XGudron/UA3REO-DDC-Transceiver/Schematic/Wolf-DK102/Photos/20241206171314.jpg

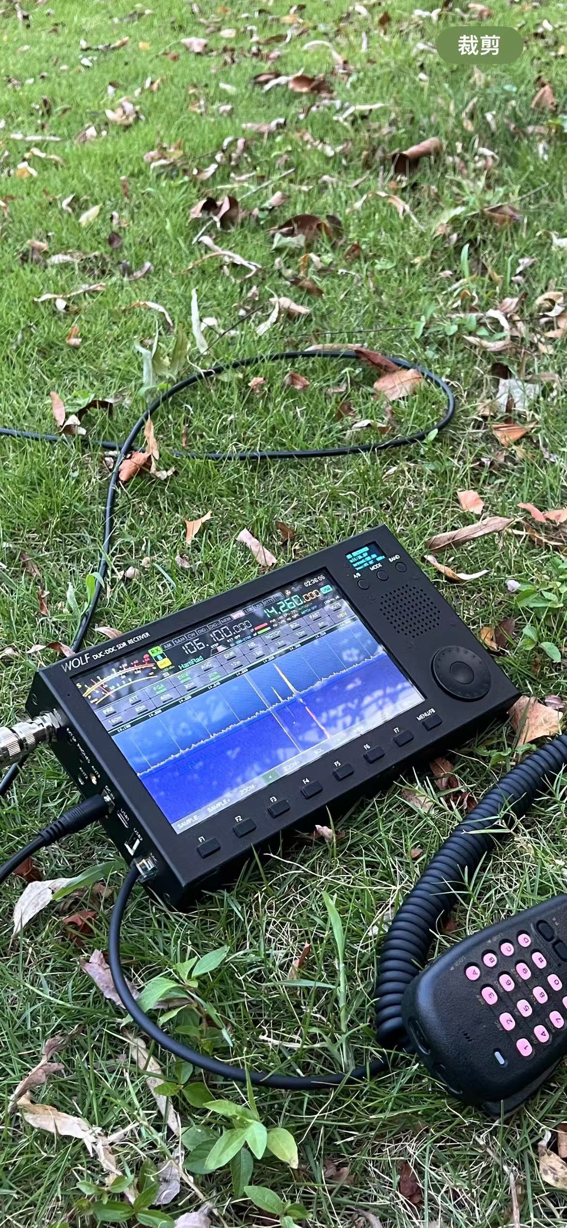
Schematic/Wolf-DK102/Photos/20241206171314.jpg
