XGudron/UA3REO-DDC-Transceiver/Schematic/Wolf/Addons/LPF_switch.jpg

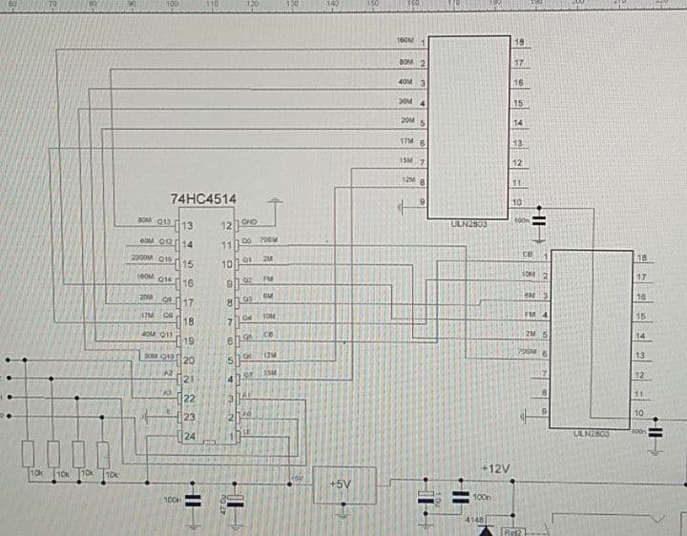
Schematic/Wolf/Addons/LPF_switch.jpg
