XGudron/UA3REO-DDC-Transceiver/Schematic/Wolf/Addons/PCB MIC MH-48/pcb1.jpg

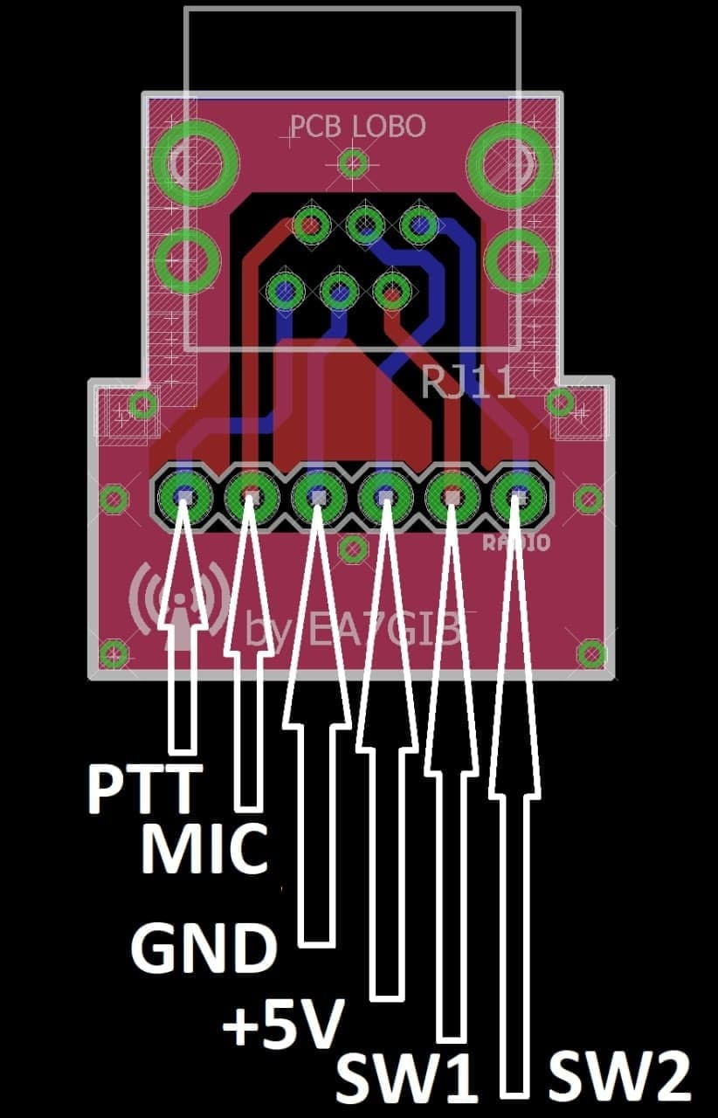
Schematic/Wolf/Addons/PCB MIC MH-48/pcb1.jpg
