XGudron/UA3REO-DDC-Transceiver/Schematic/Wolf/Addons/PCB MIC MH-48/pcb3.jpg

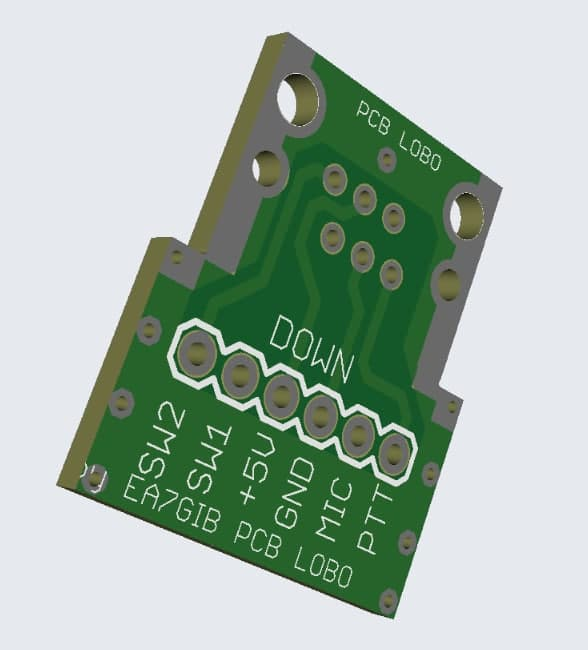
Schematic/Wolf/Addons/PCB MIC MH-48/pcb3.jpg
