XGudron/UA3REO-DDC-Transceiver/Schematic/Wolf/CASE/7/Panel/photo_2023-04-01_12-15-42.jpg

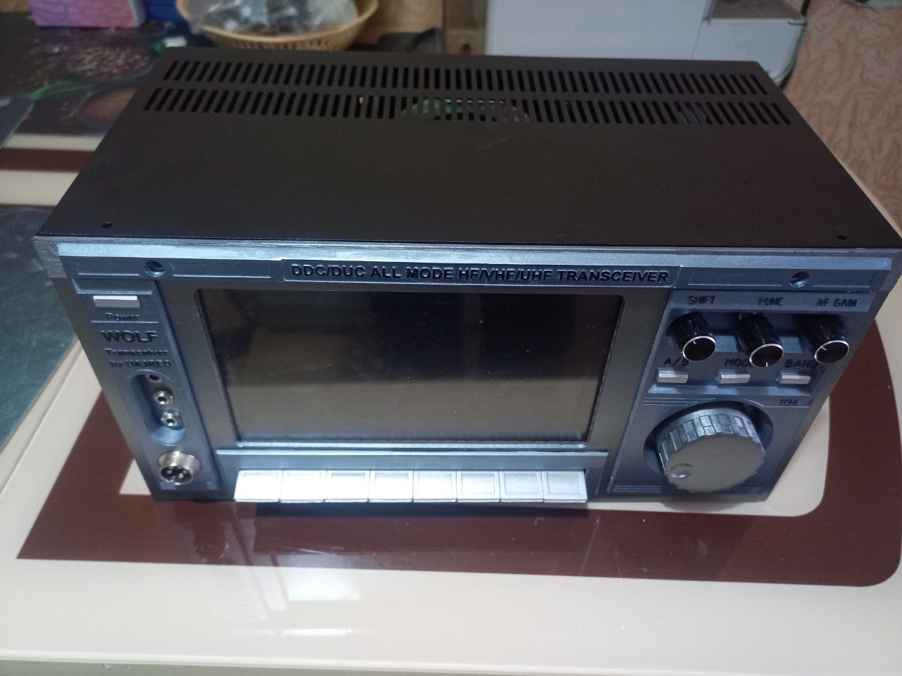
Schematic/Wolf/CASE/7/Panel/photo_2023-04-01_12-15-42.jpg
