XGudron/UA3REO-DDC-Transceiver/Schematic/Wolf/CASE/7/Panel/photo_2023-04-01_13-19-56.jpg

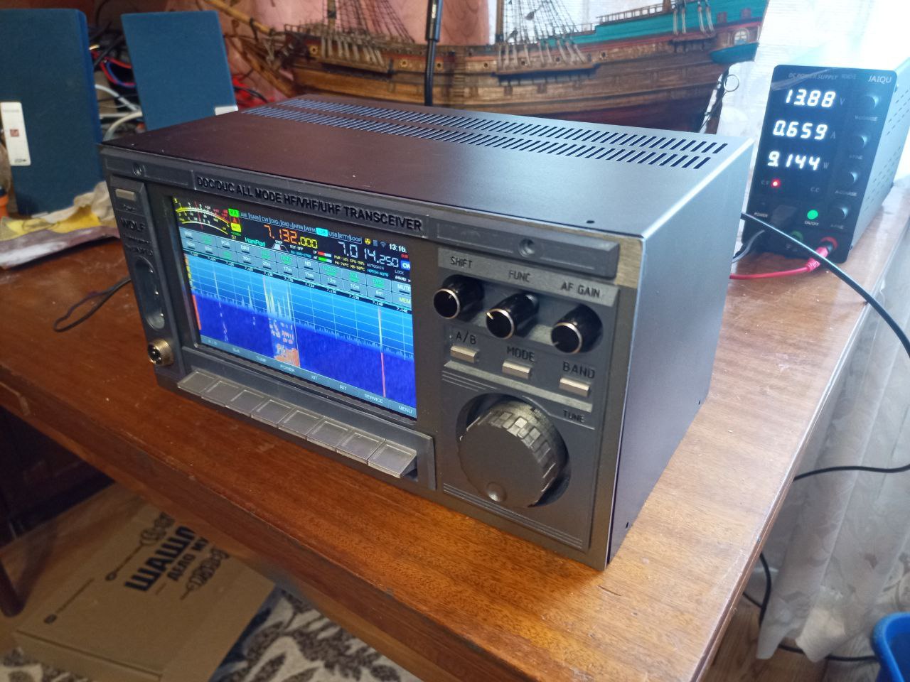
Schematic/Wolf/CASE/7/Panel/photo_2023-04-01_13-19-56.jpg
