XGudron/UA3REO-DDC-Transceiver/Schematic/Wolf/BOM/BOM-MOTHERBOARD-rev33.xls

Comment | Description | Designator | Footprint | LibRef | Quantity | LCSC Part #
JX2 | JX2 | 13.8V + | JX2 | JX2 | 1
51022-0300_1 | 51022-0300 | A_OUT, MIC_IN2 | 51022-0200 - duplicate | 51022-0300_1 | 2
CR1220 + | BR1632A/FA | B1 | KLS5-CR1220-01 | BR1632A/FA | 1
 | 2 Pin | BOOT | 51022-0200 | 51022-0200 | 1
4.7uF 16V | CAPAE_6.6x6.6h5.4 | C1 | SMC | CAPAE_6.6x6.6h5.4 | 1
22uF 10V | CAPAE_4.3x4.3h5.4 | C2, C125, C126 | CAPAE_4.3x4.3h5.4 | CAPAE_4.3x4.3h5.4 | 3
100n | CAP_0805 | C3, C4, C5, C6, C9, C16, C19, C21, C23, C31, C44, C45, C46, C47, C48, C49, C51, C53, C56, C57, C58, C59, C61, C62, C65, C67, C69, C70, C71, C72, C73, C74, C76, C78, C79, C81, C82, C83, C84, C86, C87, C88, C89, C91, C93, C94, C95, C96, C97, C98, C99, C100, C107, C109, C110, C112, C113, C114, C115, C117, C118, C120, C123, C124, C135 | CAP_0805 | CAP_0805 | 65
1uF | CAP_0805 | C7, C11, C12, C13, C14, C15, C35, C92, C119, C121, C122, C1003, C1004 | CAP_0805 | CAP_0805 | 13
10uF 10V | CAPAE_4.3x4.3h5.4 | C8, C20, C22, C24, C32, C54, C60, C75, C77, C80, C85, C1002 | CAPAE_4.3x4.3h5.4 | CAPAE_4.3x4.3h5.4 | 12
470p | CAP_0805 | C10, C90, C104, C116 | CAP_0805 | CAP_0805 | 4
10uF 10V | CAP_0805 | C17 | CAP_0805 | CAP_0805 | 1
1uF 10V | CAPAE_4.3x4.3h5.4 | C25, C26, C29 | CAPAE_4.3x4.3h5.4 | CAPAE_4.3x4.3h5.4 | 3
220p | CAP_0805 | C27, C28, C30 | CAP_0805 | CAP_0805 | 3
220uF 10V | CAPAE_4.3x4.3h5.4 | C33, C34 | EEEFC_size� | CAPAE_4.3x4.3h5.4 | 2
100pF | CAP_0805 | C36 | CAP_0805 | CAP_0805 | 1
10n | CAP_0805 | C37, C63, C137 | CAP_0805 | CAP_0805 | 3
6pF | CAP_0805 | C38, C39 | CAP_0805 | CAP_0805 | 2
10uF | CAP_0805 | C40, C41, C50, C52, C64, C66, C68 | CAP_0805 | CAP_0805 | 7
22p | CAP_0805 | C42, C43 | CAP_0805 | CAP_0805 | 2
7.5p | CAP_0805 | C55 | CAP_0805 | CAP_0805 | 1
10uF 20V | CAPAE_4.3x4.3h5.4 | C101, C108 | CAPAE_4.3x4.3h5.4 | CAPAE_4.3x4.3h5.4 | 2
1uF | CAP_1206 | C102, C103 | CAP_1206 | CAP_1206 | 2
680p | CAP_1206 | C105, C106 | CAP_1206 | CAP_1206 | 2
10p | CAP_0805 | C127 | CAP_0805 | CAP_0805 | 1
8.2n | CAP_0805 | C136 | CAP_0805 | CAP_0805 | 1
1n | CAP_0805 | C1001 | CAP_0805 | CAP_0805 | 1
SMAJ5.0A-TR | Diode | D1, D3, D29, D30, D31, D34, D35, D36, D37, D38, D39, D40 | SMBJ36CATR | SMLVT3V3 | 12 | [NoParam], test
SS34 | Schottky Diode | D1001 | SMB | D Schottky | 1
Diode | Default Diode | D1002 | C1206 | Diode | 1
SJ1-3525NG | SJ1-3525NG | J1, J2, J3, J5 | SJ1-3525NG | SJ1-3523N | 4
RF-UNIT | 2*5 Pin | J4 | 90131-0126 | 90131-0126 | 1
FPC-45P-0.5mm | Connector | J6 | FH12S45S05SH60 | FH12S-45S-0.5SH_55_ | 1
FAN | 51022-0200 | J7 | 51022-0200 | 51022-0200 | 1
USB | 2-1734035-3 | J8 | 2-1734035-3 | 2-1734035-3 | 1
DAC_OUT | SMA | J9 | 31-5431 | 31-5431 | 1
ADC | SMA | J10 | 31-5431 | 31-5431 | 1
 | 2*5 Pin | JTAG_FPGA, JTAG_STM32 | IDC10 | IDC10 | 2
3.3uH | IND_1812 | L1, L9 | IND_1812 | IND_1812 | 2
BLM21 | BLM21 | L3, L8 | CAP_0805 | IND_FERRITE_BEAD | 2
22uH | IND_1206 | L7 | IND_7x7 | IND_1206 | 1
10uH | Inductor | L37, L1001 | IND_7x7 | IND_FERRITE_CORE | 2
10uH | IND_1812 | L1002 | IND_1812 | IND_1812 | 1
PTT_IN | 51022-0200 | PTT_IN | 51022-0200 | 51022-0200 | 1
2SC5103TLP | Transistor BJT NPN | Q1 | 2SC5103TLQ | 2SC5103TLP | 1
7.5k | RES_0805 | R1 | RES_0805 | RES_0805 | 1
39k | RES_0805 | R2 | RES_0805 | RES_0805 | 1
0/NONE | By used crystal | R3 | RES_0805 | RES_0805 | 1
NONE / 0 | RES_0805 | R4, R1001, R1002 | RES_0805 | RES_0805 | 3
5.6k | RES_0805 | R5, R6, R7, R9, R51 | RES_0805 | RES_0805 | 5
30k | RES_0805 | R8, R55 | RES_0805 | RES_0805 | 2
10k | RES_0805 | R10, R13, R24, R27, R28, R30, R31, R32, R33, R36, R37, R38, R39, R46, R47, R48, R56, R57 | RES_0805 | RES_0805 | 18
680 | RES_0805 | R11 | RES_0805 | RES_0805 | 1
47k | RES_0805 | R12, R14, R15, R45 | RES_0805 | RES_0805 | 4
1.5k | RES_0805 | R16, R66 | RES_0805 | RES_0805 | 2
1k | RES_0805 | R17, R18, R19, R25, R26, R49, R50, R52 | RES_0805 | RES_0805 | 8
130 | RES_0805 | R20, R21 | RES_0805 | RES_0805 | 2
82 | RES_0805 | R22, R23 | RES_0805 | RES_0805 | 2
1m | RES_0805 | R29 | RES_0805 | RES_0805 | 1
100 | RES_0805 | R34, R35 | RES_0805 | RES_0805 | 2
22 | RES_0805 | R40, R53, R54, R58 | RES_0805 | RES_0805 | 4
24 | RES_0805 | R41, R42, R43, R64, R65 | RES_0805 | RES_0805 | 5
200 | RES_0805 | R44 | RES_0805 | RES_0805 | 1
 | RES_0805 | R59, R60 | RES_0805 | RES_0805 | 2
330 | RES_0805 | R61 | RES_0805 | RES_0805 | 1
5.6 | RES_1206 | R62, R63 | RES_1206 | RES_1206 | 2
56 | RES_0805 | R67 | RES_0805 | RES_0805 | 1
10 | RES_0603 | R68, R69 | RES_0603 | RES_0603 | 2
Thermistor 20k | Thermistor | R70 | MF52A103F3950A1 | MF52A103F3950_A1_ | 1
ADJ-5k | 306J | R71 | 306J | 306J | 1
0 | RES_0805 | R1003 | RES_0805 | RES_0805 | 1
1:1+1 | Transformer | T3 | TRANSF_ACORE2 | TRANSF_ACORE2 | 1
1:4 ADT4-6T | Transformer | T4 | TRANSF_ACORE2 | TRANSF_ACORE2 | 1
1:1 | Transformer | T6 | TRANSF_ACORE | TRANSF_ACORE | 1
PAM8406 | PAM8406 | U1 | PAM8403 | PAM8406 | 1
LD3985 | LD3985 | U2 | LD3985 | LD3985 | 1
ST1S10 | ST1S10 | U3 | ST1S10 | ST1S10 | 1
WM8731 | WM8731 | U4 | WM8731 | WM8731 | 1
STM32H743VIT6-rev.V | STM32H743VIT6 | U5 | STM32H743VIT6 | STM32H743VIT6 | 1
LM1084IS-3.3 | LM1084IS-3.3 | U6 | LM1085-3.3 | LM1085-3.3 | 1
W25Q16 | W25Q16 | U7 | W25Q16 | W25Q16 | 1
DAC5674 | Integrated Circuit | U8 | QFP50P900X900X100-49N | DAC5674IPHP | 1
25P80 | 25P80 | U9 | 25P80 | 25P80 | 1
EP4CE22E22C8N | EP4CE22E22C8N | U10 | QFP144-20-2222A | EP4CE22E22C8N | 1
1117DT-2.5 | LD1117DT-2.5 DPAK | U11 | TO228P991X238-3N | LM1117DT-ADJ | 1
1117DT-1.2 | LD1117DT-1.2 DPAK | U12 | TO228P991X238-3N | LM1117DT-ADJ | 1
1117-3.3 | LT1117CST-3.3 | U13 | LT1117CST-3.3 | LT1117CST-3.3 | 1
1117-1.8 | LT1117CST-1.8 | U14 | LT1117CST-3.3 | LT1117CST-3.3 | 1
SPEAKER | 4 pins conn | U15 | speaker conn | speaker conn | 1
LTC2208CUP | LTC2208CUP | U16 | LTC2208CUP | LTC2208CUP | 1
LTC6400IUD | Single Channel, Low Noise, Low Distortion Differential ADC Driver for 300 MHz IF, 1800 MHz Typical GBW, 4500 V/us Typical SR, 2.85 to 3.5 V, 16-Pin QFN (UD-16), Industrial, Pb-Free | U17 | LT-UD-16_N | CMP-0359-03855-2 | 1
1117DT-3.3 | LD1117DT33 DPAK | U18 | TO228P991X238-3N | LM1117DT-ADJ | 1
ADUM4160 | Integrated Circuit | U19 | SOIC127P1032X265-16N | ADUM4160BRWZ | 1
OPA2673 | Integrated Circuit | U20 | QFN65P400X400X100-17N-D | OPA2673IRGVT | 1
LM2940S-12/NOPB | 1-A, 26-V, high-PSRR, low-dropout voltage regulator | U21 | TO254P1524X483-4N | LM2940S-12/NOPB | 1
122.88Mhz | NV7050SA VG-4513CA-122.8800M-GGCT3 | XG1 | NV7050SA | NV7050SA | 1
12.288Mhz TCXO 3.3v TTL/CMOS (set other freq in fpga code) | Crystal or Oscillator | XG2 | 581L200X2ITT | 581L200X2ITT | 1
ABS25-32.768KHZ-6-T | Crystal or Oscillator | Y1 | ABS25 | ABS25-32.768KHZ-6-T | 1
8mhz | ECS-200-20-1 | Y2 | ECS-200-20-1 | ECS-200-20-1 | 1
