XGudron/UA3REO-DDC-Transceiver/Schematic/Wolf/BOM/BOM-RF-UNIT-BIG-RU4PN-rev5.5.xls

ID | Name | Designator | Footprint | Quantity | Manufacturer Part | Manufacturer | Supplier | Supplier Part | Price
1 | 100n | C1,C7,C8,C9,C10,C11,C16,C21,C26,C31,C36,C38,C42,C47,C48,C49,C50,C59,C64,C67,C71,C76,C78,C80,C82,C89,C90,C113,C114,C116,C117,C118,C130,C131,C136,C137,C138,C139,C167,C170,C171,C241,C301,C302,C303,C304 | C0805 | 46
2 | 470pF | C2 | C1206 | 1
3 | 30pF | C3 | C1206 | 1
4 | 36pF | C4 | C1206 | 1
5 | 47pF | C5,C86 | C1206 | 2
6 | 22pF | C6,C85 | C1206 | 2
7 | 27pF | C12,C15 | C1210 | 2
8 | 20pF | C13 | C1210 | 1
9 | 100pF | C14,C17,C19,C20 | C1210 | 4
10 | 120pF | C18 | C1210 | 1
11 | 150pF | C22,C23,C25,C28 | C1210 | 4
12 | 220pF | C24,C27,C30 | C1210 | 3
13 | 330pF | C29 | C1210 | 1
14 | 470pF | C32,C33,C34,C35 | C1210 | 4
15 | 470+330pF | C37,C41 | C1210 | 2
16 | 1000pF | C39,C45 | C1210 | 2
17 | 560pF | C40 | C1210 | 1
18 | 1000+220pF | C43,C46 | C1210 | 2
19 | 1000+470pF | C44 | C1210 | 1
20 | 3n3 | C51,C125,C134,C135 | C0805 | 4
21 | 68pF 500V | C52,C56 | C1206 | 2
22 | 4.7n* | C53,C54 | C1206 | 2
23 | 27pF | C55 | C0805 | 1
24 | 470p 500V | C57 | C1206 | 1
25 | 100n | C58,C61,C106 | C1206 | 3
26 | 200p 500V | C60 | C1206 | 1
27 | 1uF | C62,C63,C79,C83,C126 | C0805 | 5
28 | 30pF* | C65,C66 | CAP-ADJ-SMD_L4.5-W3.2-L | 2 | TZC3P300A110R00 | Murata Electronics | LCSC | C107707
29 | 82pF | C68,C73,C388,C390 | C0805 | 4
30 | 10n | C69,C107,C108,C109,C110,C121,C123,C124,C133,C141,C142,C143,C144,C145,C146,C147,C148,C149,C150,C151,C152,C153,C154,C157,C158,C159,C160,C161,C162,C163,C164,C165,C166 | C0805 | 33
31 | 4.7n | C70,C75 | C0805 | 2
32 | 75pF | C72,C311,C389 | C0805 | 3
33 | 22uF | C74,C77 | CASE-B_3528 | 2
34 | 15n | C81,C111 | C1206 | 2
35 | 10pF | C84 | C1206 | 1
36 | 100pF | C87,C91,C93,C103 | C1206 | 4
37 | 220pF | C88 | C1206 | 1
38 | 10n | C92,C102 | C1206 | 2
39 | 1n | C94,C104 | C1206 | 2
40 | 2.2uF | C95 | C1206 | 1
41 | * | C96,C97,C98,C99,C100 | CAP-TH_L8.0-W4.0-P7.50-D0.6 | 5 | CC45SL3AD101JYSNA | TDK | LCSC | C2835349 | 0.006
42 | 200pF | C101 | C1206 | 1
43 | 1n8 | C105 | C1206 | 1
44 | 100p | C112,C127,C132 | C0805 | 3
45 | 1n | C115,C122,C347,C348,C372 | C0805 | 5
46 | 47uF | C119 | CASE-B_3528 | 1
47 | 68p | C120,C202,C208 | C0805 | 3
48 | 1uF | C128 | C1206 | 1
49 | 10uF 25V | C129 | CAP-D4.0×H5.5 | 1
50 | 39p | C201 | C0805 | 1
51 | 12p | C203 | C0805 | 1
52 | 27p | C204 | C0805 | 1
53 | 51p | C207 | C0805 | 1
54 | 47p | C210 | C0805 | 1
55 | 47pF | C305,C313 | C0805 | 2
56 | 33pF | C306 | C0805 | 1
57 | 39pF | C307 | C0805 | 1
58 | 110pF | C310 | C0805 | 1
59 | 61pF | C312 | C0805 | 1
60 | 100pF | C314,C322 | C0805 | 2
61 | 120pF | C315,C321 | C0805 | 2
62 | 15pF | C317 | C0805 | 1
63 | 8pF | C319 | C0805 | 1
64 | 150pF | C320 | C0805 | 1
65 | 330pF | C323,C344,C346 | C0805 | 3
66 | 270pF | C324,C332,C345 | C0805 | 3
67 | 180pF | C333,C334 | C0805 | 2
68 | 560pF | C335 | C0805 | 1
69 | 470pF | C336,C360 | C0805 | 2
70 | 820pF | C358,C373 | C0805 | 2
71 | 680pF | C359 | C0805 | 1
72 | 1.5n | C361 | C0805 | 1
73 | 1.2n | C362,C374 | C0805 | 2
74 | 3.3n | C375,C376 | C0805 | 2
75 | 30pF * | C386,C387 | CAP-ADJ-SMD_L4.5-W3.2-L | 2 | TZC3P300A110R00 | Murata Electronics | LCSC | C107707
76 | BAT46JFILM | D1,D3,D49,D50 | SOD-323_L1.8-W1.3-LS2.5-RD | 4 | BAT46JFILM | STMicroelectronics | LCSC | C111205
77 | SMAJ5.0A-TR | D2 | SMA_L4.3-W2.6-LS5.2-RD | 1 | SMAJ5.0A-TR | STMicroelectronics | LCSC | C98802 | 0.037
78 | 1N4148W | D4,D5,D8,D9,D13,D15,D17,D20,D22,D25,D27,D31,D32,D38,D39,D40,D41,D42,D43,D44,D45,D46,D47,D48,D51 | SOD-123FL_L2.6-W1.6-LS3.4-RD | 25 | 1N4148W | Tak Cheong | LCSC | C129216 | 0.003
79 | CDSOD323-T05C | D6,D10,D11,D12 | SOD-323_L1.8-W1.3-LS2.5-BI | 4 | CDSOD323-T05C | BOURNS | LCSC | C711706 | 0.048
80 | BAV99 | D7 | SOT-23-3_L2.9-W1.3-P1.90-LS2.4-BR | 1 | BAV99-7-F | DIODES | LCSC | C106919 | 0.005
81 | SS14 | D18,D23 | SS14 | 2 | SS14 | MDD | LCSC | C2480 | 0.002
82 | SS14 | D35,D36,D37 | SMA_L4.4-W2.8-LS5.4-RD | 3 | SS14 | MDD | LCSC | C2480 | 0.002
83 | BLM21 | FB1,FB2 | L0806 | 2
84 | BLM21 | FB4,FB5 | L0805 | 2 | BLM21PG300SN1D | MuRata | LCSC | C16903 | 0.004
85 | FAN_OUT | H1 | HDR-F-2.54_1X2 | 1 |  |  | LCSC | C49661 | 0.006
86 | ANT1 | J1 | SMA-TH_BWSMA-KE-Z001 | 1 | SMA-KE-P901 | DreamLNK | LCSC | C914556 | 0.109
87 | ADC | J2,J10 | SMA-TH_BWSMA-KE-Z001 | 2 | SMA-KE-P901 | DreamLNK | LCSC | C914556 | 0.109
88 | EXTERNAL | J3 | IDC-10 | 1
89 | MOTHERBOARD | J4 | IDC-10 | 1
90 | ANT2 | J5 | SMA-TH_BWSMA-KE-Z001 | 1 | SMA-KE-P901 | DreamLNK | LCSC | C914556 | 0.109
91 | HiCurrent 13.8V | J6 | CONN-TH_TY500-5.08-02P-14-00AH | 1 | TY500-5.08-02P-14-00AH | Toponelec(拓宜) | LCSC | C2828268 | 0.032
92 | HiCurrent13.8V | J7 | CONN-TH_TY500-5.08-02P-14-00AH | 1 | TY500-5.08-02P-14-00AH | Toponelec(拓宜) | LCSC | C2828268 | 0.032
93 | 13.8V | J8 | CONN-TH_TY500-5.08-02P-14-00AH | 1 | TY500-5.08-02P-14-00AH | Toponelec(拓宜) | LCSC | C2828268 | 0.032
94 | DAC | J9 | SMA-TH_BWSMA-KE-Z001 | 1 | SMA-KE-P901 | DreamLNK | LCSC | C914556 | 0.109
95 | G6S-2-12V | K1,K2,K8,K9,K10,K11,K12,K13,K14,K15,K16,K17,K18,K19,K20,K21,K24,K25,K26,K27,K28,K29,K30,K31,K32,K33,K34,K35 | RELAY-TH_G6S-2-X | 28 | G6S-2-12V | OMRON | LCSC | C28410 | 0.145
96 | axicom im06c | K4,U4,U12 | IM06C | 3 | axicom im06c |  | axicom
97 | G6K-2F-5V | K50 | RELAY-TH_G6K-2F-Y | 1 | 0 | Omron Electronics | LCSC | C231389 | 0.201
98 | 0,047uH | L1 | BEAD-TH_BD3.5-L4.7-P8.70-D0.7 | 1 | BL02RN2R1M2 | China |  | C84974
99 | 0.047uH | L2,L3 | BEAD-TH_BD3.5-L4.7-P8.70-D0.7 | 2 | BL02RN2R1M2 | China |  | C84974
100 | 0.065uH | L7,L8 | BEAD-TH_BD3.5-L4.7-P8.70-D0.7 | 2 | BL02RN2R1M2 | China |  | C84974
101 | 0.29uH | L10,L11 | BEAD-TH_BD3.5-L4.7-P8.70-D0.7 | 2 | BL02RN2R1M2 | China |  | C84974
102 | 0.4uH | L13,L14 | BEAD-TH_BD3.5-L4.7-P8.70-D0.7 | 2 | BL02RN2R1M2 | China |  | C84974
103 | 0.6uH | L16,L17 | BEAD-TH_BD3.5-L4.7-P8.70-D0.7 | 2 | BL02RN2R1M2 | China |  | C84974
104 | 1.15uH | L19,L20 | BEAD-TH_BD3.5-L4.7-P8.70-D0.7 | 2 | BL02RN2R1M2 | China |  | C84974
105 | 2.3uH | L22,L23 | BEAD-TH_BD3.5-L4.7-P8.70-D0.7 | 2 | BL02RN2R1M2 | China |  | C84974
106 | 4.5uH | L25,L26 | BEAD-TH_BD3.5-L4.7-P8.70-D0.7 | 2 | BL02RN2R1M2 | China |  | C84974
107 | 10u 10x10 | L30,L43 | B82464Z4 | 2
108 | 0.22u | L31 | L1206 | 1
109 | 0.0082u | L32,L33,L34 | L0805 | 3
110 | 0.1uH | L35 | BEAD-TH_BD3.5-L4.7-P8.70-D0.7 | 1 | BL02RN2R1M2 | China |  | C84974
111 | 0.22uH | L36 | BEAD-TH_BD3.5-L4.7-P8.70-D0.7 | 1 | BL02RN2R1M2 | China |  | C84974
112 | 0.45uH | L39 | BEAD-TH_BD3.5-L4.7-P8.70-D0.7 | 1 | BL02RN2R1M2 | China |  | C84974
113 | 1.0uH | L41 | BEAD-TH_BD3.5-L4.7-P8.70-D0.7 | 1 | BL02RN2R1M2 | China |  | C84974
114 | 2.2uH | L42 | BEAD-TH_BD3.5-L4.7-P8.70-D0.7 | 1 | BL02RN2R1M2 | China |  | C84974
115 | 0.22u | L46 | L0805 | 1
116 | 0.022u | L48 | L0805 | 1
117 | 0.0082u | L134,L135,L136 | L0805-WOLF | 3 | L0805C100MDWIT | KEMET | LCSC | C696787 | 0.037
118 | 0.1u | L140 | L0805-WOLF | 1
119 | 0.082u | L141 | L0805-WOLF | 1
120 | 0.15u | L142 | L0805-WOLF | 1
121 | 0.022u | L151 | L0805-WOLF | 1 | L0805C100MDWIT | KEMET | LCSC | C696787 | 0.037
122 | 0.18u | L153 | L0805-WOLF | 1 | L0805C100MDWIT | KEMET | LCSC | C696787 | 0.037
123 | 0.33u | L155,L308,L310,L311 | L0805-WOLF | 4 | L0805C100MDWIT | KEMET | LCSC | C696787 | 0.037
124 | 0.27u | L301,L307 | L0805-WOLF | 2 | L0805C100MDWIT | KEMET | LCSC | C696787 | 0.037
125 | 0.082u | L302 | L0805-WOLF | 1 | L0805C100MDWIT | KEMET | LCSC | C696787 | 0.037
126 | 0.1u | L303 | L0805-WOLF | 1 | L0805C100MDWIT | KEMET | LCSC | C696787 | 0.037
127 | 0.47u | L304,L315 | L0805-WOLF | 2 | L0805C100MDWIT | KEMET | LCSC | C696787 | 0.037
128 | 0.15u | L305,L306 | L0805-WOLF | 2 | L0805C100MDWIT | KEMET | LCSC | C696787 | 0.037
129 | 1u | L309,L317 | L0805-WOLF | 2 | L0805C100MDWIT | KEMET | LCSC | C696787 | 0.037
130 | 0.56u | L312,L316 | L0805-WOLF | 2 | L0805C100MDWIT | KEMET | LCSC | C696787 | 0.037
131 | 0.82u | L313,L321 | L0805-WOLF | 2 | L0805C100MDWIT | KEMET | LCSC | C696787 | 0.037
132 | 1.5u | L314,L318,L325 | L0805-WOLF | 3 | L0805C100MDWIT | KEMET | LCSC | C696787 | 0.037
133 | 1.8u | L319,L326 | L0805-WOLF | 2 | L0805C100MDWIT | KEMET | LCSC | C696787 | 0.037
134 | 0.68u | L320 | L0805-WOLF | 1 | L0805C100MDWIT | KEMET | LCSC | C696787 | 0.037
135 | 2.2u | L322,L330,L331 | L0805-WOLF | 3 | L0805C100MDWIT | KEMET | LCSC | C696787 | 0.037
136 | 2.7u | L323,L327 | L0805-WOLF | 2 | L0805C100MDWIT | KEMET | LCSC | C696787 | 0.037
137 | 4.7u | L324 | L0805-WOLF | 1 | L0805C100MDWIT | KEMET | LCSC | C696787 | 0.037
138 | 3.3u | L328 | L0805-WOLF | 1 | L0805C100MDWIT | KEMET | LCSC | C696787 | 0.037
139 | 5.6u | L329 | L0805-WOLF | 1 | L0805C100MDWIT | KEMET | LCSC | C696787 | 0.037
140 | 6.8u | L332 | L0805-WOLF | 1 | L0805C100MDWIT | KEMET | LCSC | C696787 | 0.037
141 | 8.2u | L333 | L0805-WOLF | 1 | L0805C100MDWIT | KEMET | LCSC | C696787 | 0.037
142 | RD16HHF1 | Q1,Q3 | TO220V | 2
143 | IRLML9301 | Q2,Q7,Q10 | SOT-23-3_L2.9-W1.3-P1.90-LS2.4-BR | 3 | IRLML9301TR | VBsemi Elec | LCSC | C710004 | 0.018
144 | PGA103+/SPF5189Z | Q4 | SOT-89-3_L4.5-W2.5-P1.50-LS4.2-TL | 1
145 | RD100HHF1 | Q5,Q6 | RD100HHF WOLF | 2
146 | RA80H1415M1 | Q8 | RA80H1415M1 | 1 | RA80H1415M1
147 | RD01MUS1 | Q9 | RD01MUS1 | 1
148 | IRLML9301 | Q11 | SOT-23_L2.9-W1.3-P1.90-LS2.4-BR | 1 | IRLML9301TRPBF | IR | LCSC | C82056 | 0.051
149 | BSS123 | Q12 | SOT-23-3_L2.9-W1.6-P1.90-LS2.8-BR | 1 | BSS123 | CJ | LCSC | C79015 | 0.005
150 | A022-145M2 | QF1 | A022-145M2 | 1
151 | 47 | R1,R2,R17,R18 | R1206_1 | 4 | 0 | Chian Chia Elec | LCSC | C122207 | 0.012
152 | 560 | R3,R7,R8,R9,R10,R11,R12,R62,R63 | R0805 | 9
153 | 30k | R4,R41,R45,R48,R75 | R0805 | 5
154 | 1k | R5,R6,R31,R33,R35,R42,R43,R57,R69,R70,R71,R72,R79,R80,R81,R201,R202,R203,R204,R205,R206,R207 | R0805 | 22
155 | 2k | R13 | R0805 | 1
156 | KTY81/120 | R14 | RES-TH_KTY81 | 1 | KTY81/110,112 | NXP(恩智浦) | LCSC | C1527155 | 0.201
157 | 56 | R15,R16,R26 | R0805 | 3
158 | 0 | R17*,R49,R50,R65,R67 | R1206 | 5
159 | * | R18* | R1206 | 1
160 | 10K | R19,R20 | RES-ADJ-TH_3296W | 2 | 3296W-1-102LF | BOURNS | LCSC | C57089 | 0.12
161 | 750 | R21 | R0805 | 1
162 | 470 | R22 | R0805 | 1
163 | 20 | R23 | R0805 | 1
164 | 300 | R24,R25 | R0805 | 2
165 | 47 | R27,R44 | R0805 | 2
166 | 100 | R28,R29,R51 | R0805 | 3
167 | 1K | R30,R40,R46 | RES-ADJ-TH_3296W | 3 | 3296W-1-102LF | BOURNS | LCSC | C57089 | 0.12
168 | 6.8k | R32 | R0805 | 1
169 | 100 | R34 | R1206 | 1
170 | 510 | R36,R54 | R1206 | 2
171 | 2.7k | R37 | R0805 | 1
172 | 4.7 | R38,R47,R74,R76 | R1206 | 4
173 | 18 | R39 | R1206 | 1
174 | 200 | R52 | R0805 | 1
175 | 1.2k | R53 | R0805 | 1
176 | 50 | R55,R56 | R1206 | 2
177 | 620 | R58 | R0805 | 1
178 | 430 | R59,R60 | R1206 | 2
179 | 10 | R61 | R0805 | 1
180 | 1K | R64,R68 | R1206 | 2
181 | 100 | R66 | RES-ADJ-TH_3362P | 1 | 3362P-1-105 | ReliaPro | LCSC | C20063
182 | 10k | R73 | R1206 | 1
183 | 2.2k | R77,R78 | R0805 | 2
184 | BN61-002 | T1 | BN61-002 WOLF | 1 | BN61-002
185 | BN43-202 | T2 | BN43-202 WOLF SHORT | 1
186 | BN43-202 | T3 | BN43-202_RD16 WOLF | 1
187 | 1:1 | T5 | ATD1+TC1 | 1 | TC1-1T+ | Mini-Circuits | LCSC | C879831 | 0.44
188 | VHF Tandem Meter | T6 | VHF SWR METER | 1 | VHF Tandem Meter
189 | BN-61-202 | TSWR | BN43-202_TANDEM | 1 | 2843010302 | Fair-Rite |  | 2843010302
190 | STPIC6C595TTR | U1,U2,U3,U7,U11,U21 | TSSOP-16_L5.0-W4.4-P0.65-LS6.4-BL | 6 | STPIC6C595TTR | STMicroelectronics | LCSC | C222081 | 0.391
191 | LT1117-ADJ | U5,U20 | SOT-223-3_L6.5-W3.4-P2.30-LS7.0-BR | 2 | LT1117IST#PBF | Analog Devices | LCSC | C661269 | 0.689
192 | LM1117DT-5.0 | U6 | TD03B | 1
193 | PE4302 | U9 | QFN-20L_L4.0-W4.0-P0.50-BL-EP2.0 | 1 | PE4302-EK | null | LCSC | C2763949
194 | ADG918BRMZ | U13,U14 | MSOP-8_L3.0-W3.0-P0.65-LS4.9-BL | 2 | ADG918BRMZ-500RL7 | Analog Devices | LCSC | C207406 | 0.452
195 | LT1117IST-5.0 | U19 | SOT-223-3_L6.5-W3.4-P2.30-LS7.0-BR | 1 | LT1117IST-5#TRPBF | Analog Devices | LCSC | C661276 | 1.412
196 | ADG904BRUZ | U24,U25,U26,U27 | TSSOP-20 | 4
