XGudron/UA3REO-DDC-Transceiver/Schematic/Wolf/CASE/3'2/3DPrinter/STL/case_shell.STL

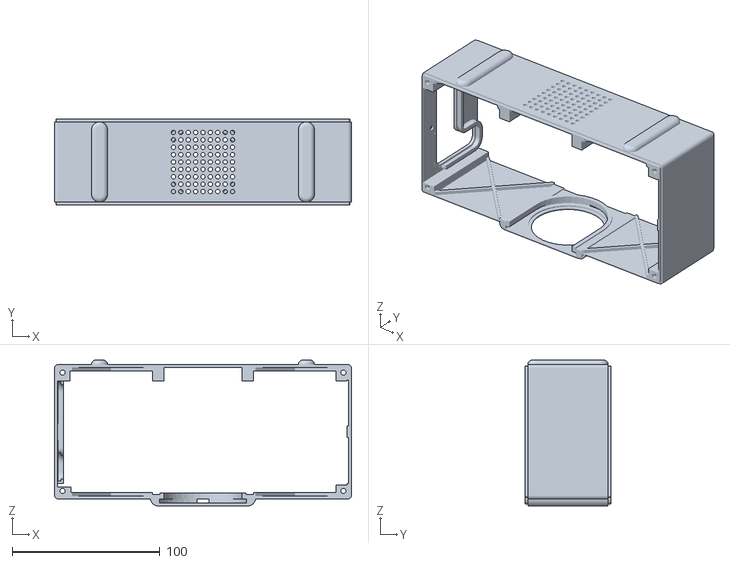
[picture p36: CAD file, 2024-02-05]
Schematic/Wolf/CASE/3'2/3DPrinter/STL/case_shell.STL
201.0 x 58.4 x 98.7
