XGudron/UA3REO-DDC-Transceiver/Schematic/Wolf/CASE/VFO/VFO38WithExt.stl

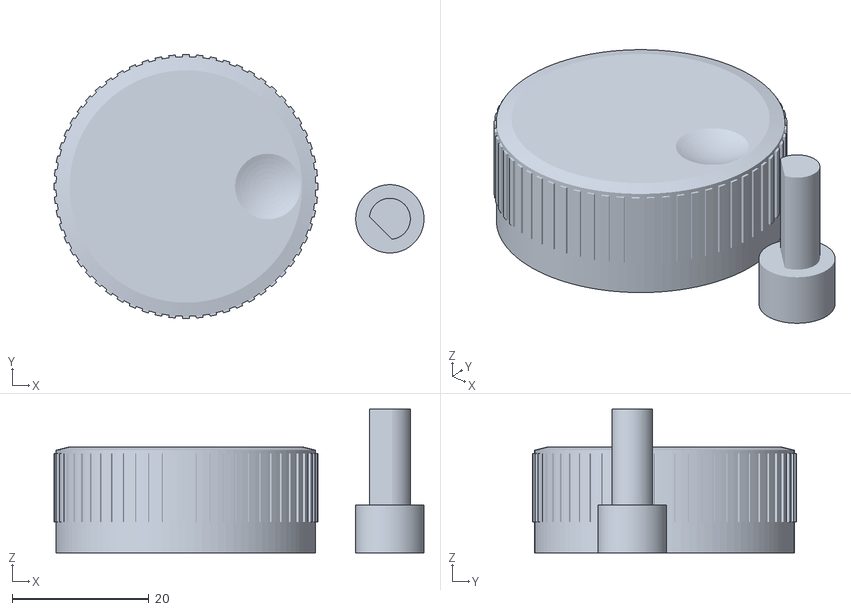
[picture p38: CAD file, 2024-02-05]
Schematic/Wolf/CASE/VFO/VFO38WithExt.stl
54.1 x 38.6 x 21.0
