XGudron/UA3REO-DDC-Transceiver/Schematic/Wolf/CASE/7/Panel/верхняя планка волк7_1.stl

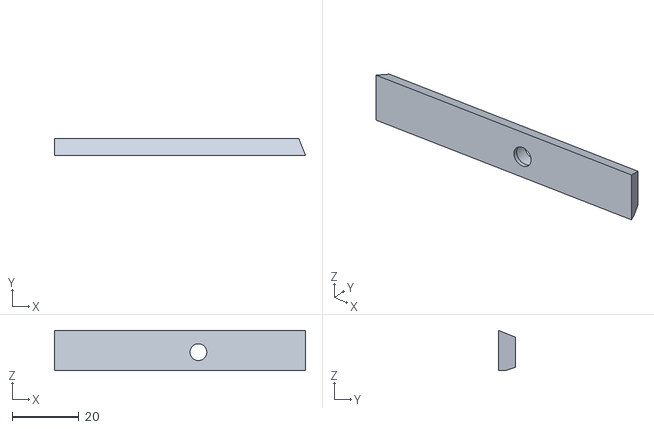
[picture p41: CAD file, 2024-02-05]
Schematic/Wolf/CASE/7/Panel/верхняя планка волк7_1.stl
75.0 x 5.00 x 12.0
