XGudron/UA3REO-DDC-Transceiver/Schematic/Wolf/CASE/3'2/3DPrinter/Rotary Encoder.SLDPRT

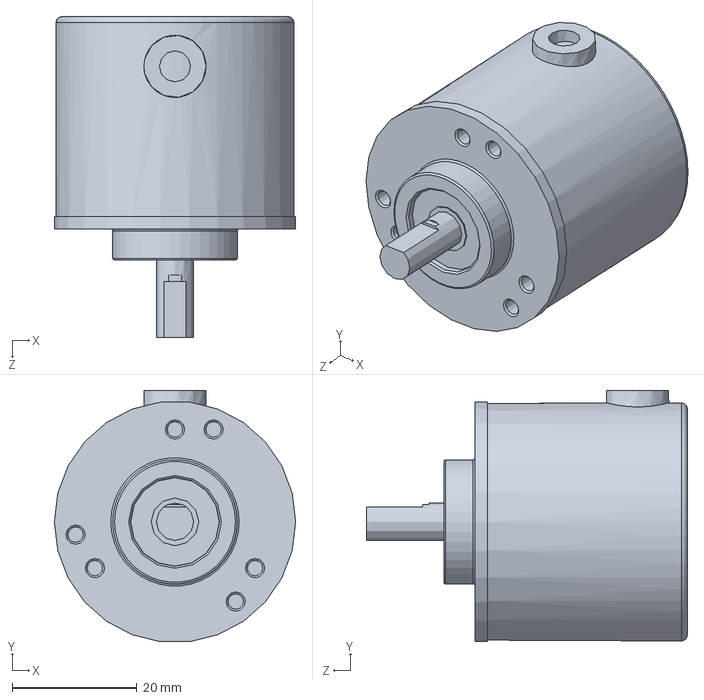
[picture p44: CAD file, 2024-02-05]
Schematic/Wolf/CASE/3'2/3DPrinter/Rotary Encoder.SLDPRT
38.7 x 40.3 x 51.5 mm
