XGudron/UA3REO-DDC-Transceiver/Schematic/Wolf/CASE/7/Panel/рамка_низ_7_л.stl

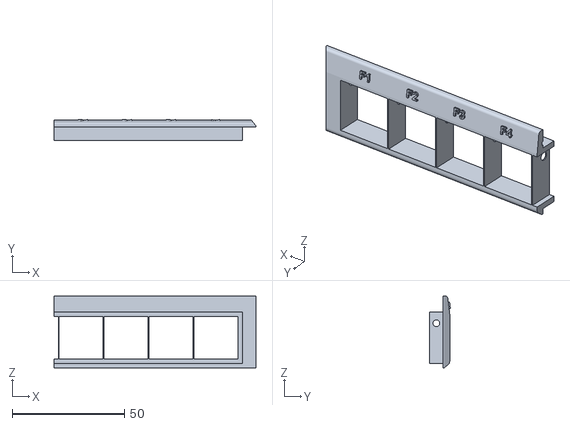
[picture p48: CAD file, 2024-02-05]
Schematic/Wolf/CASE/7/Panel/рамка_низ_7_л.stl
90.0 x 9.31 x 32.0
