XGudron/UA3REO-DDC-Transceiver/Schematic/Wolf/CASE/7/Panel/левая_панель_волк7.stl

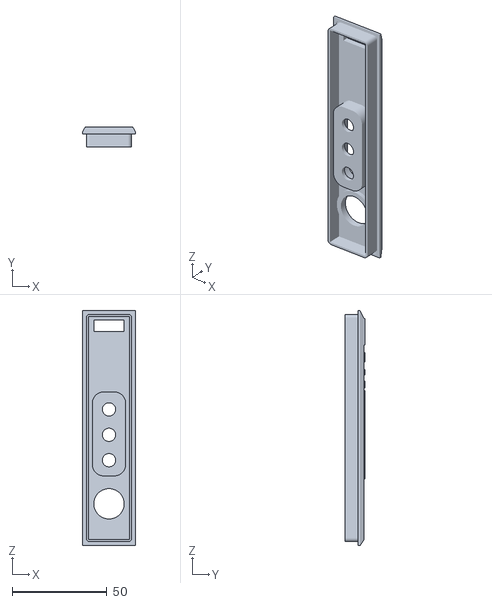
[picture p53: CAD file, 2024-02-05]
Schematic/Wolf/CASE/7/Panel/левая_панель_волк7.stl
28.0 x 10.6 x 124.0
