XGudron/UA3REO-DDC-Transceiver/Schematic/Wolf/CASE/3'2/3DPrinter/speaker.SLDPRT

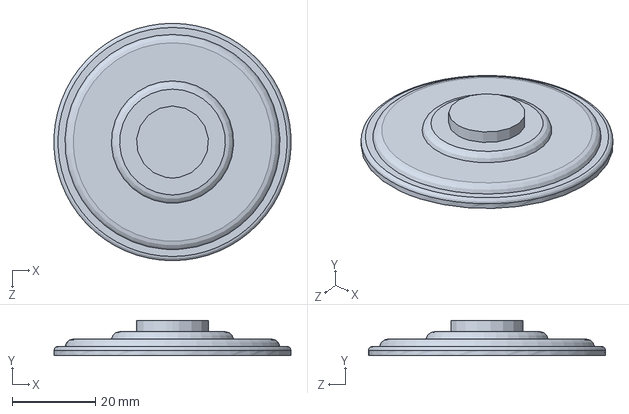
[picture p55: CAD file, 2024-02-05]
Schematic/Wolf/CASE/3'2/3DPrinter/speaker.SLDPRT
56.9 x 8.51 x 57.0 mm
