XGudron/UA3REO-DDC-Transceiver/Schematic/Wolf/CASE/3'2/3DPrinter/case/button.SLDPRT

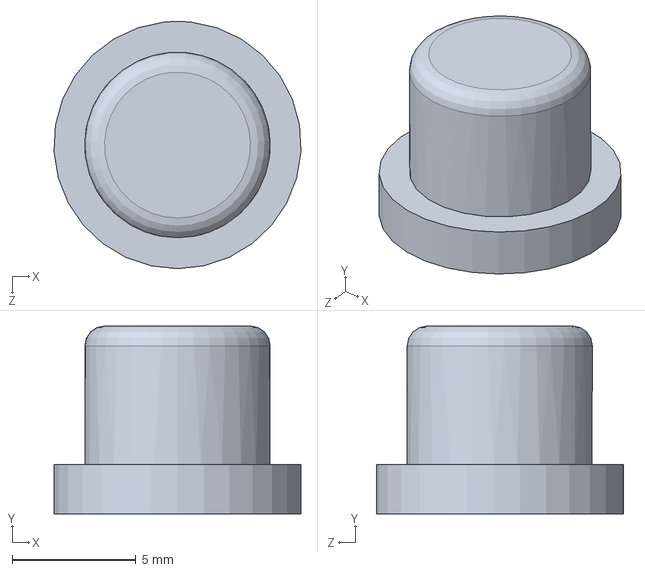
[picture p59: CAD file, 2024-02-05]
Schematic/Wolf/CASE/3'2/3DPrinter/case/button.SLDPRT
9.99 x 7.60 x 10.0 mm
