XGudron/UA3REO-DDC-Transceiver/Schematic/Wolf/CASE/3'2/3DPrinter/tactileswitch-long.SLDPRT

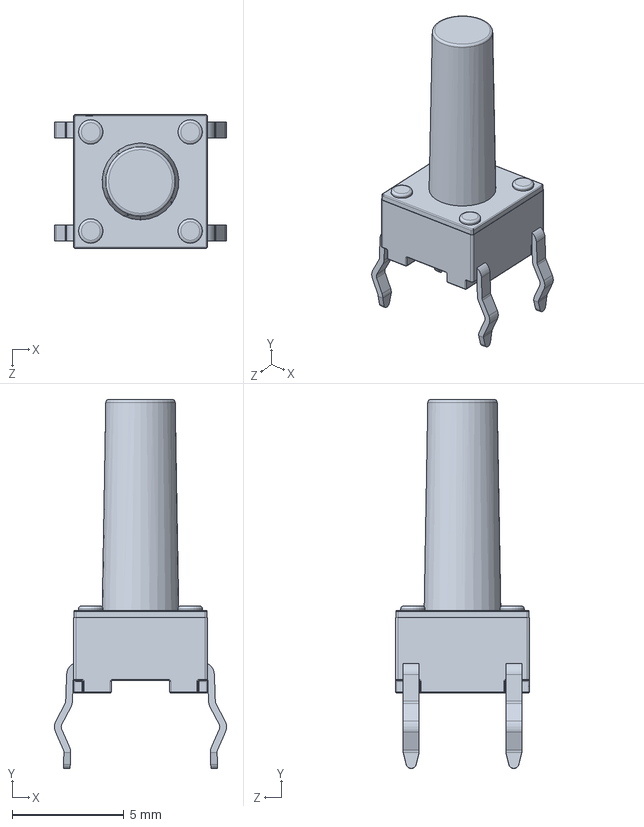
[picture p62: CAD file, 2024-02-05]
Schematic/Wolf/CASE/3'2/3DPrinter/tactileswitch-long.SLDPRT
7.69 x 16.5 x 6.01 mm
