XGudron/UA3REO-DDC-Transceiver/Schematic/Wolf/CASE/3'2/3DPrinter/MB.SLDPRT

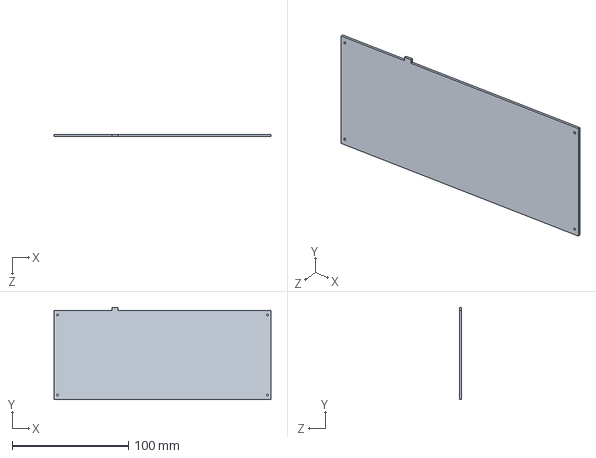
[picture p67: CAD file, 2024-02-05]
Schematic/Wolf/CASE/3'2/3DPrinter/MB.SLDPRT
187.0 x 79.5 x 1.60 mm
