XGudron/UA3REO-DDC-Transceiver/Schematic/Wolf/CASE/3'2/3DPrinter/beam_short.SLDPRT

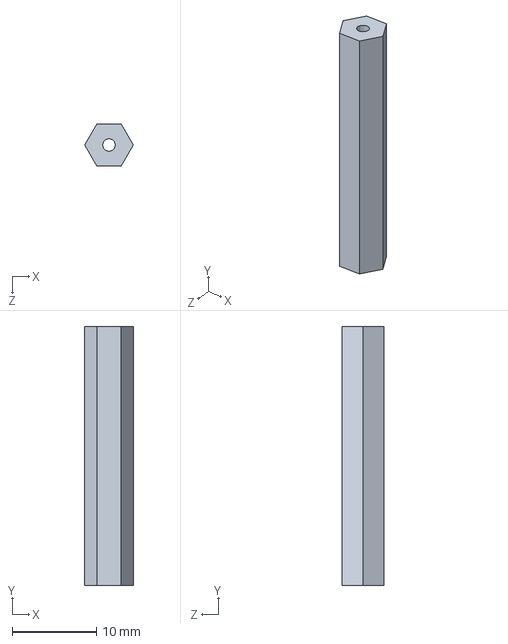
[picture p71: CAD file, 2024-02-05]
Schematic/Wolf/CASE/3'2/3DPrinter/beam_short.SLDPRT
5.77 x 30.7 x 5.00 mm
