XGudron/UA3REO-DDC-Transceiver/Schematic/Wolf/CASE/3'2/3DPrinter/GX16-8.stp

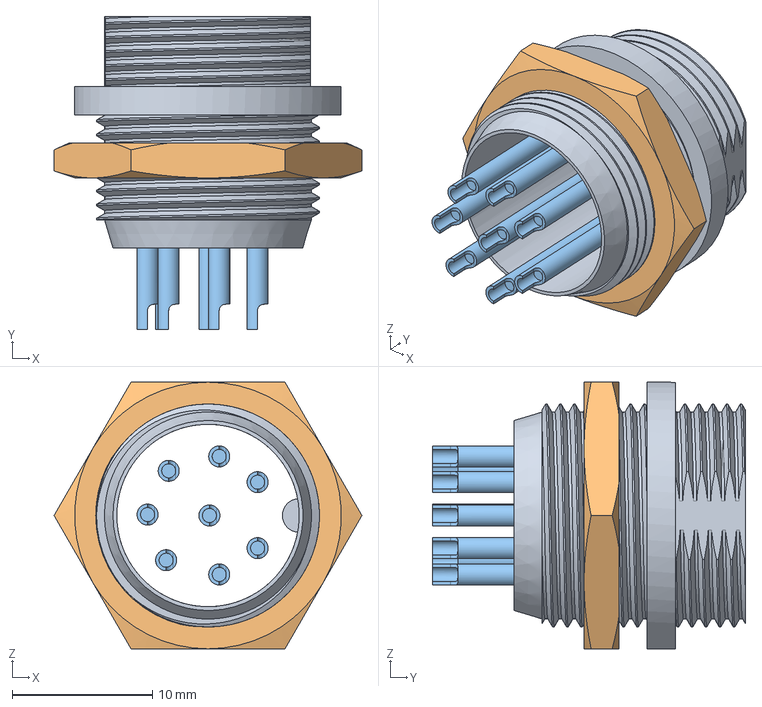
[picture p73: CAD file, 2024-02-05]
Schematic/Wolf/CASE/3'2/3DPrinter/GX16-8.stp
21.9 x 22.3 x 19.0 mm
