XGudron/UA3REO-DDC-Transceiver/Stuff/Manuals/Сопряжение TRX Wolf и CW Skimmer + DXLog.pdf

1. Скачиваем и ставим CW Skimmer 2.1 (содержит Omnirig) https://www.dxatlas.com/CwSkimmer/
2. Включаем аудио-устройства трансивера

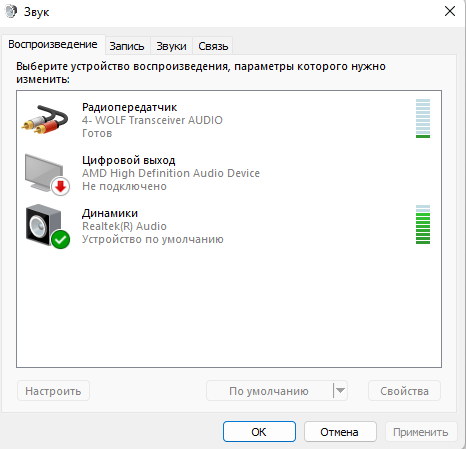
[picture p141: figure]
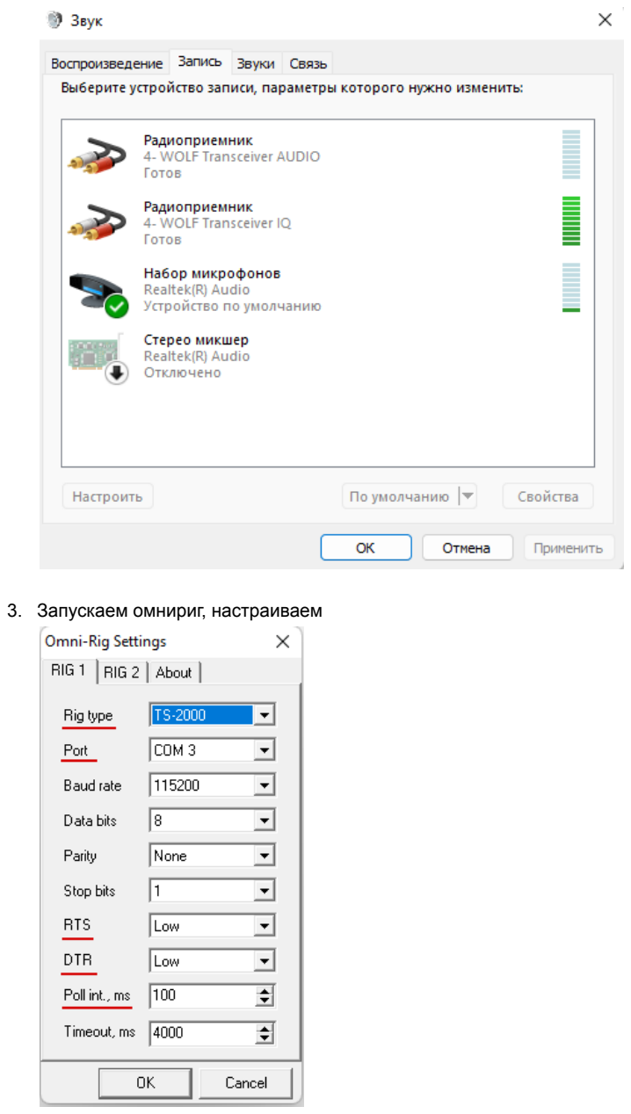
[picture p142: page 2]

3. Запускаем омнириг, настраиваем

4. Запускаем CW Skimmer, регистрируем
5. Настраиваем скиммер
CW Pitch выбираем как в трансивере (Меню -> CW Settings -> Pitch)

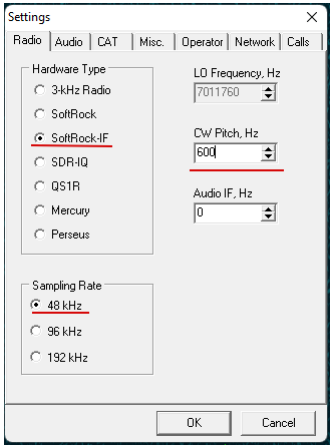
[picture p143: figure]
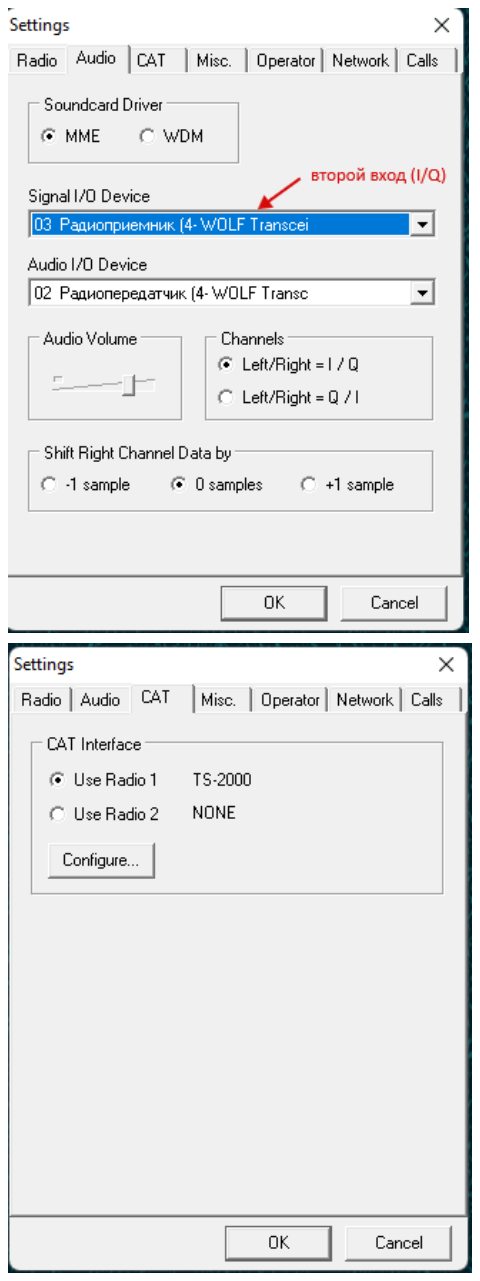
[picture p144: page 4]
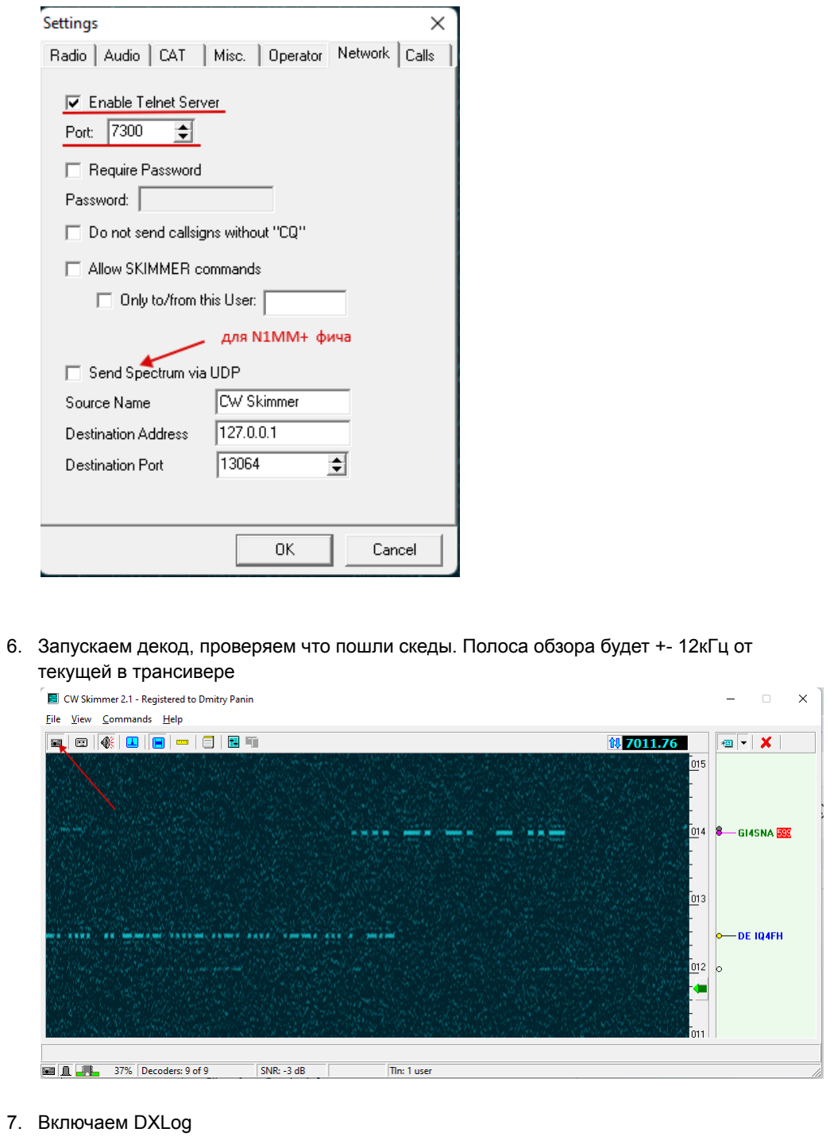
[picture p145: page 5]

6. Запускаем декод, проверяем что пошли скеды. Полоса обзора будет +- 12кГц от текущей в трансивере
7. Включаем DXLog

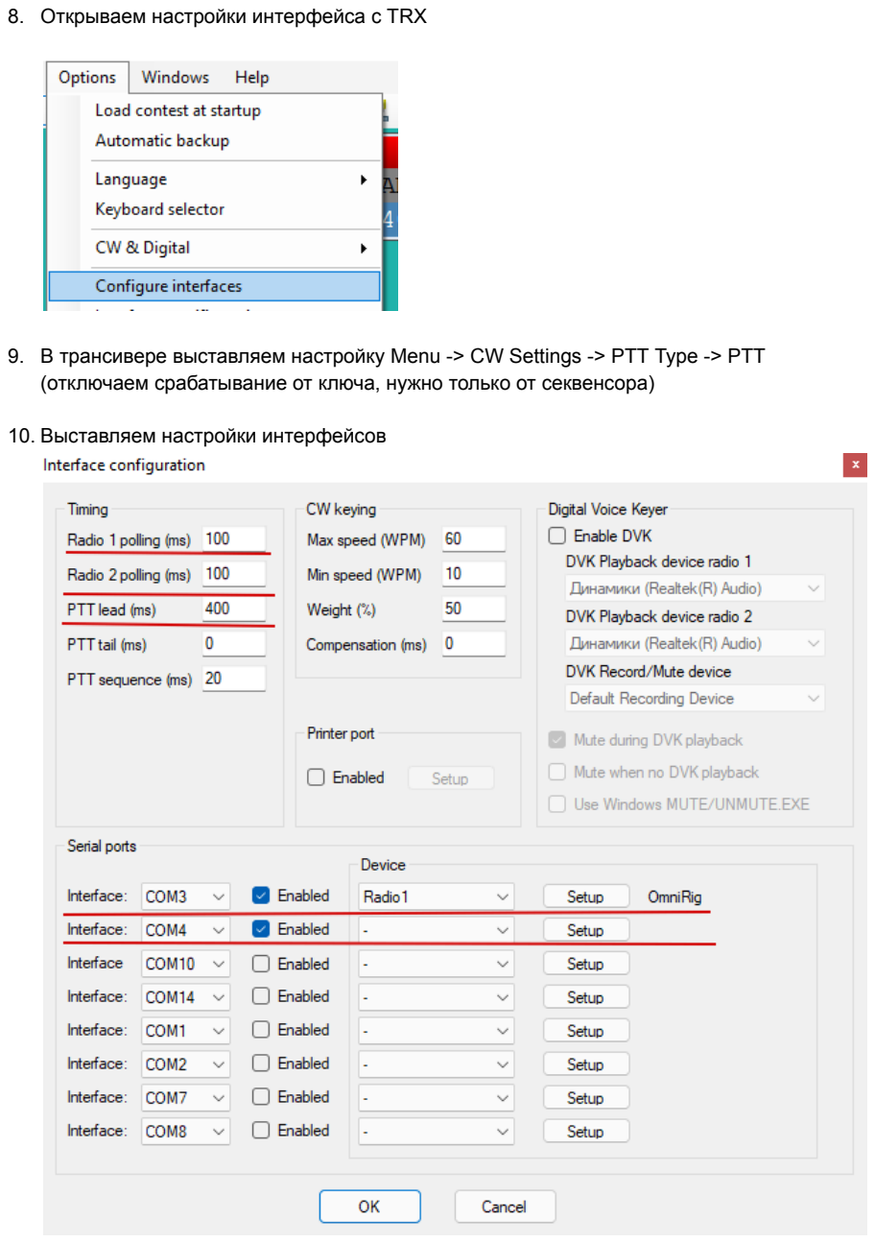
[picture p146: page 6]

8. Открываем настройки интерфейса с TRX
9. В трансивере выставляем настройку Menu -> CW Settings -> PTT Type -> PTT (отключаем срабатывание от ключа, нужно только от секвенсора)
10. Выставляем настройки интерфейсов

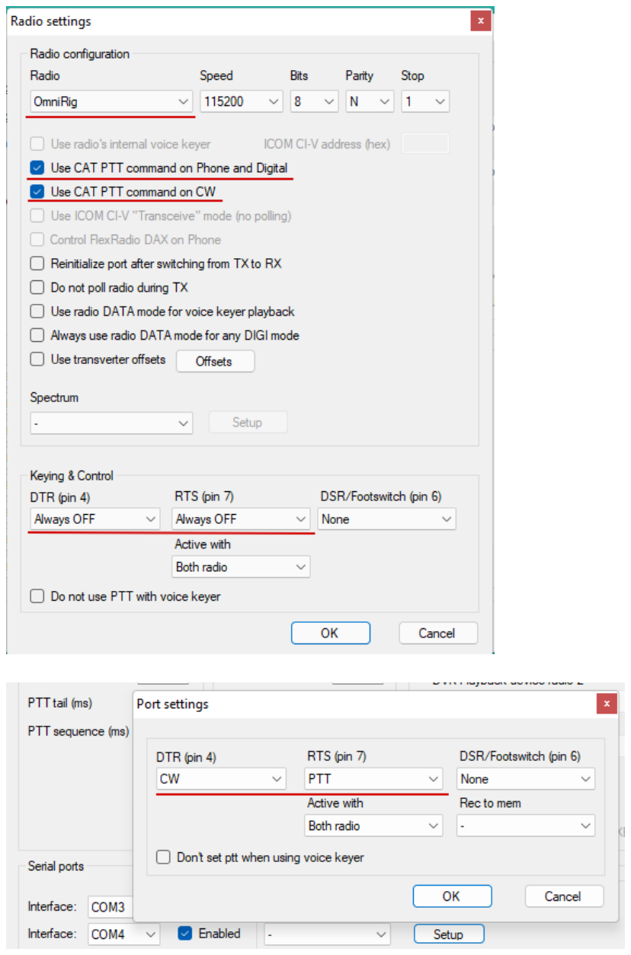
[picture p147: page 7]

11. Проверяем что пошла синхронизация частоты, есть несущая (Ctrl+T), есть ввод с клавиатуры (Alt+K) и он не сжирает первую точку (слушаем самоконтроль на трансивере).
12. Открываем список соединений с кластером

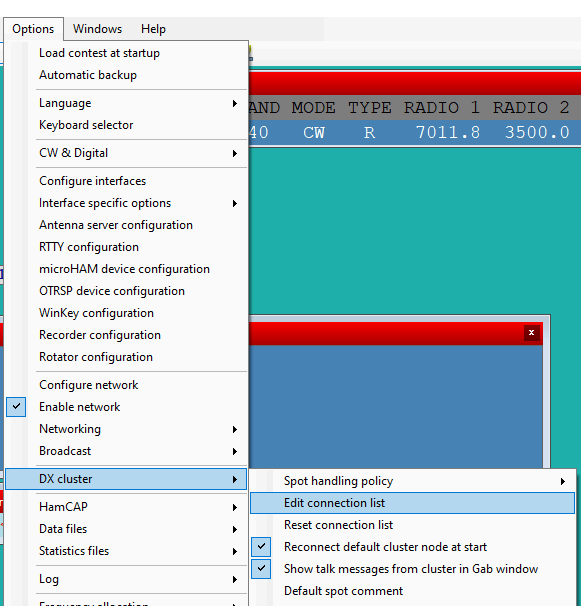
[picture p148: figure]

13. Добавляем локальный кластер скиммера, делаем его активным по умолчанию

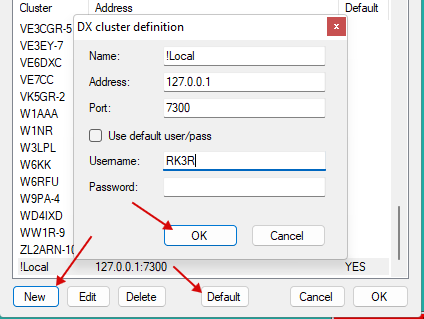
[picture p149: figure]

Включаем соединение при старте

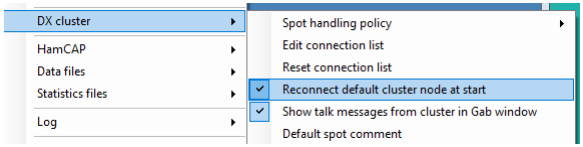
[picture p150: figure]

14. Перезапускаем лог или подключаемся вручную

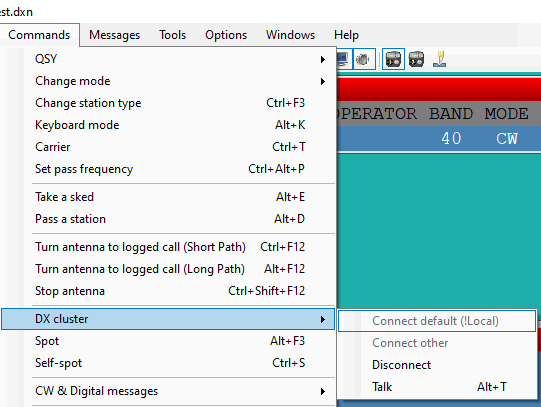
[picture p151: figure]

15. Проверяем что на бендмапе побежали споты

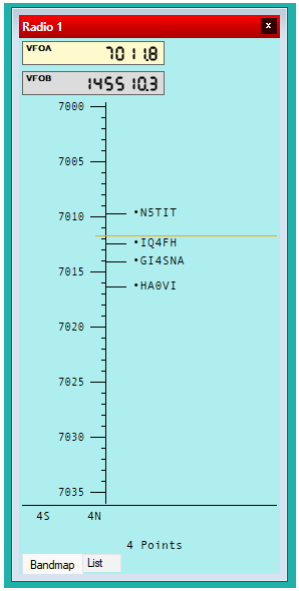
[picture p152: figure]

16. Готово, можно пользоваться
