XGudron/UA3REO-DDC-Transceiver/Schematic/Wolf-DK102/Manual/WOLF_DK102 Руководство по сборке и эксплуатации V0_4_250321.pdf

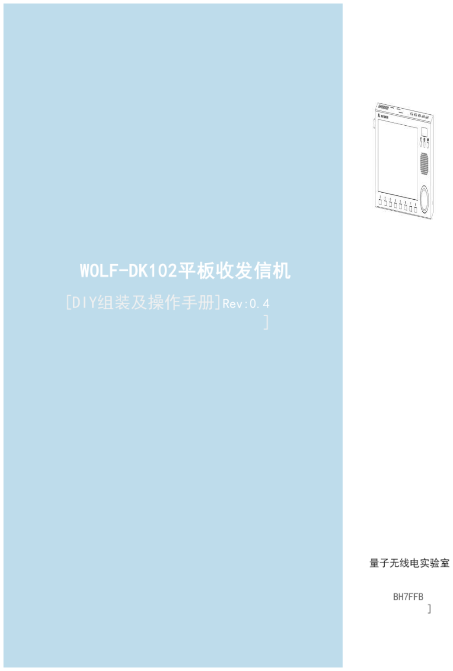
[picture p181: page 1]

[Лаборатория квантового радио] Внутренние учебные материалы

Оглавление
1. Введение | 2
2. Предупреждение | 2
3. Описание панели и кнопок. | 2
3.1 Передняя панель и кнопки | 2
3.2 Верхние кнопки и ручки | 3
3.3 Боковой интерфейс | 3
3.4 Интерфейс главного экрана | 4
4. Описание определения интерфейса | 5
4.1 Вход для зарядки | 5
4.2 Внешние динамики/ACC | 5
4.3 Электрические ключи | 6
4.4 Разъем для наушников | 6
4.5 Антенный вход | 6
4.6 Микрофон | 6
4.7 USB-интерфейс | 6
5. Меню главного экрана | 7
5.1 Главное меню | 7
5.2 Дополнительное меню | 7
6. Индикаторы параметров | 7
6.1 Основные параметры | 7
6.2 Получение параметров | 8
6.3 Параметры передачи | 8
7. Общие способы устранения неполадок | 8
8. Приложение | 9
8.1 Подключение к ПК | 9
8.2 Подключение внешнего усилителя мощности (зарезервировано) | 9
9. Сборка своими руками | 9
9.1 Монтажные инструменты и расходные материалы | 9
9.2 Список устройств | 9
9.3 Сборка и пайка устройства платы приема | 11
9.4 Сборка и пайка устройства на плате AD/DA | 12
9.5 Сборка и пайка устройства платы PA | 14
9,6 МБ монтаж платы сварка | 17
9.7 Монтаж и сварка платы OLED | 20
9.8 Сборка и сварка платы энкодера | 21
9.9 Измерение статического сопротивления | 21
9.10 Измерение напряжения | 23
9.11 Приемочные испытания голой платы | 24
9.12 Испытание на излучение голой платы | 25
9.13 Устранение побочных излучений | 30
9.14 Полная сборка машины | 32
9.15 Полное испытание машины | 40
9.16 Краткое изложение мер предосторожности и вопросов при сборке | 40
1. Введение

Плоский трансивер WOLF-DK102 использует высокопроизводительную

архитектуру прямого радиочастотного захвата. Его ядром является

полнодиапазонный полнорежимный радиоприемопередатчик с повышающим/понижающим преобразованием, разработанный и открытый

российским радиолюбителем «UA3REO» и его командой. «Квантовая

радиолаборатория» превратила его в портативную машину, также известную как

«плоский радиоприемник Вольфа».

Планшетный трансивер WOLF-DK102 оснащен мощными высокоскоростными

компонентами АЦП и радиочастотными блоками, предоставляющими новые

мощные функции и более удобное использование для радиолюбителей.

Высокопроизводительная архитектура прямого обнаружения RF обеспечивает

трансиверу более высокую чувствительность приема и более низкий коэффициент

шума. Кроме того, большой 7-дюймовый сенсорный экран отображает сигналы в

каждой частотной точке в режиме реального времени, что упрощает захват

мимолетных сигналов.

Кроме того, планшетный трансивер WOLF-DK102 также обладает

характеристиками ультрапортативного устройства и его можно легко переносить на

открытом воздухе или во время путешествий. Его встроенная батарея большой

емкости и сверхкомпактная конструкция обеспечивают максимальную

портативность, позволяя пользователям удобно искать свои любимые сигналы в

любое время и в любом месте, что делает использование трансивера более

свободным и гибким.

Смысл этого занятия своими руками заключается в решении трех задач.

Во-первых, снизить сложность производства и предоставить радиолюбителям с недостаточными техническими навыками возможность испытать волка. Во-вторых,

дайте дополнительный выбор тем радиолюбителям, у которых есть технические

возможности, но нет денег, чтобы заниматься своими руками. Потому что стоимость

сборки очень высока, если людей или людей мало. В-третьих, ощутить

удовольствие и технологические усовершенствования DIY.

2. предупреждать
- Во избежание возгорания или поражения электрическим током не подвергайте

данное устройство воздействию дождя или влаги;

- Его должны собирать или ремонтировать квалифицированные специалисты;
- Встроенный аккумулятор: в целях защиты окружающей среды после сдачи в

утилизацию машину необходимо подвергнуть профессиональной переработке;

- | Те, | кто | не | получил | сертификат | радиолюбителя | и | лицензию на

радиолюбительство, не имеют права вести передачу. Нарушители будут

расследованы и наказаны соответствующими ведомствами и подвергнуты

административному наказанию;

- Этот комплект востребованВОЛКЛицензия автора радио с открытым исходным

кодом UA3REO предоставляется в виде набора для использования

радиолюбителями без высоких возможностей самостоятельной сборки с целью

сниженияСложность радио «ВОЛК» своими руками；

- Этот комплект предназначен для того, чтобы получить удовольствие от работы

своими руками и усовершенствования любительской радиотехники по низкой цене, а не для получения прибыли.

3. Описание панели и кнопок
3.1 | Передняя панель и кнопки

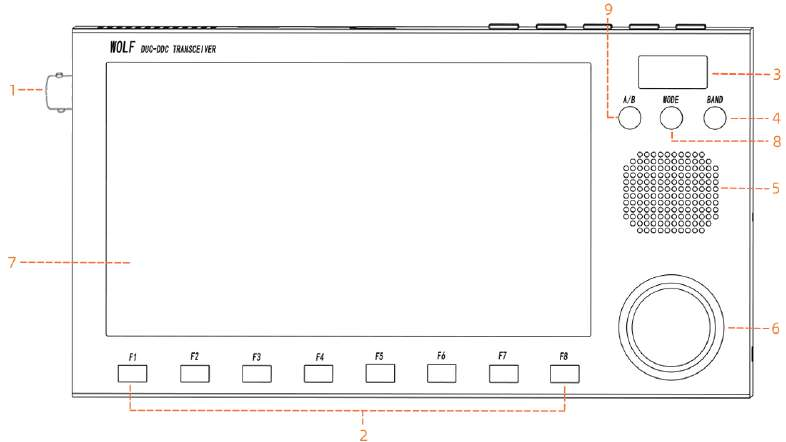
[picture p182: figure]

❶Интерфейс | высокочастотной
антенны

❻Ручка настройки

❷Функциональные клавиши [F1~F8] ❼Главный экран
❸Вторичный экран | ❽[MODE] переключение режима
❹[BAND] переключение диапазонов ❾[A/B] переключение между основной и дополнительной частотой
❺Спикер

3.2 Верхние кнопки и ручки

❶[IF-GAIN] Регулировка усиления
промежуточной частоты

❺[S2] Функциональная клавиша S2

❷Регулировка громкости [AF-GAIN] | ❻[S3] Функциональная клавиша S3
❸Слот для tf-карты | ❼[SCP] Клавиша переключения вторичного
экрана.
❹[S1] Функциональная клавиша
S1/PTT
❽[ПИТАНИЕ] | Короткое | нажатие | для
включения, | длительное | нажатие | для
выключения

3.3 Боковой интерфейс

левая сторона | правая сторон а

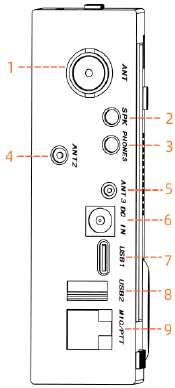
[picture p183: figure]

❶Интерфейс | высокочастотной
антенны

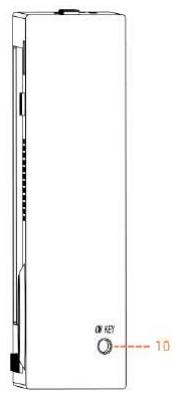
[picture p184: figure]

❻Интерфейс зарядки

❷Внешний динамик/интерфейс
ACC (зарезервировано)

❼интерфейс типа C

❸Разъем для наушников | ❽интерфейс типаА
❹Антенный | интерфейс | U/VHF
(зарезервирован)

❾Интерфейс ручного микрофона

❺Антенный | интерфейс | GPS
(зарезервирован)

❿Интерфейс CW-ключа

3.4 Интерфейс главного экрана

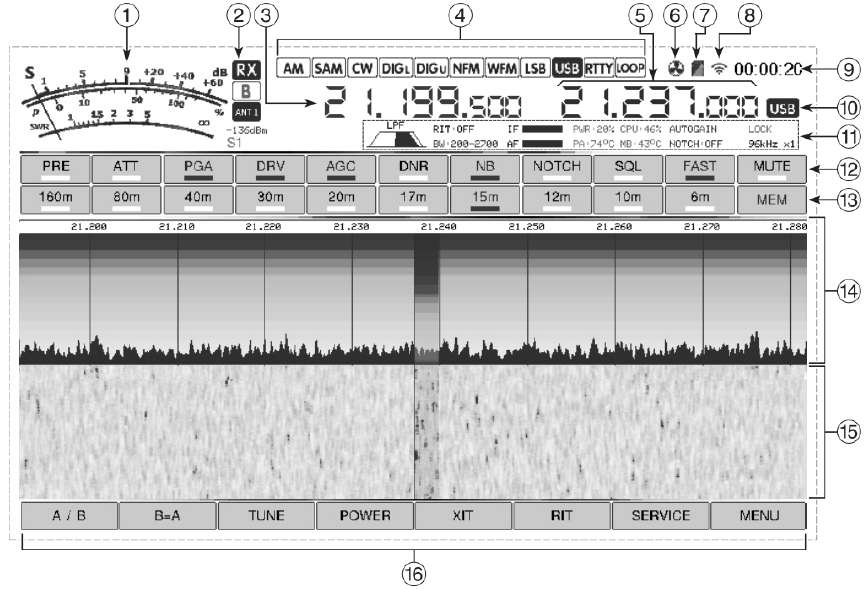
[picture p185: figure]

❶Информационная | панель | (сила
сигнала/мощность передачи/стоячая волна)

❾часы

❷TX/RX передача/прием | ❿Режим работы частоты VFO-B
❸Частота VFO-A | ⓫Текущий статус машины
❹Режим работы частоты VFO-A | ⓬Кнопка быстрой функции
❺Частота VFO-B | ⓭Выбор диапазона
❻Статус фаната | ⓮Спектр БПФ
❼Состояние SD-карты | ⓯WTF водопад
❽Состояние Wi-Fi | ⓰Функциональные программные клавиши
(им соответствуют физические клавиши ниже)

⓫Текущий статус машины

[11-1] | Состояние | полосового | фильтра
(длительное нажатие для настройки)

[11-3]Ширина спектра

[11-2] | IF: | Отображение | усиления
промежуточной частоты
AF: отображение громкости
PWR: процент мощности передачи (длительное нажатие для регулировки)
PA: температура трубки усилителя

[11-4] Индикация блокировки от детей. Нажмите и удерживайте кнопку LOCK, чтобы разблокировать.

мощности
ЦП: отображение загрузки ЦП
МБ: | отображение | температуры
материнской платы
AUTOGAIN: автоматическая коррекция усиления.
NOTCH: режекторный фильтр
⓬Кнопка быстрой функции
[PRE]Малошумящий предусилитель LNA | [ATT]Аттенюатор
[PGA]Предварительный усилитель АЦП | [DRV]Драйвер АЦП
[AGC]Прием автоматической регулировки
усиления

[DNR]Цифровой процессор шума

[NB] Подавитель импульсных помех | [NOTCH]Режекторный фильтр
[SQL] Шумоподавление | [FAST] Ступенчатое ускорение частоты
[MUTE]Отключить звук
4. Описание определения интерфейса
4.1 | вход для зарядки
5525 Разъем постоянного тока | название сигнала | описывать | Примечание
| + | Положительный полюс источника питания | 9~16,8 В постоянного тока Зарядное устройство для литиевой батареи ≤3А
| - | Отрицательный полюс источника питания
4.2 | Внешние динамики/ACC
СПК/АСС | название сигнала | описывать | Примечание
| 1 | Аудиовыход+ | Подключите внешние динамики+

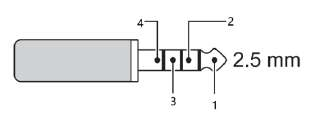
[picture p186: figure]

| 2 | Аудиовыход - | Подключите внешние динамики-
| 3 | ТРХ | Отправка и получение сигналов (зарезервировано)
| 4 | ГРУППА | Диапазон сигнала (зарезервирован)
4.3 | ключ

CW-КЛЮЧ

название
сигнала

описывать Примечание

Точка | сброс сигнала | Поддержка ручных и автоматических ключей, устанавливаемых в меню «CWsettings».
Общий | обществен ный
Бросаться | да сигнал
4.4 | Разъем для наушников
Аудио/PTT-выход | название сигнала | описывать | Примечание
| Верно | левый канал | --
| Левый | правый канал | --
| Земля | земля | --

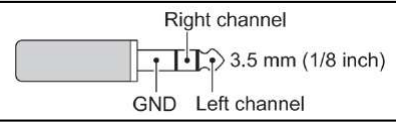
[picture p187: figure]

4.5 | Антенный вход
ANT1: интерфейс ВЧ антенны, розетка BNC, сопротивление 50 Ом.

ANT2: интерфейс антенны GPS, гнездовая база MCX, сопротивление 50 Ом

(зарезервировано)

ANT3: Антенный интерфейс U/VHF, розетка MCX, полное сопротивление 50 Ом

(зарезервировано)

4.6 ручной микрофон
Он поддерживает многофункциональные ручные микрофоны Yaesu MH-36 и MH-48.

Выбрать нужную модель можно в меню главного экрана. Тип интерфейса — RJ12, а

интерфейс ручного микрофона определяется следующим образом.

Интерфейс ручного микрофона RJ12 | приколоть | Сигнал | Примечание
| 1 | РТТ | запуск PTT
| 2 | ВПК | ручной микрофон
| 3 | Земля | Земля
| 4 | 5В | источник питания 5 В
| 5 | ДАТЫ1 | Сигнал данных ручного микрофона 1
| 6 | ДАННЫЕ2 | Сигнал данных ручного микрофона 2

### 4.7 USB-интерфейс

Интерфейс TypeC: связь с компьютером и внешняя зарядка (быстрая зарядка

максимум 27 Вт)

Интерфейс TypeA: внешняя зарядка (быстрая зарядка максимум 27 Вт)

5. Меню главного экрана

5.1 Главное меню
Нажмите кнопку MENU, чтобы войти в главное меню.

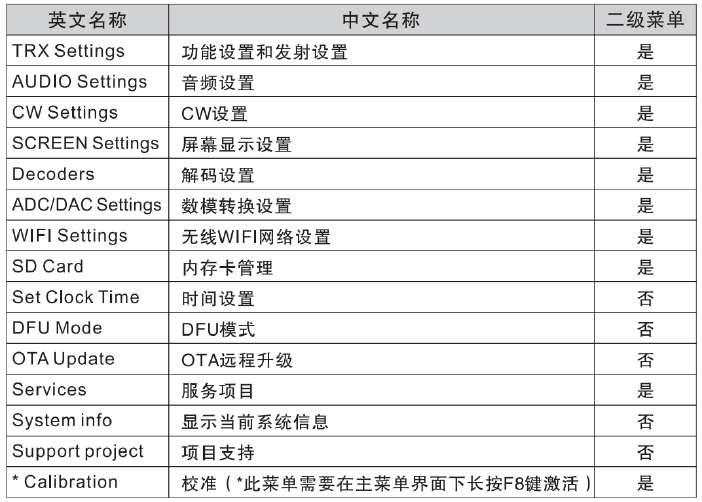
[picture p188: figure]

5.2 Вторичное меню
После входа во вторичное меню вы можете использовать ручку настройки для

выбора различных подменю, затем нажать кнопку в середине ручки настройки,

чтобы выбрать подменю, или коснуться ее непосредственно, чтобы выбрать

подменю. Список вторичного подменю выглядит следующим образом:

❶Настройки функций и настройки запуска

❷Настройки звука
❸Настройки CW
❹Настройки отображения экрана
❺Настройки декодирования
❻Настройки цифро-аналогового преобразования. ❼Настройки беспроводной сети Wi-Fi ❽Управление картами памяти
❾Сервисные предметы
❿Калибровка
6. Индекс параметра

6.1 Основные параметры

- Тип модуляции: CW, LSB, USB, AM, FM, WFM, DIGI
- Напряжение питания: 9 ~ 16,8 В
- Полученный ток: 0,7 А (макс.)
- Ток эмиссии: 3,8 А (макс.)
- Параметры зарядки: зарядное устройство для литиевой батареи 16,8 В/2 А.
- Сопротивление антенны: 50 Ом
- Аудиовыход: 4 Вт (4 Ом, КНИ ≤10%)
- Рабочая температура: -5℃~45℃
- Размер корпуса: 210*119*35 мм (без учета выступов)
- Емкость аккумулятора: 51,8 Втч (встроенный)
- Вес хоста: 910 г

6.2 Получить параметры

- Частота приема: 0,5-750 МГц
- Чувствительность приема (теоретическое значение, не проверялось):

SSB/CW(S/N 10 дБ) 0,16 мкВ (1,8–30 МГц) 0,16 мкВ (50–54 МГц)

AM (S/N 10 дБ) 5 мкВ (0,8–1,8 МГц) 1,6 мкВ (1,8–30 МГц)

- Малошумящий усилитель: LNA
- Регулируемый аттенюатор: 0–31 дБ

6.3 Параметры передачи

- Частота передачи: 0,5–30 МГц (только любительский диапазон частот)
- Мощность передачи: 14,9 Вт (макс.)
★Примечание. | Подробную
информацию о функциях вторичного
меню | см. | в | «Справочнике | по
трансиверу Wolf на китайском языке», составленном BD6MM.

- Подавление побочных эффектов: ≥50 дБ
7. Общие способы устранения неполадок
- Система не работает (отображается в виде зависания экрана и звука или размытого

изображения). Вы можете нажать кнопку сброса на задней панели устройства, чтобы

перезапустить его.

- Касания экрана или нажатия клавиш недействительны. Возможно, блокировка машины от

детей заблокирована. Вы можете часто нажимать кнопку LOCK, чтобы разблокировать его.

- Реакция клавиш медленная или реакция дисплея меню медленная. Возможно, модель

TF-карты не соответствует или не отформатирована.

- Невозможно запустить, удерживая клавишу PTT. Возможно, установлена частота только для

приема или выбран неправильный режим.

- Никакой реакции при нажатии кнопки питания. Возможно, аккумулятор разряжен или

внешний источник питания имеет неправильную полярность.

- Высота стоячей волны отображается во время запуска, и после этого машина не может

запуститься. Возможно, передающая цепь перешла в состояние защиты, и машину

необходимо перезапустить.

- Аккумулятор, встроенный в машину, нельзя заряжать. Возможно, ток зарядного устройства

слишком велик и машина защищена. Зарядный ток не должен превышать 3А.

8. приложение

8.1 Подключиться к ПК

- Подключите интерфейс USB (typeC) устройства к интерфейсу USB ПК. ПК распознает

звуковую карту USB и взаимодействует с программным обеспечением на ПК, например

HAMRADIODELUX, HDSDR и т. д. (не проверено).

- Подключите интерфейс USB (typeC) устройства к интерфейсу USB ПК. ПК также распознает

COM-порт. COM-порт можно использовать для открытия программного обеспечения

последовательного терминала на ПК и просмотра информации о рабочем состоянии

машины.

8.2 Подключение к внешнему усилителю мощности (зарезервировано)

- Сигнал приемопередатчика TRX в интерфейсе SPK/ACC машины подключен к сигналу

управления приемопередатчиком интерфейса управления внешним усилителем мощности.

- Сигнал диапазона BAND в интерфейсе SPK/ACC машины подключен к сигналу управления

диапазоном интерфейса управления внешним усилителем мощности.

- Антенный интерфейс HF ANT устройства подключен к входному порту антенны внешнего

усилителя мощности.

9. Сборка своими руками
9.1 | Инструменты и расходные материалы для сборки
- | Необходимые | инструменты:Паяльник, паяльная проволока, мультиметр, диагональные

плоскогубцы, пинцет, острогубцы, имитатор нагрузки 50 Ом при 20 Вт, коротковолновая

| антенна;
- Вторичные инструменты:Анализатор спектра, аттенюатор 50 дБ при 20 Вт и согласующая

перемычка (аттенюатор может заменить имитатор нагрузки), канцелярский нож,

регулируемый источник питания, измеритель стоячей волны, инструмент для зачистки

проводов, антистатический браслет или антистатические перчатки;

- Расходные материалы:Высокотемпературный скотч шириной более 15 мм, двухсторонний

клей-пенопласт (толщина 1 мм, ширина около 15 мм), промывочная вода или безводный

спирт (не обязательно); мягкая проволока диаметром около 0,4мм и длиной 50см;

теплопроводящая силиконовая смазка

- Что следует отметить:Перед сборкой вымойте руки и снимите статический заряд. Убедитесь,

что паяльник заземлен.

9.2 | Список запчастей
| се ри йн ый но
| тип | Модель/Описание ко ли че ст во

ме р

1 | Терми нальн ый кабел ь | Вилка с шагом 1,25, 2PIN, несимметричный, L=60 мм | 1
2 | Терми нальн ый кабел ь | Вилка с шагом 1,25 дюйма, 10-контактная, перевернутая с обоих концов, L=120 мм. | 1
3 | Терми нальн ый кабел ь | Вилка с шагом 1,25, 6-контактная, перевернутые концы, L=120 мм | 1
4 | Терми нальн ый кабел ь | Вилка с шагом 1,25, 12-контактная, перевернутые концы, L=250 мм | 1
5 | Терми нальн ый кабел ь | Вилка с шагом 1,25 мм, 14-контактная, перевернутые концы, L=130 мм. | 1
6 | Терми нальн ый кабел ь | Вилка с шагом 1,25, 4-контактная, несимметричная, L=50 мм | 2
7 | Терми нальн ый кабел ь | Вилка с шагом 2,54, 8-контактная, перевернутая с обоих концов, L=80 мм | 1
8 | RF-кабе ль | Разъем IPX на обоих концах, 113 линий, 50 Ом, длина = 130 мм. | 2
9 | RF-кабе ль | Разъем IPX на обоих концах, 113 линий, 50 Ом, L=100 мм | 2
10 RF-кабе | ль | Разъем IPX на обоих концах, 113 линий, 50 Ом, длина = 200 мм. | 1
11 | Силик онова я прово лока | Красный, силиконовый провод 18AWG, 6А, L=80 мм. | 1
12 | Силик онова я прово лока | Черный, силиконовый провод 18AWG, 6А, L=80 мм. | 1
13 ЖК-экр | ан | 7 дюймов, RGB, разрешение 800*480, емкостный сенсорный экран, настраиваемая подсветка высокой яркости | 1

14 | аккум улято рная батар ея | 18650, 3500 мАч, 4 ячейки последовательно, с 6-чиповым разъемом питания, 3-жильный разъем для отбора проб | 1
15 | колпа чки клави ш | Колпачок на пуговице 9*5*7,5 силикон | 13
16 | колпа чки клави ш | Клавиатура φ6*6*6,5-29 | 3
17 орато | р | Полнодиапазонный динамик 1,5 дюйма, высота 2 см, 4 Ом, 5 Вт | 1
18 шасси | | Алюминиевый сплав, индивидуальный, черный, с черными винтами с потайной головкой M2 * 5 9 шт., черные винты с потайной головкой M2 * 3 10 шт., с обычными серебряными винтами M2 13 шт., с роговой прокладкой из алюминиевого сплава | 1
19 | заряд ное устро йство | 16,8 В/2 А, разъем DCJack 5525 | 1
20 | ручно й микро фон | Домашний ручной микрофон MH-48A6J | 1
21 Прокл | адка | Прокладка М2 | 2
22 | орех | М12*0,75*3 | 1
23 | орех | Гайка М2 | 12
24 шпиль | ки | Внутреннее отверстие M2 на одном конце, винт M2 на другом конце, высота корпуса 3 мм. | 12
25 винт | | Крестообразные винты M2*3 с плоской головкой | 4
26 прихв | атка | 3,5*13 см, толщина: 1 мм | 1
27 | термо прокл адка | 16*30 мм, толщина: 2 мм | 1
28 | термо прокл адка | 16*16 мм, толщина: 3 мм | 1
29 | Эмали рован ный прово д | φ0,15 мм, длина = 0,4 м | 1
30 | Эмали рован ный прово д | φ0,40 мм, длина = 2,45 м | 1

31 | Эмали рован ный прово д | φ0,60 мм, длина = 0,77 м | 1
32 | Квадр атный щит | 3 типа защитных чехлов: 0,55*11,77*1,73 мм; 24,15*24,25*3,4 мм; 25,4*12,3*3,3 мм | 1
33 | Защит ная крышк а специ ально й формы | 2 типа защитных чехлов по индивидуальному заказу | 1
34 | Прово дящая пена | Длина: 7 мм, ширина: 6 мм, толщина: 3 мм. | 1
35 | магни тное кольц о | Т37-6 | 8
36 | магни тное кольц о | Т37-1 | 2
37 | магни тное кольц о | Т37-2 | 2
38 | магни тное кольц о | БН43-202 | 1
39 | магни тное кольц о | БН-61-202 | 1
40 | магни тное кольц о | БН43-2402 | 1
41 | магни тное кольц о | ФТ37-43 | 1
42 | печат ная плата | ДК-102_МБ_В01 | 1
43 | печат ная плата | ДК-102_AD_DA_V01 | 1
44 | печат ная плата | ДК-102_ПА_В01 | 1

45 | печат ная плата | ДК-102_RX_V01 | 1
46 | печат ная плата | ДК-102_OLED_V01 | 1
47 | печат ная плата | ДК-102_TUNING_V01 | 1
48 разъе | м | 1251S-2P (штуцер с шагом 1,27 мм) | 1
49 разъе | м | 1251S-3P (штуцер с шагом 1,27 мм) | 1
50 разъе | м | 1251S-4P (штуцер с шагом 1,27 мм) | 3
51 разъе | м | 1251S-6P (штуцер с шагом 1,27 мм) | 1
52 разъе | м | 1251S-12P (штуцер с шагом 1,27 мм) | 1
53 разъе | м | 1251S-14P (штуцер с шагом 1,27 мм) | 1
54 разъе | м | XH-6A (штуцер с шагом 2,54 мм) | 1
55 разъе | м | PM127V-6P (мама с шагом 1,27 мм) | 9
56 разъе | м | PJ-320A (разъем для наушников 2,5 мм) | 1
57 разъе | м | USB-265-BRW | 1
58 разъе | м | BNC_DOSIN-801-0080 | 1
59 разъе | м | DS1133-S60BPX,RJ12 | 1
60 разъе | м | MCX-KWE, ДИП | 2
61 разъе | м | MCX-КЕ,ДИП | 2
62 | ключе вой перек лючат ель | Тактовый переключатель, 6*6, боковой монтаж | 5
63 | ключе вой перек лючат ель | Тактовый переключатель, 6*6, вертикальная установка | 3
64 | элект ретны й микро фон | B4012AP422-003 | 1
65 | элект ролит ическ ий конде | 220 мкФ/35 В, φ8 мм, высота = 12 мм, DIP | 1

| нсато р
66 | НТЦ | MF52B104F3950L100(100к/нтк) | 1
67 | ТЫ | 0,96-дюймовый OLED, FPC | 1
68 кодер | | Датчик KC, черный, с кнопкой посередине. | 1
69 | регул ируем ое сопро тивле ние | Регулируемый резистор 50К Б503-16 | 2
70 | интег ральн ая схема | Датчик температуры KTY81/120 | 1
9.3 | Сборка и пайка устройства платы RX
- Припаяйте разъемы J9 (1251S-12P), J8 (1251S-14P) и J3 (1251S-10P) к плате DK-102_RX.

Конкретные положения показаны в красной области значка ниже (обратите внимание, что

разъемы вставляются в соответствии с направлением шелкографии и не могут быть

установлены задом наперед). U23 паять не нужно.

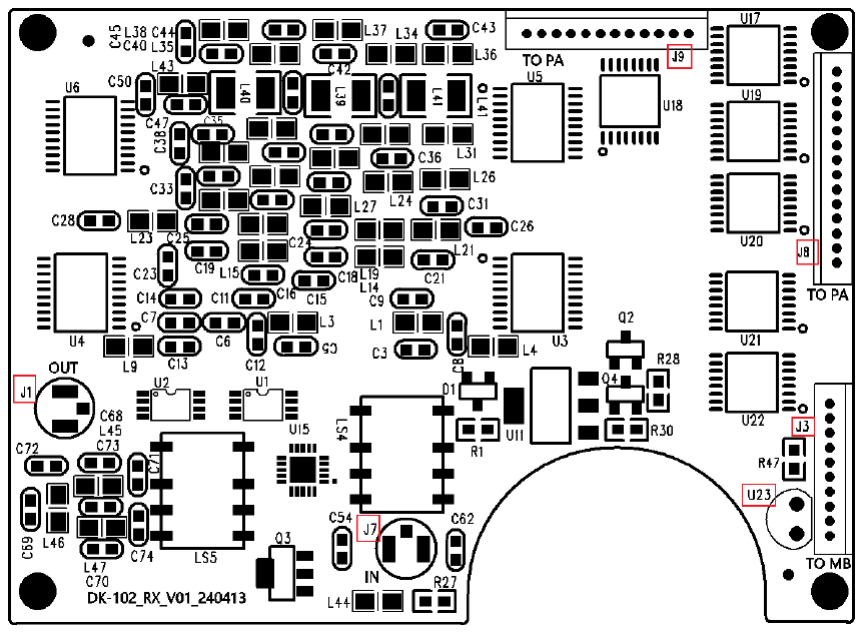
[picture p189: figure]

- Фактический продукт после завершения выглядит так, как показано ниже (паяные

соединения можно очистить промывочной водой или абсолютным спиртом).

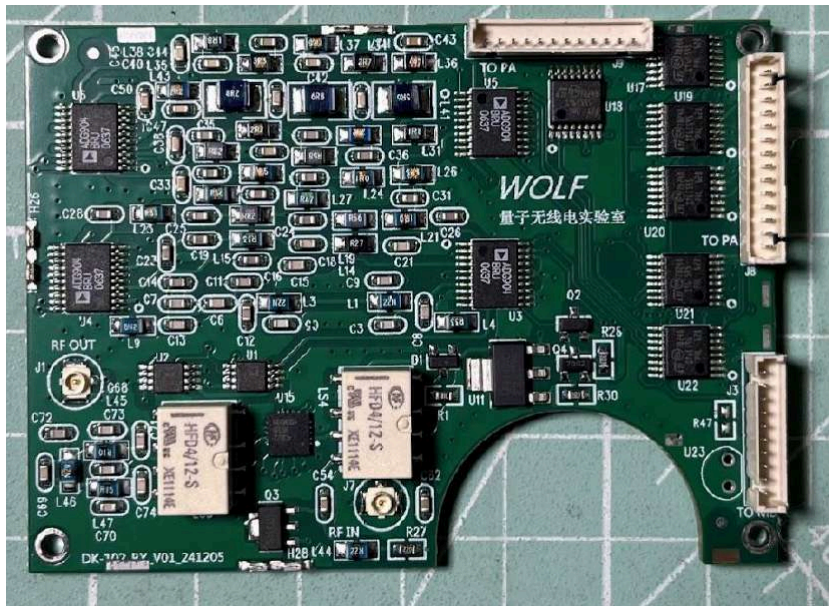
[picture p190: figure]

9.4 Сборка и пайка устройств на плате AD/DA

- Припаяйте J9 (XH-8A), J18 (PJ-320A), J8 (1251S-14P), J16 (1251S-6P) к плате

DK-102_ADC_DAC (обратите внимание, что разъем вставляется в соответствии с

направлением шелкографии и не может быть установлен задом наперед).R45 и R52

необходимо удалить и заменить примерно на 330–680 Ом.Резистор (корпус 0402),

конкретное расположение показано в красной области значка ниже.

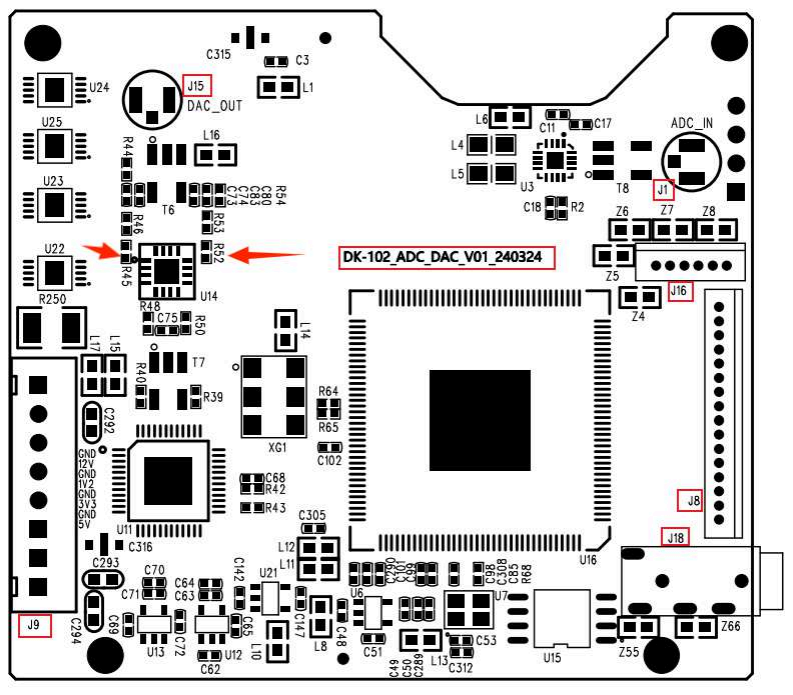
[picture p191: figure]

- Фактический продукт после завершения выглядит так, как показано ниже (паяные

соединения можно очистить промывочной водой или абсолютным спиртом).

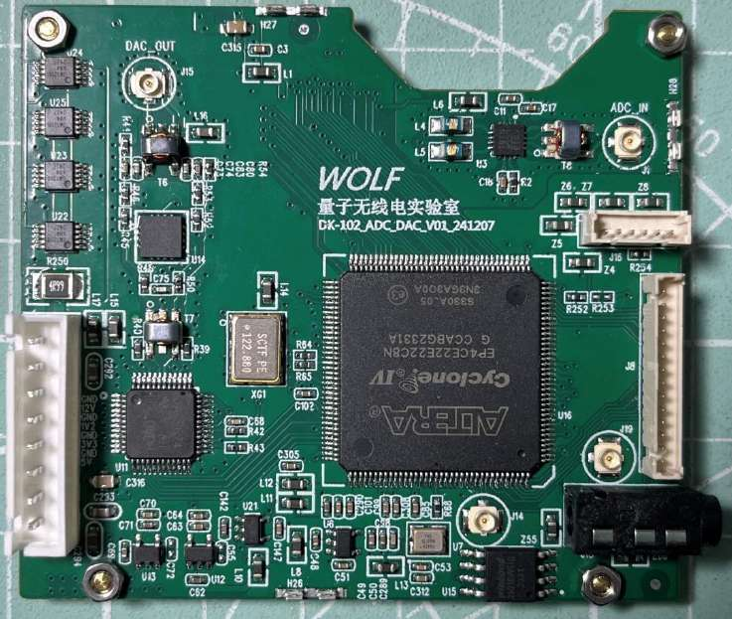
[picture p192: figure]

9.5 Сборка и сварка устройства платы ПА

- Намотайте магнитное кольцо в соответствии с таблицей ниже (для справки), 1T означает 1

оборот (в частности, см. завершенное физическое изображение ниже).

Магнитное кольцо (цвет/размер) | Количеств о витков(Т) | Диаметр проволоки (мм) | Количест во (шт.) | номер бита
Катушка с воздушным сердечником 0,068uH (диаметр 5,3 мм) | 5 | 0,60 | 2 | Л15, Л17
ФТ37-43(черный) | 5 | 0,60 | 1 | Л2
БН43-202(13,3*14,3 мм) | 1+1:3 | 0,60 | 1 | Т3
БН-61-202(13,3*14,3мм) | 1+1 | 0,60 | 1 | Т5
| 10+10 | Мягкая проволока диаметром 0,4 или около того или эмалирова нная проволока. | 1
Т37-2(красный) | 20 | 0,40 | 2 | Л26, Л27
Т37-1(синий) | 21 | 0,40 | 2 | Л28, Л29

Т37-6(желтый) | 8 | 0,40 | 2 | Л18, Л19
Т37-6(желтый) | 10 | 0,40 | 2 | Л20, Л21
Т37-6(желтый) | 13 | 0,40 | 2 | Л22, Л23
Т37-6(желтый) | 15 | 0,40 | 2 | Л24, Л25
БН43-2402(7*6,2 мм) | 6+6 | 0,15 | 1 | Т7
| 4 | 0,15 | 1

Способ намотки следующий. После завершения намотки концы обоих концов

эмалированного провода нужно зачистить краской и залужить. При лужении старайтесь отделять

концы проволоки от магнитного кольца и не нагревайте паяльник слишком долго. Избегайте

высокотемпературного повреждения магнитного кольца (настоятельно рекомендуется залудить

магнитное кольцо перед вставкой его в плату для пайки, иначе его будет легко припаять)

логическая схема | Схема намотки
Схема контактов сборки
печатной платы
- Способ намотки печатной платы номер Т7 следующий.

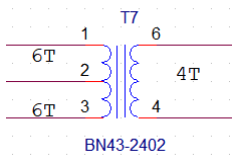
[picture p193: figure]
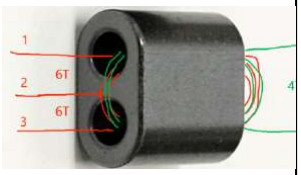
[picture p194: figure]

логическая схема | Схема намотки | Схема контактов сборки
печатной платы
- Способ намотки печатной платы номер Т3 следующий.

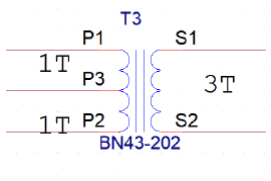
[picture p195: figure]

логическая схема

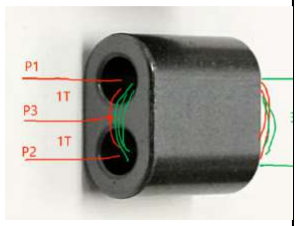
[picture p196: figure]
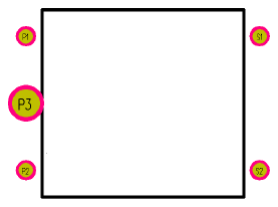
[picture p197: figure]

Схема намотки | Схема контактов сборки
| печатной платы
- Метод намотки печатной платы с номером T5 следующий: 2–7, 3–6 — эмалированный

провод φ=1 мм, эмалированный провод 10T — φ=0,5 мм.

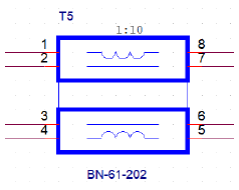
[picture p198: figure]

логическая схема

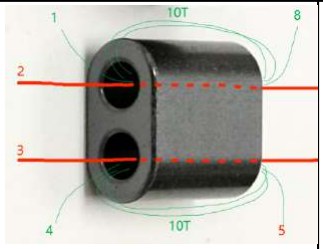
[picture p199: figure]

Схема намотки

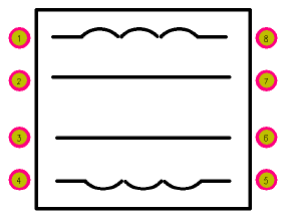
[picture p200: figure]

Схема контактов сборки
печатной платы
- Приварить T7, R79, R80 (потенциометр), L2, T3, J2, T5, J17, J16, ANT2, J15, J13, L22, L23,

L28, в плате ДК-102_ПА

L29,L24,L25,L20,L21,L26,L27,19,L18,L15,L17,U1(Датчик температуры KTY81/120). Между U1 и

печатной платой можно нанести термосиликоновую смазку.Удалите D71 и D73.,Положительный и

отрицательный полюсы диода D70 спроектированы неправильно, и перед приваркой их

необходимо снять и повернуть на 180 градусов.(Правильная полярность должна быть такой, как

показано ниже). Конкретное расположение необходимых сварочных компонентов показано в

красной рамке значка ниже, также вы можете проверить номер бита на плате. Т7 можно

закрепить клеем.

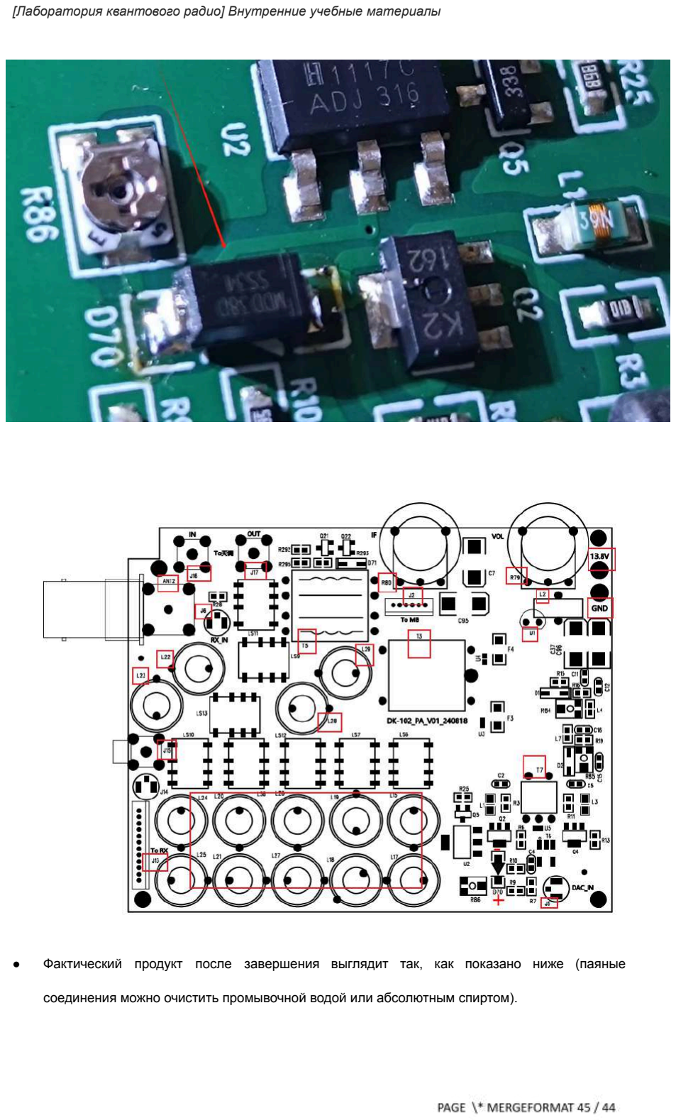
[picture p201: page 24]

- Фактический продукт после завершения выглядит так, как показано ниже (паяные

соединения можно очистить промывочной водой или абсолютным спиртом).

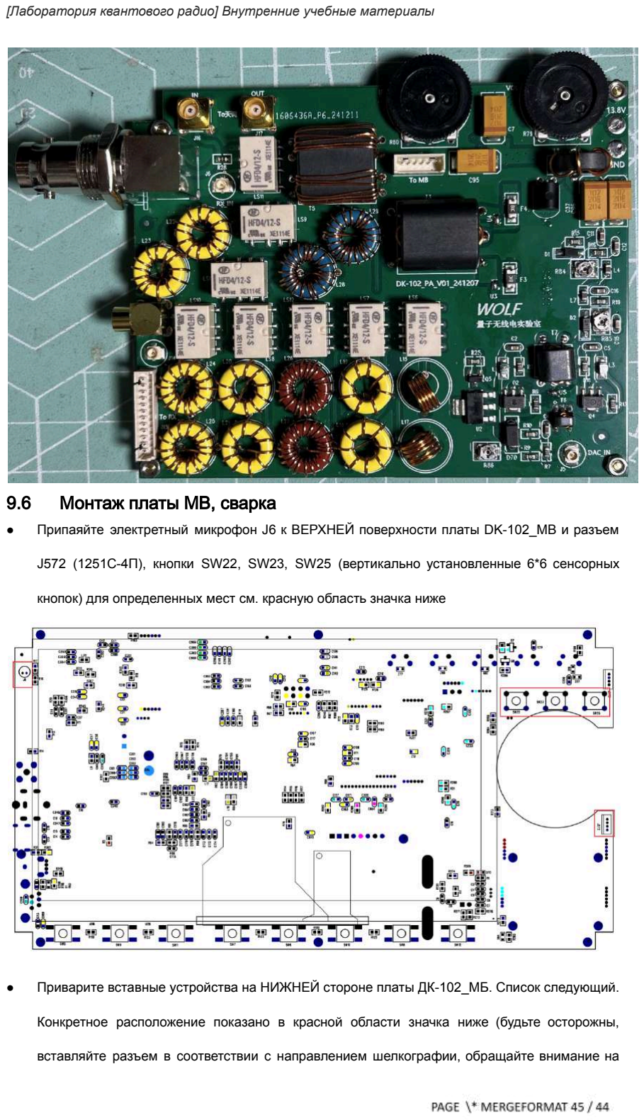
[picture p202: page 25]

9.6 Монтаж платы MB, сварка

- Припаяйте электретный микрофон J6 к ВЕРХНЕЙ поверхности платы DK-102_MB и разъем

J572 (1251С-4П), кнопки SW22, SW23, SW25 (вертикально установленные 6*6 сенсорных

кнопок) для определенных мест см. красную область значка ниже

- Приварите вставные устройства на НИЖНЕЙ стороне платы ДК-102_МБ. Список следующий.

Конкретное расположение показано в красной области значка ниже (будьте осторожны,

вставляйте разъем в соответствии с направлением шелкографии, обращайте внимание на полярность конденсатора и не устанавливайте его наоборот). После пайки открытые

контакты на поверхности TOP необходимо обрезать, иначе это повлияет на экран для

поверхностного монтажа TOP.

1 | ключевой переключатель | TS-1093C (боковой монтаж) | SW13, SW14, SW15, SW24, SW26
2 | разъем | 1251S-2P (2-контактная розетка с шагом 1,27) | J7
3 | разъем MCX | MCX-KWE | J15
4 | Разъем RJ12 | DS1133-S60BPX | J22
5 | разъем | USB-265-BRW | J47
6 | разъем | 1251S-3P (3-контактная розетка с шагом 1,27) | J48
7 | разъем | Однорядный гнездовой разъем с шагом 1,27 мм. | J560,J561,J562,J563,J564,J565, J566,J570,J571
8 | разъем | 1251S-4P (4-контактная розетка с шагом 1,27) | J573
9 | разъем | ХН-6А | J577
10 | разъем | PJ-242 (разъем для наушников | J8
2,5 мм)Необходимо отрезать нижнюю позиционирующую
стойку.
11 | электролитичес кий конденсатор | 220 мкФ/35 В, φ8, высота = 12 мм | С960
12 | НТЦ | MF52B104F3950L100(100к/нтк) | 270 рэндов

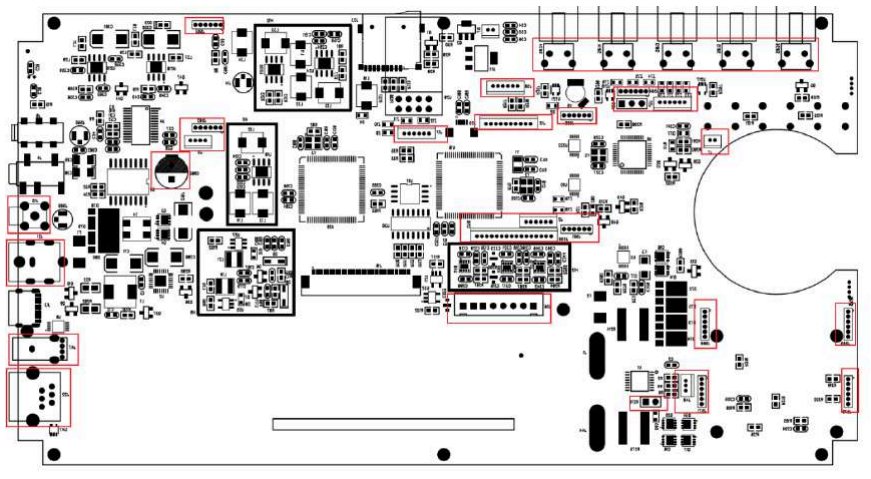
[picture p203: figure]

- Фактический продукт после завершения выглядит так, как показано ниже (паяные соединения можно очистить промывочной водой или абсолютным спиртом).

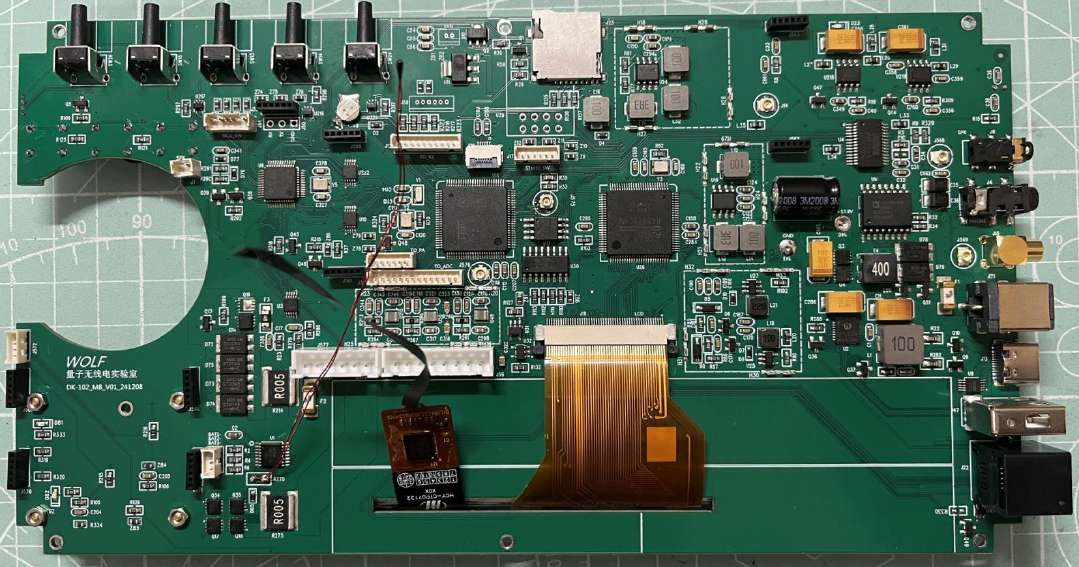
[picture p204: figure]

- Суперконденсатор, используемый в часах, расположен рядом с боковой кнопкой. Номер

битаY6, если мощности не хватает, нужно заменить на модель:ML414H-IV01E, иначе время,

отображаемое на главном экране, будет неточным.

- U4 необходимо использовать проволочную проволоку для приваривания двух резисторов 2,2

кОм к стрелке (в противном случае будет вероятность бесшумной загрузки или ошибки

инициализации аудиокода). Положение U4 показано в красной рамке устройства.

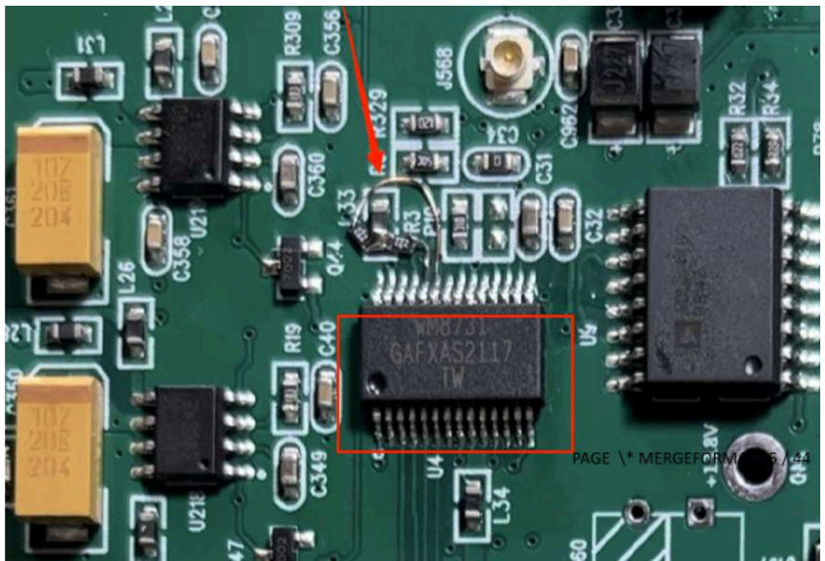
[picture p205: figure]

- Фактический продукт после завершения выглядит так, как показано ниже (паяные

соединения можно очистить промывочной водой или абсолютным спиртом).

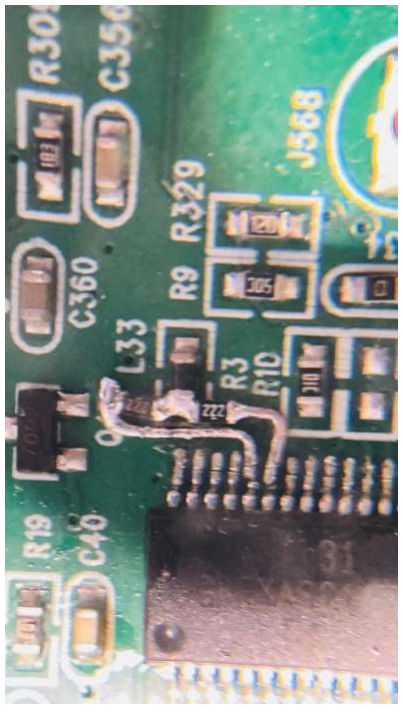
[picture p206: figure]

9.7 Сварка для монтажа платы OLED

- Припаяйте 4-жильный провод (вилка с шагом 1,25, 4-контактный, несимметричный, L=50) к

позиции J572 на плате DK-102_OLED. Обратите внимание на соответствующую взаимосвязь

между порядком пайки проводов и направлением вилки (см. завершенное физическое

изображение ниже).

- Завершите физический рисунок (паяные соединения можно очистить промывной водой или

абсолютным спиртом)

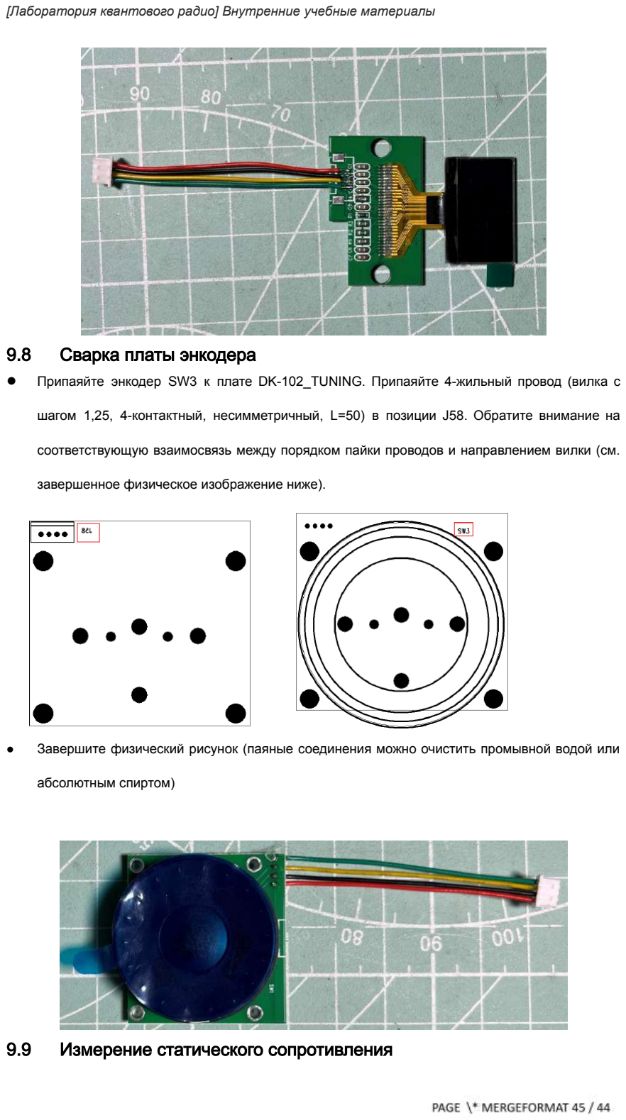
[picture p207: page 29]

9.8 Сварка платы энкодера
- Припаяйте энкодер SW3 к плате DK-102_TUNING. Припаяйте 4-жильный провод (вилка с

шагом 1,25, 4-контактный, несимметричный, L=50) в позиции J58. Обратите внимание на

соответствующую взаимосвязь между порядком пайки проводов и направлением вилки (см.

завершенное физическое изображение ниже).

- Завершите физический рисунок (паяные соединения можно очистить промывной водой или

абсолютным спиртом)

9.9 Измерение статического сопротивления

- Знаком со схемой топологии соединений каждой печатной платы всей машины.

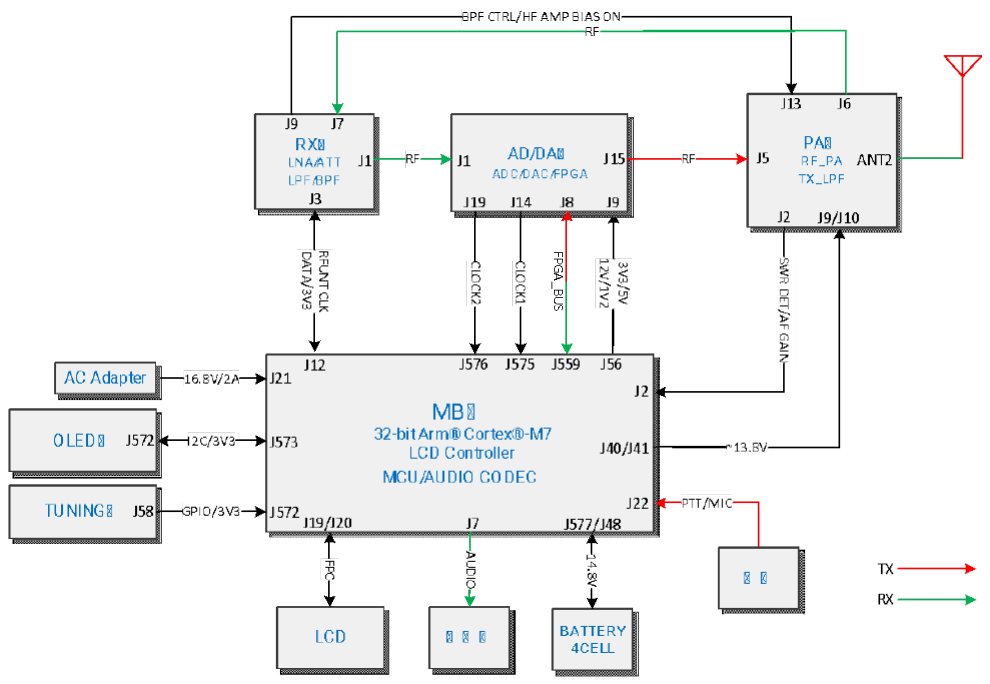
[picture p208: figure]

- Подключите каждую плату соответствующими кабелями в точках, указанных в таблице ниже

(взаимосвязь соответствует схеме топологии).

Кабель | Точка платы DK-102_MB | Оценка доски DK-102_AD_DA
Вилка с шагом 2,54, 8-контактная, перевернутая с обоих концов, L=80 | J56 | J9
Вилка с шагом 1,25, 14-контактная, перевернутые концы, L=130 | J559 | J8
Разъем IPX на обоих концах, 50 Ом, L=130 | J575 | J14
Разъем IPX на обоих концах, 50 Ом, L=130 | J576 | J19
Кабель | Точка платы DK-102_MB | Точка на плате DK-102_RX
Вилка с шагом 1,25, 10-контактная, | J12 | J3

перевернутые концы, L=120

Кабель | Точка платы DK-102_MB | Доска DK-102_PA
Вилка с шагом 1,25, 6-контактная, перевернутые концы, L=120 | J2 | J2
Кабель | Точка на плате DK-102_RX | Доска DK-102_PA
Вилка с шагом 1,25, 12-контактная, перевернутые концы, L=250 | J9 | J13
- Измерьте статический импеданс каждой точки на рисунке ниже на плате DK-102_MB

(зафиксируйте каждую плату и не допускайте короткого замыкания).

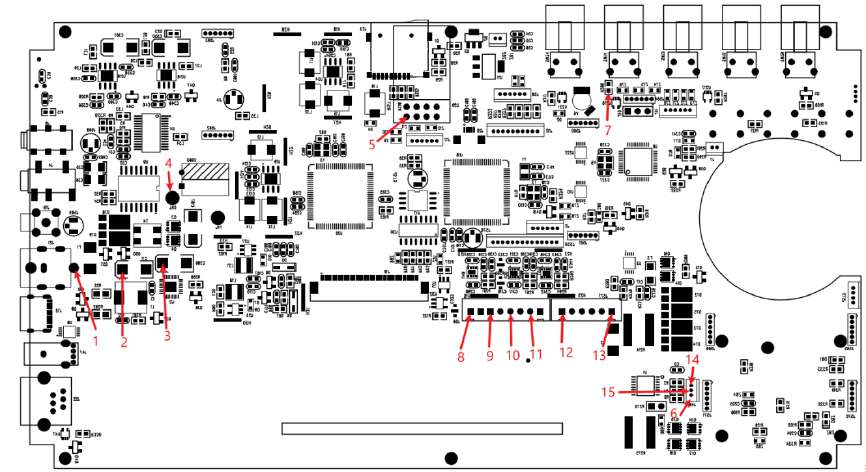
[picture p209: figure]

Располо жение | Эталонное значение импеданса | Располо жение | Эталонное значение импеданса | Располо жение | Эталонное значение импеданса | Располо жение | Эталонно е значение импеданс а
❶ | >800 Ом | ❷ | >800 Ом | ❸ | >800 Ом | ❹ | >800 Ом
❺ | Около 100 | ❻ | >800 Ом | ❼ | >800 Ом | ❽ | >800 Ом

| Ом
❾ | Около 100 Ом | ❿ | >800 Ом | ⓫ | >800 Ом | ⓬ | >800 Ом
⓭ | >800 Ом | ⓮ | >800 Ом | ⓯ | >800 Ом | ⓰ | >800 Ом

9.10 Измерение напряжения

- Отсоедините кабель, соединяющий плату DK-102_MB с другими платами, подключите

зарядное устройство (16,8 В) к разъему J21, а затем включите зарядное устройство.

Проверьте, что напряжение в позиции 1 на рисунке ниже должно составлять 16,8 В. Нажмите

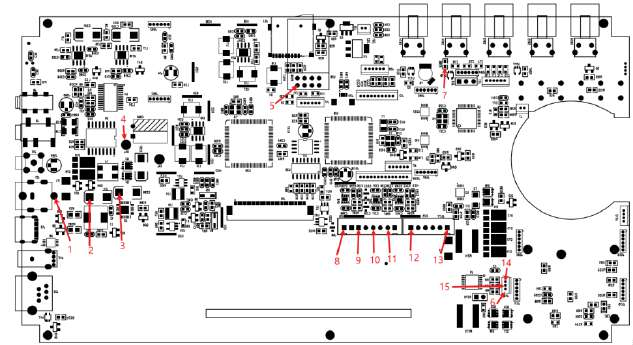
[picture p210: figure]

SW26, а затем SW 15. Посмотрите, нет ли каких-либо отклонений на плате. Если отклонений

нет, измерьте, соответствует ли напряжение в других позициях эталонному значению (будьте

осторожны, чтобы не вызвать короткое замыкание во время проверки. Вы можете

подключить кабель к позициям 8–11 и проверить другой конец кабеля). После проверки

напряжения отключите зарядное устройство.

Располо жение | Значение опорного напряжени я | Распол ожение | Значение опорного напряжения | Располо жение | Значение опорного напряжени я | Распол ожение | Значение опорного напряжения
❶ | 16,8 В | ❹ | 16,8 В | ❺ | 3,3 В | ❼ | 3,3 В
❽ | 5В | ❾ | 3,3 В | ❿ | 1,2 В | ⓫ | 12 В

9.11 Приемочные испытания голой платы

- Вставьте 4-контактный разъем, только что припаянный на плате DK-102_OLED, в J573 платы

MB. Вставьте зарядное устройство (16,8 В) в разъем J21, а затем включите зарядное

устройство. Нажмите SW15. В это время на экране платы DK-102_OLED должно

отображаться следующее изображение. Затем отключите зарядное устройство.

- Подключите плату DK-102_MB к другим платам в соответствии с главой 9.8 и подключите

кабели согласно таблице ниже.

Кабель | Точка на плате DK-102_RX | Доска DK-102_PA
Разъем IPX на обоих концах, 50 Ом, L=200 | J7 | J6
Кабель | Точка на плате DK-102_RX | Оценка доски DK-102_AD_DA
Разъем IPX на обоих концах, 50 Ом, L=100 | J1 | J1
Кабель | Точка платы DK-102_MB | оратор
Вилка с шагом 1,25, 2PIN, несимметричный, L=60 | J7 | +/-полюс
Кабель | DK-102_TUNNINGбон | Точка платы DK-102_MB
Вилка с шагом 1,25, 4-контактная, несимметричная, L=50 | J58 | J572
- Обклейте всю заднюю часть ЖК-экрана высокотемпературной лентой (ленту необходимо

удалить в местах соприкосновения с проводящей пеной) в целях изоляции. Наклейте

проводящую пену на квадратную открытую жестяную поверхность площадью 1,5 см на

ВЕРХНЕЙ поверхности платы MB, как показано ниже.

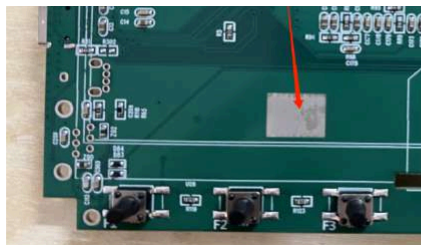
[picture p211: figure]
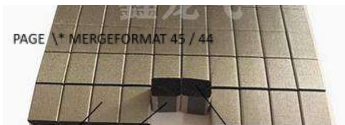
[picture p212: figure]

- Вставьте экран на плату MB (в соответствии с рамкой шелкографии на плате MB), после

завершения подключите кабель FPC экрана к плате MB J19 и J20, как показано ниже.

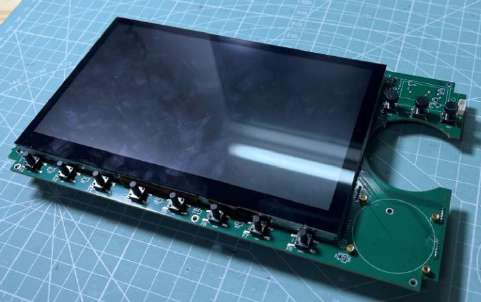
[picture p213: figure]

- Вставьте зарядное устройство (16,8В) в J21, нажмите SW26 для включения (учтите, что

платы нужно изолировать и не закорачивать). В это время должен отобразиться экран и

войти в основной интерфейс, как показано ниже. Из динамика должен раздаваться шорох

(если звука нет, проверьте, установлен ли потенциометр громкости или коэффициент

усиления ПЧ на плате PA на минимум). Каждая кнопка на сенсорном экране должна

реагировать на прикосновение.

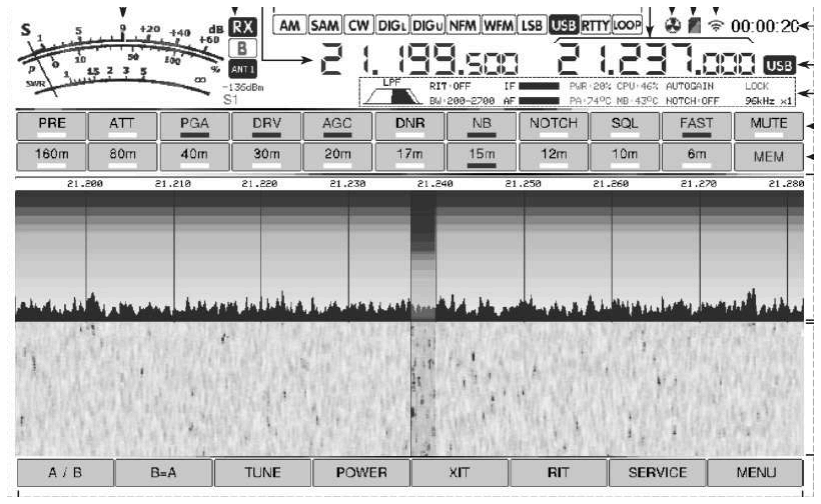
[picture p214: figure]

- Подключите зарядное устройство и нажмите SW26, чтобы включить его, коротко нажмите F8,

чтобы войти в интерфейс меню -> нажмите и удерживайте F8, чтобы войти в меню

калибровки, найдите меню RF-Unit Type (тип платы усилителя мощности) ->Выберите

RU4PN-> Возврат к основному интерфейсу режима ожидания-> Длительное нажатие SW26

для выключения.

- Подключите антенну к интерфейсу BNC на плате DK-102_PA, коротко нажмите SW26, чтобы

включить телефон, войдите в основной интерфейс, коснитесь частоты на экране, нажмите и

удерживайте, чтобы настроить частоту в соответствии с диапазоном FM-вещания и режимом

WFM. В это время вы сможете принимать FM-передачи. Настройтесь на коротковолновый

диапазон и режим AM, и вы сможете принимать коротковолновые передачи. Поверните

энкодер, чтобы отрегулировать частоту приема.

9.12 Тест запуска голой платы

- На основании главы 9.11 также подключите кабели согласно следующей таблице.
Кабель | Точка платы DK-102_MB | Доска DK-102_PA
Красный, силиконовый провод 18AWG, L=80 Черный, силиконовый провод 18AWG, L=80 | J40 J41 | Красный подключается к 13,8 В (J9). Черный подключен к GND (J10)
- Используйте зарядное устройство для питания материнской платы или регулируемый

источник питания (напряжение около 15 В, ток регулируется до <1,5 А).

- передаст прибыль(Следующее меню RF GAIN...) настроено примерно на 15~40. (по

умолчанию 40)

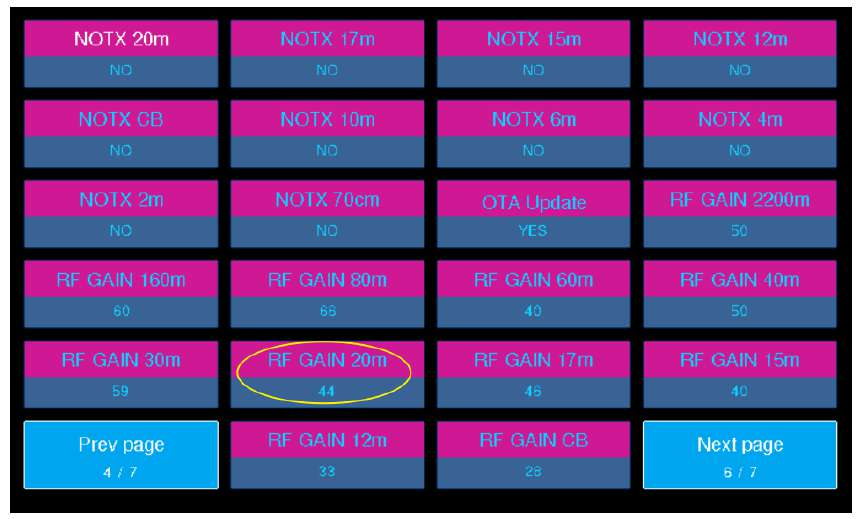
[picture p215: figure]

- Регулировка первичного статического смещения передачи: коснитесь основного интерфейса,

чтобы настроить диапазон 20 м, режим CW или режим SSB -> нажмите кнопку питания или

кнопку передачи ручного микрофона -> измерьте напряжение на контакте 1 R86 -> с

помощью крестовой отвертки отрегулируйте R86 так, чтобы напряжение на контакте 1

составляло около 2,2 В -> замкните U5 оловом -> затем измерьте напряжение на контакте 1

R86, оно должно быть около 2,5 В, а U5 должно быть около 9В. При измерении будьте

осторожны и не касайтесь измерительных проводов другими паяными соединениями.

- Регулировка статического смещения конечного этапа передачи: коснитесь основного

интерфейса, чтобы настроить диапазон 20 м, режим CW или режим SSB -> нажмите кнопку

источника питания или кнопку передачи ручного микрофона -> измерьте напряжение на

контакте 1 R84 и R85 -> используйте крестовую отвертку для регулировки R84 и R85 так,

чтобы напряжение на контакте 1 составляло около 2,27 В (R84 и R85 настроены одинаково и

не могут отличаться слишком сильно) -> короткое замыкание U3/U4 с оловом -> Затем

измерьте напряжение на контакте 1 R84 и R85, оно должно составлять около 2,27 В. U3/U4

должно быть напряжением источника питания. При измерении будьте осторожны и не

касайтесь измерительных проводов другими паяными соединениями.

- Выходная мощность 15 Вт, ложные стандартные эталонные параметры

1） Напряжение смещения: напряжение контакта 1 R86 составляет 2,5 В, напряжение

контакта 1 R85 — 2,25 В, напряжение контакта 1 R84 — 2,28 В (примечание: необходимо

отсоединить кабель, подключенный к J5 платы PA, а затем отрегулировать напряжение

смещения)

2） Усиление каждого диапазона: RF GAIN = 35~63 (разные машины и диапазоны

различаются, требуется отладка одной машины)

3） Другое: Снимите D71, D73 с платы усилителя мощности; R45, R52 с платы АЦП = 560 Ом

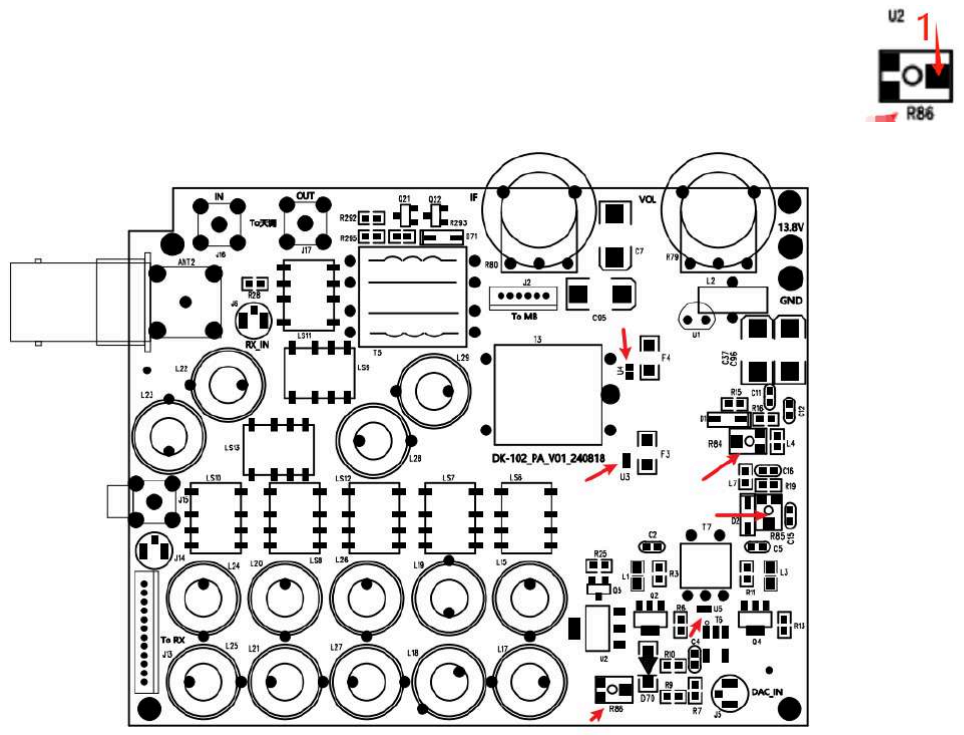
[picture p216: figure]

- Подключите кабели согласно таблице ниже.
Кабель | Оценка доски DK-102_AD_DA | Доска DK-102_PA
Разъем IPX на обоих концах, 50 Ом, L=80 | J15 | J5
- Нажмите F8 в главном интерфейсе, чтобы войти в следующее меню, измените«Мощность

RF» (китайская прошивка — «Мощность передачи») настроена на 50–100., а затем

вернитесь к основному интерфейсу

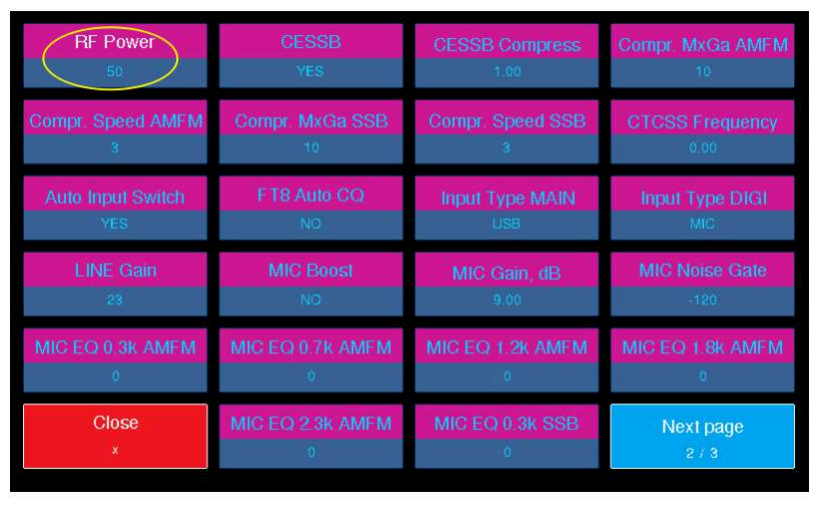
[picture p217: figure]

- Антенный интерфейс BNC подключается к измерителю стоячей волны и эквивалентной

нагрузке 50 Ом и 20 Вт или более. В это время тест передачи должен иметь выходную

мощность около 2 Вт (лучше всего использовать электростанцию для передачи в режиме

CW). Если выходная мощность отсутствует, выходной мощности ЦАП может быть

недостаточно. Вы можете долго нажимать клавишу F8 в интерфейсе главного меню, чтобы

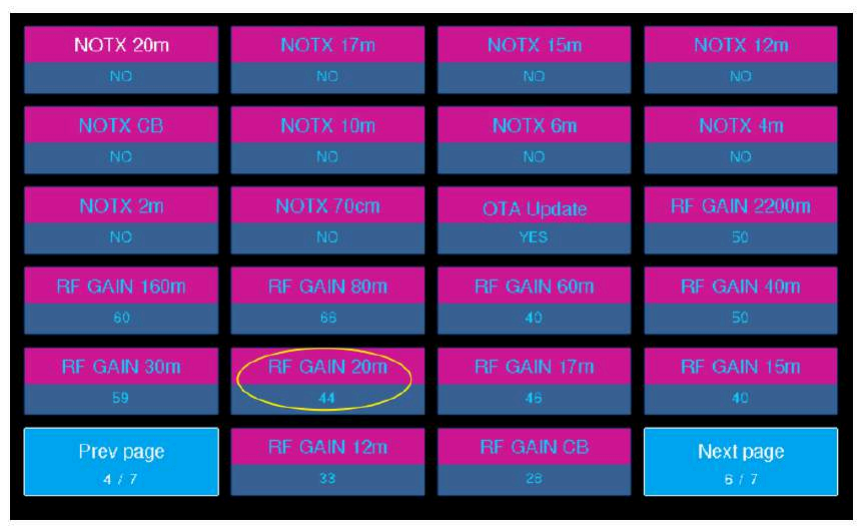
[picture p218: figure]

войти в «Меню калибровки» -> «Усиление RF каждого диапазона», чтобы увеличить

значение усиления (например, 20 м, отрегулируйте усиление RF GAIN на значение 20 м, выберите меню и поверните энкодер, чтобы изменить значение), интерфейс меню выглядит

следующим образом. В меню китайской версии прошивки есть "Усиление RF 20м".

- Увеличьте общий коэффициент передачи SSB. Это меню позволяет увеличить общую

мощность передачи SSB (по сравнению с режимом CW). Меню китайской прошивки - "SSB

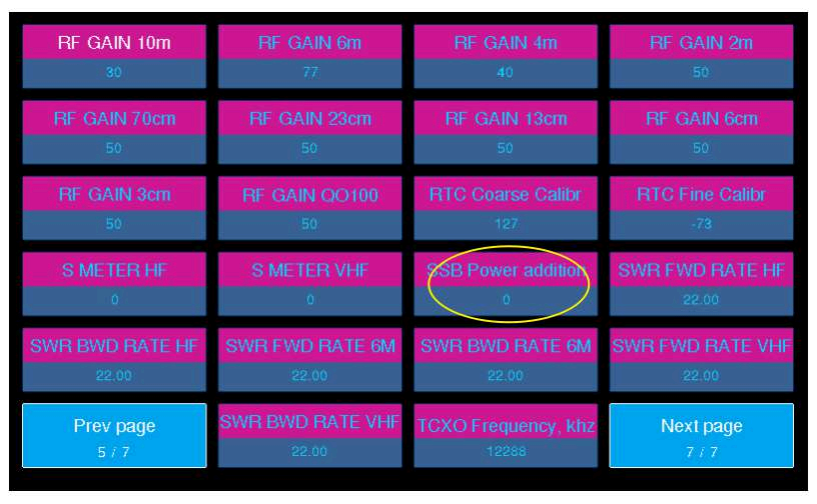
[picture p219: figure]

Power Enhancement". Рекомендуется настроить на максимальное значение.

- Увеличьте ток регулируемого источника питания до 4 А, затем повторите вышеуказанные

шаги, чтобы отрегулировать выходную мощность примерно до 14,9 Вт (если регулируемый

источник питания отсутствует, подождите, пока вся машина будет полностью собрана,

прежде чем приступать к отладке этого шага. Если нет измерителя стоячей волны, вы

можете наблюдать индикацию выходной мощности на экране в качестве справки)

- Отрегулируйте усиление других диапазонов по аналогии так, чтобы выходная мощность

была близка к одинаковой (не настраивайте выходную мощность более чем на 15 Вт, иначе

паразитные помехи превысят стандарт или схема передатчика будет повреждена

перегрузкой по току).

- Обратите внимание, что излучение можно тестировать только периодически в течение

короткого периода времени, поскольку в это время эмиссионная МОП-трубка не имеет

радиатора.

- Выключите передатчик 50М. Поскольку этот трансивер рассчитан только на прием на

расстоянии 50М, передатчик 50М имеет разработанную схему, но она не была отлажена.

Существует высокая вероятность того, что паразитные излучения превысят стандарт,

поэтому выключите передатчик. Если вам интересно, вы можете отладить его

самостоятельно. Метод выключения — установить NOTX 6m, как показано на рисунке ниже,

на ДА. В меню китайской версии прошивки стоит "Не передавать на 6м"

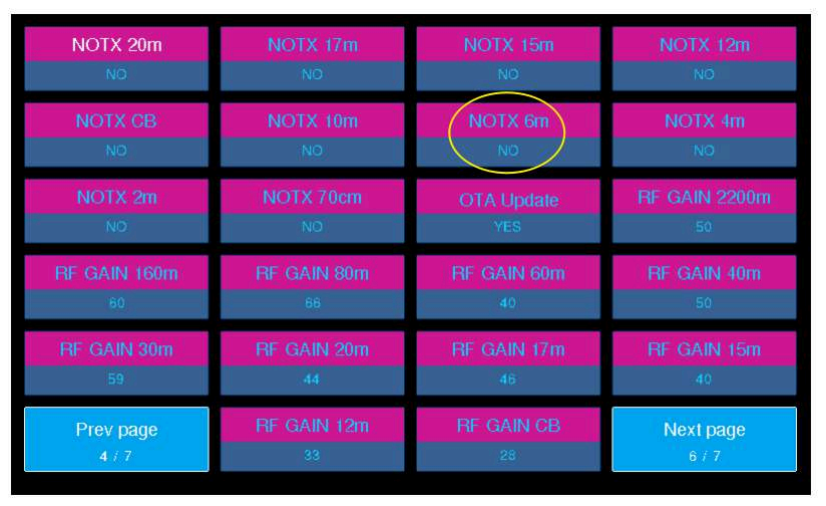
[picture p220: figure]

9.13 Отладка ложных излучений

- Если у вас есть анализатор спектра, вы можете проверить паразитное излучение.

Необходимое оборудование: анализатор спектра, аттенюатор 50 дБ при 20 Вт и

соответствующие перемычки.

- Причин ложного превышения нормы множество. В основном мы фокусируемся на трех

аспектах: напряжении смещения схемы усилителя мощности ВЧ, входной мощности

усилителя мощности ВЧ и выходном фильтре.

1) Напряжение смещения схемы усилителя мощности ВЧ предназначено главным образом

для регулировки значения R86 и значения R84/R85. R86 предназначен для регулировки

напряжения смещения лампы первичного усилителя. R84/R85 предназначен для регулировки напряжения смещения лампы окончательного усилителя. Слишком высокие или слишком низкие

напряжения смещения будут влиять на паразитную и передаваемую мощность. Обратите

внимание: при отладке рекомендуется, чтобы это напряжение не превышало 3,5 В. В противном

случае есть риск прожечь пусковую трубу.

2) Входная мощность усилителя мощности ВЧ предназначена главным образом для

регулировки усиления ВЧ, упомянутого в главе 9.12. Этот сигнал представляет собой

модулированный сигнал, выдаваемый ЦАП. Мощность около 120мВт.

3) Выходной фильтр в основном регулирует увеличение или уменьшение катушки,

намотанной на магнитное кольцо (L18/L19 и т. д. на рисунке ниже), а также регулирует номинал

конденсатора. (C51/C77/C52/C78/C50 и т. д. на рисунке ниже)

4) Поскольку печатная плата имеет паразитную емкость и паразитную индуктивность, а

также емкость, установленную на плате, ошибки магнитного кольца и катушки, эффект фильтра

каждой платы будет разным, поэтому эти параметры необходимо отрегулировать. Попробуйте

различные комбинации регулировок напряжения смещения схемы усилителя мощности ВЧ,

входной мощности усилителя мощности ВЧ и выходного фильтра для достижения показателей

выходной мощности и ложных показателей соответствия.

- На рисунке ниже показана принципиальная схема и номера битов каждой схемы полосового

фильтра. Для справки по отладке

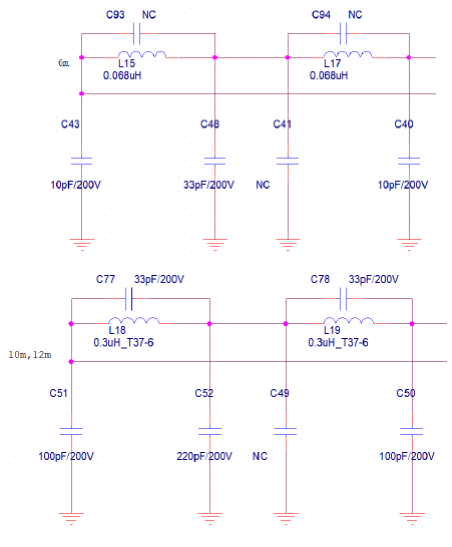
[picture p221: figure]
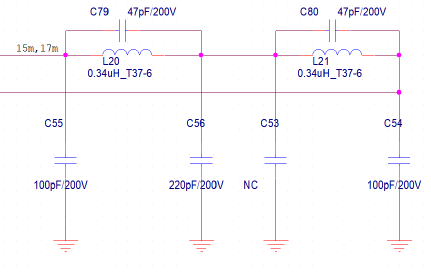
[picture p222: figure]
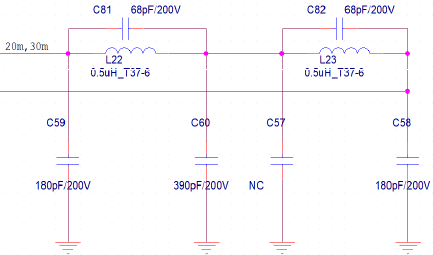
[picture p223: figure]
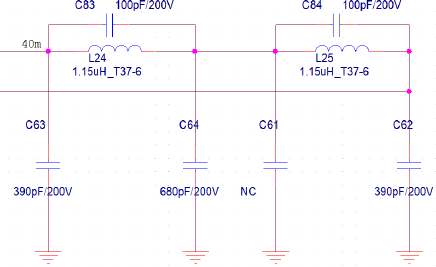
[picture p224: figure]

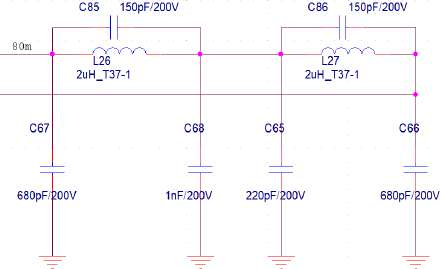
[picture p225: figure]
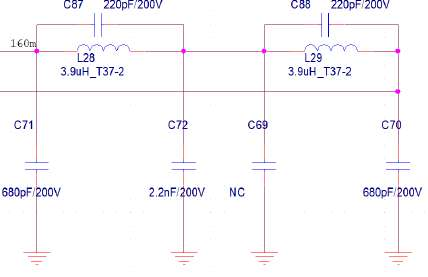
[picture p226: figure]

9.14 Вся сборка машины

1） Разделите кабели между каждой платой во время предыдущего теста, чтобы облегчить

установку в корпус.

2） Установите плату OLED в корпус и зафиксируйте винты. После завершения, как показано

ниже

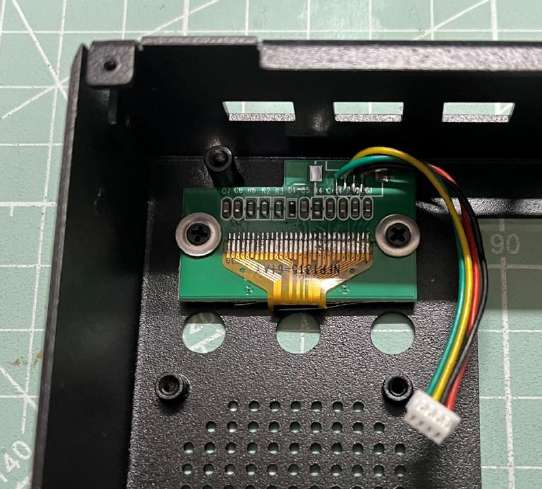
[picture p227: figure]

3） Установите динамик в корпус и зафиксируйте винты. Процесс завершения показан ниже.

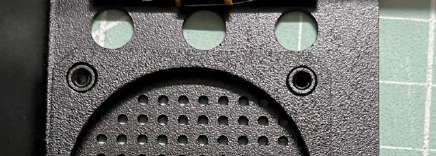
[picture p228: figure]

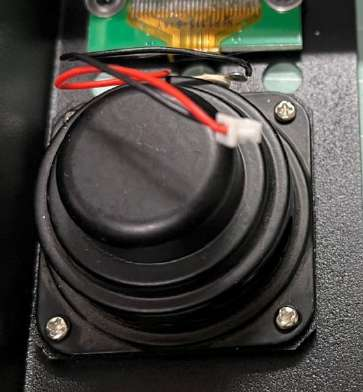
[picture p229: figure]

4） Установите плату энкодера на плату MB и подключите кабель, соединяющий энкодер с

платой MB. Процесс завершения показан ниже.

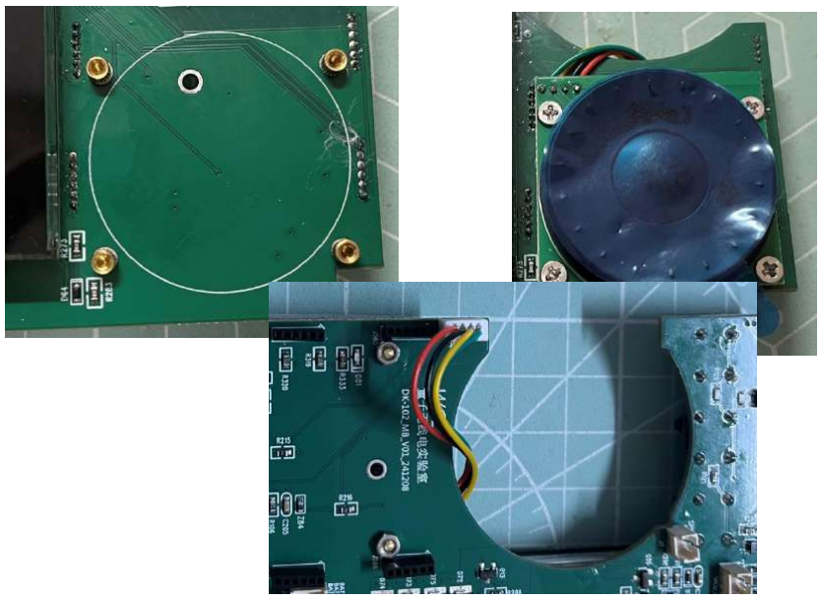
[picture p230: figure]

5） Установите плату DK-102_MB в корпус и зафиксируйте винтами. (Обратите внимание, что

кабели, соединяющие плату OLED и плату DK-102_MB, должны быть подключены правильно, а

кабели динамиков должны быть подключены.) Процесс завершения показан ниже.

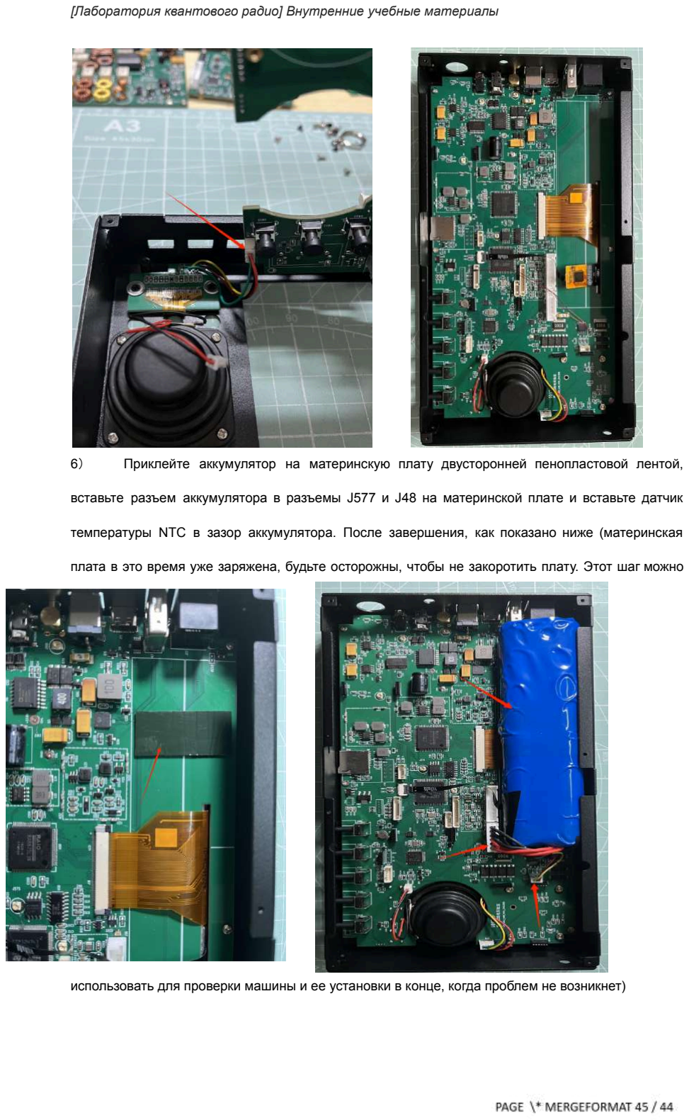
[picture p231: page 45]

6） Приклейте аккумулятор на материнскую плату двусторонней пенопластовой лентой,

вставьте разъем аккумулятора в разъемы J577 и J48 на материнской плате и вставьте датчик

температуры NTC в зазор аккумулятора. После завершения, как показано ниже (материнская

плата в это время уже заряжена, будьте осторожны, чтобы не закоротить плату. Этот шаг можно

использовать для проверки машины и ее установки в конце, когда проблем не возникнет)

7） Зафиксируйте шпильки в четырех углах платы DK-102_PA и подключите кабели. После

завершения, как показано ниже

8） Установите плату DK-102_PA в корпус (Рекомендуется наклеить на C38 и C39 платы MB

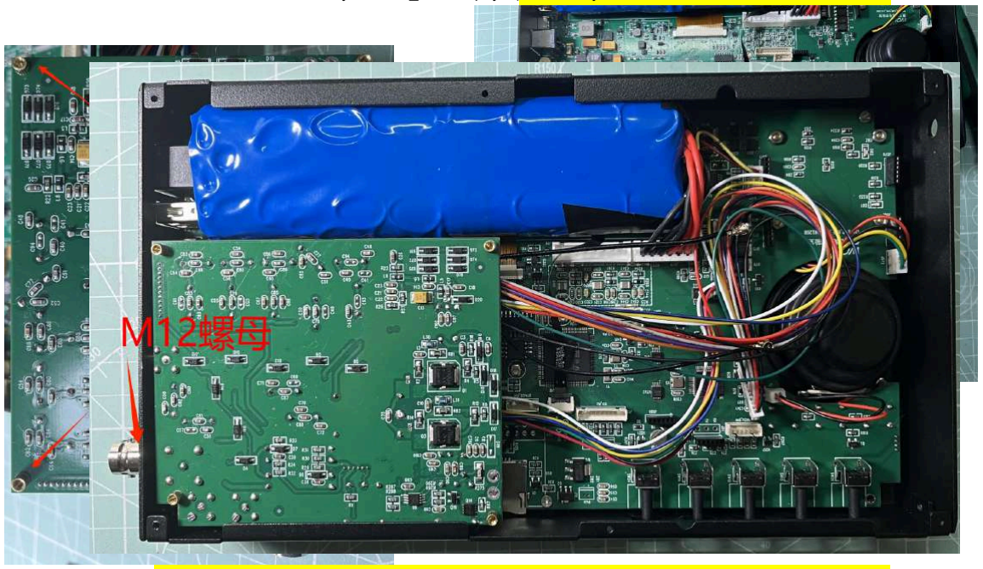
[picture p232: figure]

кусок высокотемпературной ленты для предотвращения короткого замыкания между разъемом

BNC платы DK-102_PA и C38.), зафиксируйте гайку гнезда BNC и вставьте кабель между платой

PA и платой MB. После завершения, как показано ниже

9） Зафиксируйте шпильки в четырех углах платы DK-102_AD_DA и подключите кабели.

После завершения, как показано ниже

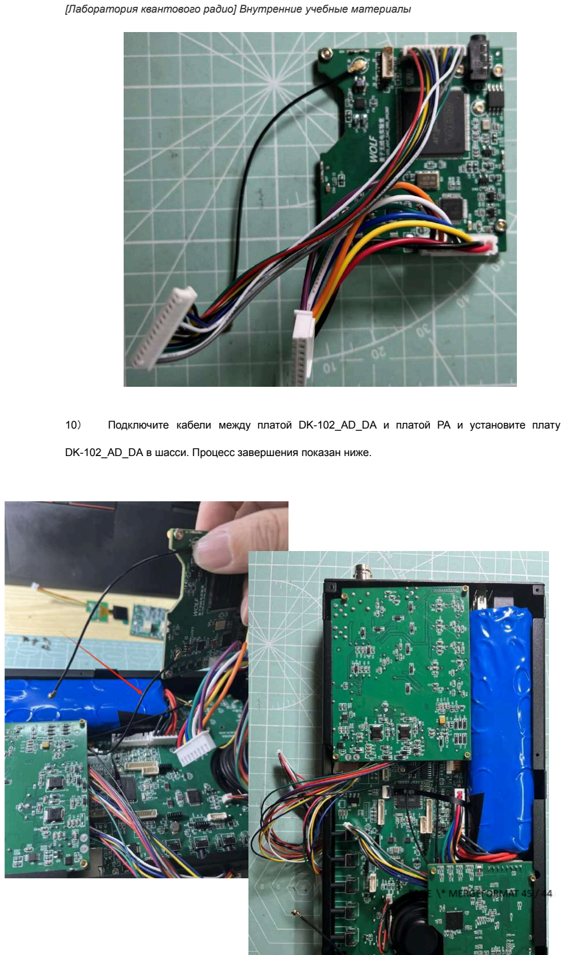
[picture p233: page 47]

10） Подключите кабели между платой DK-102_AD_DA и платой PA и установите плату

DK-102_AD_DA в шасси. Процесс завершения показан ниже.

11） Прикрепите плату DK-102_PA и плату AD_DA к термопрокладкам. После завершения

прикрепите аккумулятор к теплоизоляционной прокладке (для фиксации можно использовать

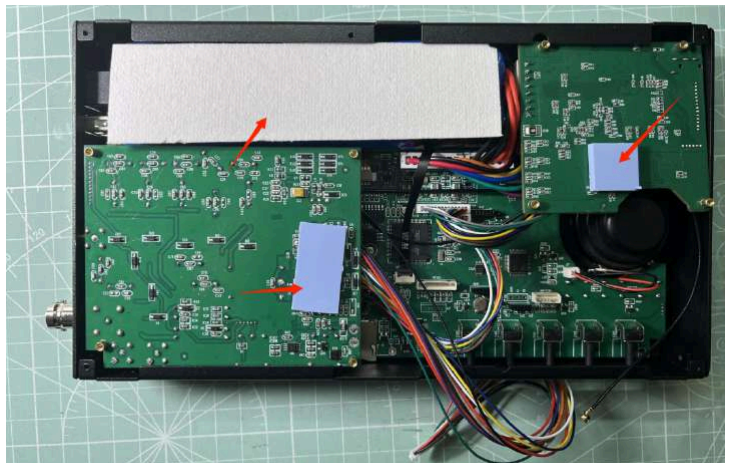
[picture p234: figure]

высокотемпературную ленту), как показано ниже.

12） Термопрокладка на рисунке выше менее эффективна и может быть заменена

«теплопроводящим силиконовым листом из нитрида алюминия мощностью 18,6 Вт» ниже. Если

его не

заменить,

летом

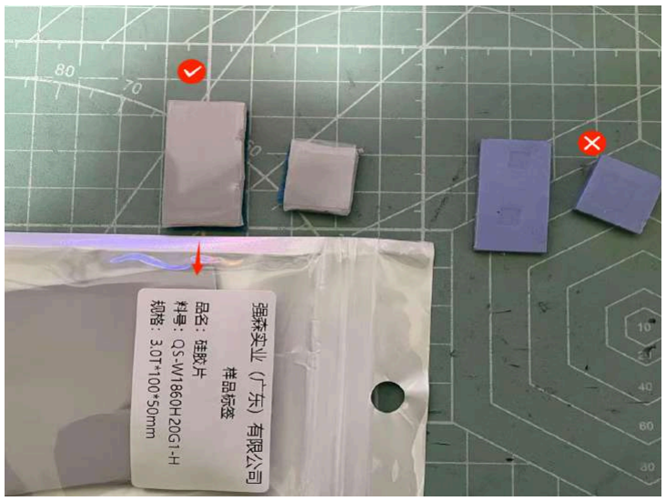
[picture p235: figure]

рассеивание тепла может быть плохим. Термопрокладка слева работает намного лучше.

(Обратите внимание, что площадь термопрокладки, прикрепленной к плате АЦП, после ее

замены на термопрокладку, расположенную ниже, не должна быть слишком большой.

Термопрокладка не может соприкасаться с резисторами и конденсаторами рядом с микросхемой,

иначе возникнет риск появления помех при приеме сигналов. Для изоляции устройств вокруг

микросхемы АЦП можно использовать высокотемпературную ленту)

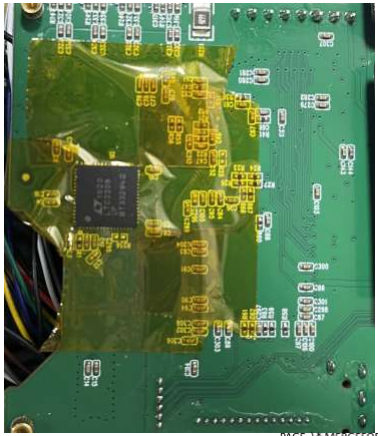
[picture p236: figure]
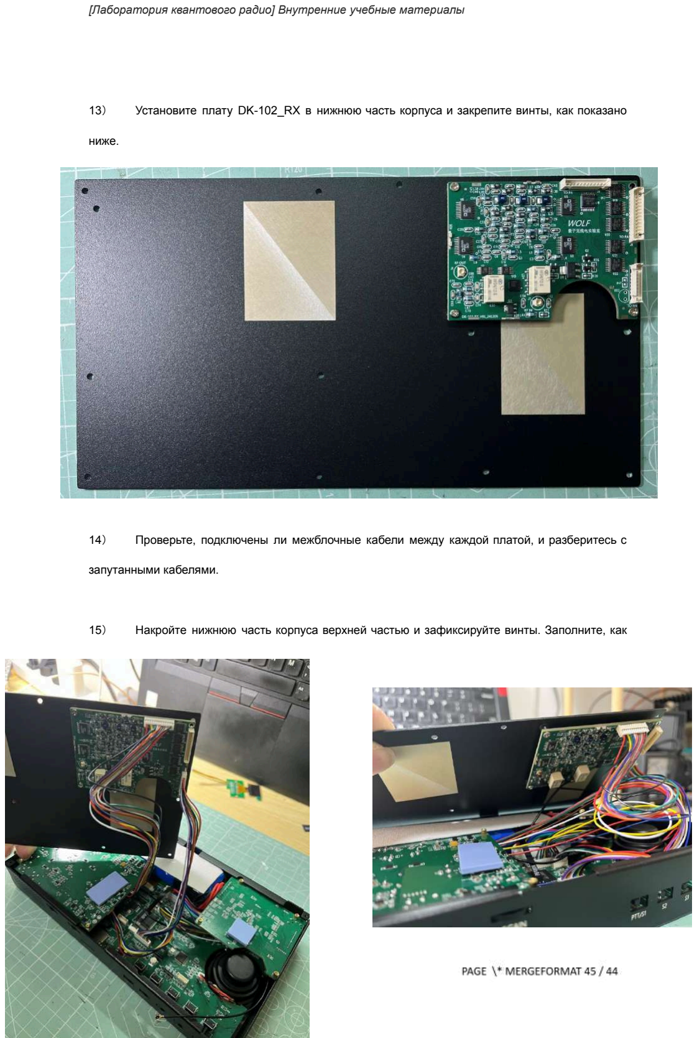
[picture p237: page 50]

13） Установите плату DK-102_RX в нижнюю часть корпуса и закрепите винты, как показано

ниже.

14） Проверьте, подключены ли межблочные кабели между каждой платой, и разберитесь с

запутанными кабелями.

15） Накройте нижнюю часть корпуса верхней частью и зафиксируйте винты. Заполните, как показано ниже (Обратите внимание, что винты в нижней части корпуса рядом с сердечником

батареи должны быть короткими. Длинные винты могут задеть сердцевину аккумулятора.）

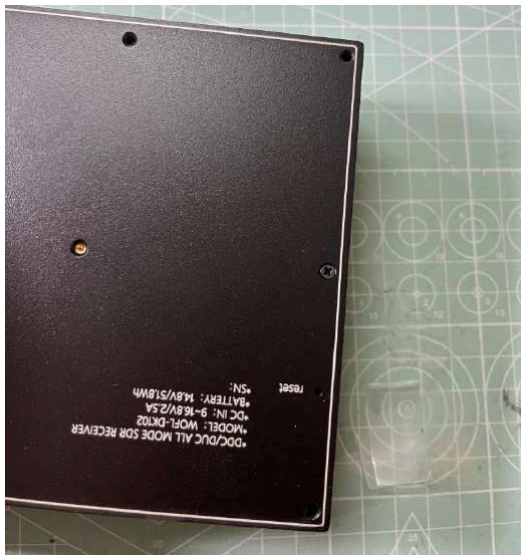
[picture p238: figure]

16） Установите верхний колпачок клавиатуры и колпачок клавиатуры на передней панели.

Заполните, как показано ниже

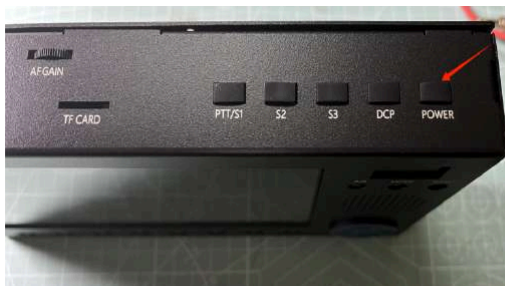
[picture p239: figure]

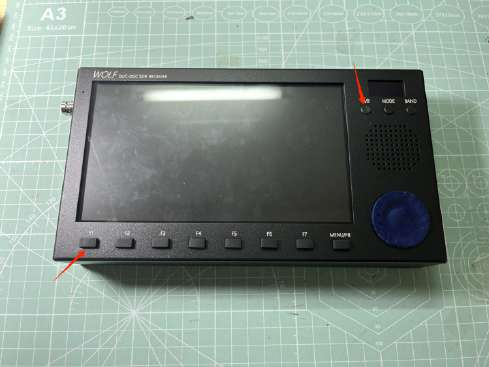
[picture p240: figure]

9.15 Тест всей машины

- Проверьте, нормальна ли функция приема
- Проверьте, нормальна ли функция передачи
- Проверьте, нормально ли работает интерфейс внешнего динамика
- Проверьте, нормальная ли зарядка
- Проверьте, нормально ли отображается OLED-экран.
- Проверьте, нормально ли работают все ручки.

9.16 Краткое изложение мер предосторожности и вопросов при сборке

- Коротковолновый прием должен питаться от батареек. Нельзя использовать прилагаемое

зарядное устройство, иначе зарядное устройство будет создавать слишком сильные помехи,

и сигнал не будет принят.

- По умолчанию передача отключена. Если вы хотите протестировать запуск, прикрепленный

экран в правом верхнем углу устройства необходимо настроить в режим трансивера.

- Как отличить эти два магнитных кольца с двумя отверстиями, которые выглядят одинаково?

Более шероховатую поверхность приваривают к Т5, а более гладкую – к Т3.

- Если вы не можете получить сигнал, убедитесь, что тип платы усилителя мощности выбран

правильно в соответствии со страницей 24 руководства.

- Чтобы настроить время, войдите в меню настройки времени, используйте волновое колесо,

чтобы выбрать положение, и удерживайте верхние кнопки S2 и S3, чтобы настроить время.

- Как именно работают резистивные летающие провода? См. рисунок в главе 9.6. Текстовое

описание такое: Один конец L33 подключен к двум резисторам 2,2К, а другие концы двух

резисторов подключены к контактам 23 и 24 микросхемы U4 соответственно.

- Каково направление вращения D70 платы PA после завершения? После завершения

положительный полюс D70 обращен к R9, и это правильно.

- U23 в плате RX паять не нужно.
- Аккумулятор нельзя заряжать или разряжать. Проверьте, хорошо ли приварен резистор NTC.
- Перед установкой материнской платы необходимо удалить край процесса.
- При подключении наушников звук есть, но в динамиках на фюзеляже звука нет. Проверьте,

плохой ли контакт внутренней шрапнели J4. Левая и правая ножки хвостовой части J4

должны быть соединены.

- Белый экран, проверьте, нормально ли питание J9 на плате АЦП (есть шелковый экран для

отображения значения напряжения), проверьте, хорошо ли сварены C322, C323 и C316

платы MB, хорошо ли сварены C316 платы АЦП и правильно ли подключены J575 и J576

платы MB к плате АЦП.

- Запуск очень медленный. Проверьте, припаян ли U18 и закорочен между контактами.

Проверьте, хорошо ли подключены J575 и J576 платы MB к плате АЦП.

- На плате АЦП нет напряжения 12В. Проверьте, припаян ли проходной конденсатор С323

платы MB. Если напряжения нет, проверьте, припаян ли проходной конденсатор.

- Главный экран белый, и через несколько секунд экран мигает. Плата АЦП работает

неправильно, или FPGA (U16) не записала прошивку.

- Не затягивайте винты на плате OLED слишком сильно, в противном случае экран OLED

будет легко подвергаться нагрузке, что приведет к обесцвечиванию отражающего света или

растрескиванию экрана при выключении.

- При передаче нет питания. Проверьте, не повреждены ли Q1 и Q3 платы PA. Сопротивление

между GS должно быть больше 1 кОм, а сопротивление между DS должно быть больше 2

кОм. Проверьте, имеют ли U3 и U4 напряжение более 13,8 В, имеет ли U5 напряжение около

9 В во время передачи, правильно ли подключен кабель, соединенный с платой PA, и

слышен ли звук реле при переключении разных диапазонов при приеме. Хорошо ли сварено

каждое магнитное кольцо

- Т5 может быть намотан проволокой.
- Если качество звука ухудшится через 2 минуты приема, прикрепите U2 платы АЦП к

термопрокладке и корпусу для отвода тепла или замените его термопрокладкой с более

высокой теплопроводностью.

- Напряжение, отображаемое на прикрепленном экране, является неточным, поскольку

сердечник батареи не подключен. После подключения аккумуляторной батареи для

активации прикрепленный экран необходимо перевести в режим зарядки.

- Компьютер не может подключиться к радио, а подключенный экран необходимо настроить в

режим PC SDR.

- В источнике питания произошло короткое замыкание. Рекомендуется проверить защитную

крышку, особенно защитную крышку рядом с J56.

- Эффект приема FM плохой. Не используйте антенну, резонирующую в коротковолновом

диапазоне. В качестве антенны можно использовать стержень или провод, либо отключить

экранирующий слой фидера в коротковолновой антенне.

- Неисправности энкодера вызывают скачки во время регулировки частоты. Очистите энкодер.
- После включения область спектра в главном интерфейсе становится черной. Войдите в

меню заводских настроек машины -> Сбросьте настройки машины.

- При загрузке выдает сообщение, что версия FPGA неправильная. Проверьте, правильно ли

подключен многожильный кабель между платой ADC и платой MB, или переверните кабель и

вставьте его.

- Время неточное после выключения на ночь. Причина в том, что суперконденсатор Y6 на

плате МБ имеет недостаточную емкость. Его можно заменить аккумуляторной батареей для

часов модели ML414H-IV01E.

- Вы можете найти меню самотестирования в меню аппарата, чтобы проверить аппарат на

наличие сообщений об ошибках, или подключить его к компьютеру и распечатать

информацию о запуске аппарата на терминале последовательного порта компьютера,

которая содержит сообщения об ошибках.

- Машина плохо отводит тепло. Вы можете попробовать следующие 3 метода улучшения:
1) Метод замены термопрокладки. Замените термопрокладку в комплекте на теплопроводящий

силиконовый листовой нитрид алюминия 18,6 Вт (см. стр. 37). Измеренный эффект улучшения очень очевиден. Летом это может в основном удовлетворить рассеивание тепла машины.

Преимущество этого метода в том, что он прост в эксплуатации. Справочный производитель

закупок (Taobao) выглядит следующим образом:

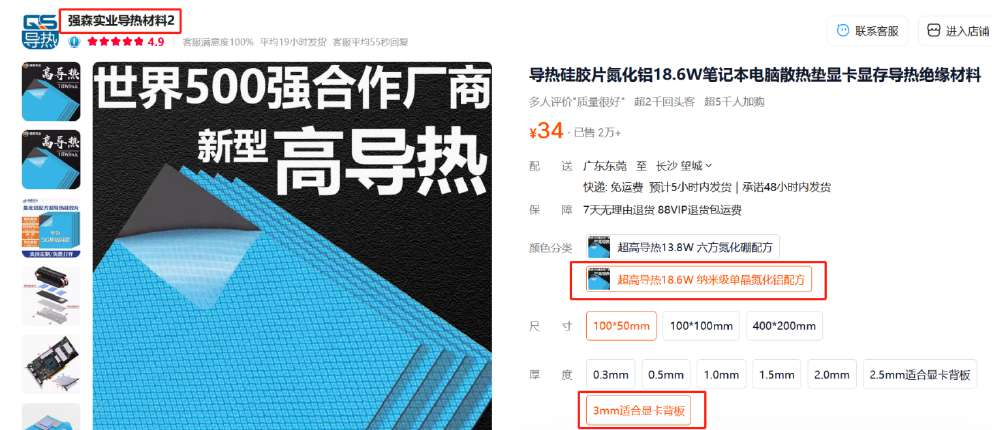
[picture p241: figure]

2) Добавьте метод медного радиатора. Добавьте кусок меди между последней трубкой MOS и

объединительной платой из алюминиевого сплава и нанесите термопасту или термопрокладку

(рекомендуется лист силикагеля из нитрида алюминия мощностью 18,6 Вт) в контактный зазор.

Максимальный доступный размер — медь 50*130 мм*1,4 мм.

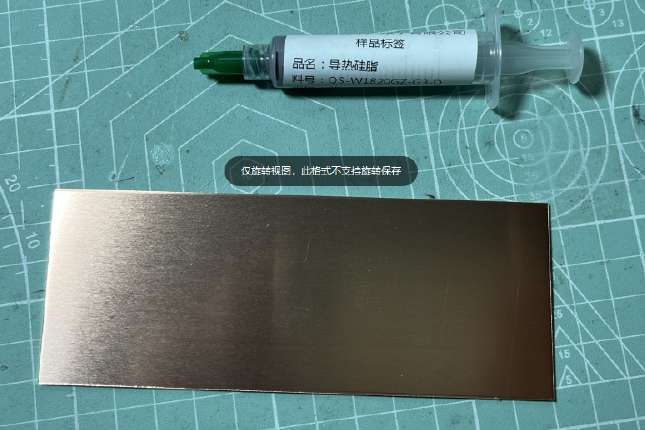
[picture p242: figure]

3） Метод увеличения высоты МОП-трубки. Поднимите последнюю МОП-трубку так, чтобы

она соприкасалась с нижней пластиной из алюминиевого сплава для отвода тепла, и нанесите

термосиликоновую смазку или термопрокладку (рекомендуется лист силикагеля из нитрида

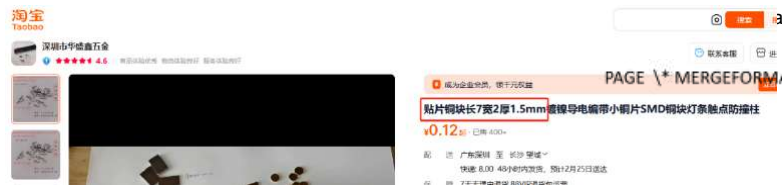
[picture p243: figure]

алюминия мощностью 18,6 Вт) в контактный зазор. Вы можете поместить два конденсатора 0805

(или металлический контактный лист батареи толщиной 1,5 мм) между трубкой MOS и печатной

платой, а затем с помощью термофена приварить трубку MOS и припаять ее. Затем с помощью

паяльника заполните припоем зазор между MOS-трубками. Плюсами этого метода являются

хороший отвод тепла и низкая стоимость. Недостаток – сложность операции.

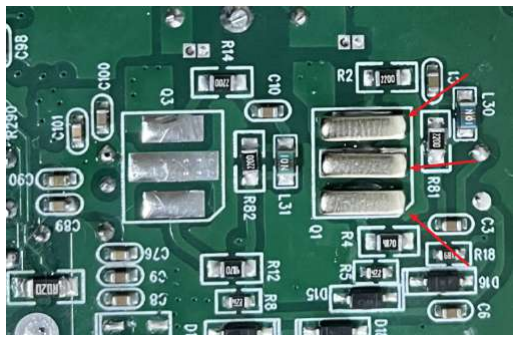
[picture p244: figure]
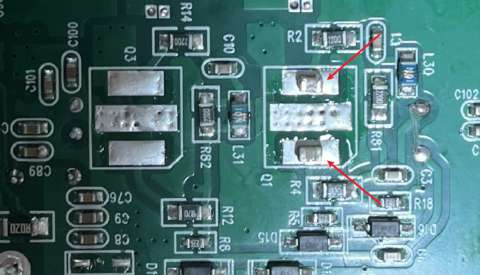
[picture p245: figure]
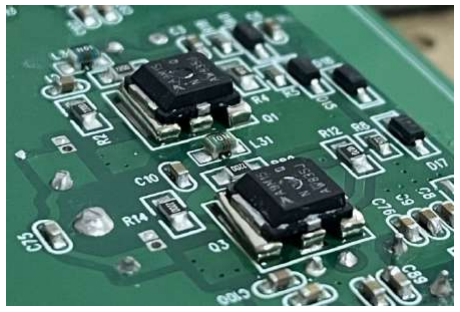
[picture p246: figure]

4) Фактическое тестовое сравнение нескольких методов оптимизации (комнатная температура 12 градусов, непрерывная передача в диапазоне 20 метров, сигнал тревоги при высокой

температуре 80 градусов Цельсия)

метод | модель | Выходная мощность | Продолжительность (секунды) | Примечание
Медный радиатор (50*130*1,5 мм) | CW продолжает передачу | 22 Вт | 55 лет | Нанесите теплопроводящую силиконовую смазку и установите тесный контакт.
Лист силикона из нитрида алюминия | CW продолжает передачу | 22 Вт | 200 с | Сожмите термопрокладку до 1,4 мм.
Увеличенная трубка MOS (силиконовый лист из нитрида алюминия) | CW продолжает передачу | 22 Вт | 230 с | Сожмите термопрокладку до 0,1 мм.
Прокладка трубки MOS (теплопроводящая силиконовая смазка) | CW продолжает передачу | 22 Вт | 60-е годы | Нанесите теплопроводящую силиконовую смазку и установите тесный контакт.

Таким образом, теоретически эффект термопасты должен быть лучше, чем у термопрокладок, но этот эксперимент показывает, что лучшим решением является раствор прокладки для трубок MOS (силиконовый лист из нитрида алюминия). Решение о прямой замене силиконового листа из нитрида алюминия является наиболее удобным и дает лучшие результаты.
4） Несколько дней спустя было протестировано другое решение по отводу тепла. Решение

заключалось в том, чтобы перевернуть трубку MOS и приварить ее, а затем использовать лист

силикона из нитрида алюминия толщиной 3 мм в качестве прокладки между выводами MOS и

объединительной платой корпуса. В реальных испытаниях этот эффект оказался лучше, чем

описанное выше решение, и его было легко реализовать. Чтобы снять трубку MOS, вы можете

использовать тепловую пушку или два паяльника. На рисунке ниже для справки показан готовый

снимок после переворачивания и сварки МОП-трубки. Результаты измерений этого решения на

открытом воздухе следующие: мощность передачи составляет 22 Вт. Режим CW имитирует связь

и осуществляет непрерывную передачу. Основной интерфейс отображает максимальную температуру PA 59 градусов Цельсия. Максимальная температура в МБ составляет 59 градусов

Цельсия. Прием нормальный. Аккумулятор разряжается через 107 минут после полной зарядки.

За все время работы машины не было никаких отклонений. Тело заметно горячее, но держать его

можно долго. Условия тестирования: на открытом воздухе, температура 27 градусов по Цельсию,

солнечно, машина подвергается воздействию прямых солнечных лучей.

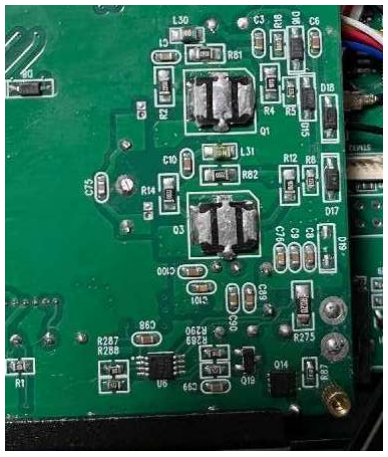
[picture p247: figure]
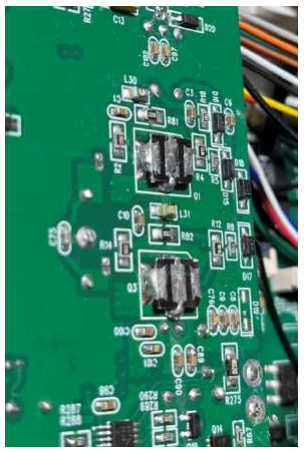
[picture p248: figure]

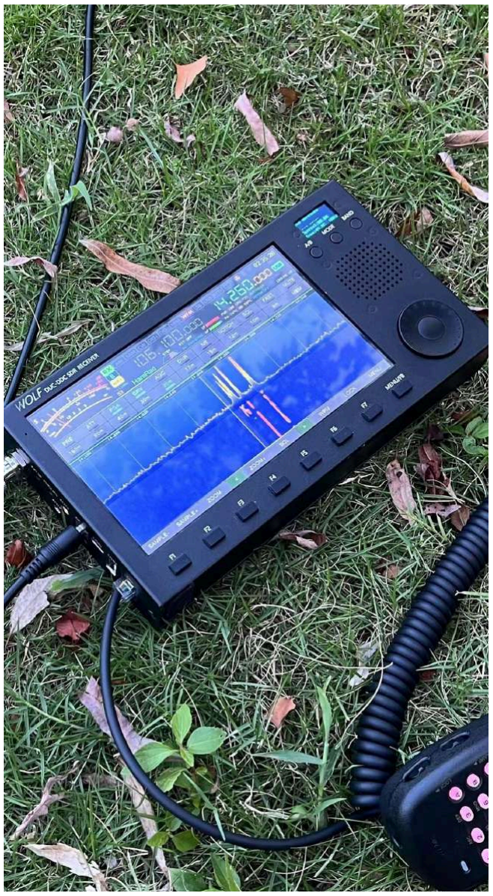
[picture p249: figure]

Как любитель радио, я искал более легкое и гибкое оборудование, чтобы лучше понять удовольствие от уличного радио. Веселое, интересное, познавательное и недорогое любительское радио своими руками! Лаборатория квантового радио 2025.03.21
