XGudron/UA3REO-DDC-Transceiver/Stuff/Manuals/External.png

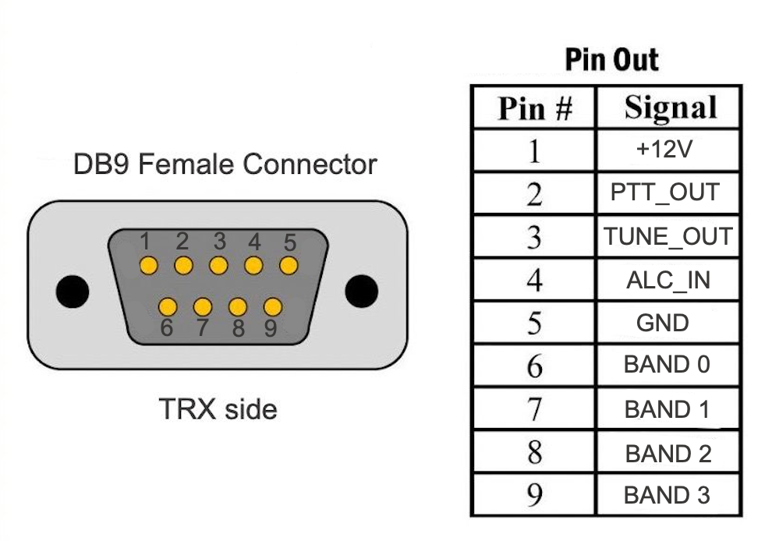
Stuff/Manuals/External.png
