XGudron/UA3REO-DDC-Transceiver/Stuff/Manuals/Infographics/rx_agc_parameters.png

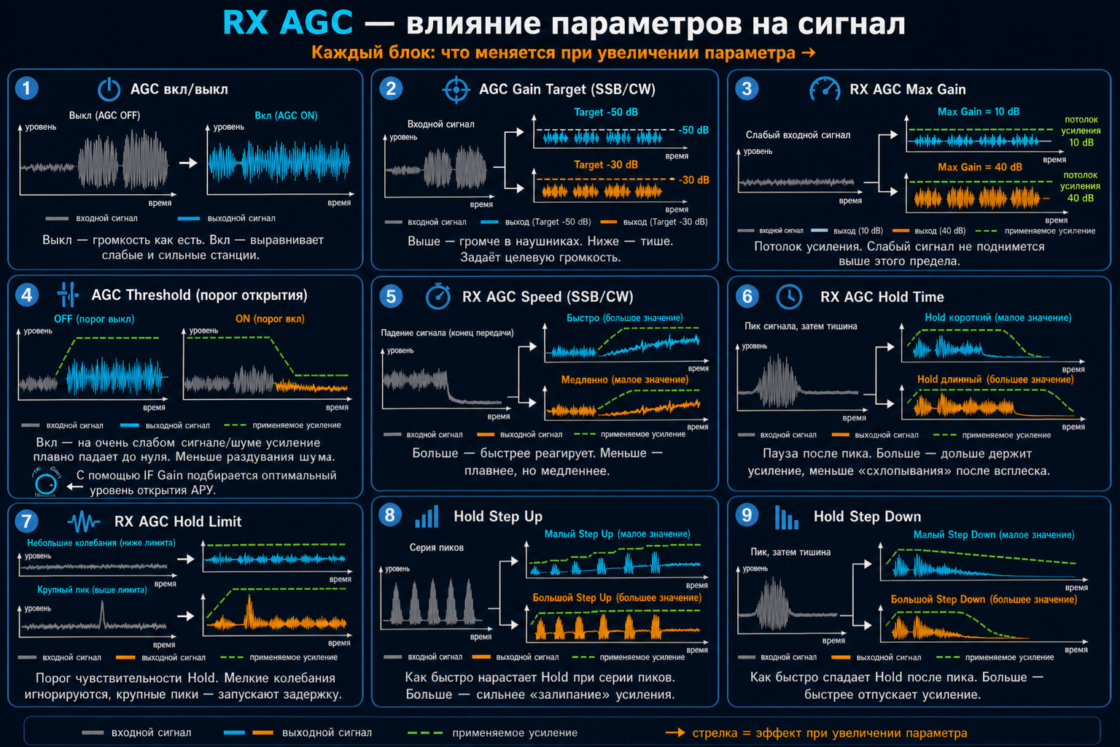
Stuff/Manuals/Infographics/rx_agc_parameters.png
