XGudron/UA3REO-DDC-Transceiver/Stuff/Manuals/Infographics/rx_agc_tips.png

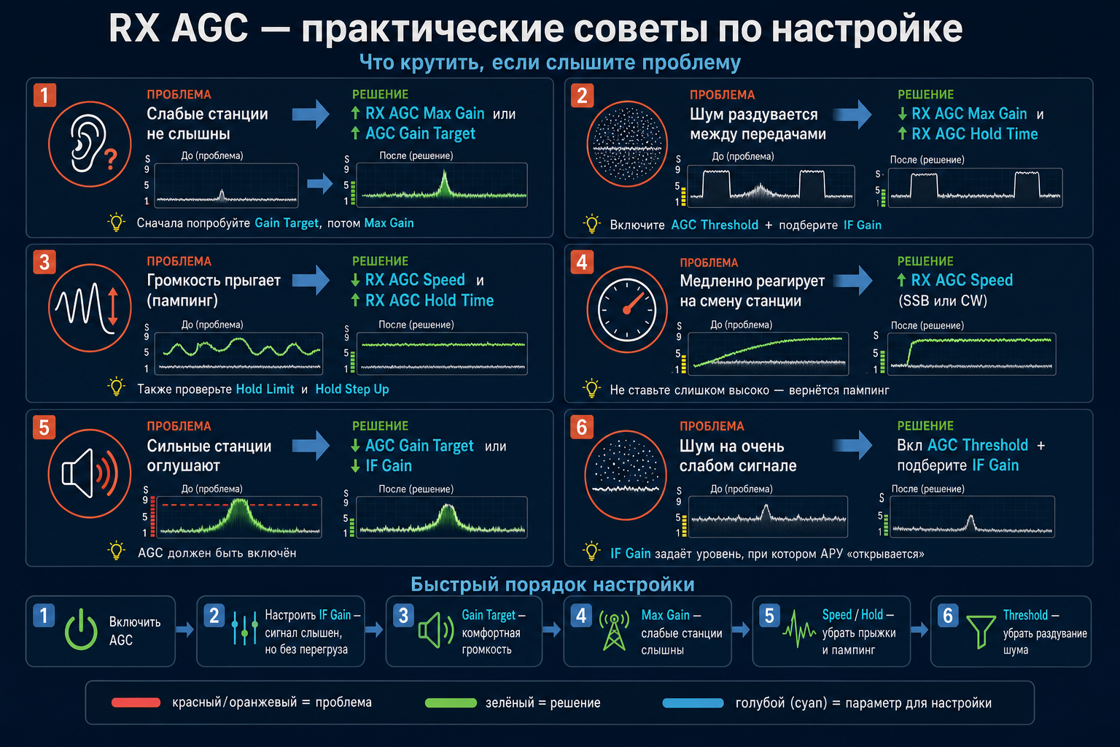
Stuff/Manuals/Infographics/rx_agc_tips.png
