XGudron/UA3REO-DDC-Transceiver/Stuff/Manuals/Infographics/tx_agc_parameters.png

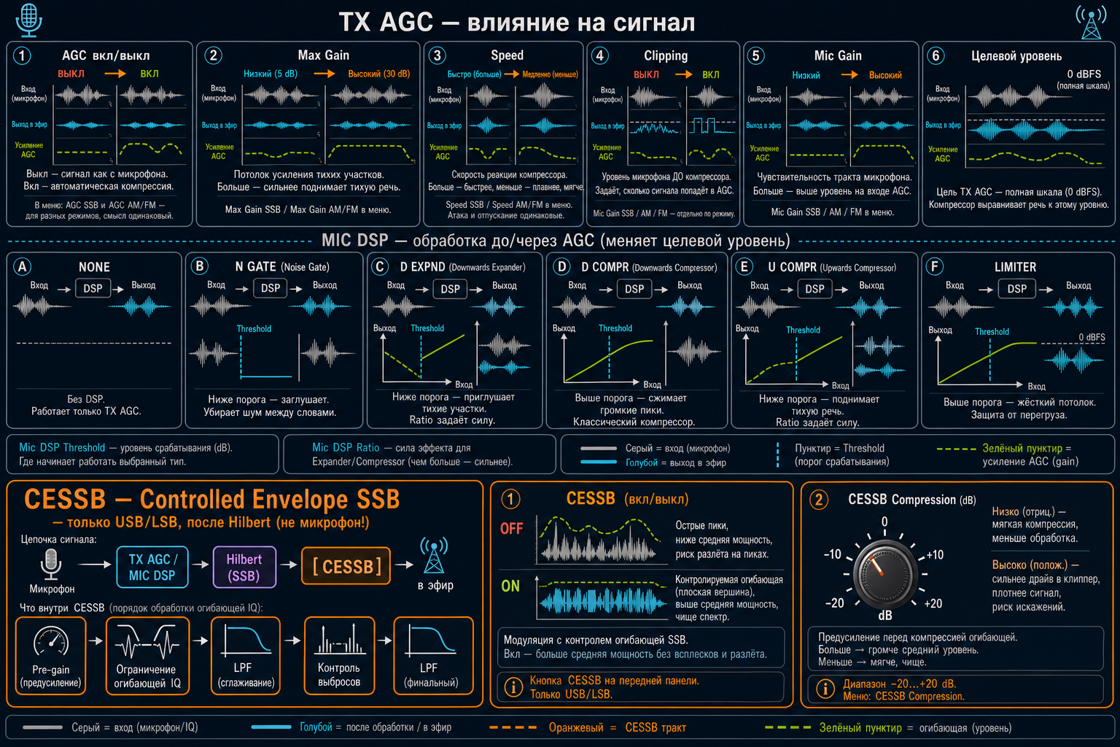
Stuff/Manuals/Infographics/tx_agc_parameters.png
