XGudron/UA3REO-DDC-Transceiver/Stuff/Manuals/Infographics/tx_agc_tips.png

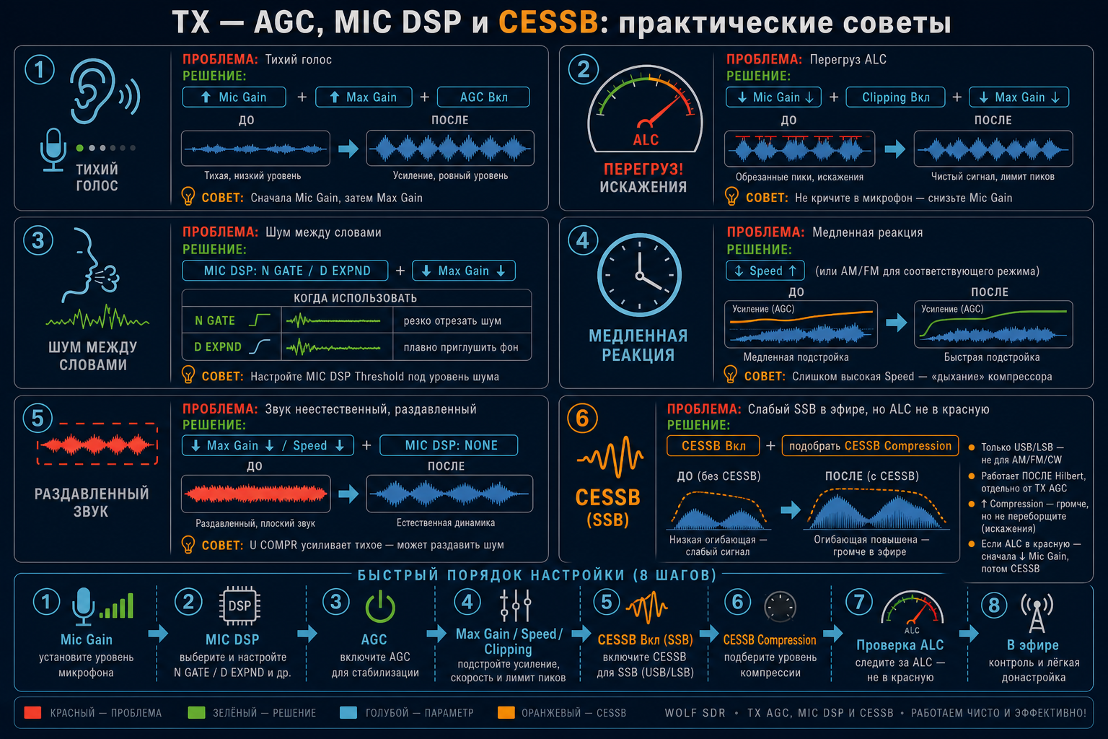
Stuff/Manuals/Infographics/tx_agc_tips.png
