XGudron/UA3REO-DDC-Transceiver/Stuff/Manuals/tangent-mh48-wolf.jpg

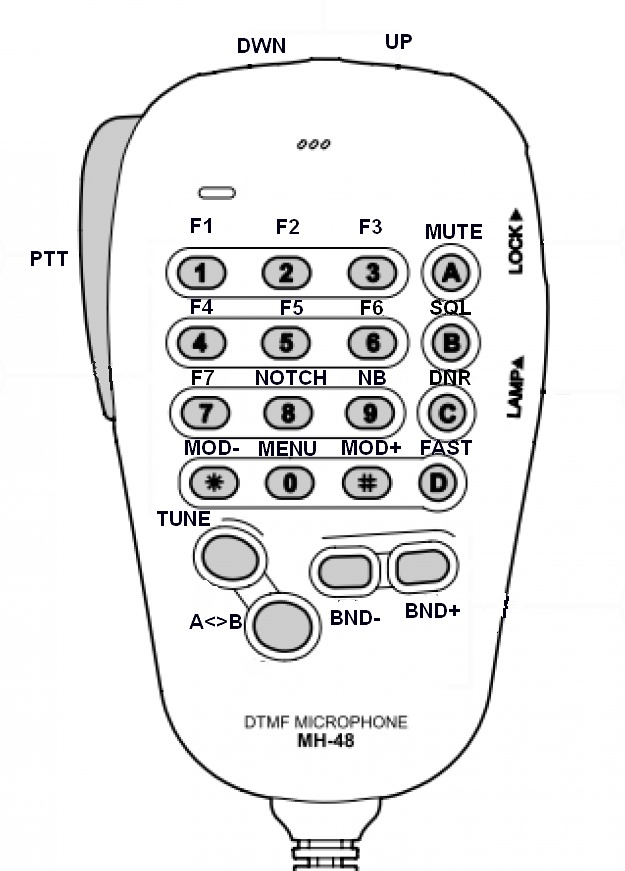
Stuff/Manuals/tangent-mh48-wolf.jpg
