XGudron/UA3REO-DDC-Transceiver/Schematic/Wolf-BA7LJL/Scheme/SCH_Main_Unit.pdf

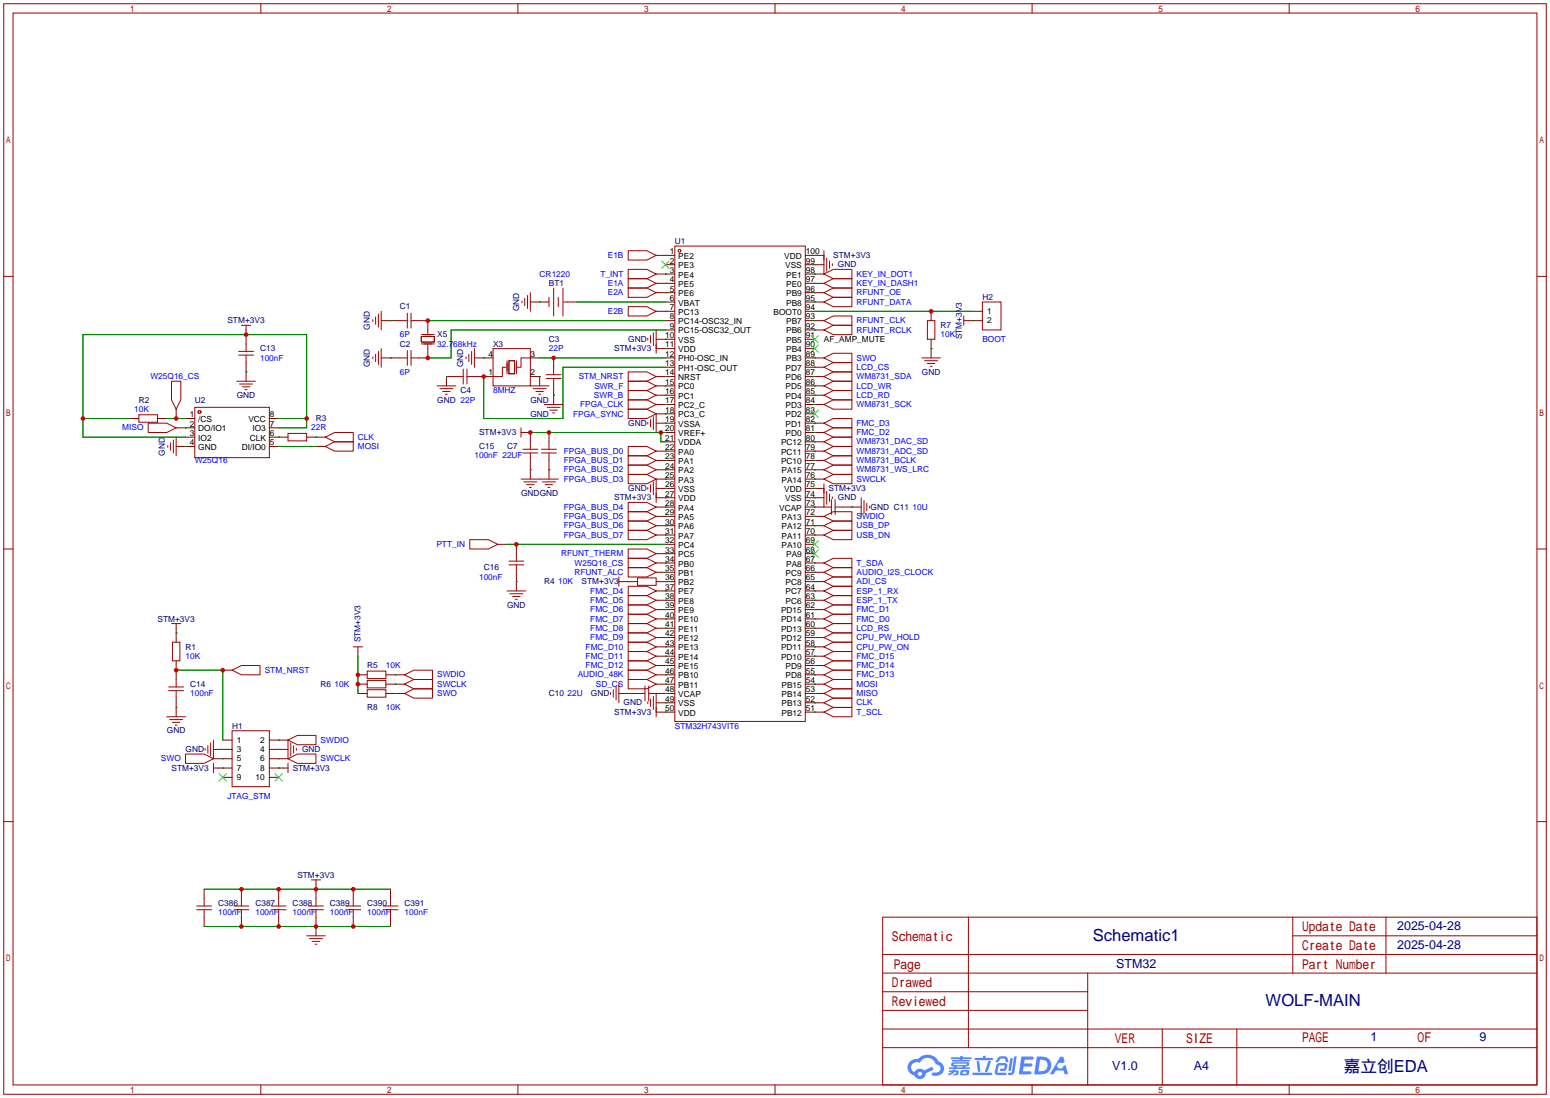
[picture p334: page 1]

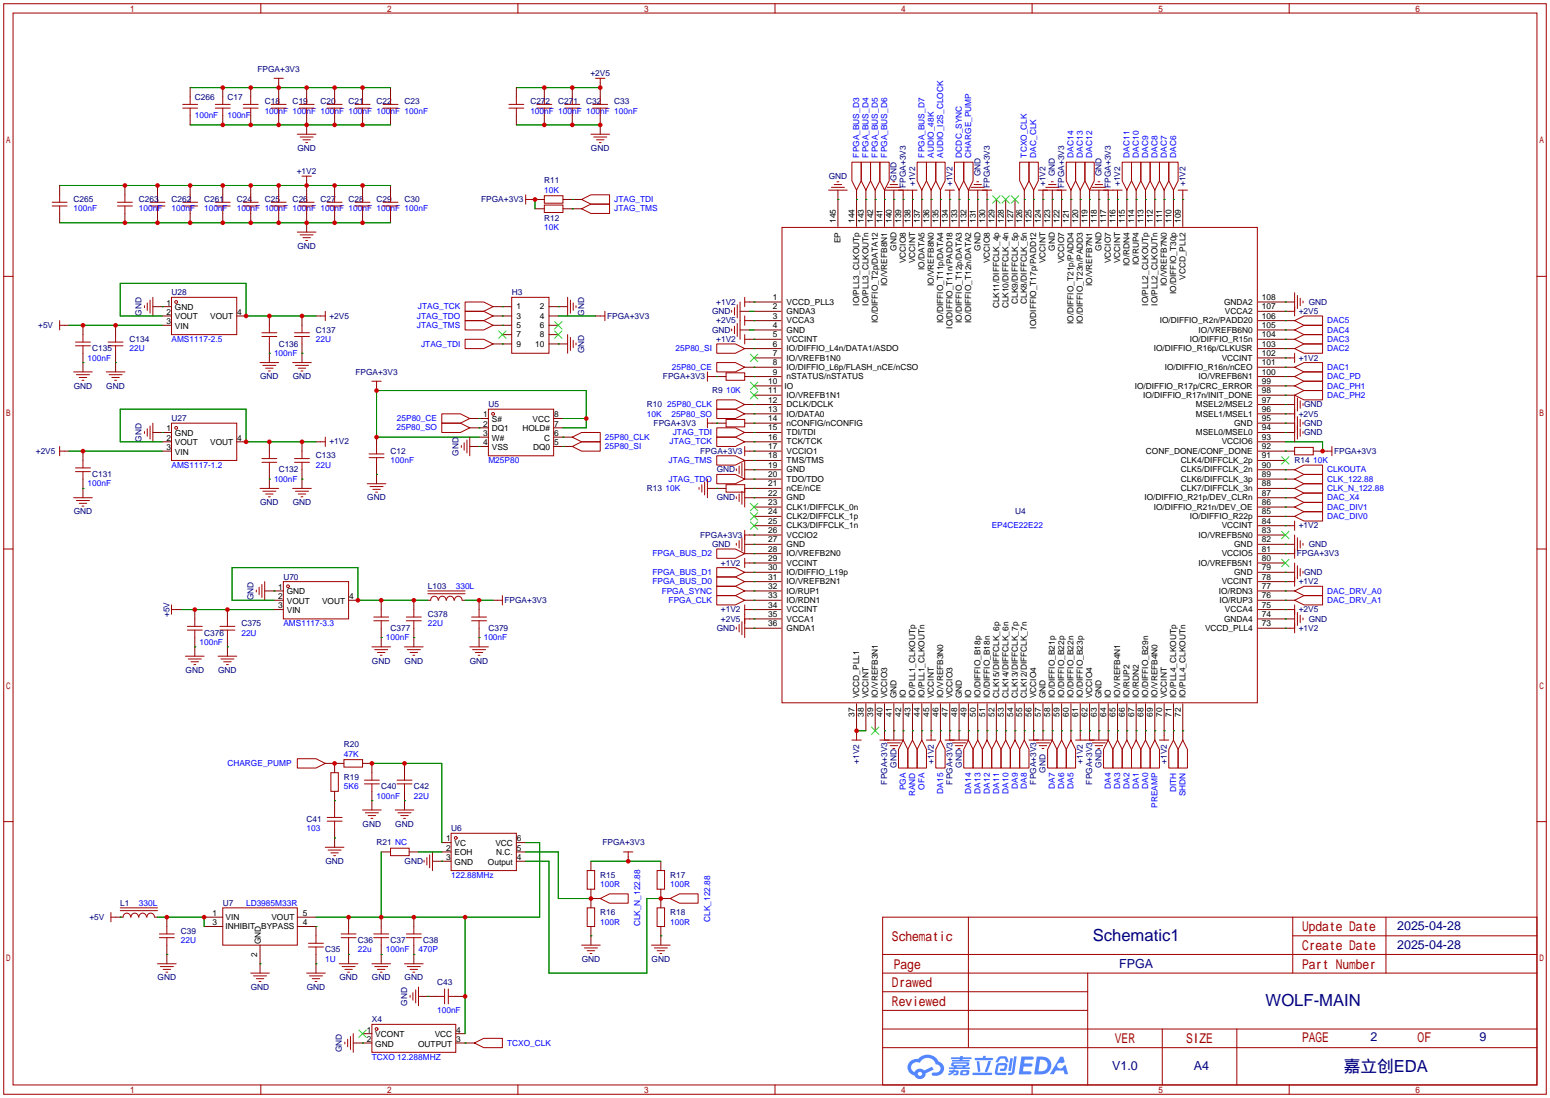
[picture p335: page 2]

VCCD_PLL4 73 GNDA4 74 VCCA4 75 IO/RUP3 76 IO/RDN3 77 VCCINT 78 GND 79 IO/VREFB5N1 80 VCCIO5 81 GND 82 IO/VREFB5N0 83 VCCINT 84 IO/DIFFIO_R22p 85 IO/DIFFIO_R21n/DEV_OE 86 IO/DIFFIO_R21p/DEV_CLRn 87 CLK7/DIFFCLK_3n 88 CLK6/DIFFCLK_3p 89 CLK5/DIFFCLK_2n 90 CLK4/DIFFCLK_2p 91 CONF_DONE/CONF_DONE 92 VCCIO6 93 MSEL0/MSEL0 94 GND 95 MSEL1/MSEL1 96 MSEL2/MSEL2 97 IO/DIFFIO_R17n/INIT_DONE 98 IO/DIFFIO_R17p/CRC_ERROR 99 IO/VREFB6N1 100 IO/DIFFIO_R16n/nCEO 101 VCCINT 102 IO/DIFFIO_R16p/CLKUSR 103 IO/DIFFIO_R15n 104 IO/VREFB6N0 105 IO/DIFFIO_R2n/PADD20 106 VCCA2 107 GNDA2 108 VCCD_PLL2 109 IO/DIFFIO_T30p 110 IO/VREFB⁷N⁰ ¹¹¹ IO/PLL2_CLKOUTn 112 IO/PLL2_CLKOUTp 113 IO/RUP⁴ ¹¹⁴ IO/RDN⁴ ¹¹⁵ VCCINT 116 VCCIO⁷ ¹¹⁷ GND ¹¹⁸ IO/VREFB⁷N¹ ¹¹⁹ IO/DIFFIO_T23n/PADD³ ¹²⁰ IO/DIFFIO_T21p/PADD⁴ ¹²¹ VCCIO⁷ ¹²² GND ¹²³ VCCINT 124 IO/DIFFIO_T17p/PADD¹² ¹²⁵ CLK⁸/DIFFCLK_5n 126 CLK⁹/DIFFCLK_5p 127 CLK¹⁰/DIFFCLK_4n 128 CLK¹¹/DIFFCLK_4p 129 VCCIO⁸ ¹³⁰ GND ¹³¹ IO/DIFFIO_T12n/DATA² ¹³² IO/DIFFIO_T12p/DATA³ ¹³³ IO/DIFFIO_T11n/PADD¹⁸ ¹³⁴ IO/DIFFIO_T11p/DATA⁴ ¹³⁵ IO/VREFB⁸N⁰ ¹³⁶ IO/DATA⁵ ¹³⁷ VCCINT 138 VCCIO⁸ ¹³⁹ GND ¹⁴⁰ IO/VREFB⁸N¹ ¹⁴¹ IO/DIFFIO_T2p/DATA¹² ¹⁴² IO/PLL3_CLKOUTn 143 IO/PLL3_CLKOUTp 144

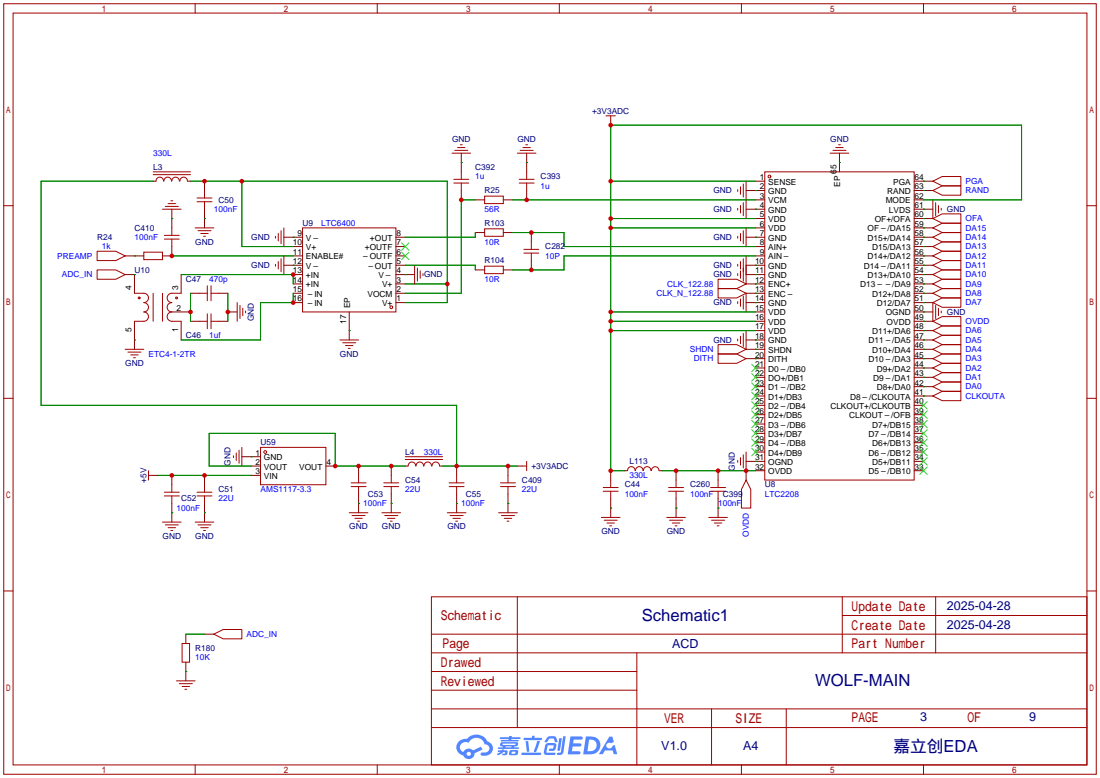
[picture p336: page 3]

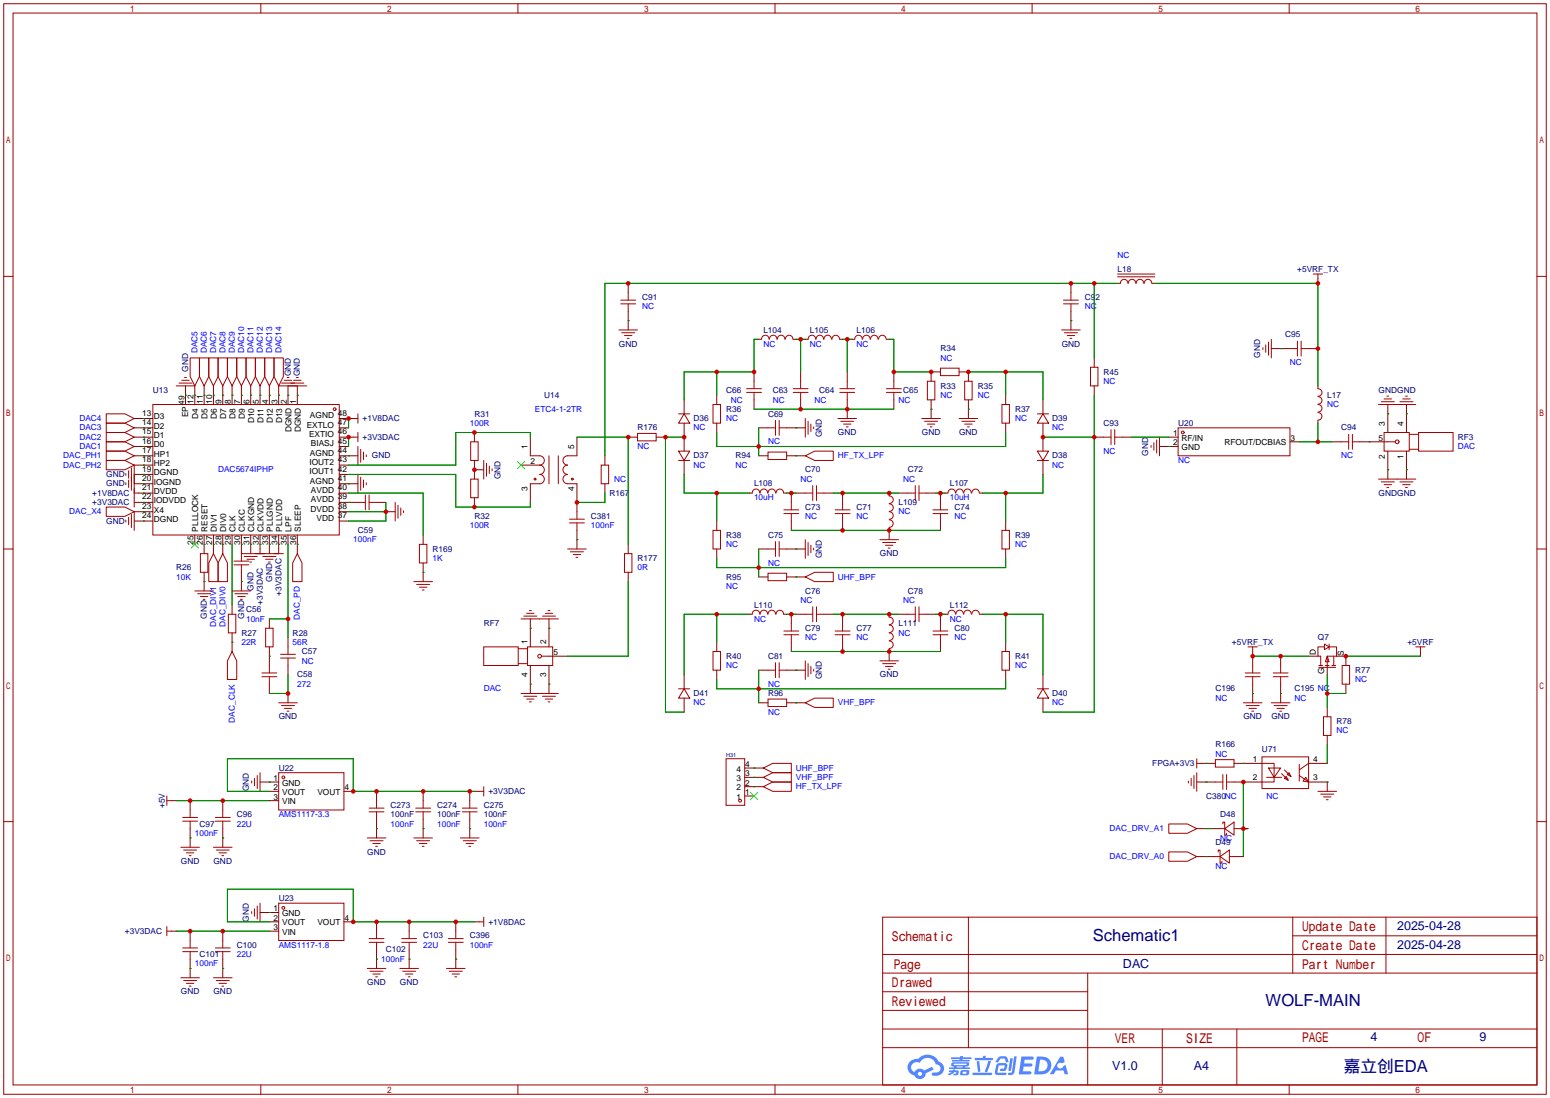
[picture p337: page 4]

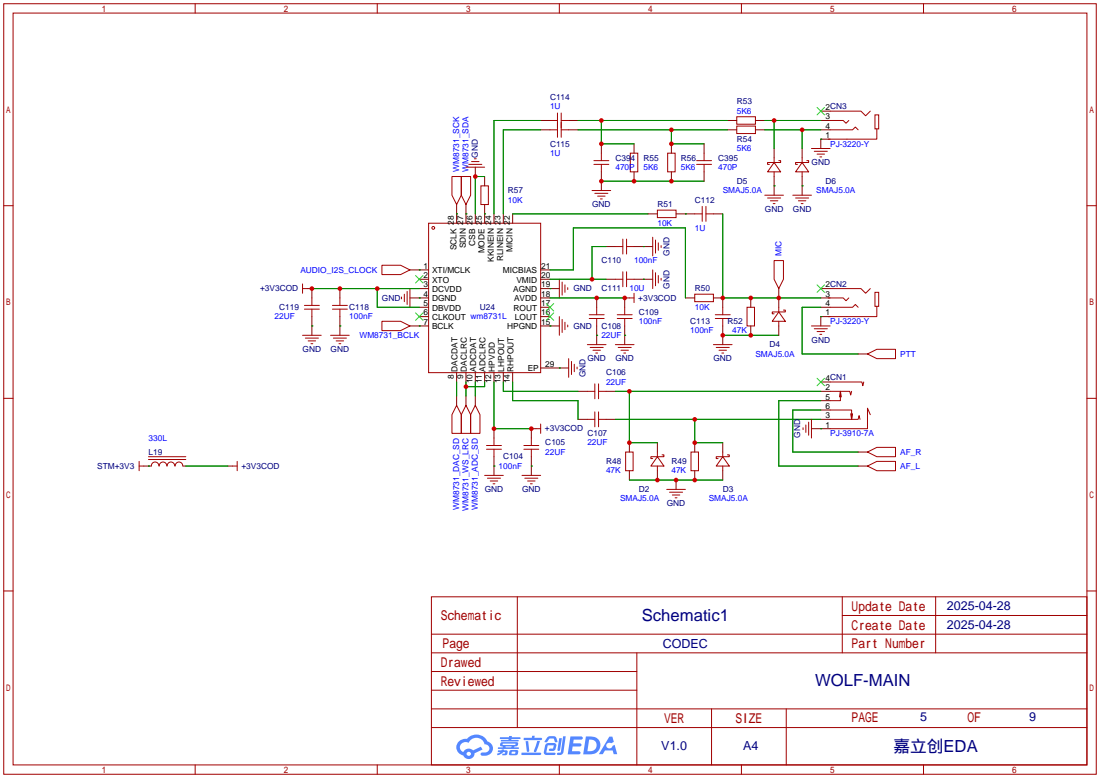
[picture p338: page 5]

HPGND 15 LOUT 16 ROUT 17 AVDD 18 AGND 19 VMID 20 MICBIAS 21 MICIN ²²

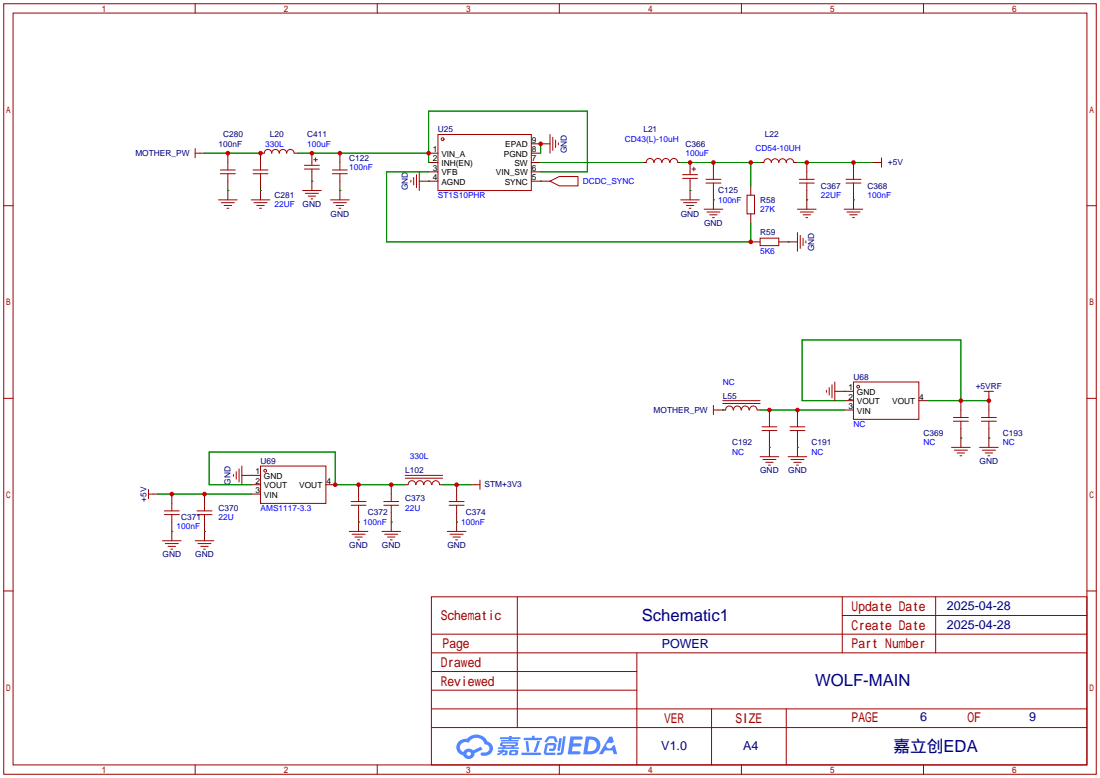
[picture p339: page 6]

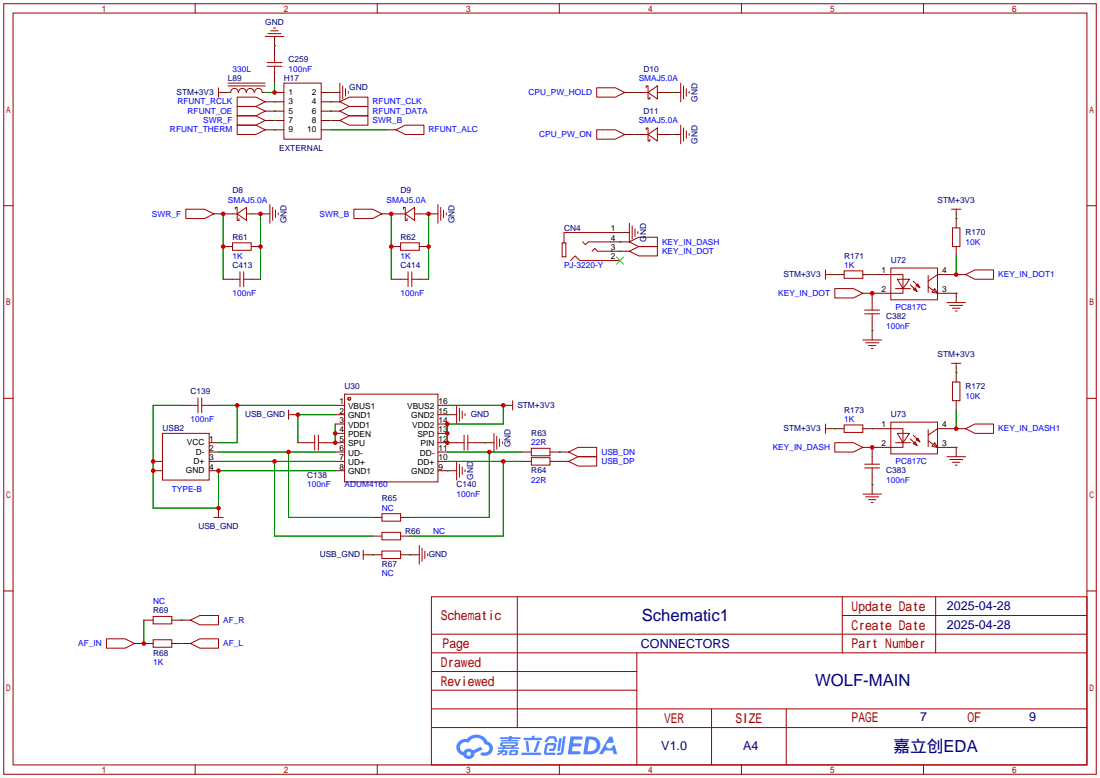
[picture p340: page 7]

DD+ 10 DD- 11 PIN 12 SPD 13 VDD2 14 GND2 15 VBUS2 16

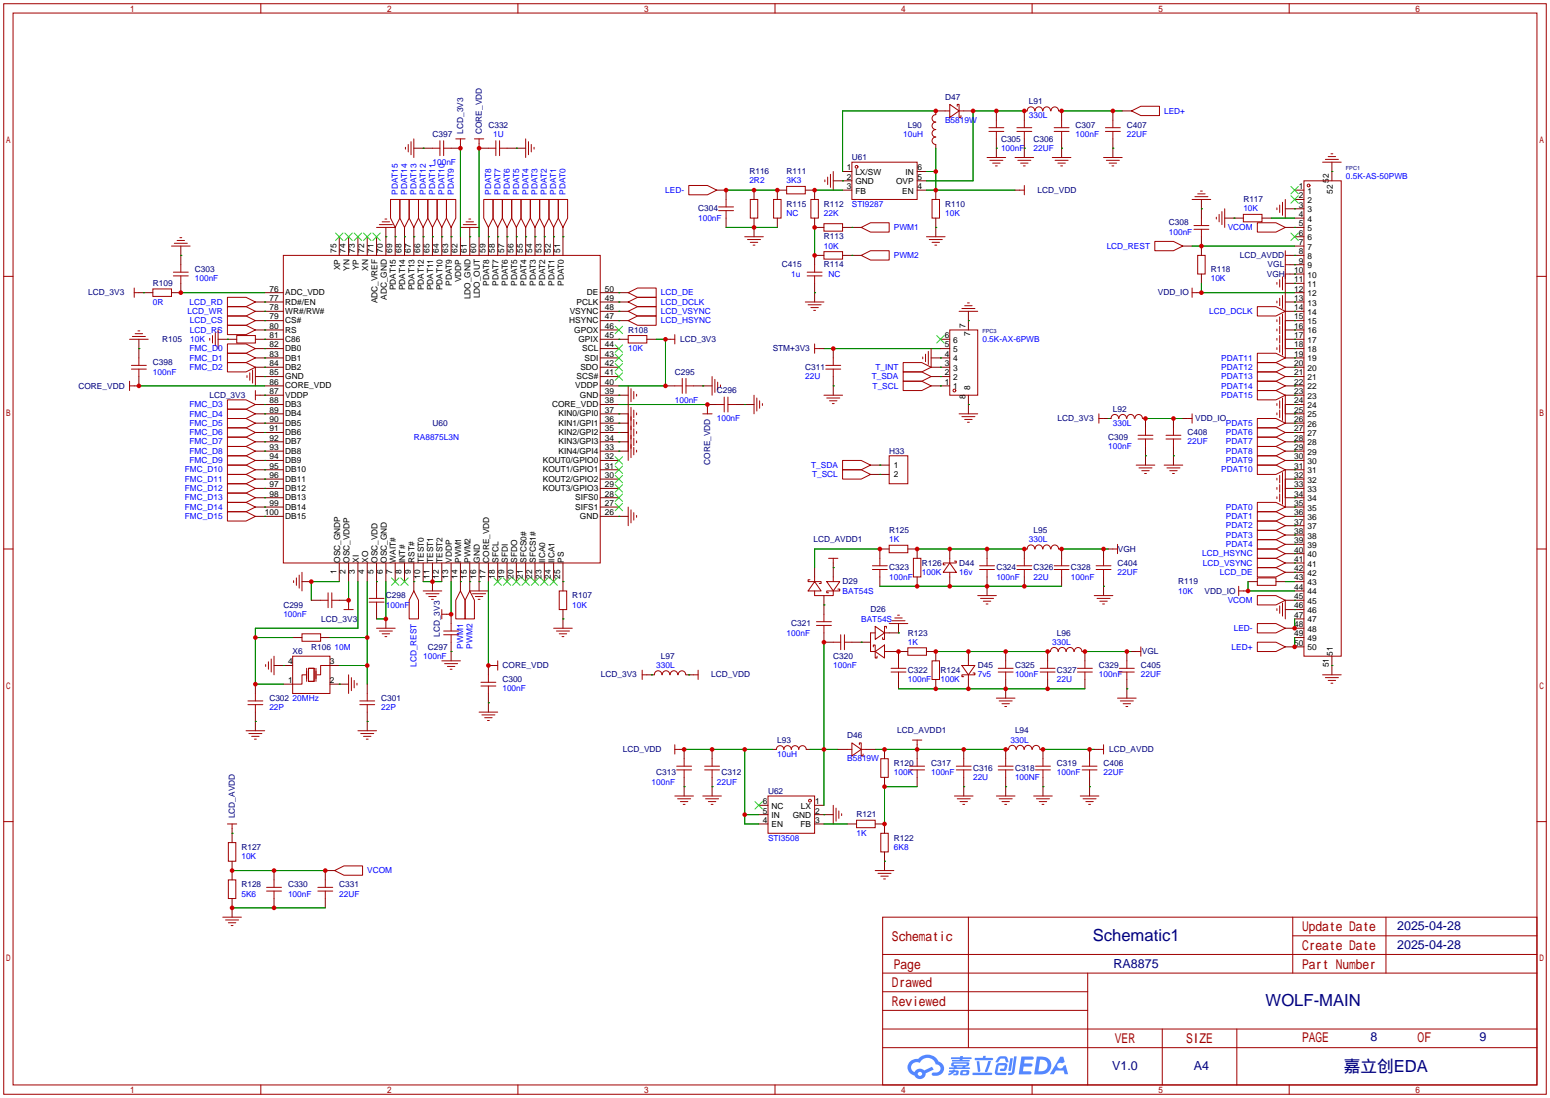
[picture p341: page 8]

GND 26 SIFS1 27 SIFS0 28 KOUT3/GPIO3 29 KOUT2/GPIO2 30 KOUT1/GPIO1 31 KOUT0/GPIO0 32 KIN4/GPI4 33 KIN3/GPI3 34 KIN2/GPI2 35 KIN1/GPI1 36 KIN0/GPI0 37 CORE_VDD 38 GND 39 VDDP 40 SCS# 41 SDO 42 SDI 43 SCL 44 GPIX 45 GPOX 46 HSYNC 47 VSYNC 48 PCLK 49 DE 50 PDAT0 51 PDAT1 52 PDAT2 53 PDAT3 54 PDAT4 55 PDAT5 56 PDAT6 57 PDAT7 58 PDAT8 59 LDO_OUT 60 LDO_GND ⁶¹ VDDP ⁶² PDAT9 63 PDAT10 64 PDAT11 65 PDAT12 66 PDAT13 67 PDAT14 68 PDAT15 69 ADC_GND ⁷⁰ ADC_VREF 71 XN ⁷² YP ⁷³ YN ⁷⁴ XP ⁷⁵

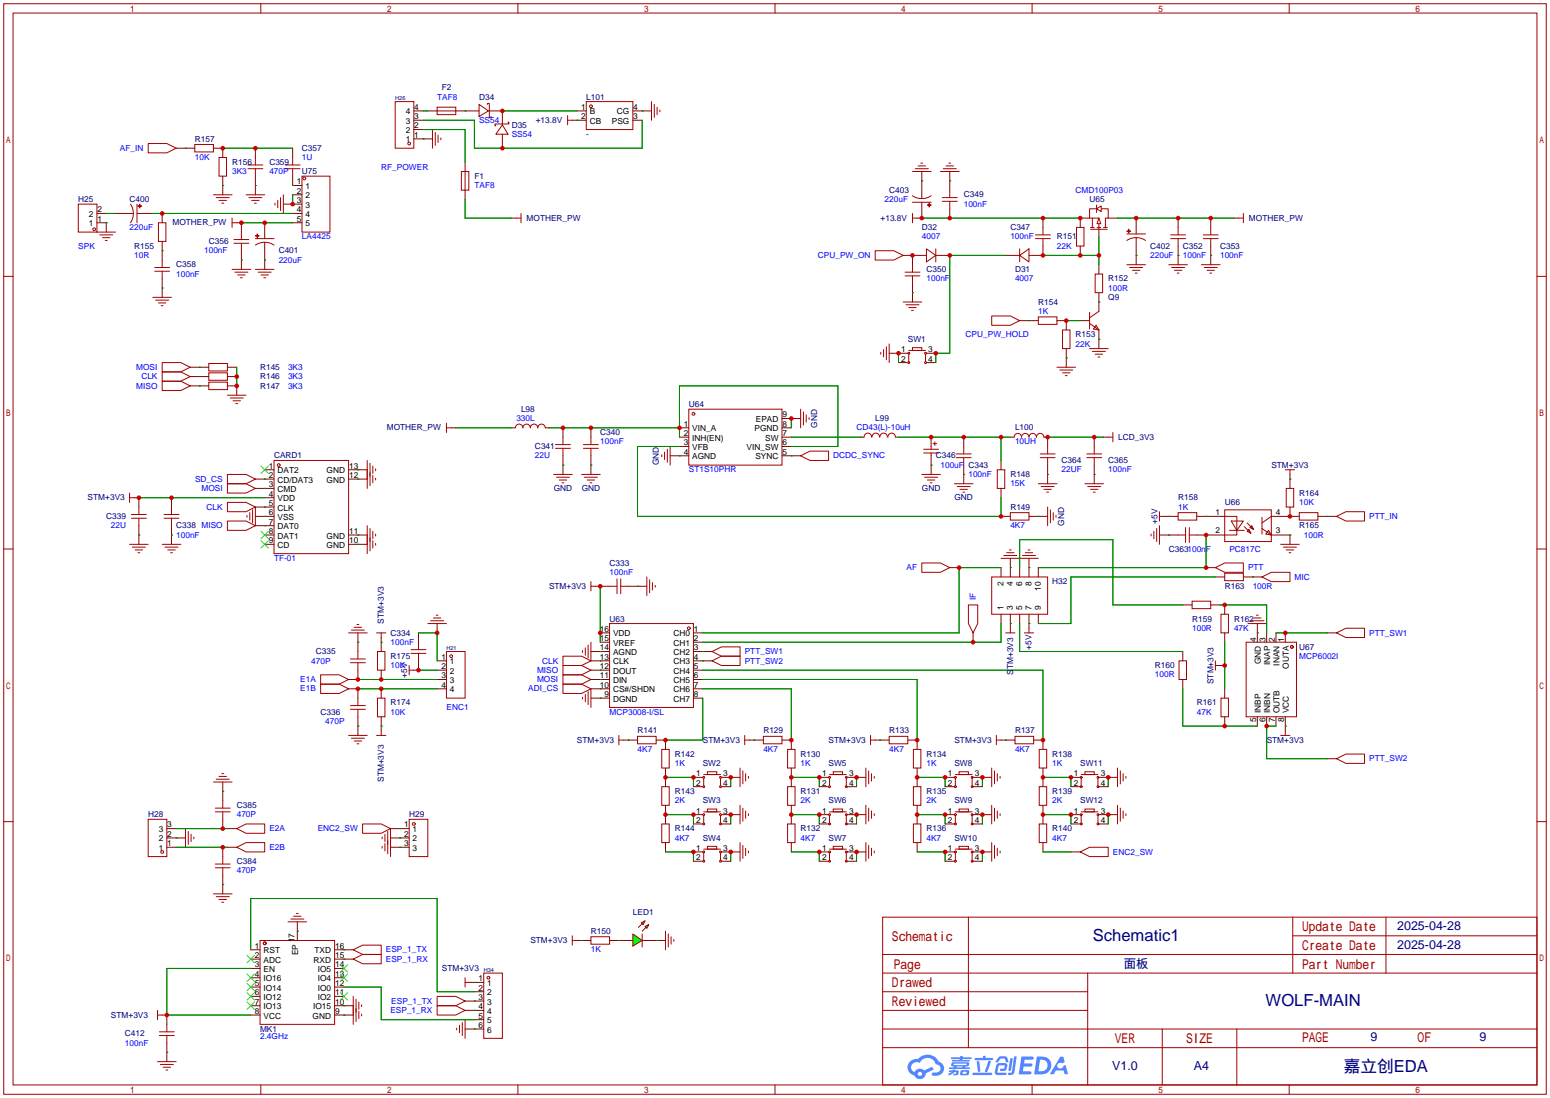
[picture p342: page 9]

CS#/SHDN 10 DIN 11 DOUT 12 CLK 13 AGND 14 VREF 15 VDD 16
