XGudron/UA3REO-DDC-Transceiver/Schematic/Wolf-BA7LJL/Scheme/SCH_PA_Unit.pdf

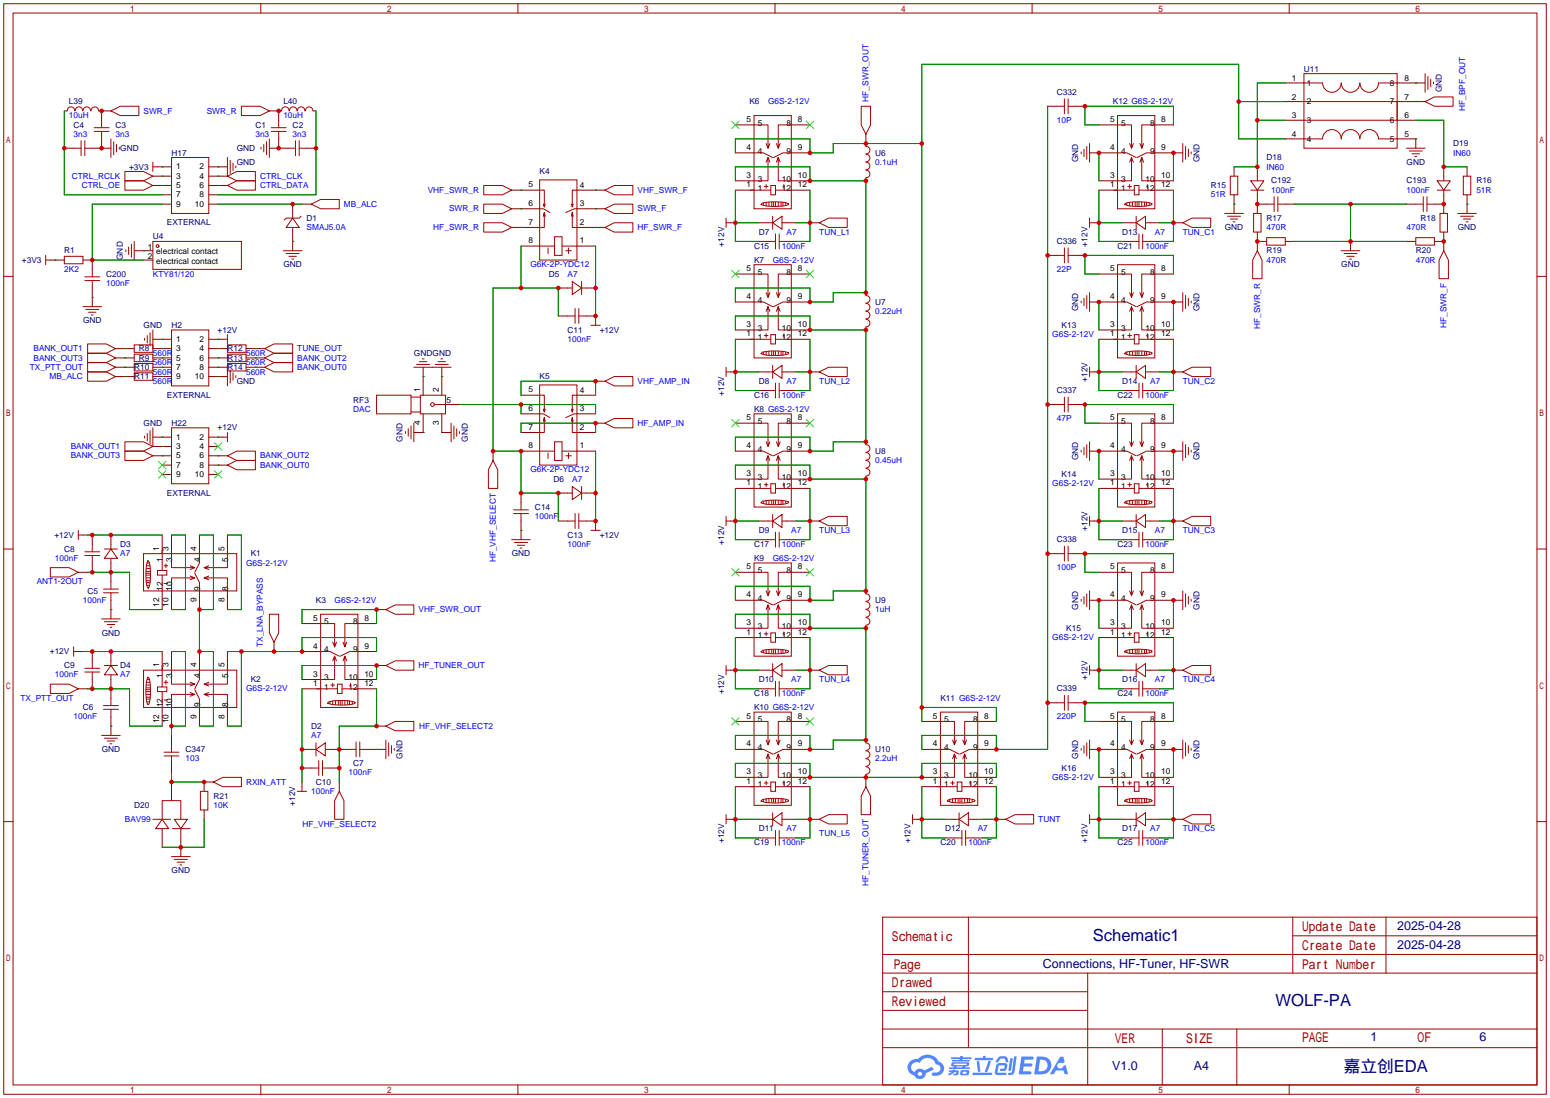
[picture p343: page 1]

2025-04-28 Schematic1
Connections, HF-Tuner, HF-SWR

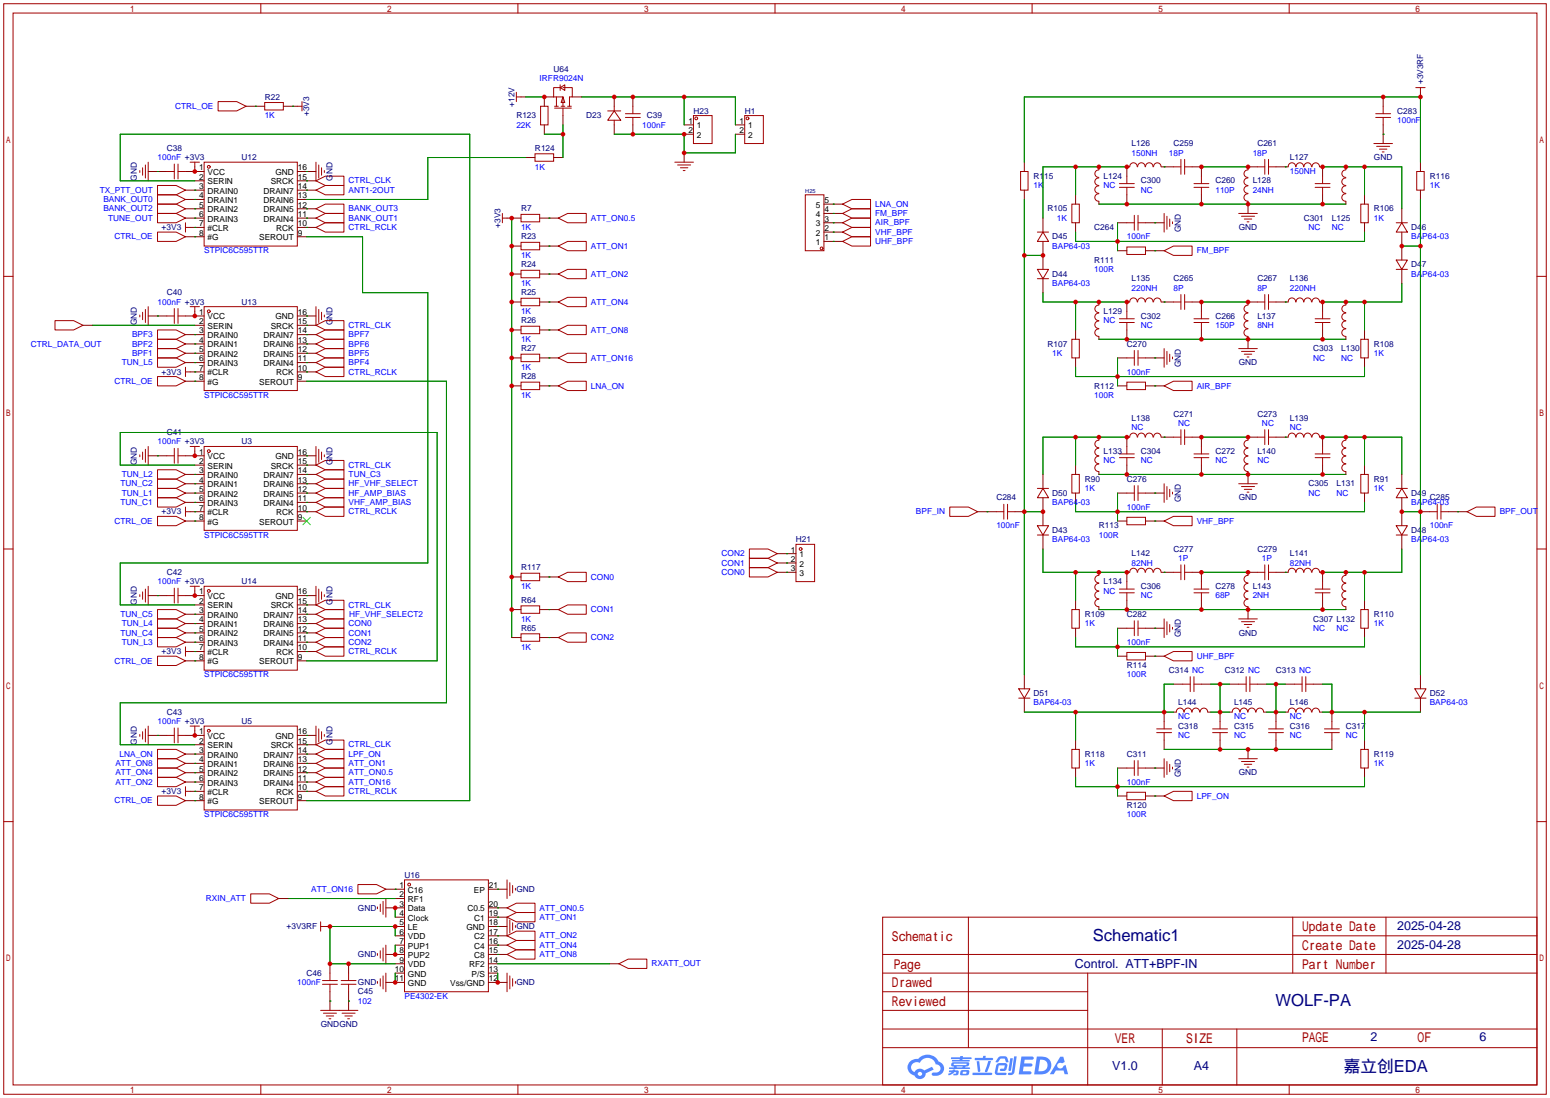
[picture p344: page 2]

2025-04-28 Schematic1
Control. ATT+BPF-IN

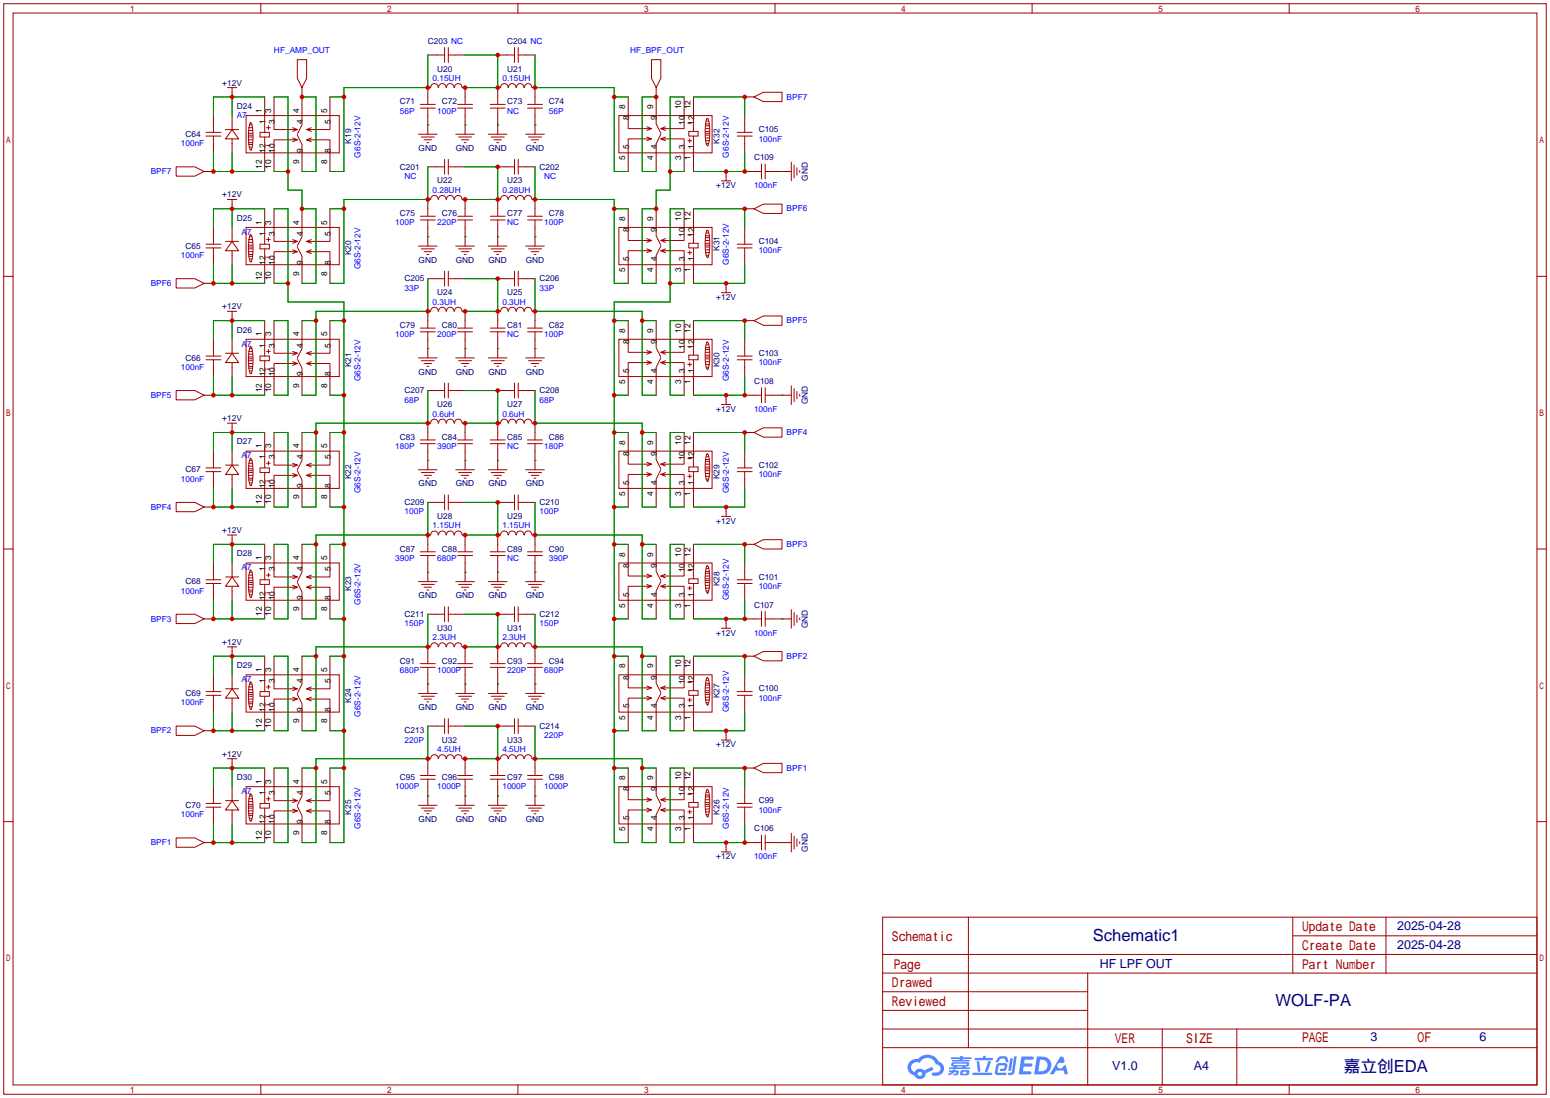
[picture p345: page 3]

GND GND

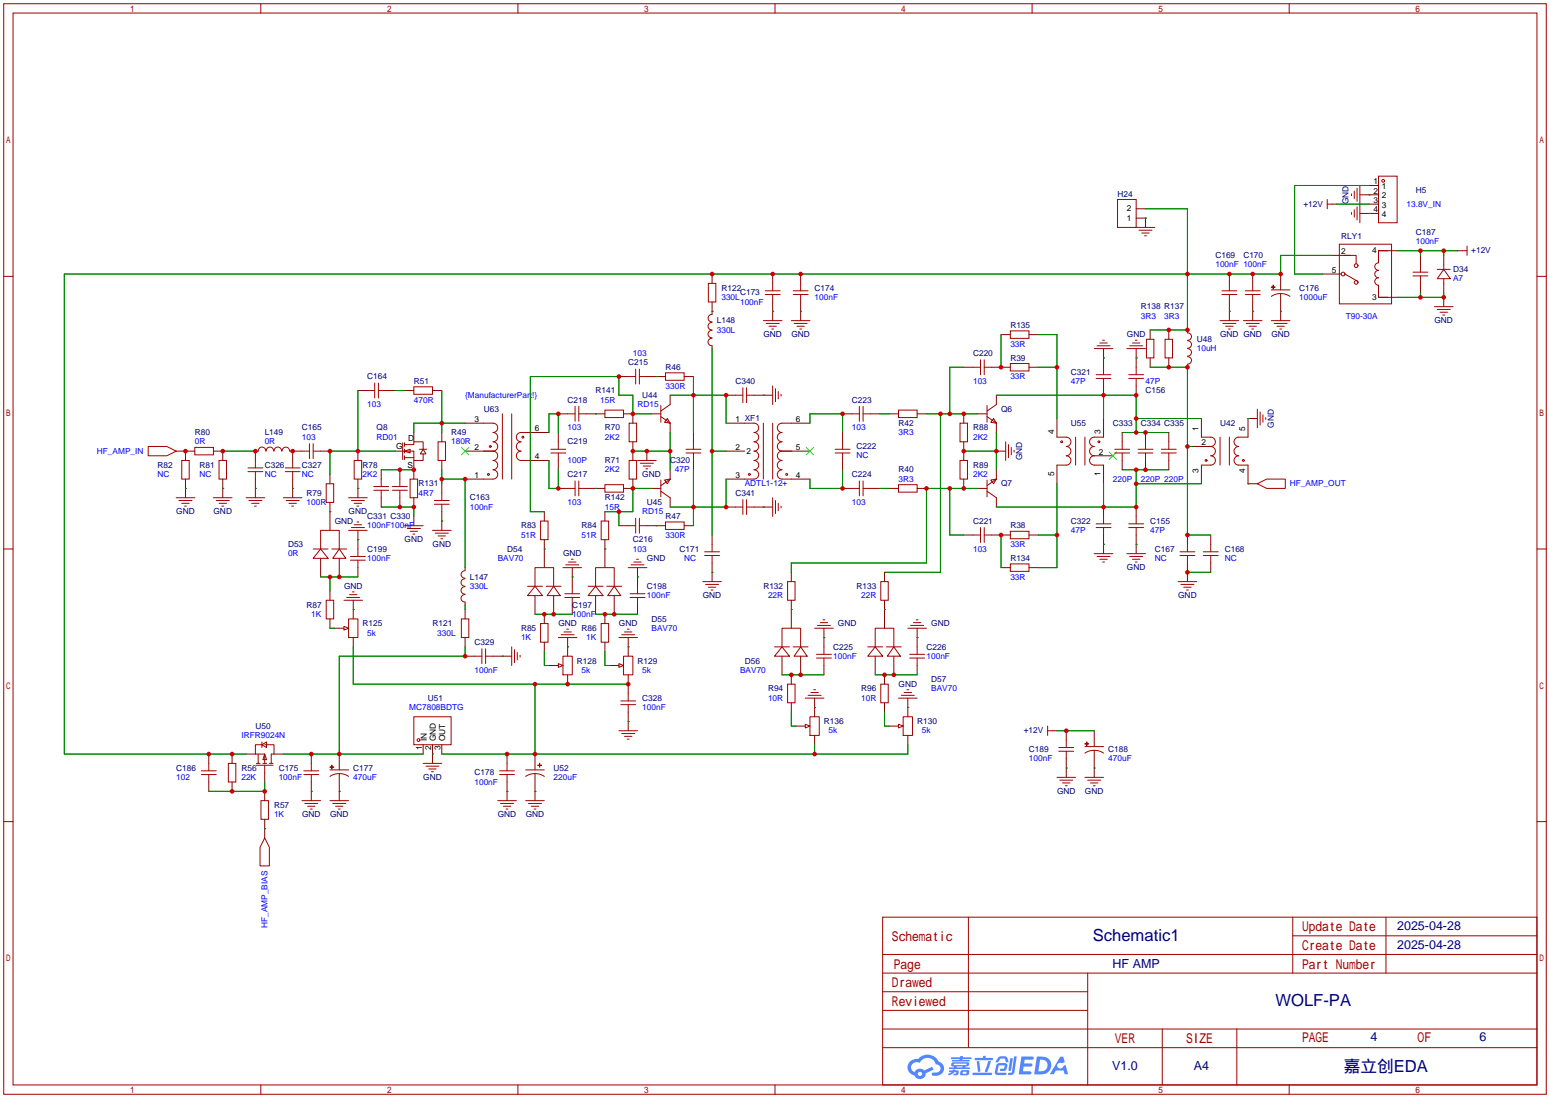
[picture p346: page 4]

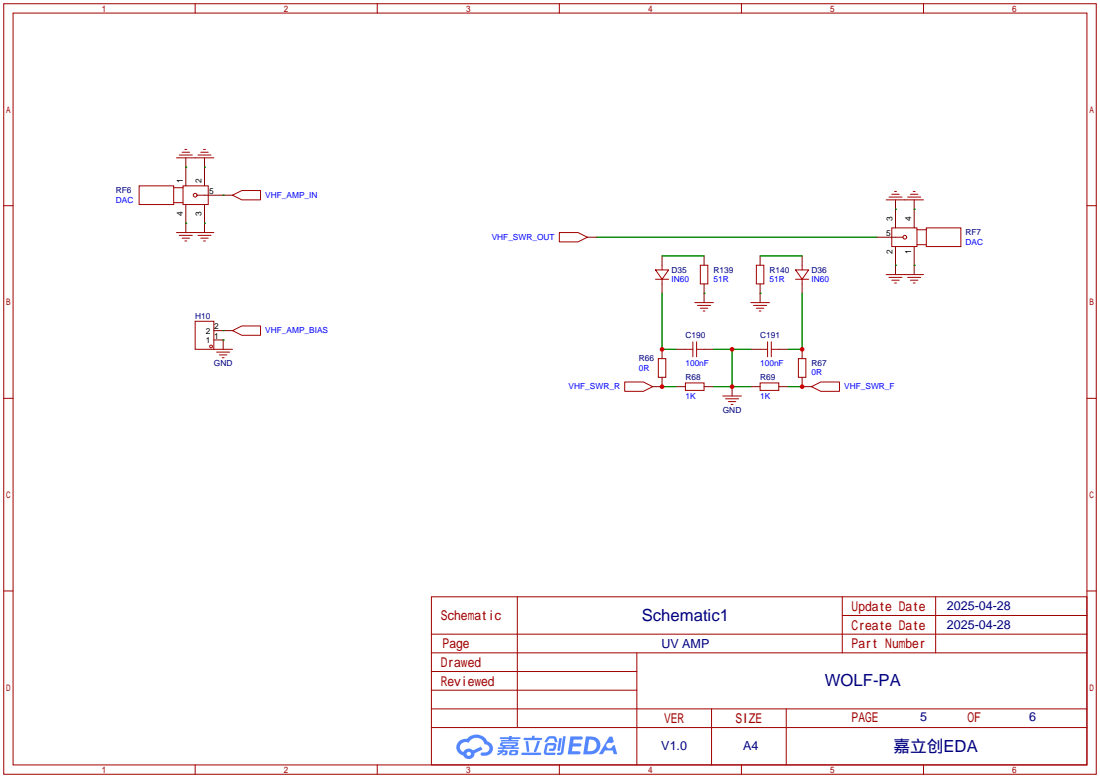
[picture p347: page 5]

# VHF

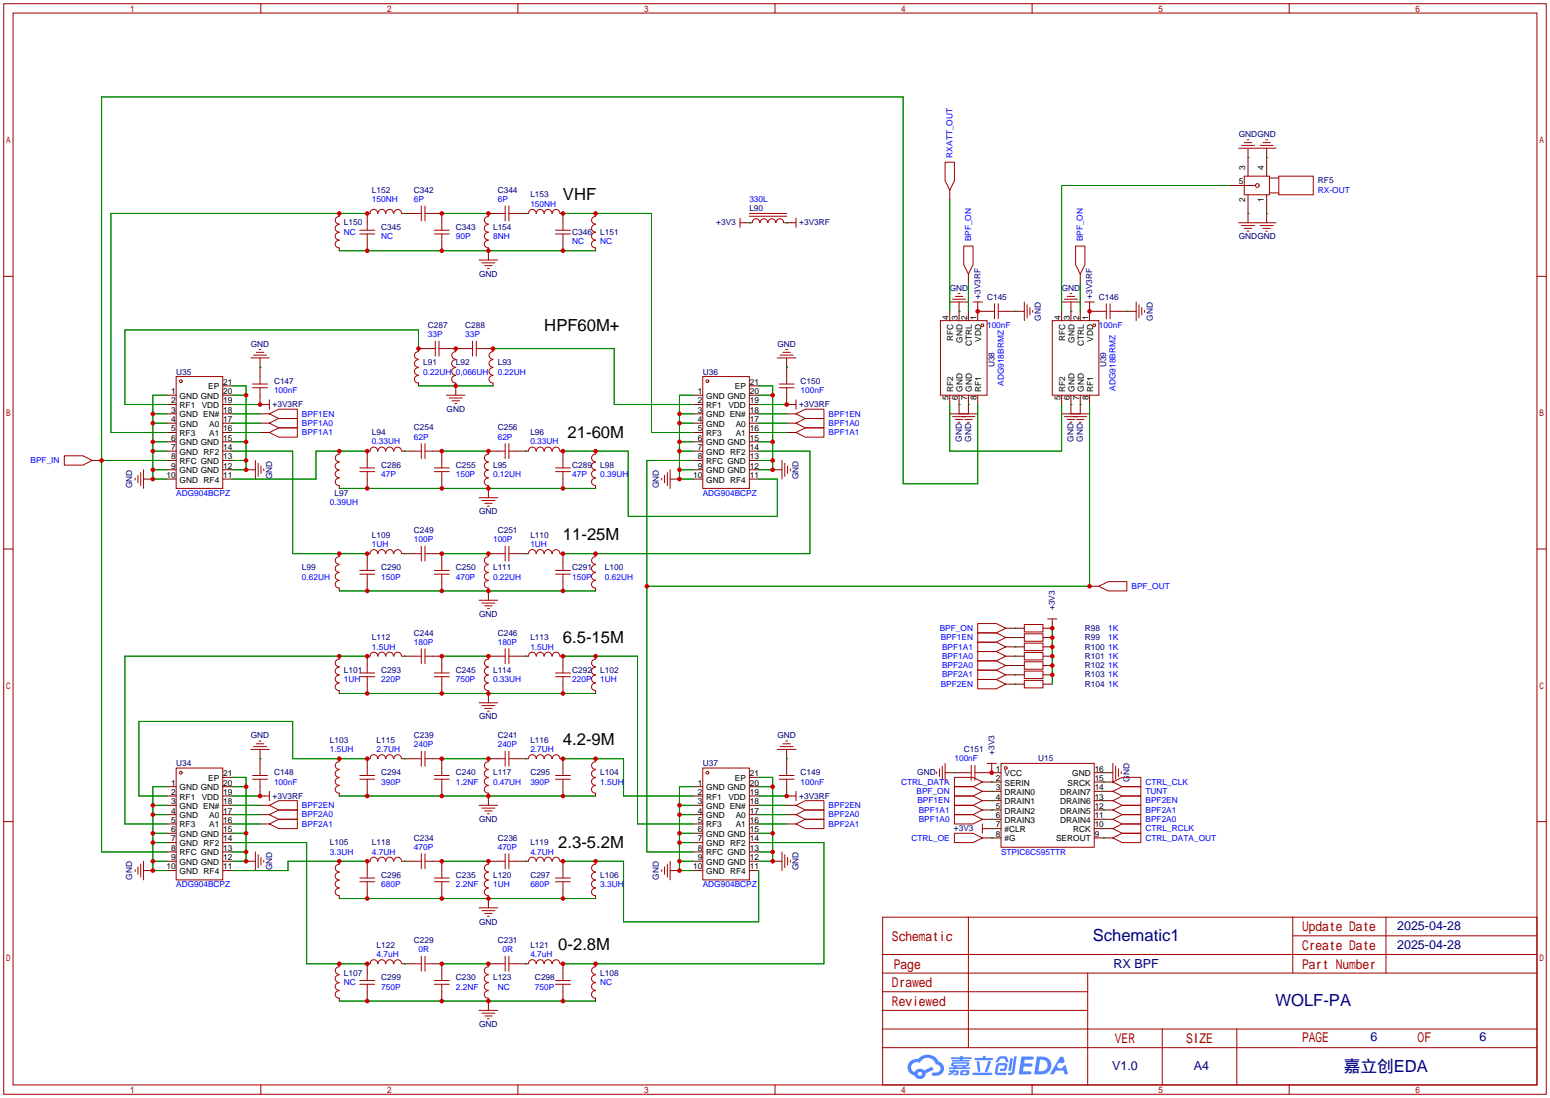
[picture p348: page 6]
