XGudron/UA3REO-DDC-Transceiver/Schematic/Wolf-DK102/Schematic/DK-102_AD_DA_V01_240324.pdf

# RX板

# AMP板 J

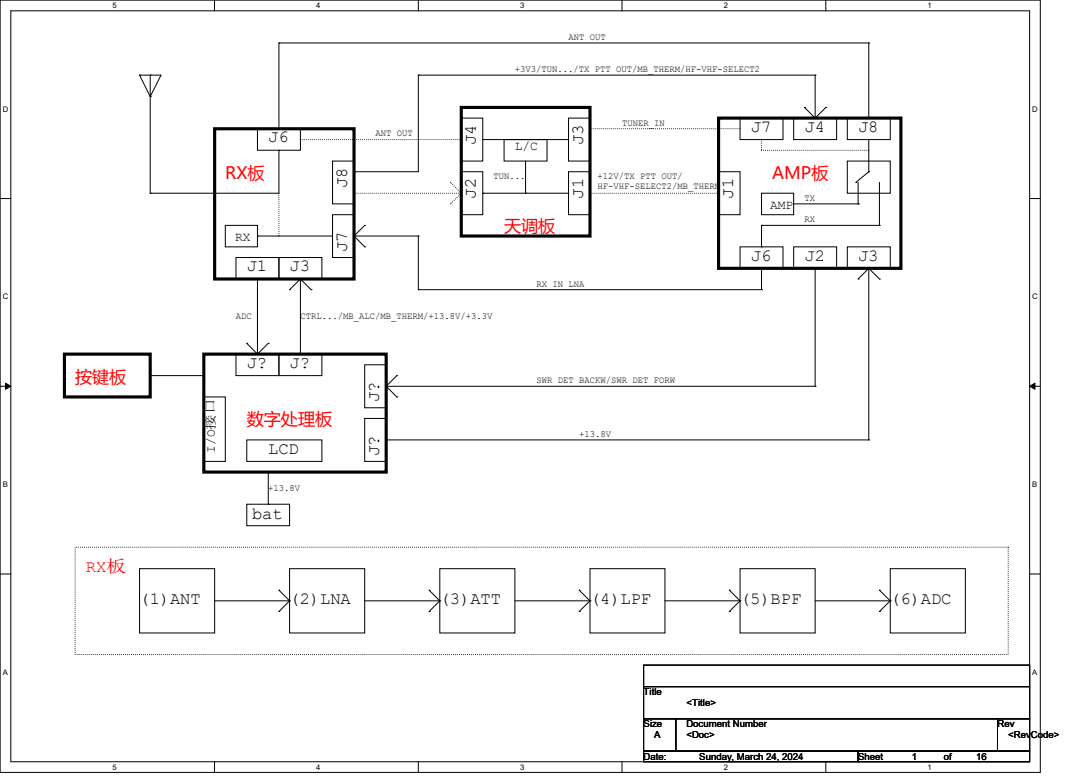
[picture p349: page 1]
天调板; 数字处理板; ANT OUT; TUNER_IN; AMP; ADC; CTRL.../MB_ALC/MB_THERM/+13.8V/+3.3V; bat; (1)ANT; (2)LNA; (3)ATT; (4)LPF; (5)BPF; (6)ADC; RX板; 按键板; LCD; TUN...; Title; Size; Document Number; Rev; Date:; Sheet; <Doc>; <RevCode>; <Title>; Sunday, March 24, 2024

+3V3/TUN.../TX PTT OUT/MB_THERM/HF-VHF-SELECT2

+12V/TX PTT OUT/
HF-VHF-SELECT2/MB_THERM

RX IN LNA

SWR DET BACKW/SWR DET FORW

500mA

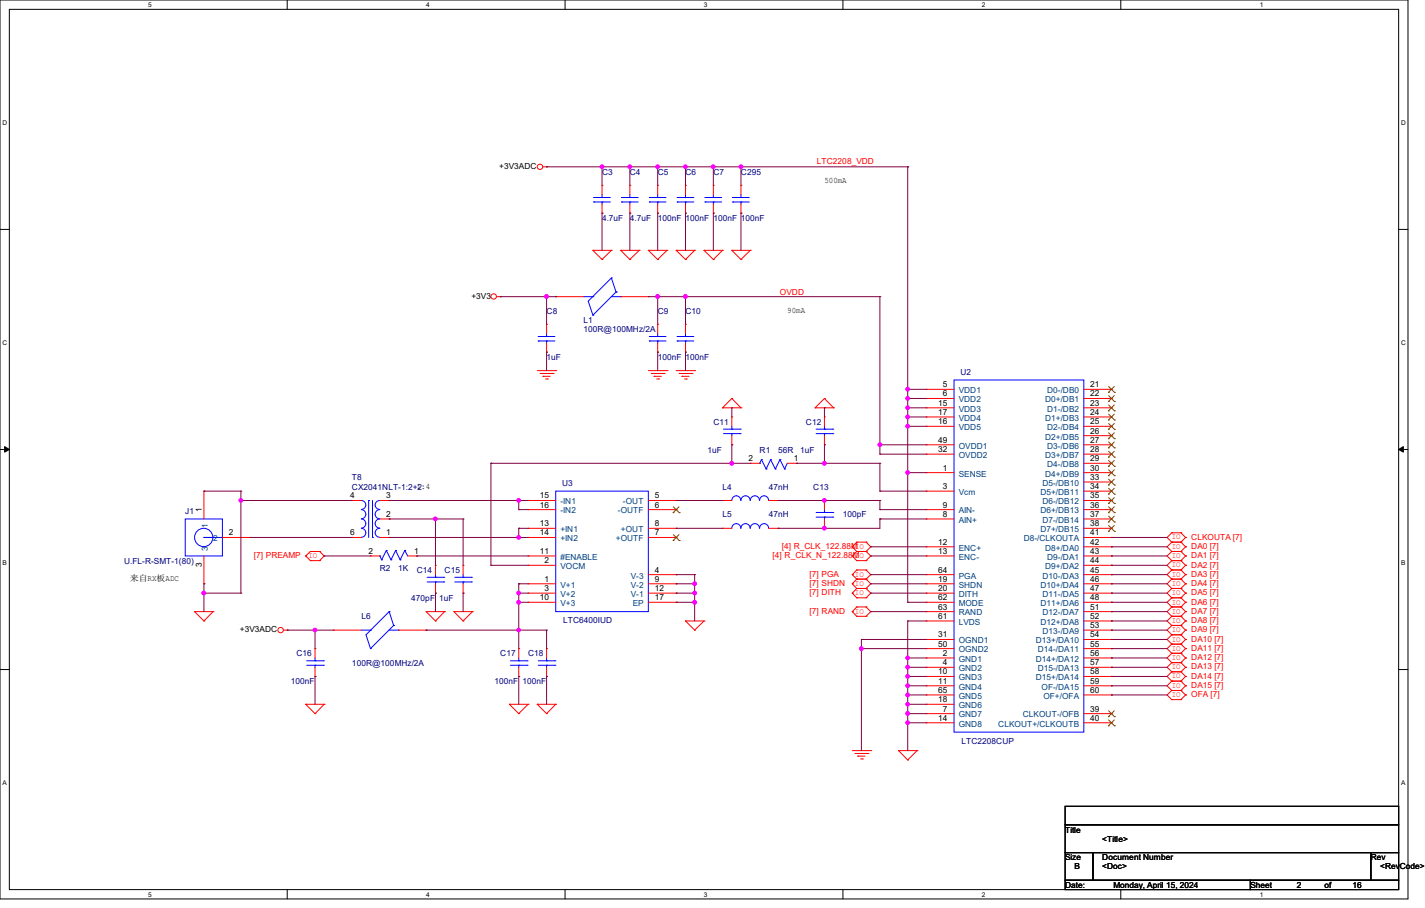
[picture p350: page 2]

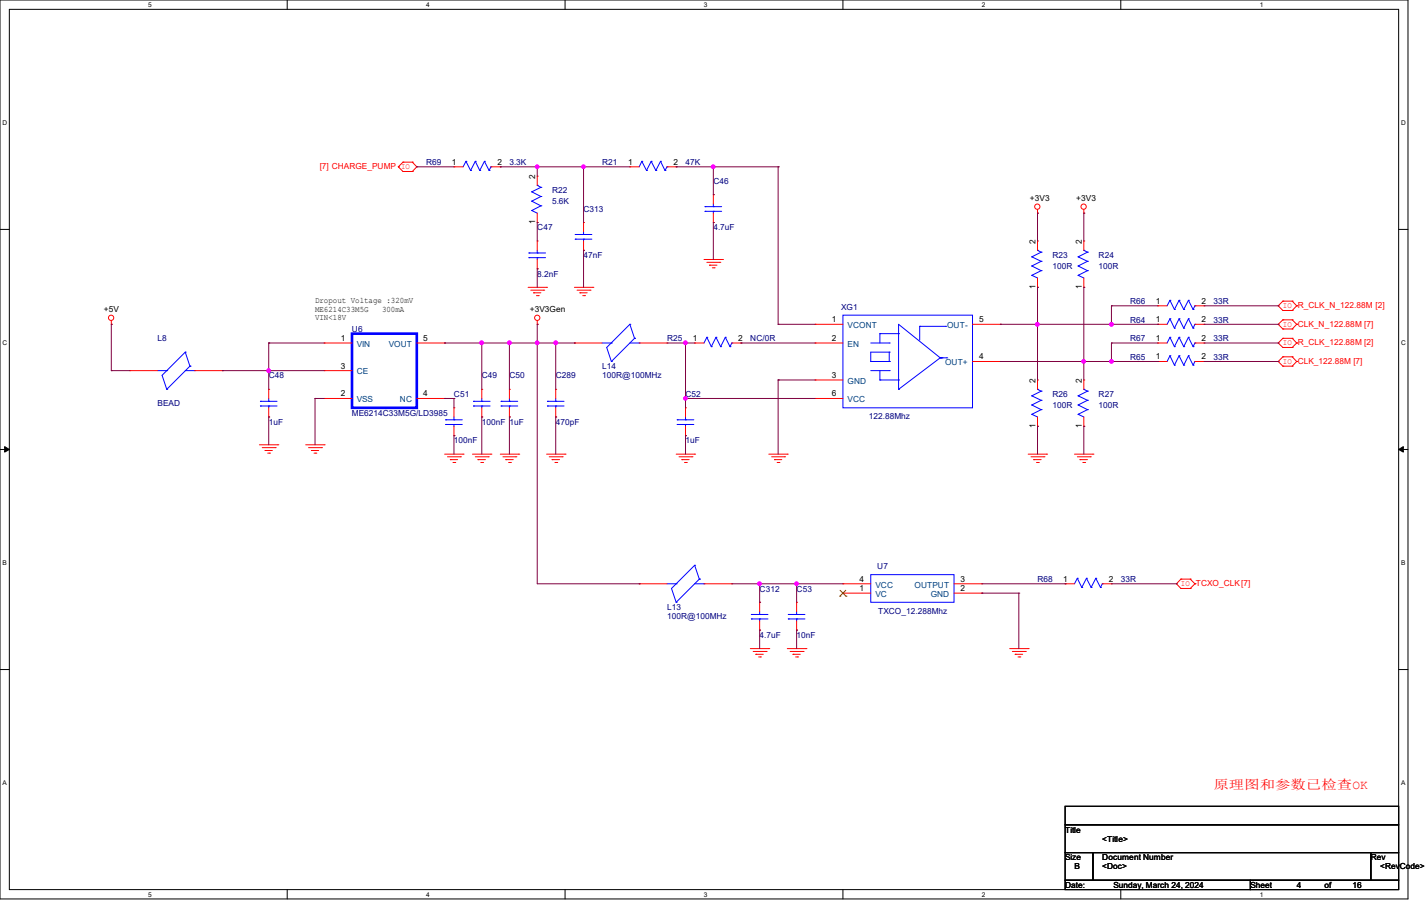
[picture p351: page 3]

## VIN=2.6V~20V VOUT=1.5V~15V/200mA

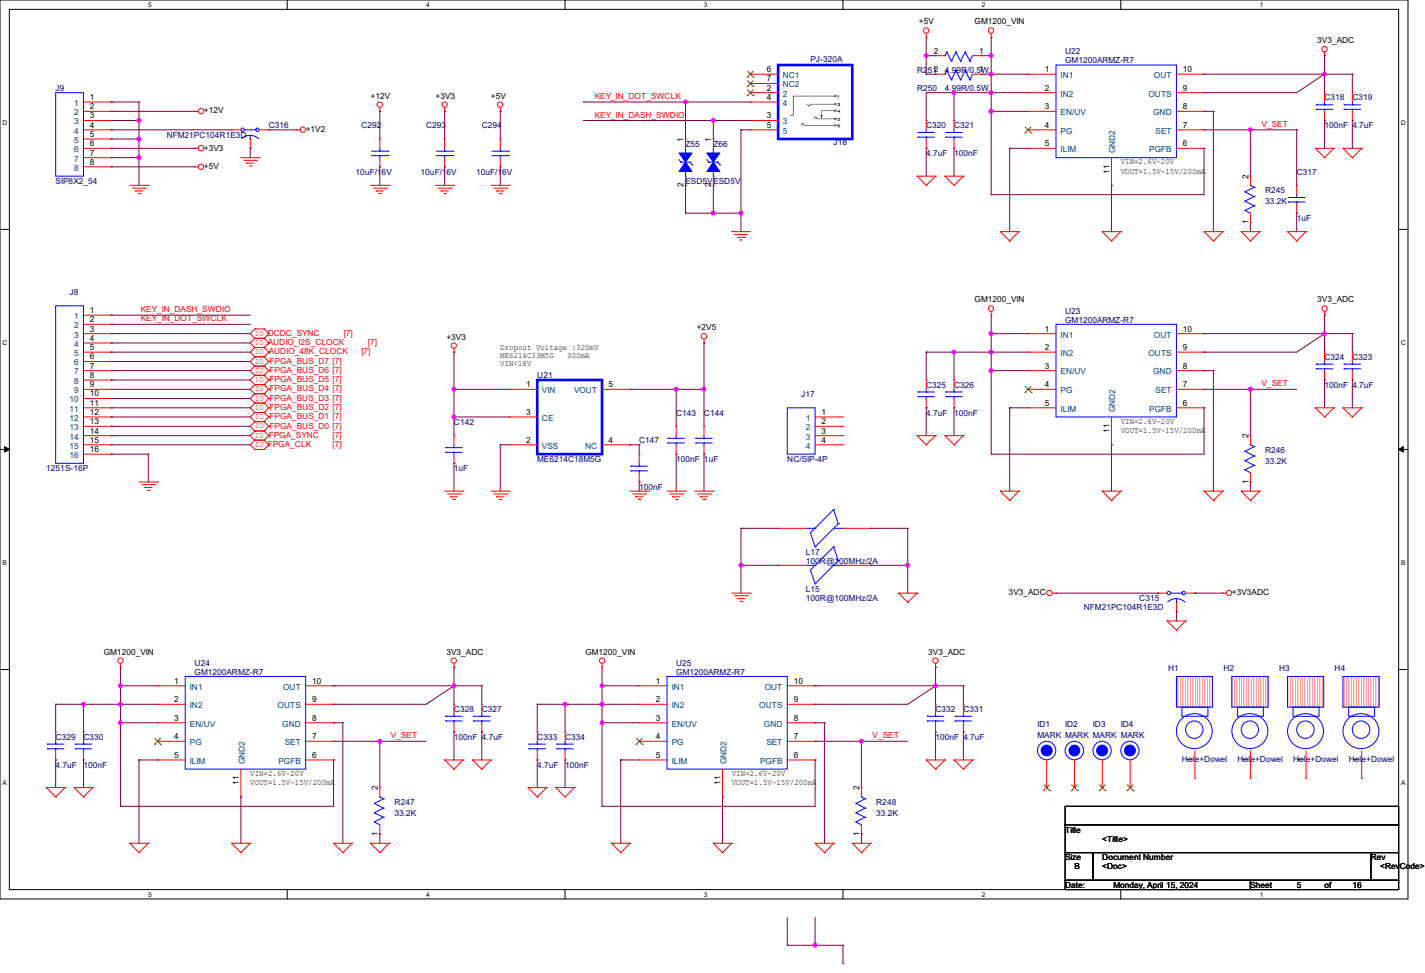
[picture p352: page 4]

## Dropout Voltage :320mV ME6214C33M5G 300mA

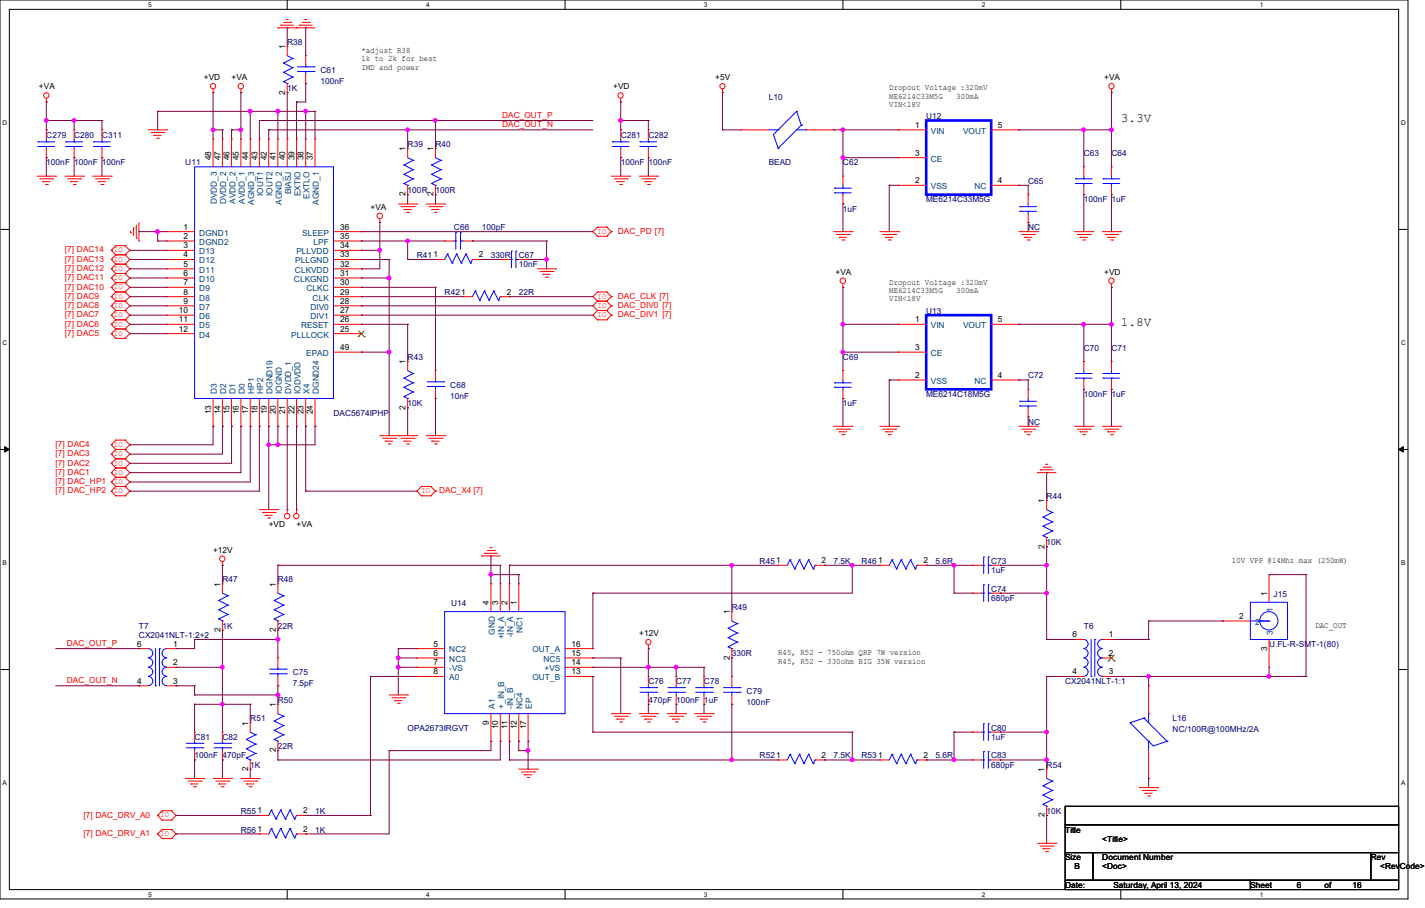
[picture p353: page 5]

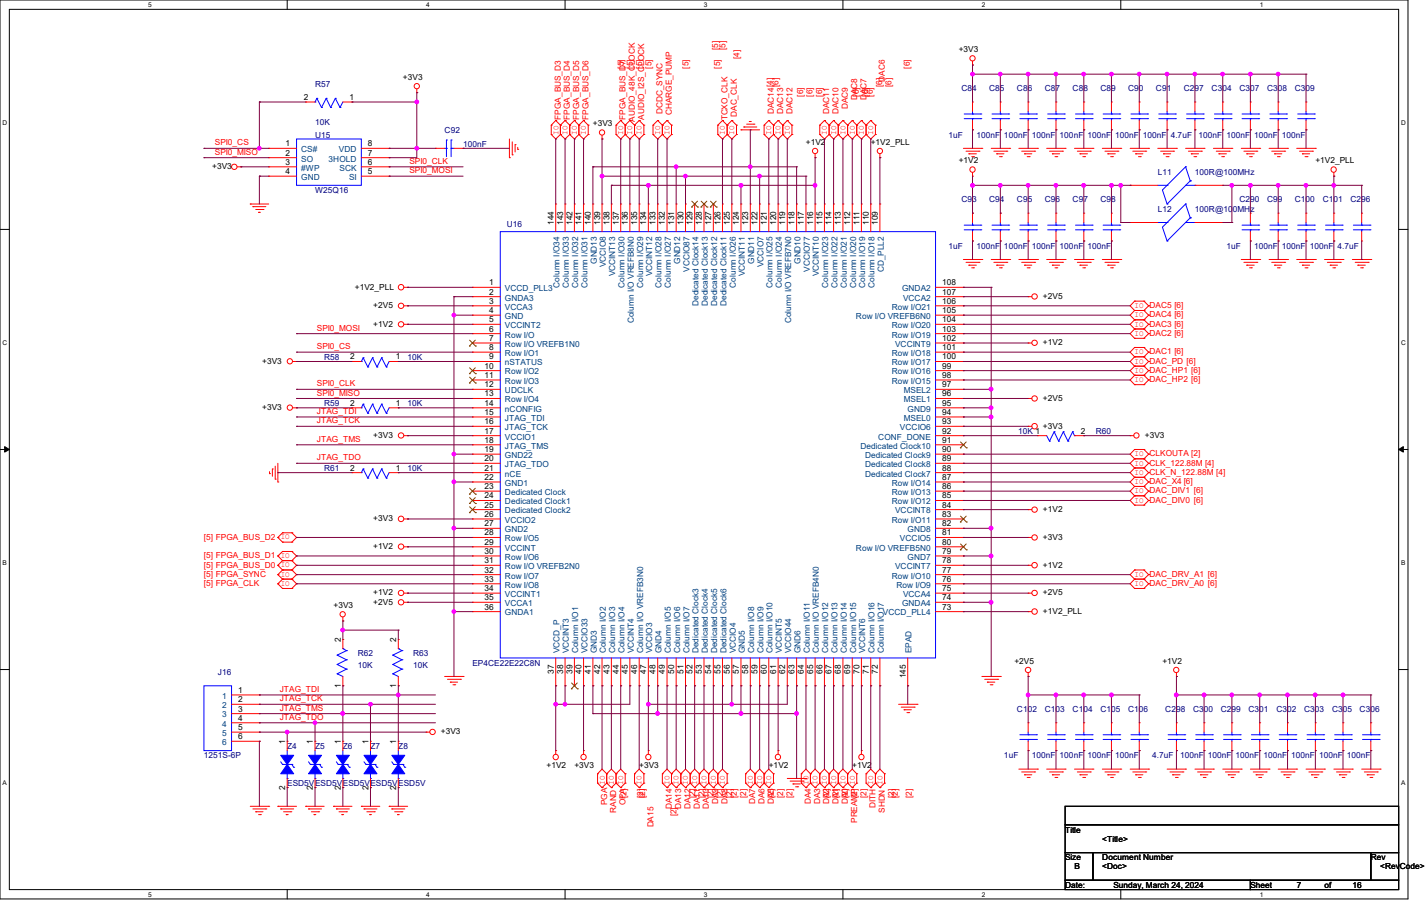
[picture p354: page 6]
