XGudron/UA3REO-DDC-Transceiver/Schematic/Wolf-DK102/Schematic/DK-102_MB_V02_240414.pdf

# RX板

# AMP板 J

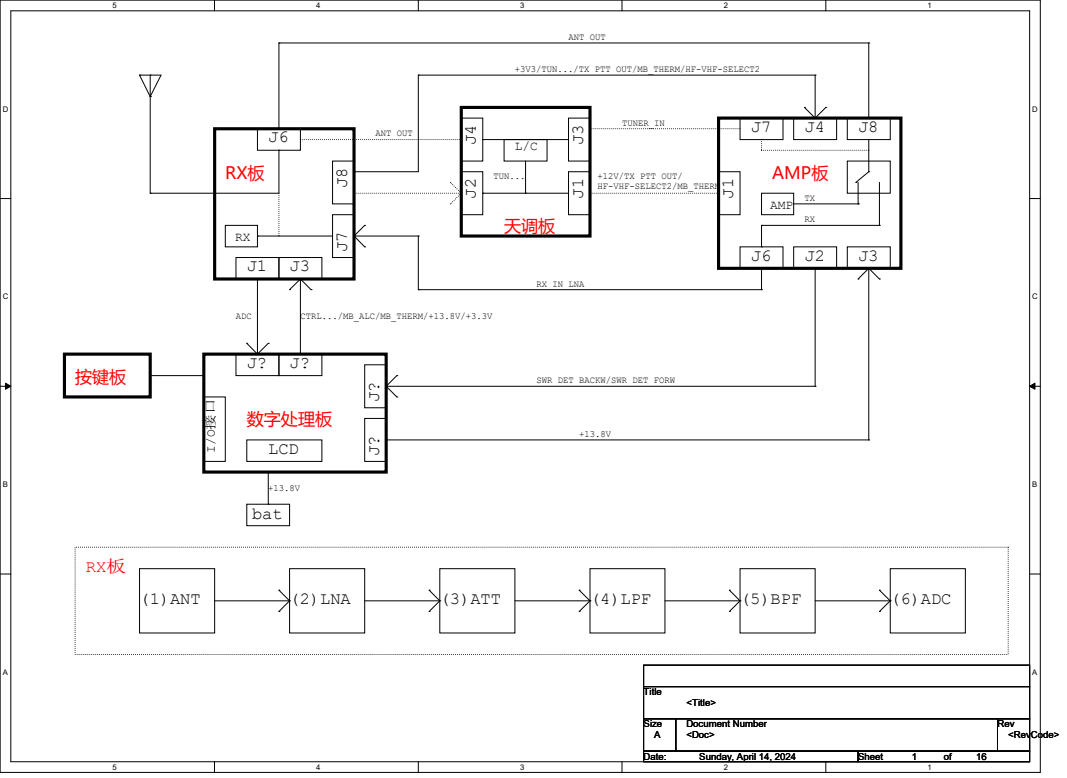
[picture p355: page 1]
天调板; 数字处理板; ANT OUT; TUNER_IN; AMP; ADC; CTRL.../MB_ALC/MB_THERM/+13.8V/+3.3V; bat; (1)ANT; (2)LNA; (3)ATT; (4)LPF; (5)BPF; (6)ADC; RX板; 按键板; LCD; TUN...; Title; Size; Document Number; Rev; Date:; Sheet; <Doc>; <RevCode>; <Title>; Sunday, April 14, 2024

+3V3/TUN.../TX PTT OUT/MB_THERM/HF-VHF-SELECT2

+12V/TX PTT OUT/
HF-VHF-SELECT2/MB_THERM

RX IN LNA

SWR DET BACKW/SWR DET FORW

## 0.9-1.5V 时芯片进入 AB 类工作模式，0.5V 以下时

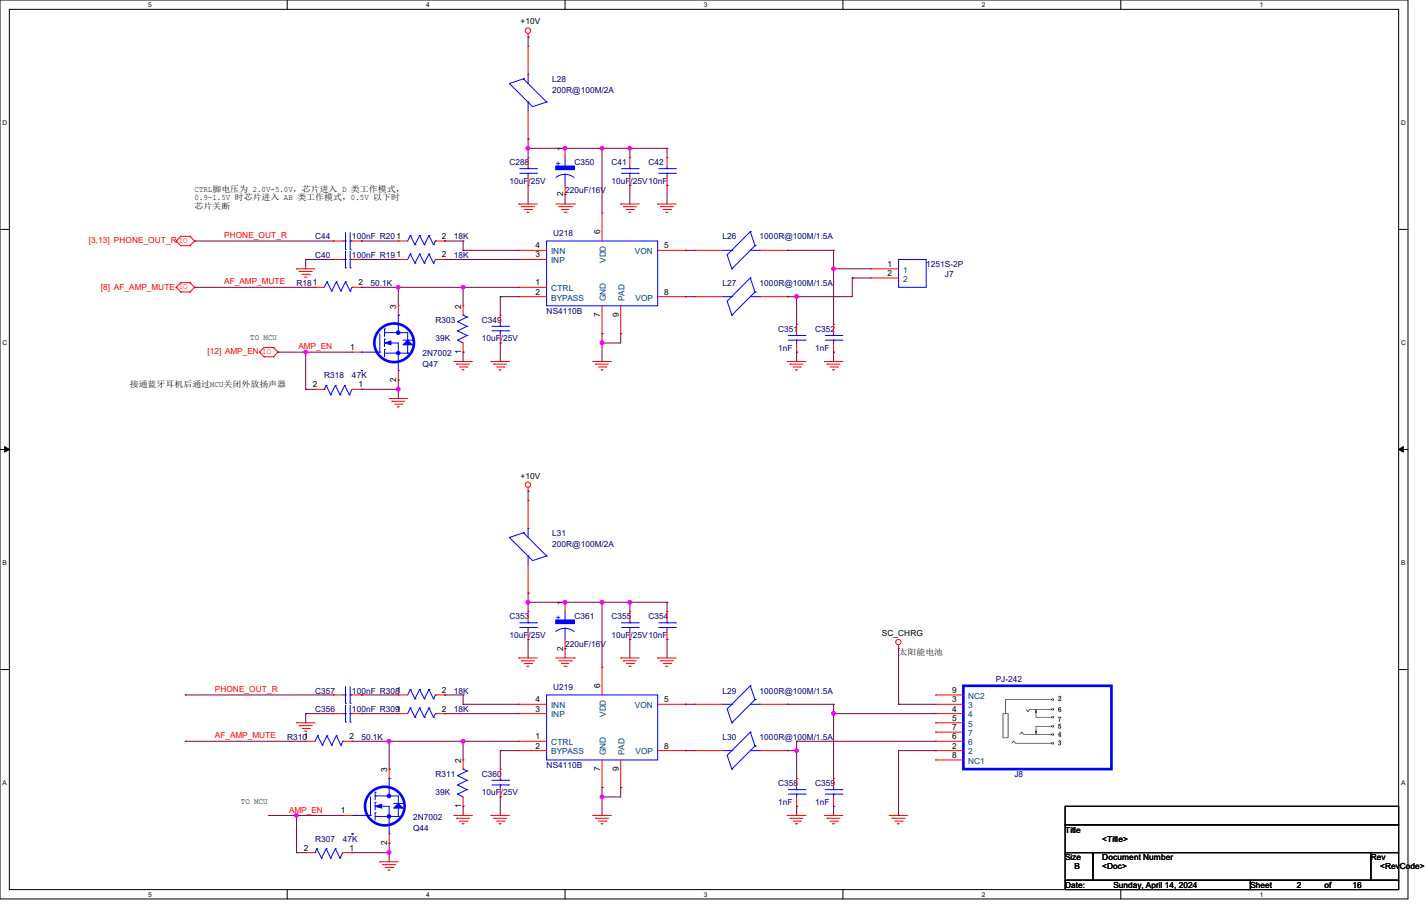
[picture p356: page 2]

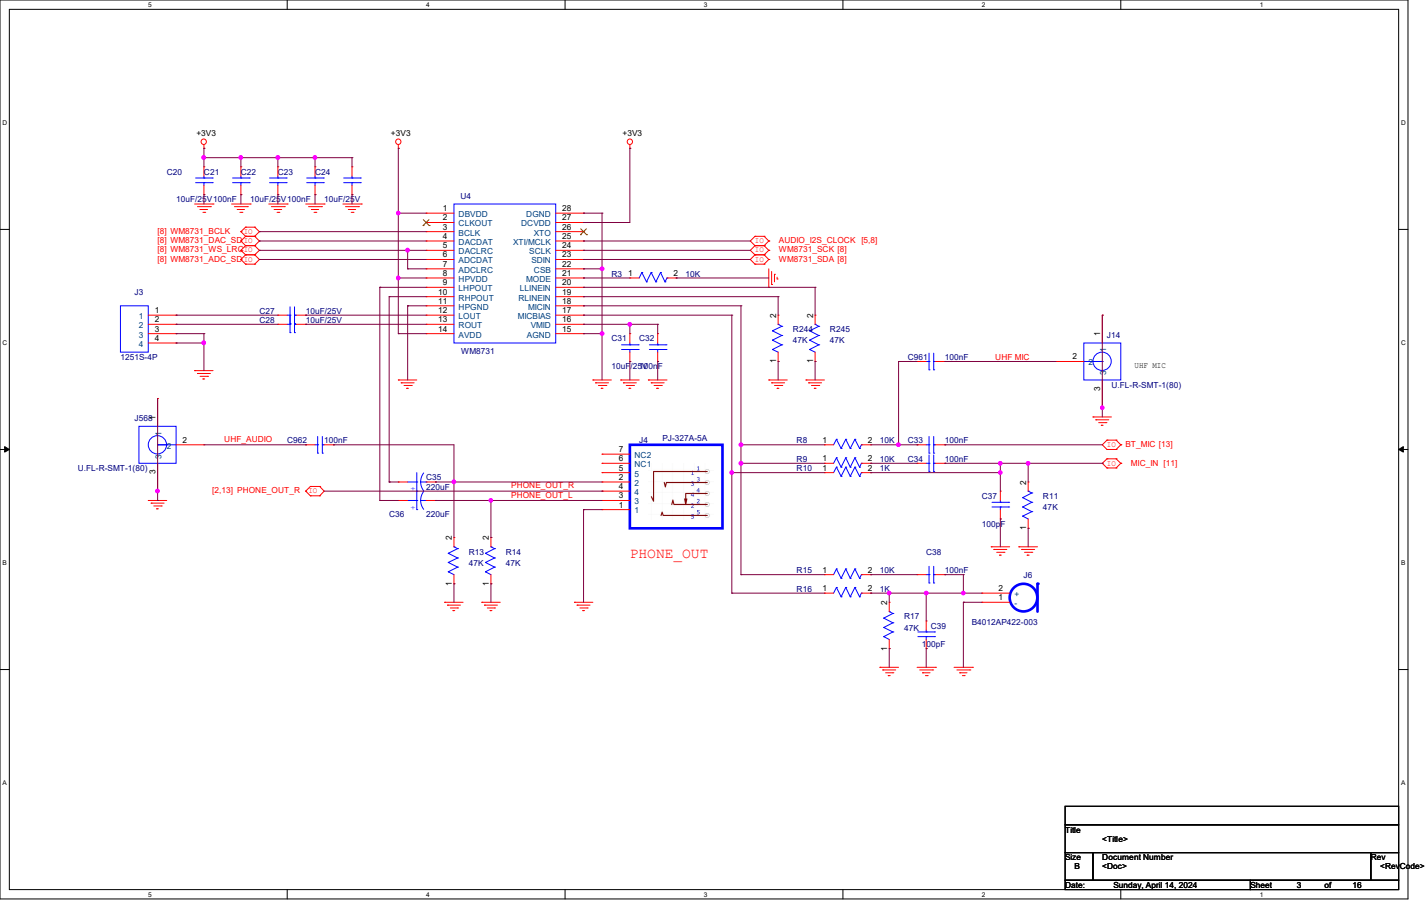
[picture p357: page 3]

13
14

## FAN

## TO AMP板

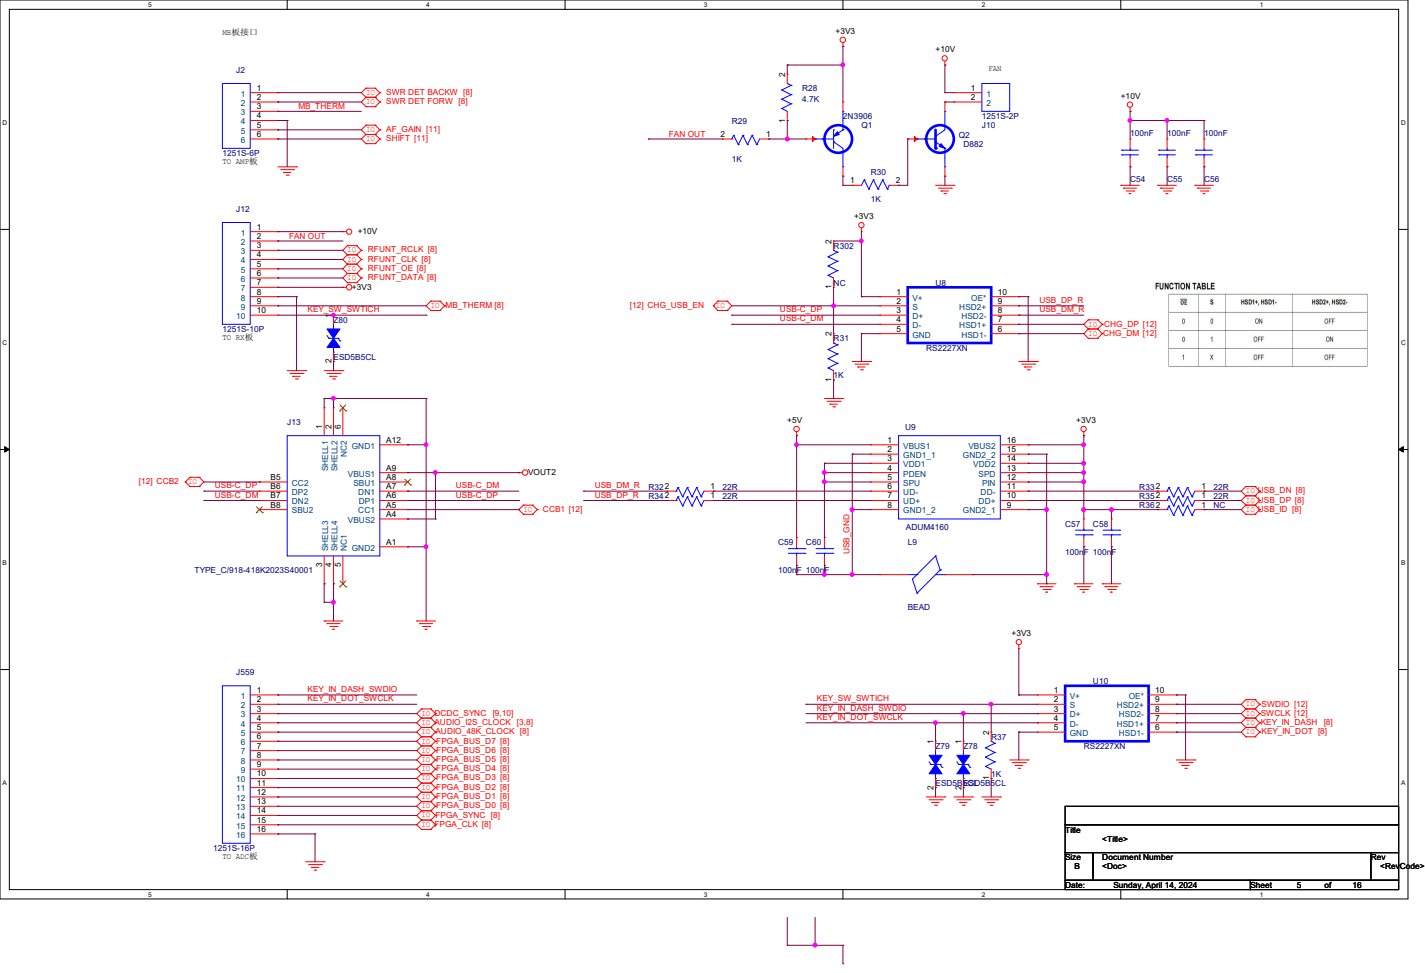
[picture p358: page 4]

IO SWR DET BACKW [8]
IO SWR DET FORW [8]

I

O

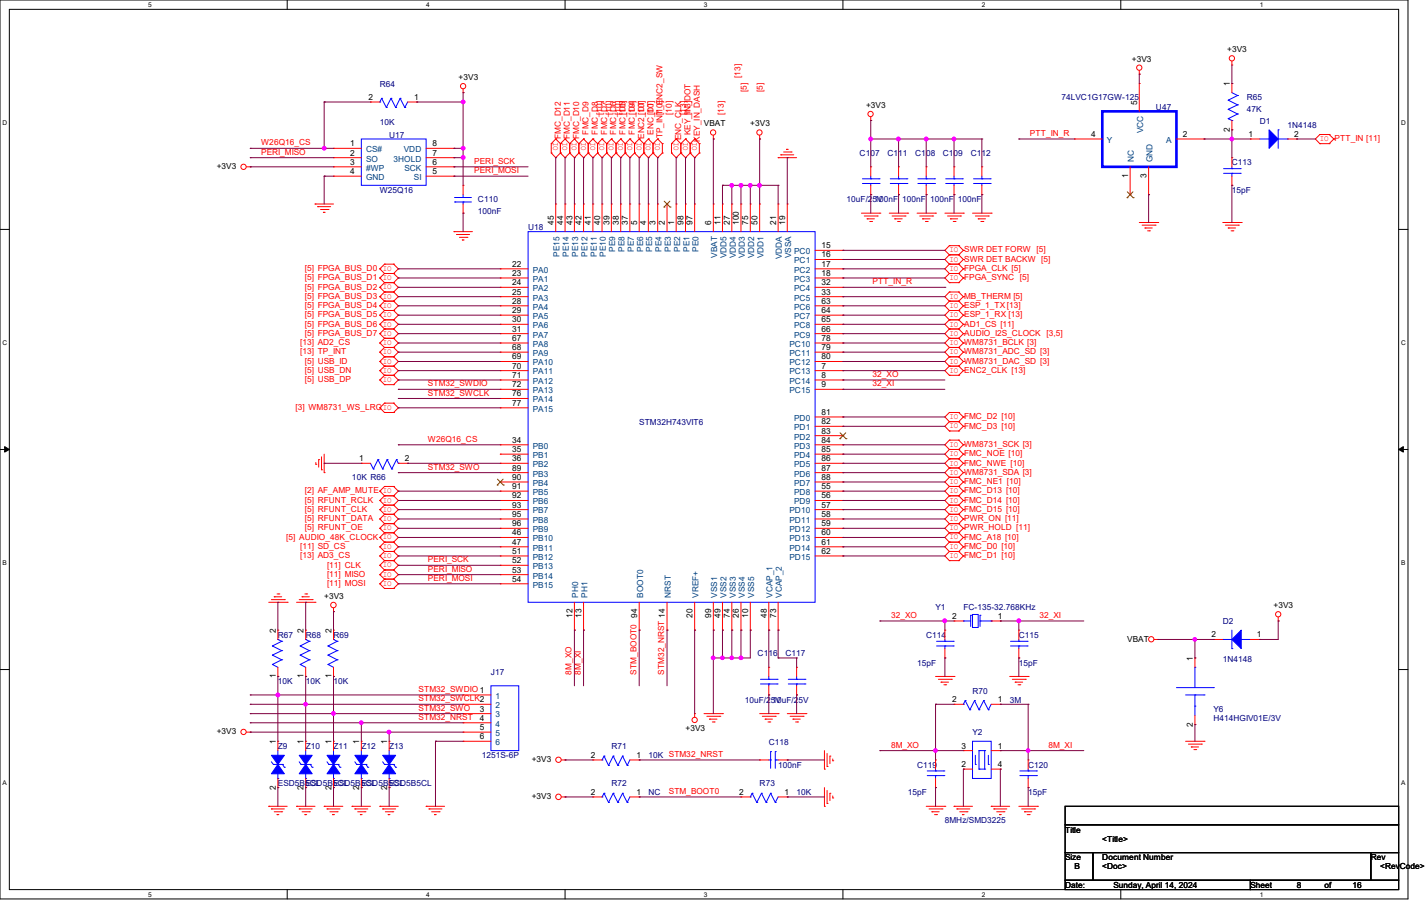
[picture p359: page 5]
DIO; IO FMC_D12; IO FMC_D11; IO FMC_D10; IO FMC_D9; IO FMC_D8; IO FMC_D7; IO FMC_D6; IO FMC_D5; IO FMC_D4; IO ENC2_DT; IO ENC_DT; IO TP_INT_ENC2_SW; IO ENC_CLK; MIS; IOKEY_IN_DASH; IO KEY_IN_DOT; Title Size; Title; ril 1; GND 3; VCC 5; VIT; VBAT 6; VDD5 11; VDD4 27; VDD3 100 VDD2 75; VDD1 50; BOOT0 94; NRST 14; VREF+ 20; VSS1 99; VSS2 49; VSS3 74; VSS4 26; VSS5 10; VCAP_1 48; VCAP_2 73 VDDA 21; VSSA 19; GIV; STM32_NRST STM³²_NRST STM_BOOT0; STM_BOOT0

## TO AMP板

0.8V

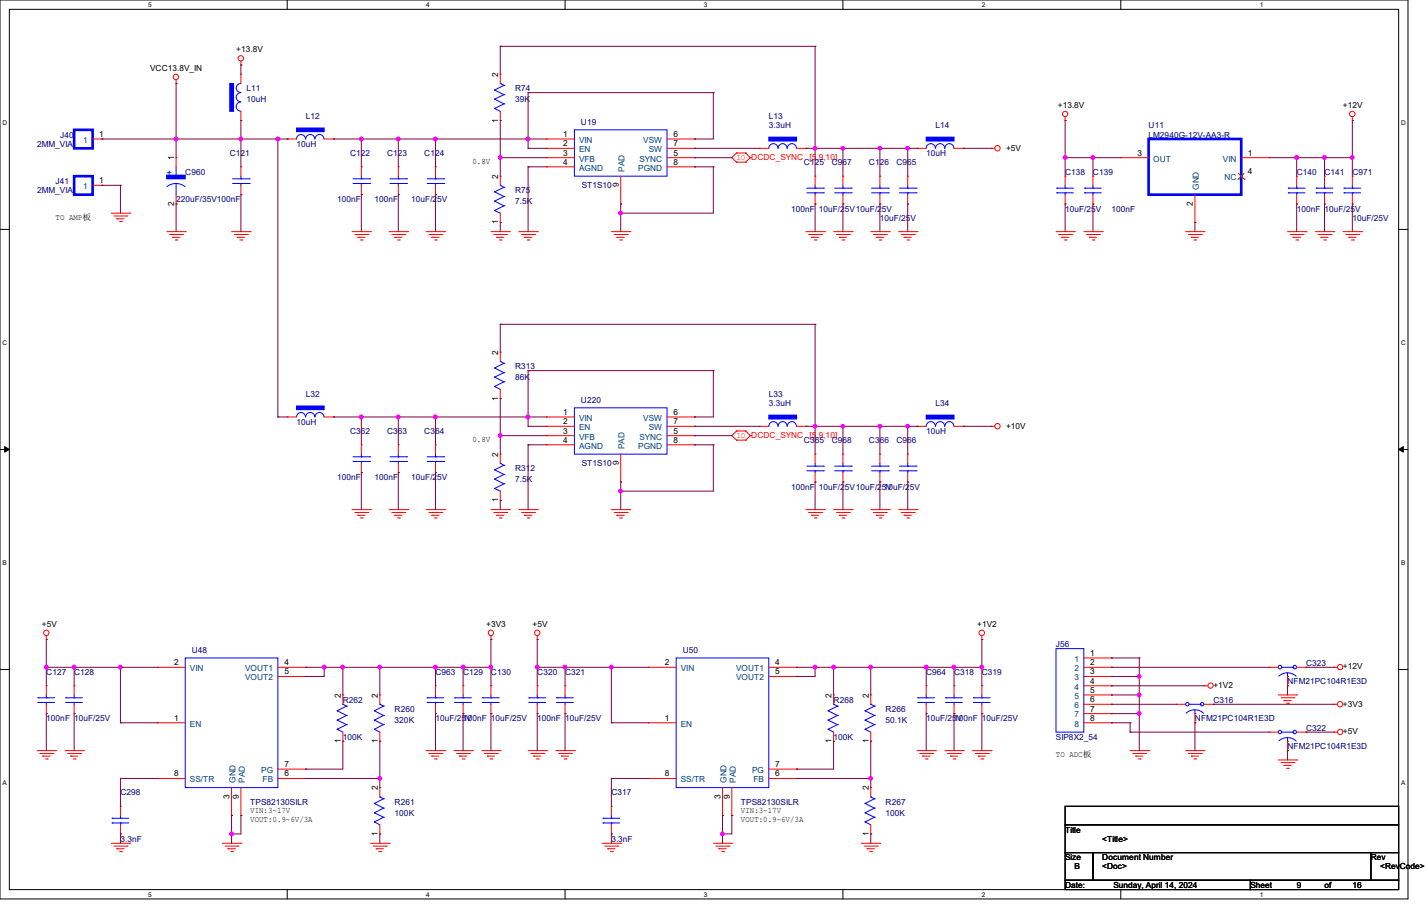
[picture p360: page 6]

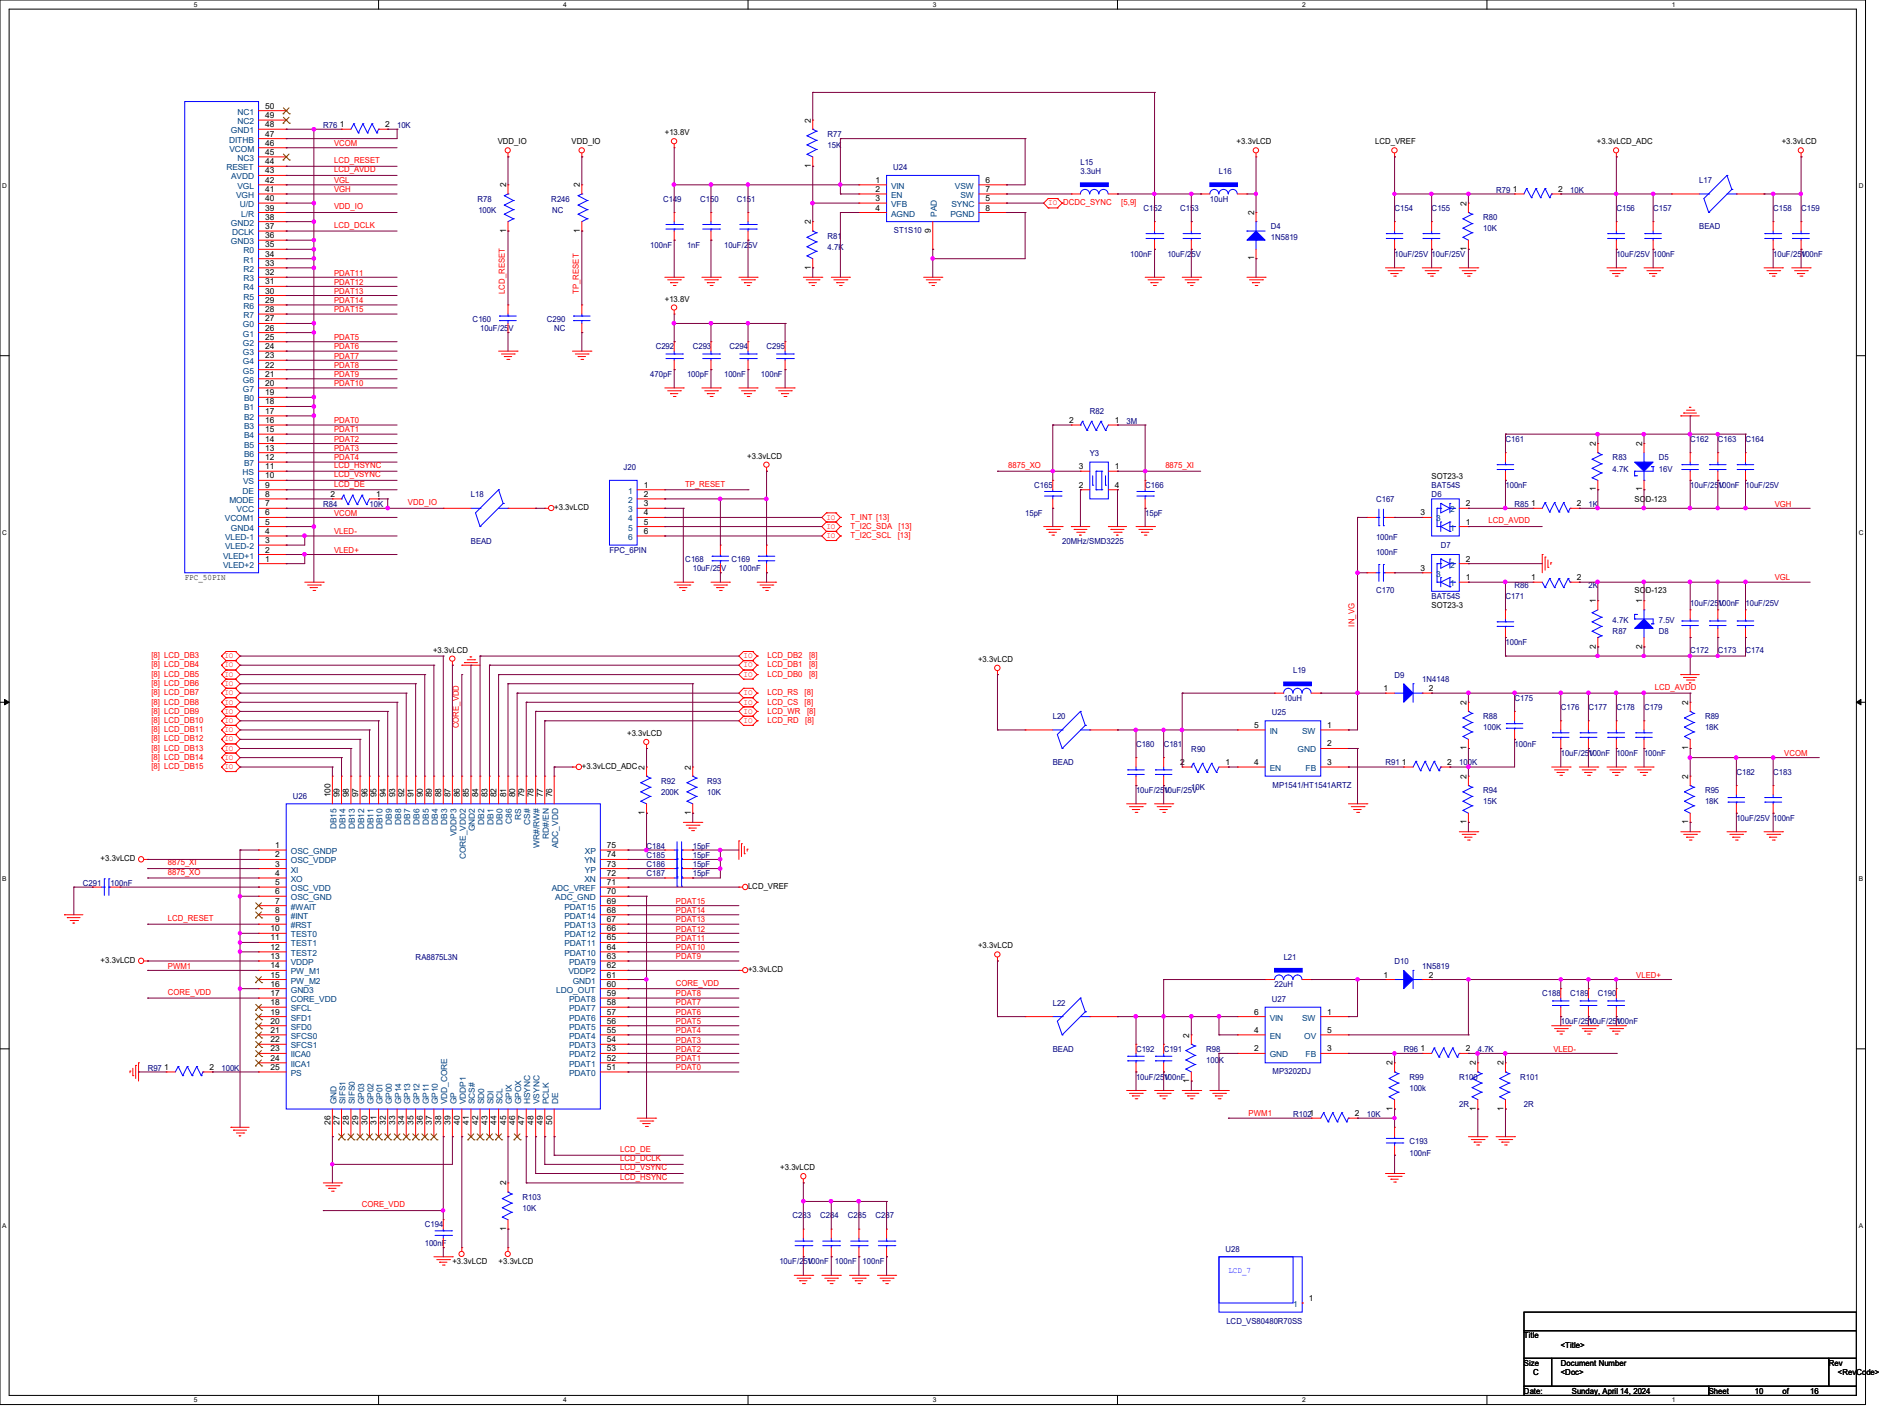
[picture p361: page 7]

EC2

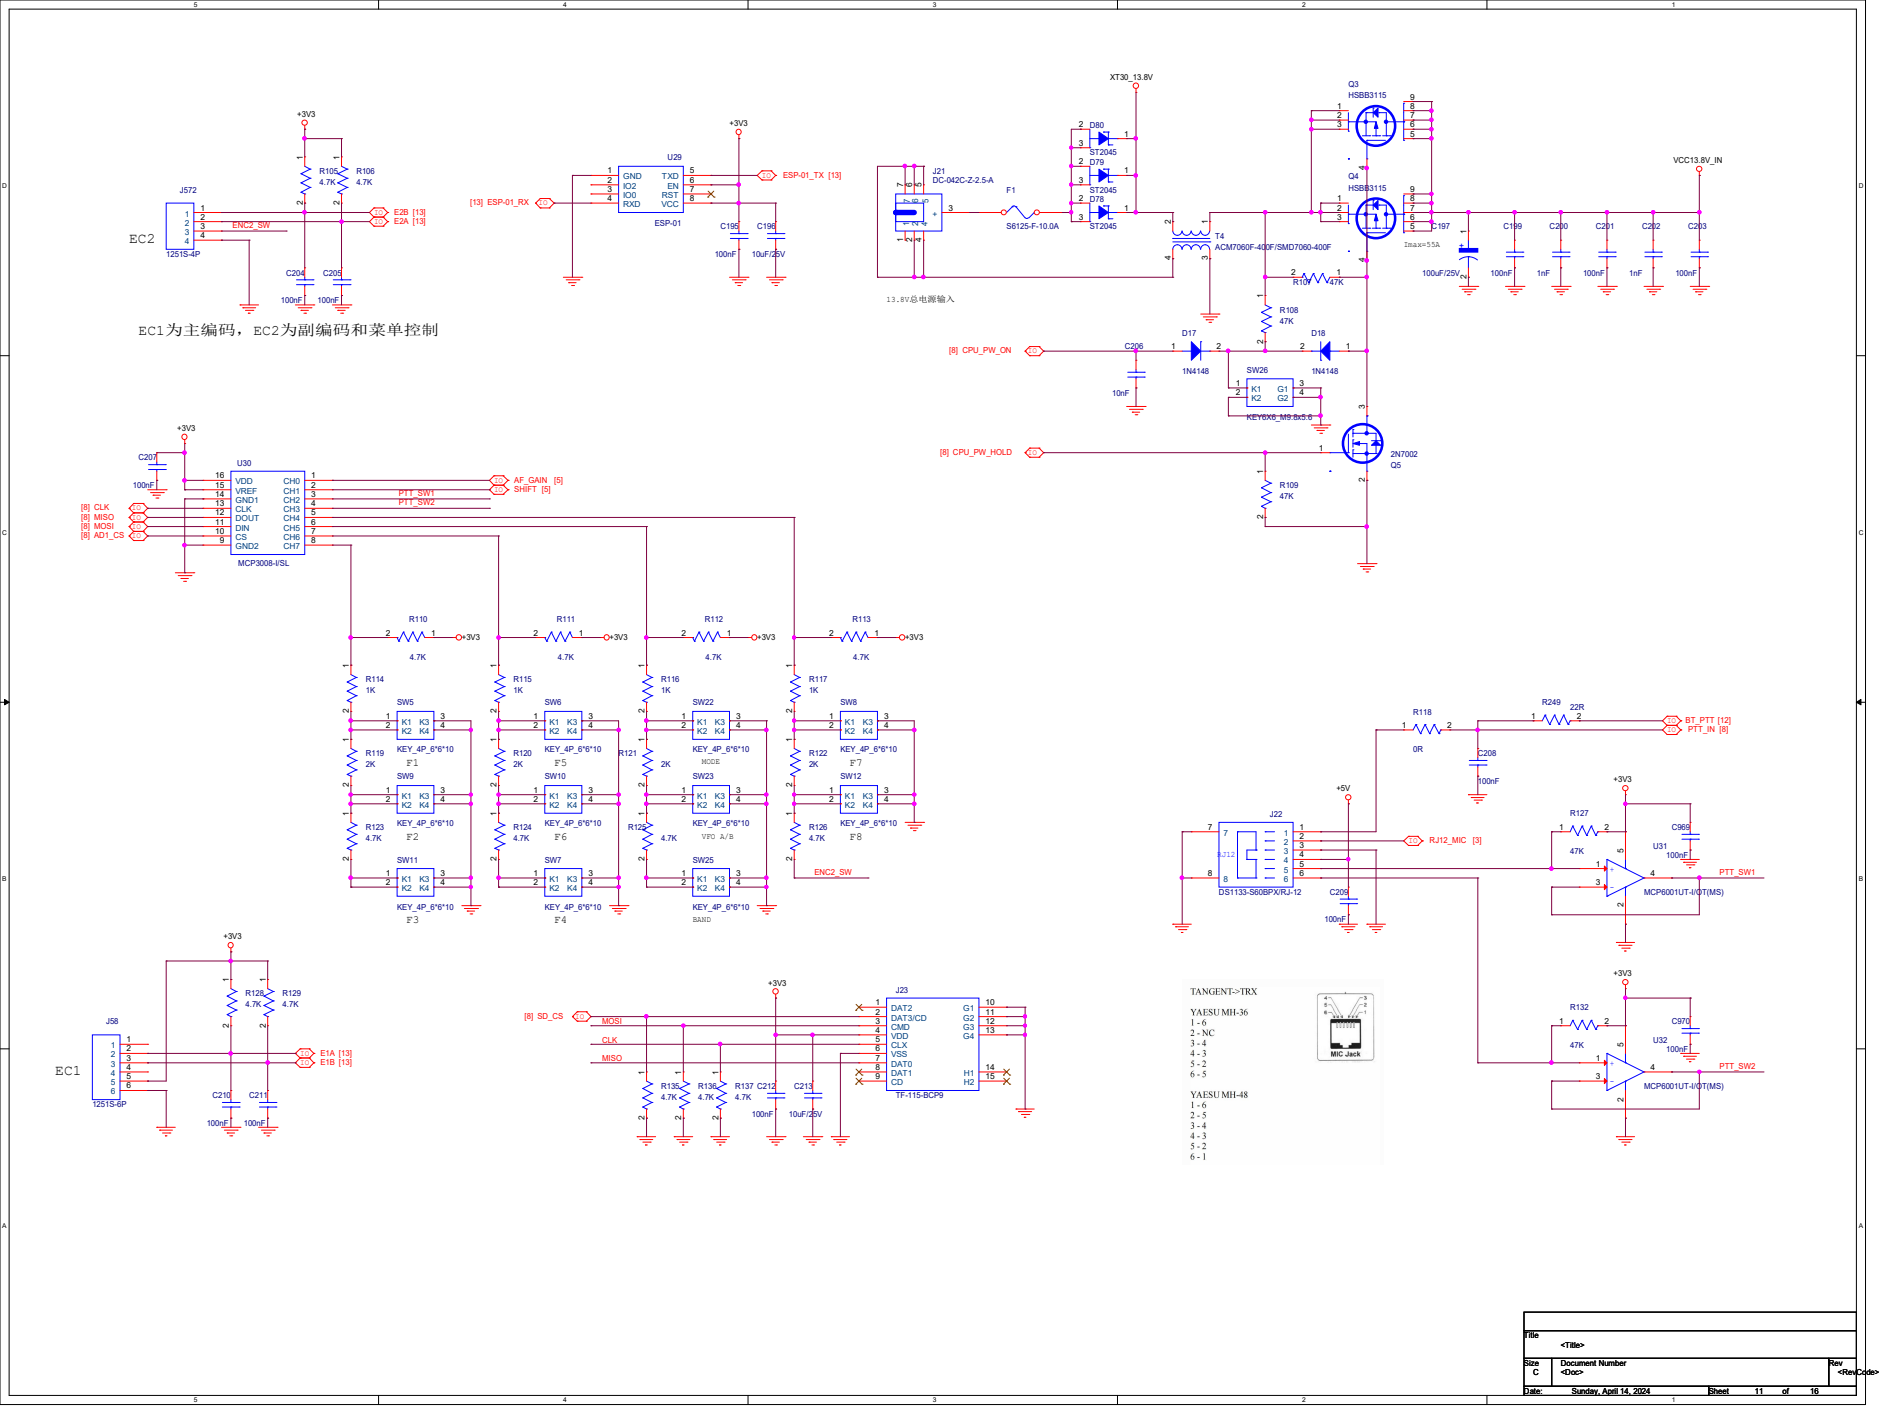
[picture p362: page 8]

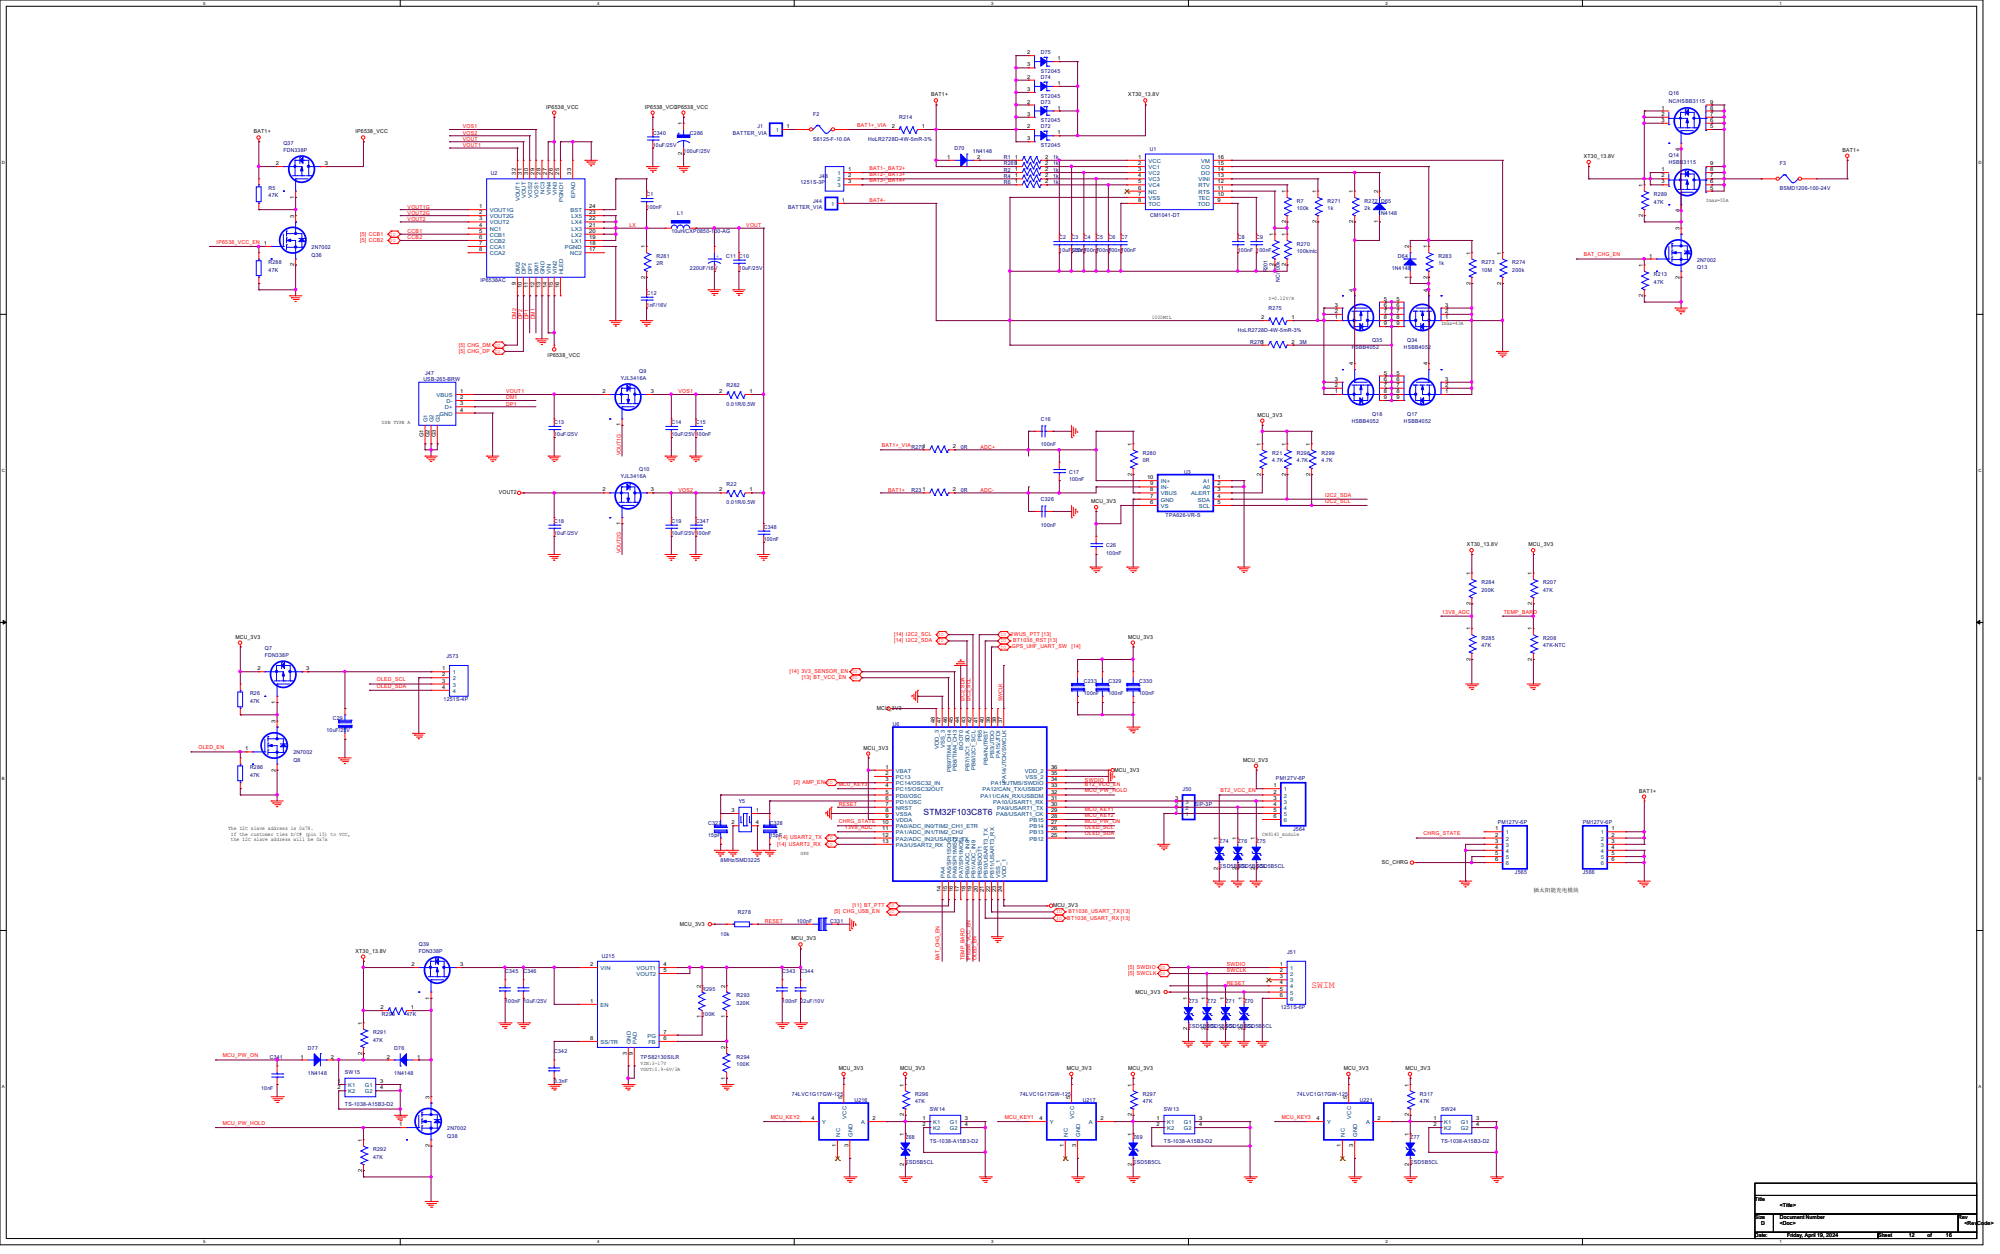
[picture p363: page 9]

The I2C slave address is 0x78.
If the customer ties D/C# (pin 15) to VCC,
the I2C slave address will be 0x7a

## SR_FRS_2WUS

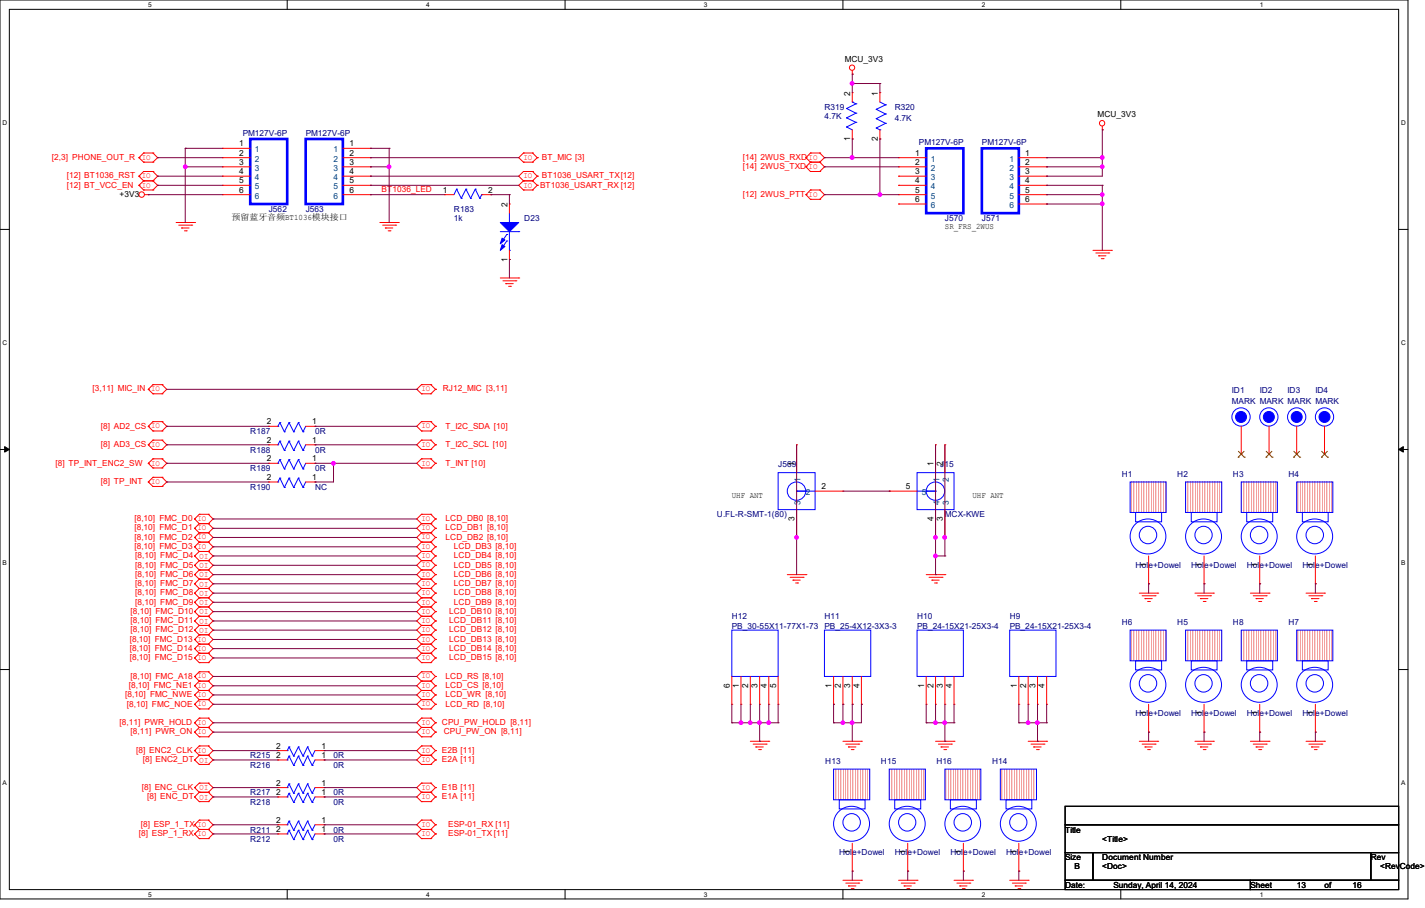
[picture p364: page 10]

1K1 2

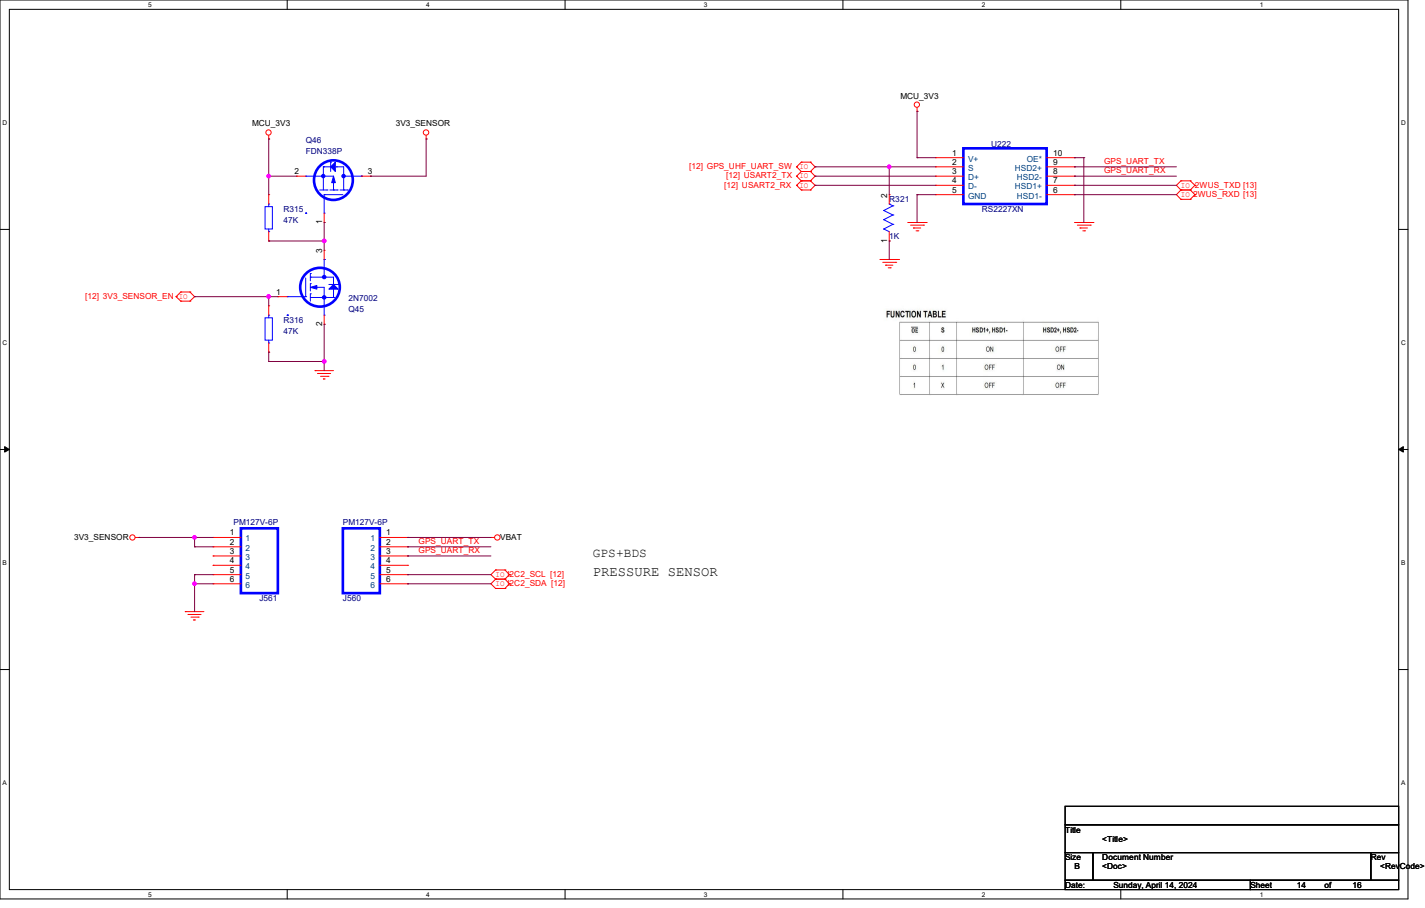
[picture p365: page 11]
