XGudron/UA3REO-DDC-Transceiver/Schematic/Wolf-DK102/Schematic/DK-102_RX_V01_240403.pdf

## 来自PA的RX 输出到ADC_DAC板

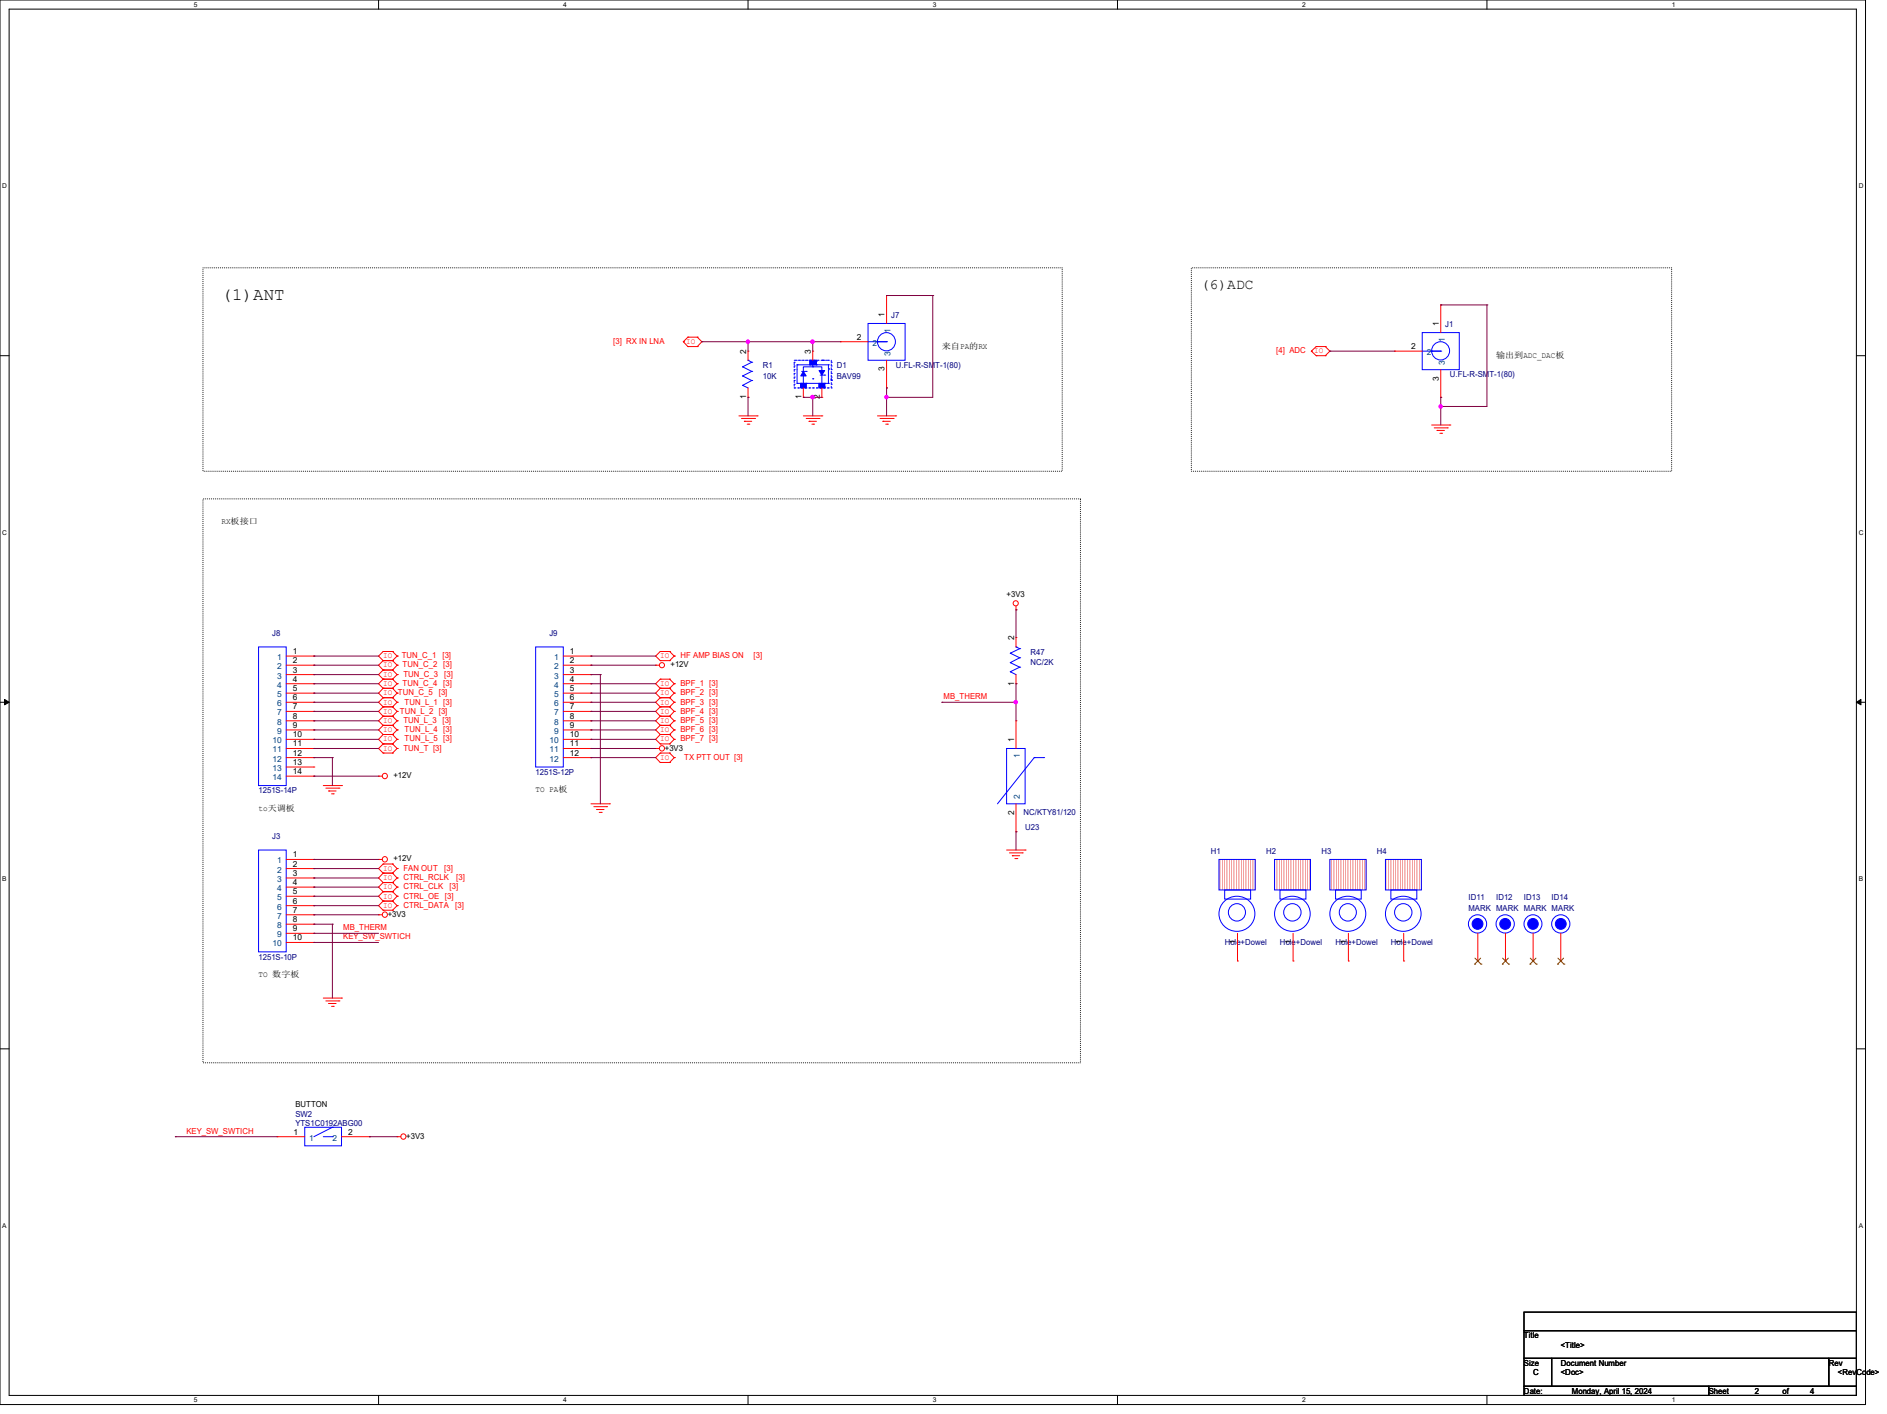
[picture p366: page 1]

## 5V/100mA

# (2)LNA

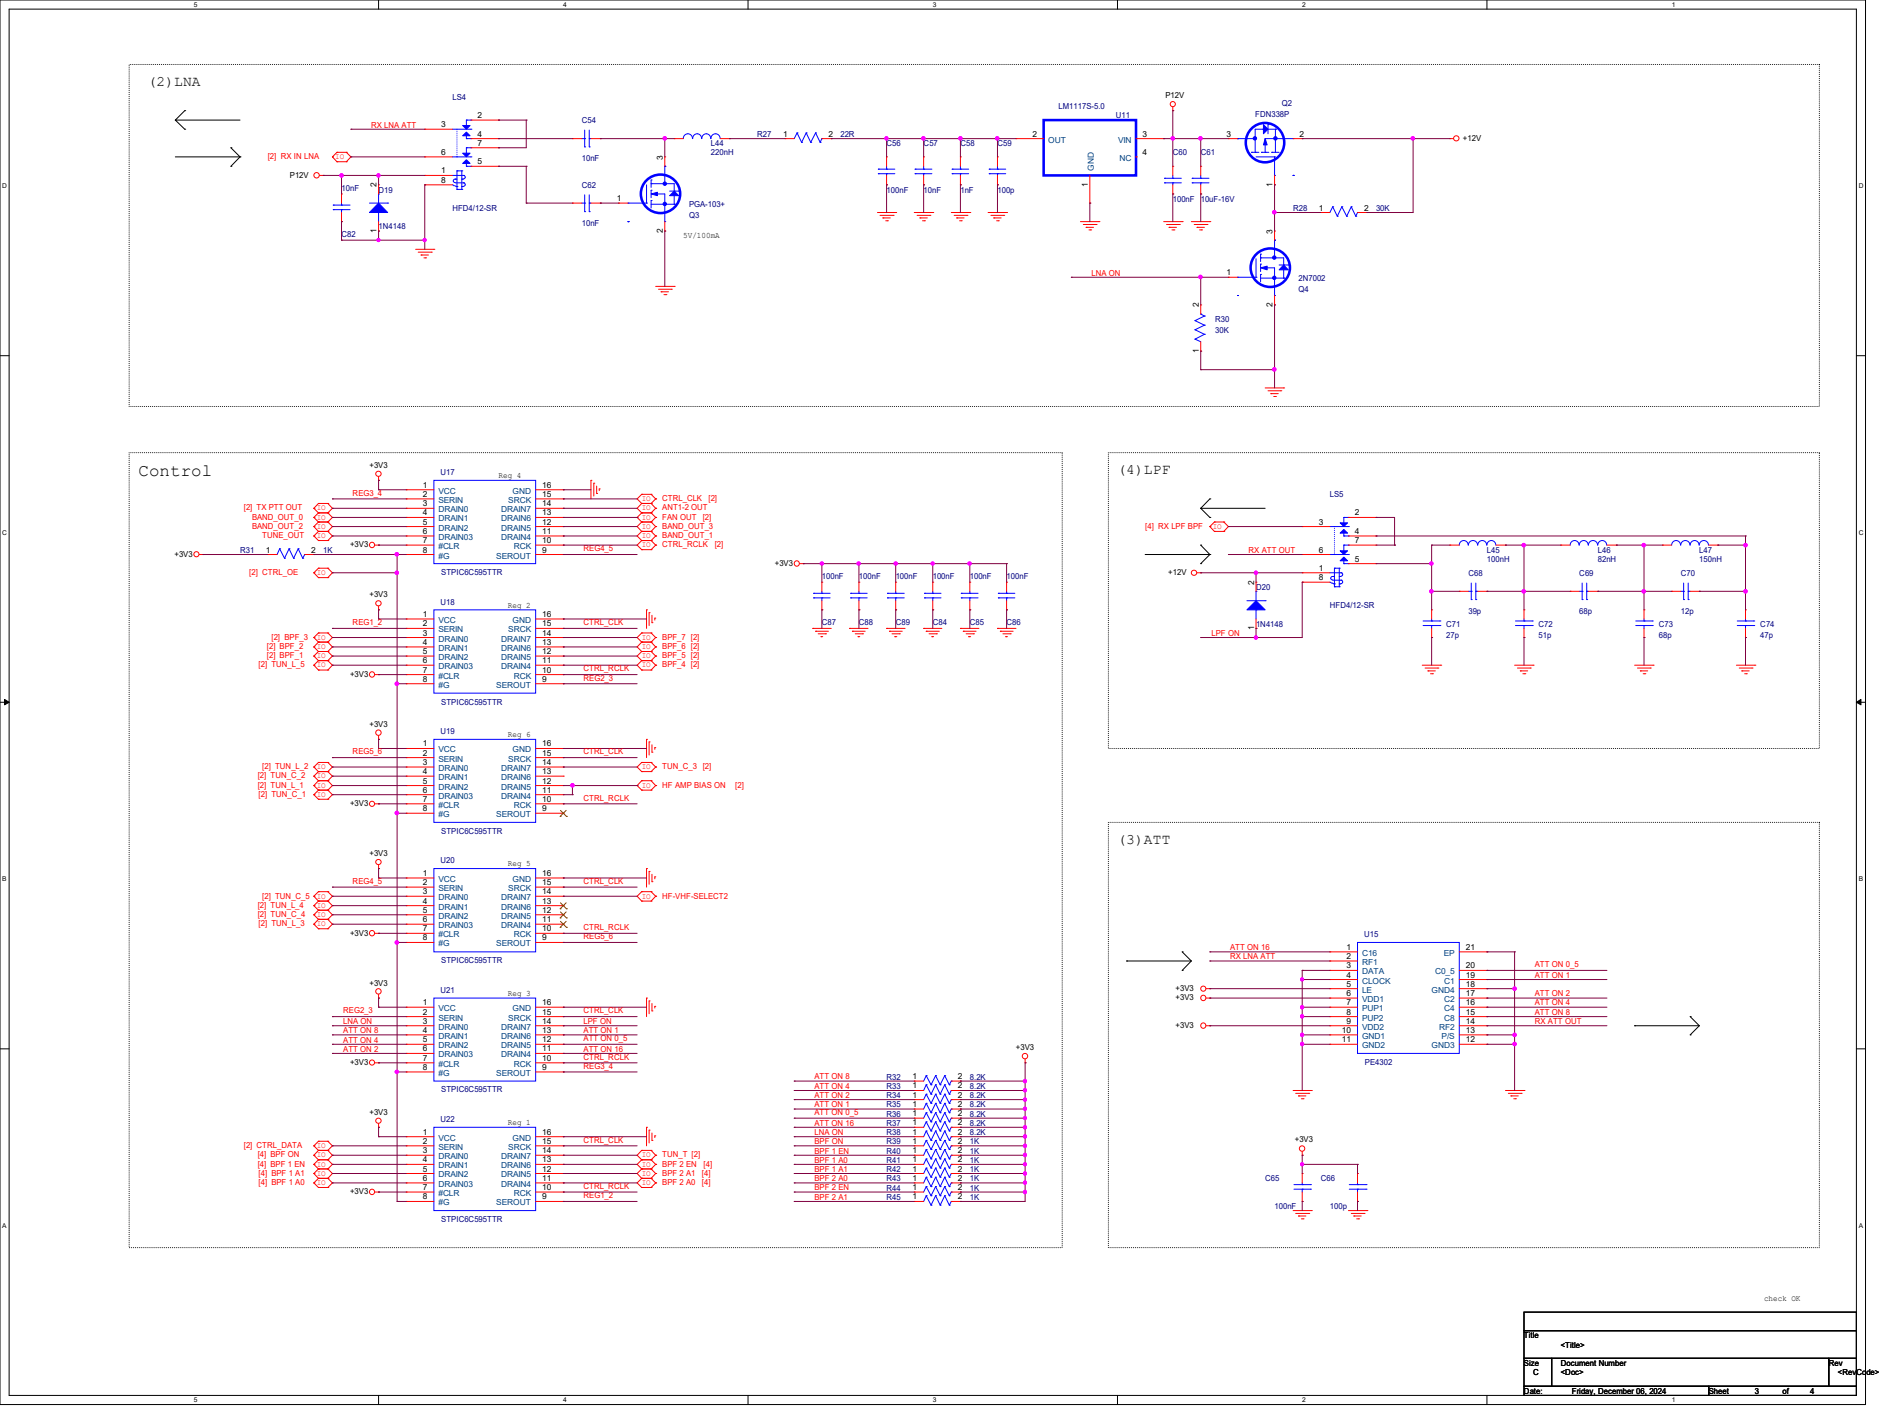
[picture p367: page 2]

[4] RX LPF BPF IO

# 0:RF2 to RFC 1:RF1 to RFC

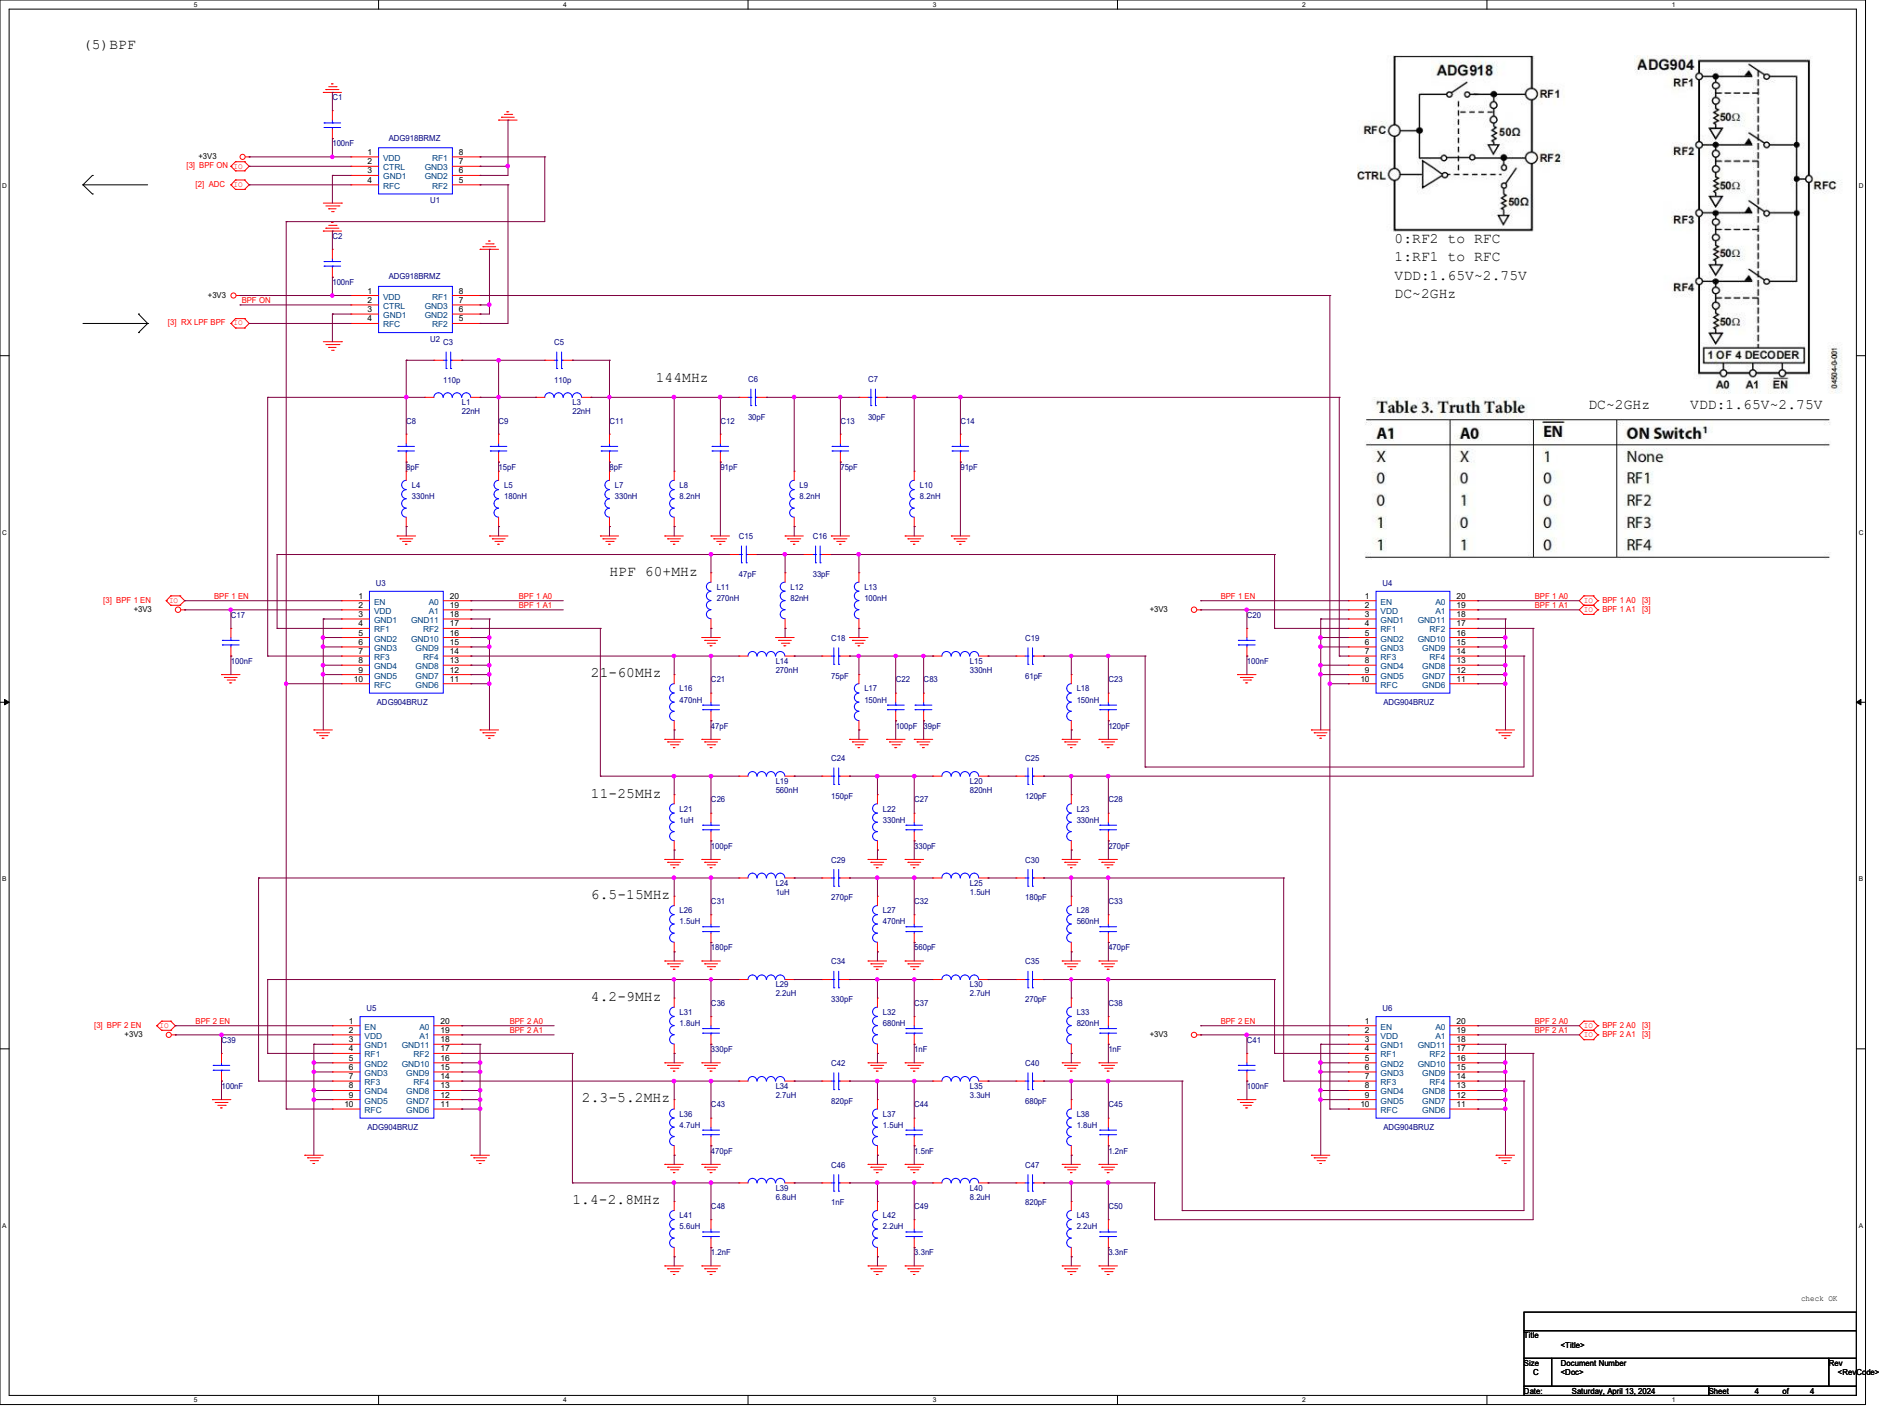
[picture p368: page 3]

[3] RX LPF BPF IO
