XGudron/UA3REO-DDC-Transceiver/Schematic/Wolf-2/Scheme/Schem W2-VHF_UHF_v03.PDF

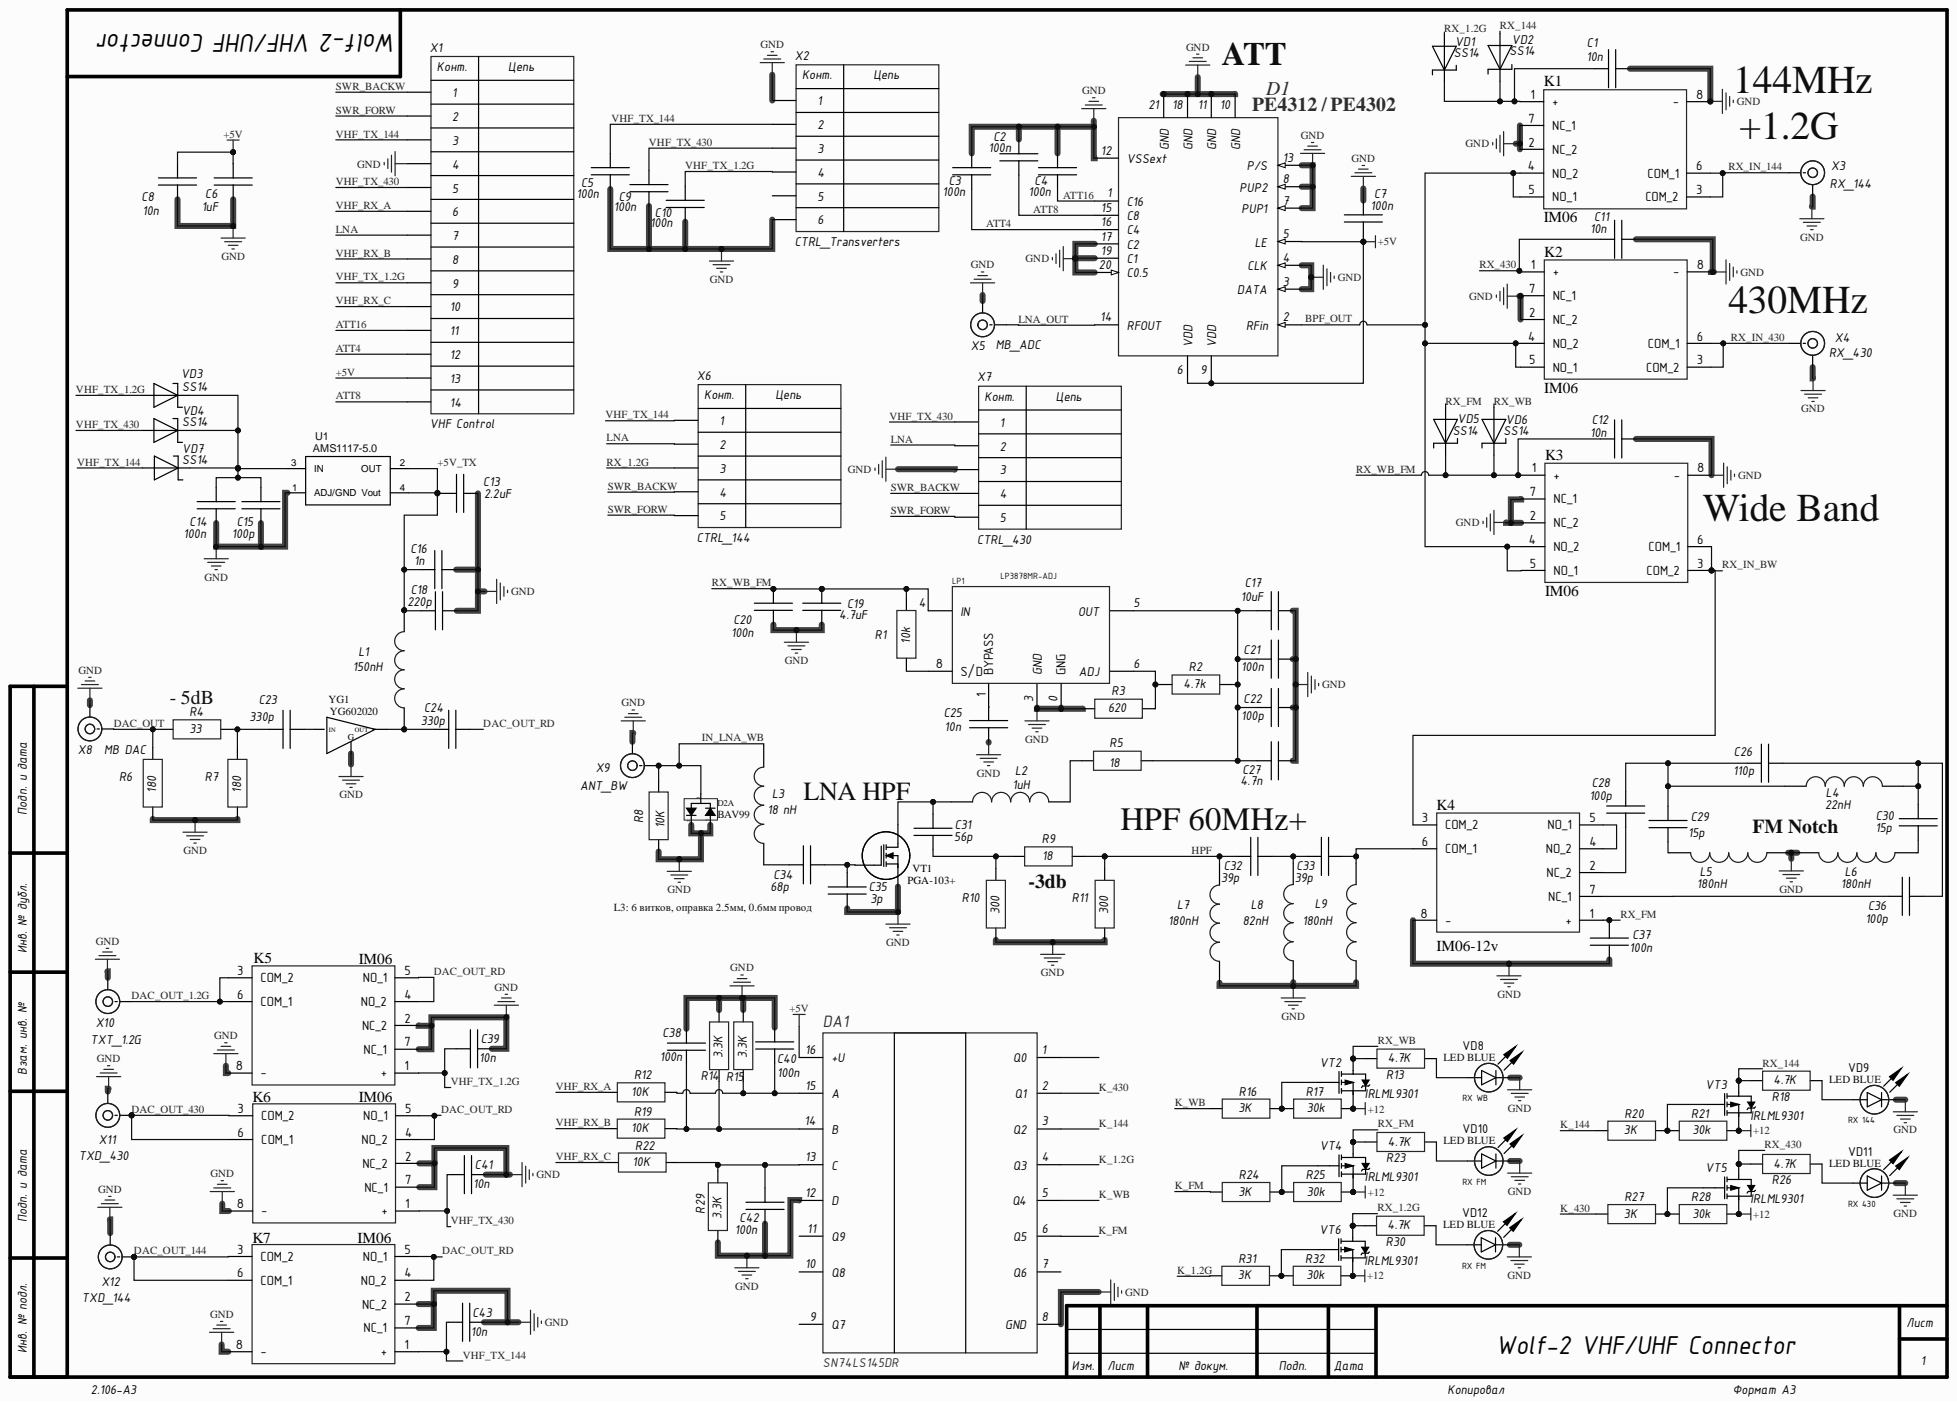
[picture p369: page 1]

C9 100n | ATT4 | ATT8 | ATT16

Инв. № подл. Инв. № дубл. Подп. и дата Взам. инв. № Подп. и дата

Wolf-2 VHF/UHF Connector

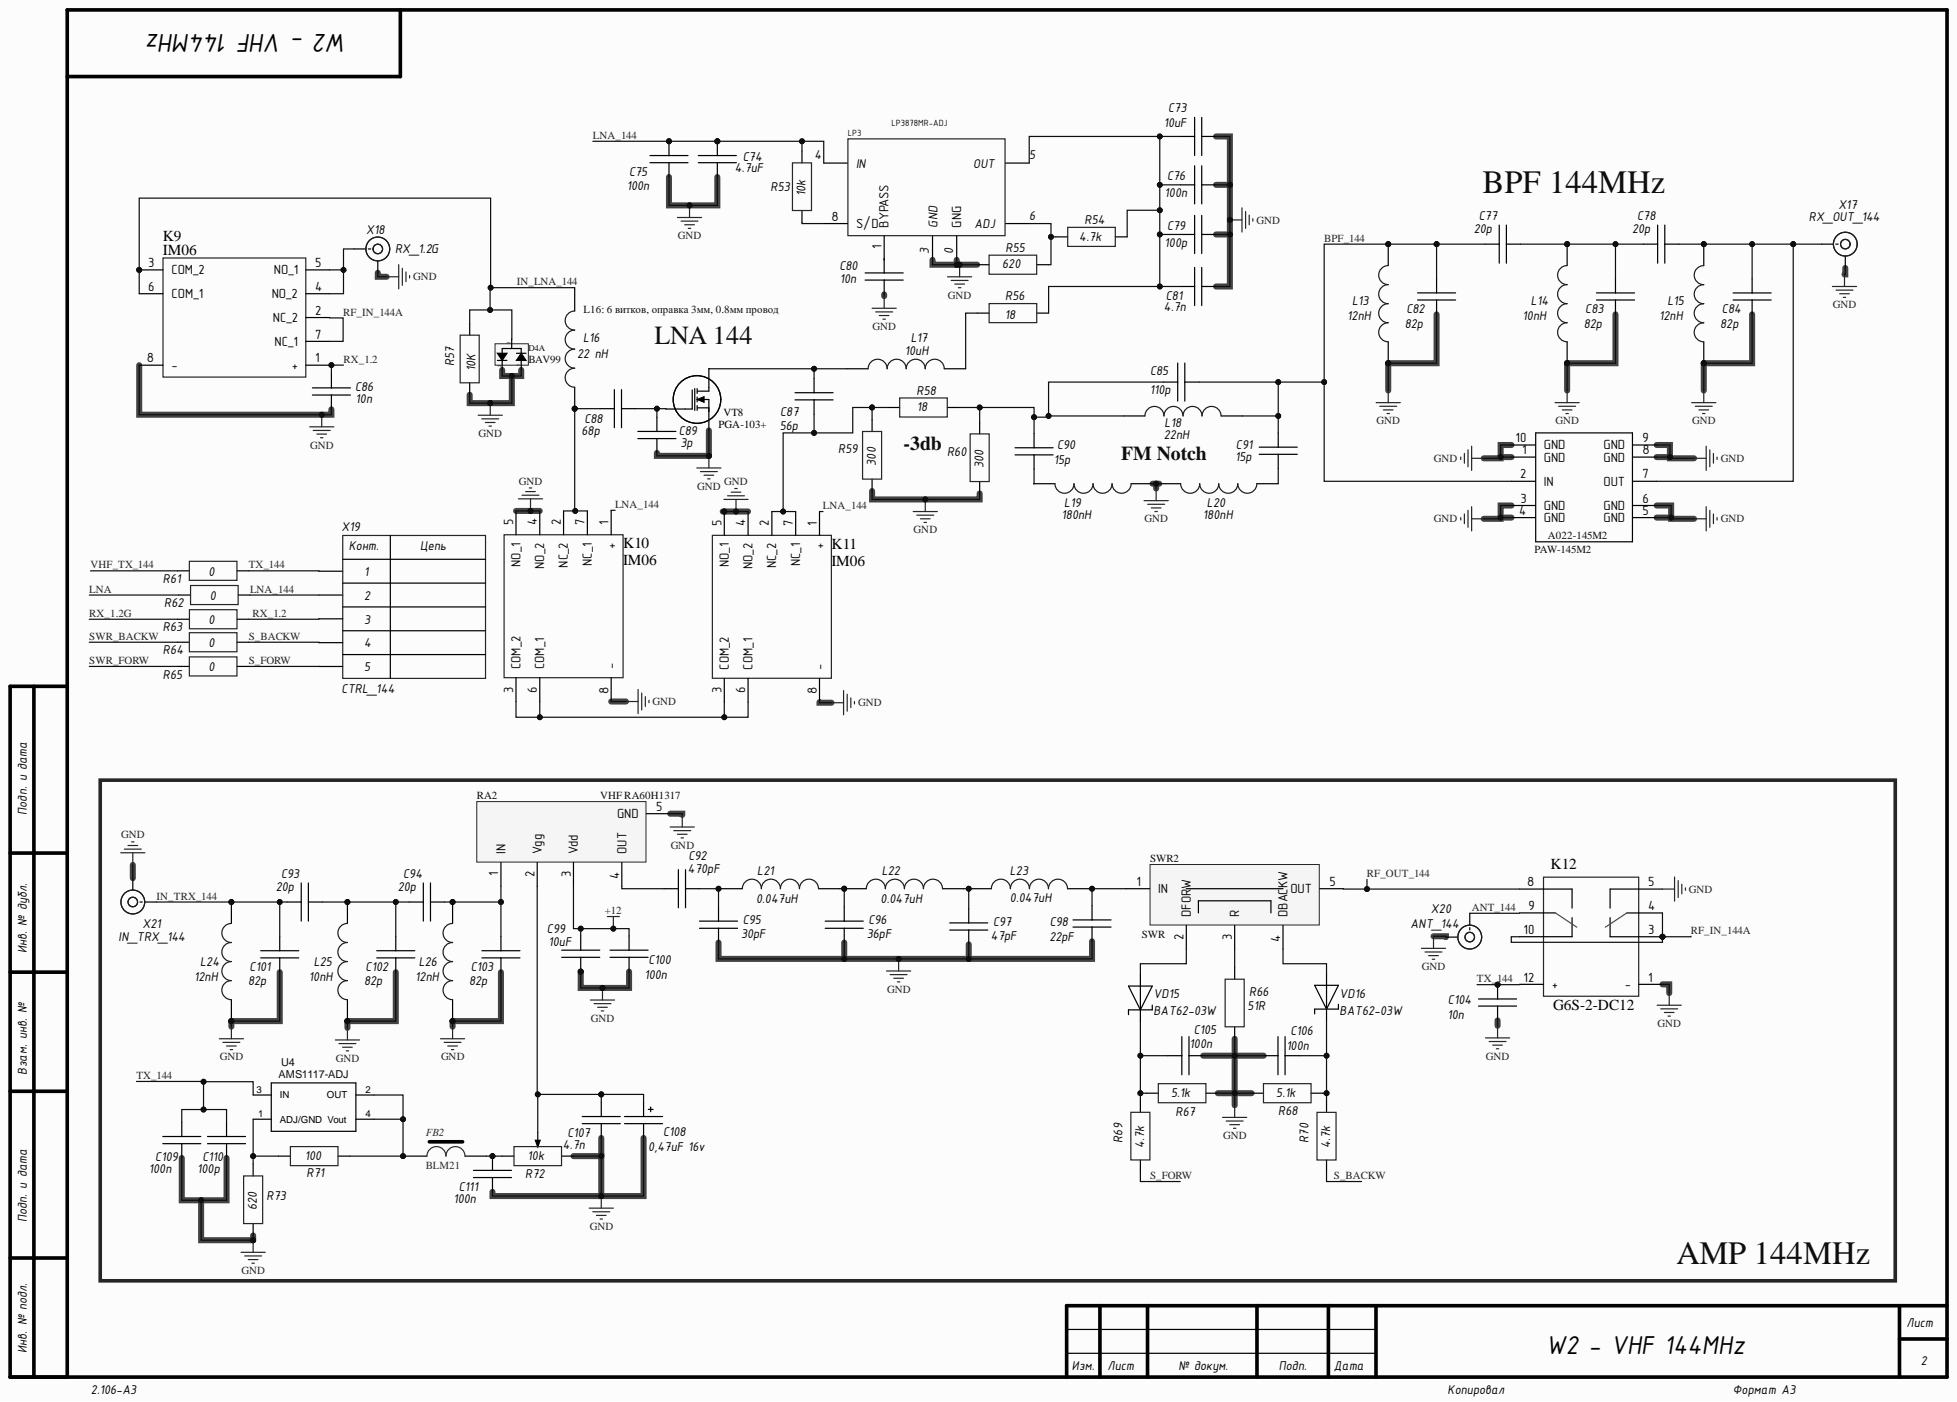
[picture p370: page 2]

Конт. | Цепь

Инв. № подл. Инв. № дубл. Подп. и дата Взам. инв. № Подп. и дата

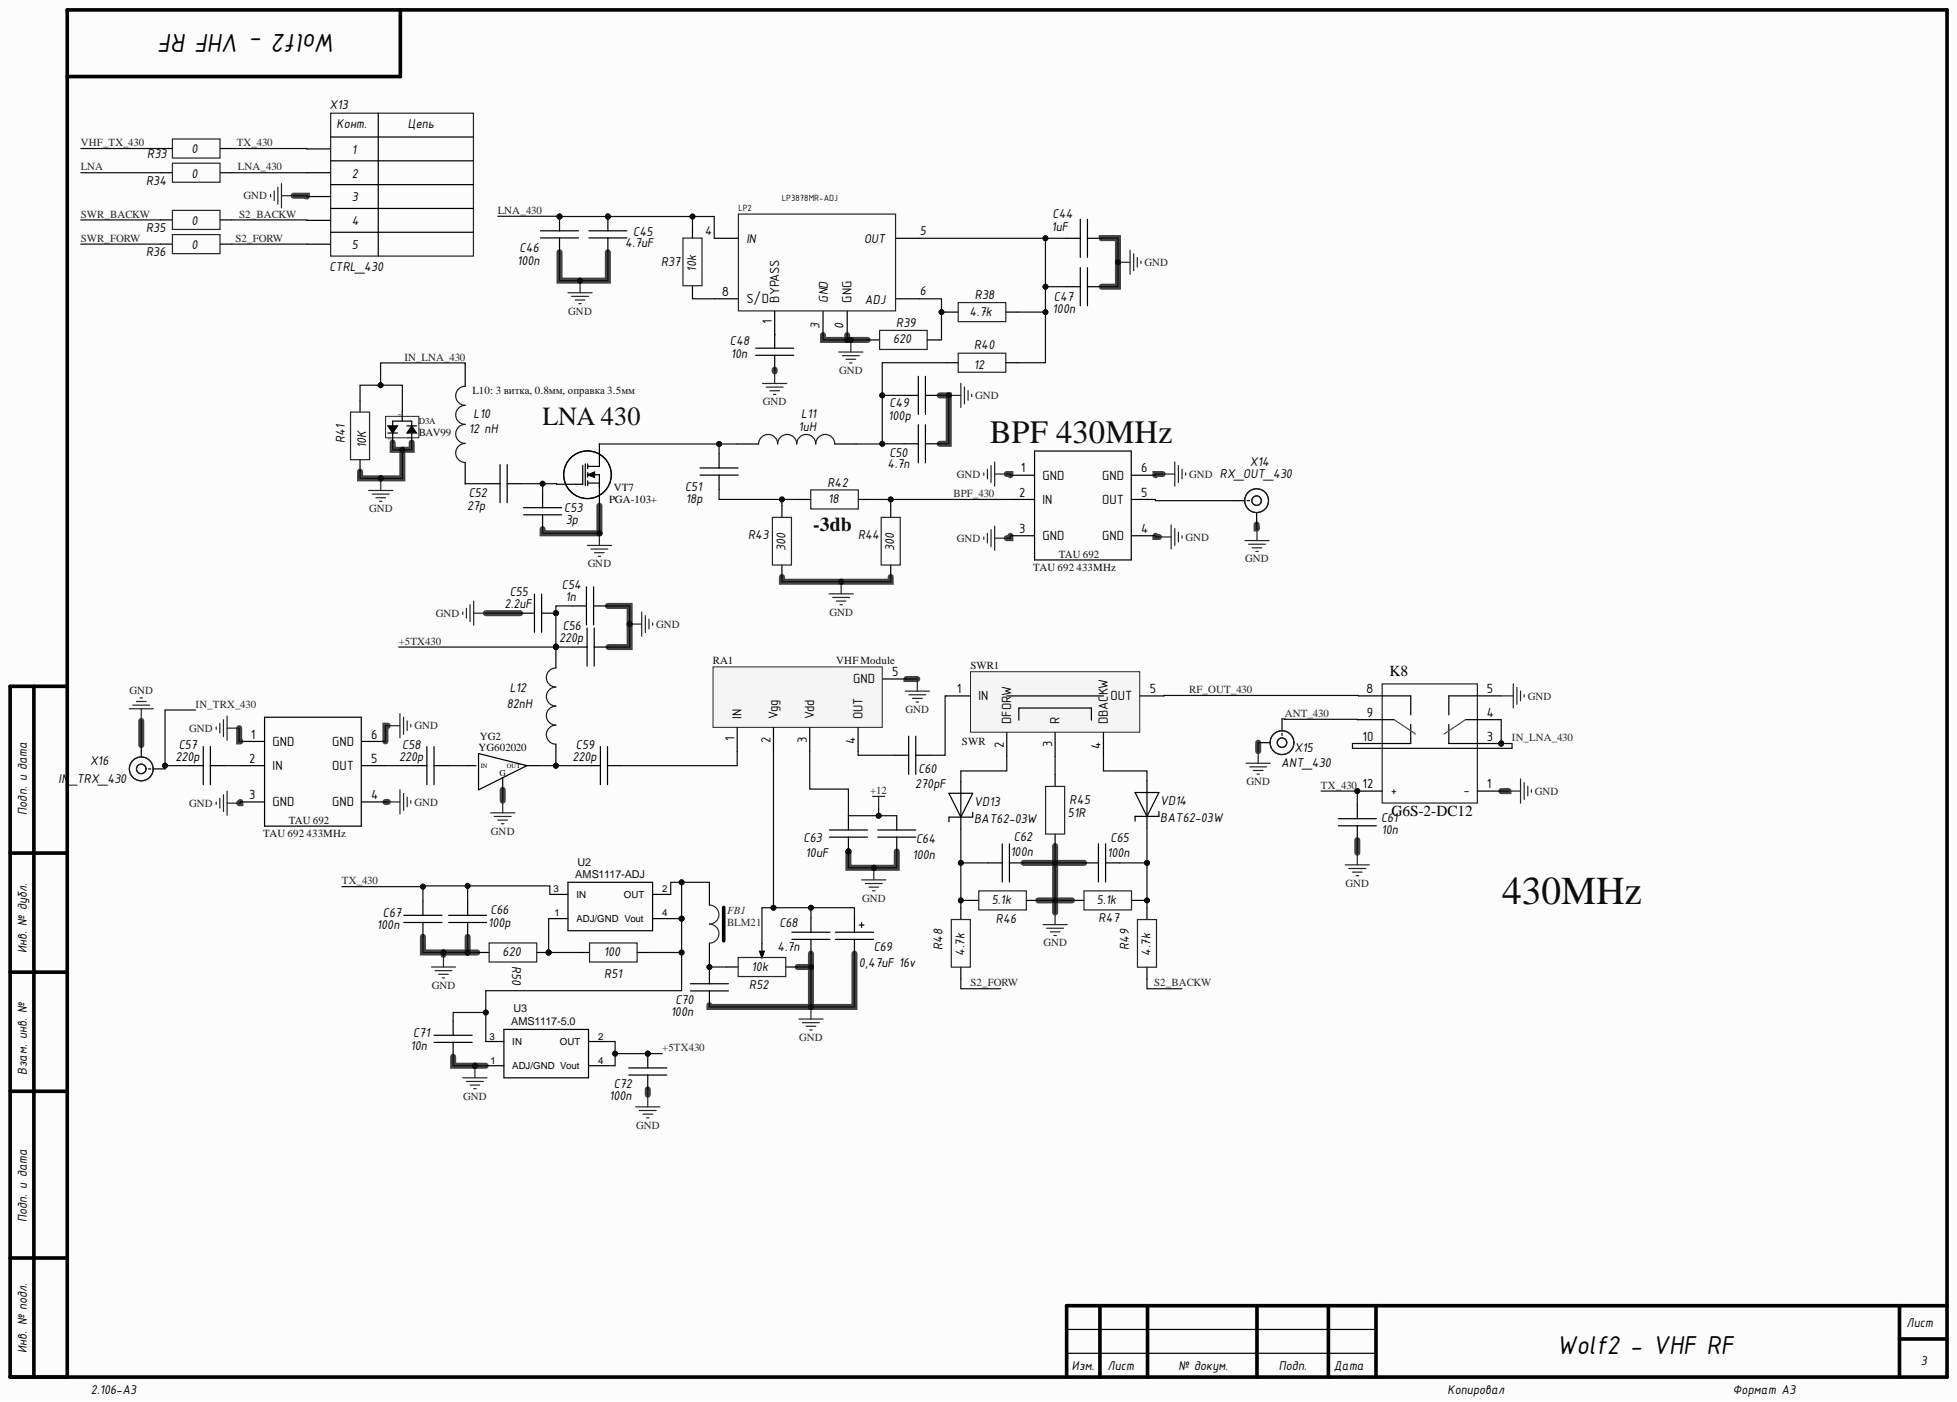
[picture p371: page 3]

Конт. | Цепь

OUT 4 GND 5 RA1 VHF Module

Инв. № подл. Инв. № дубл. Подп. и дата Взам. инв. № Подп. и дата

Comment | Description | Designator | Footprint | LibRef | Quantity
10n | | C1, C8, C11, C12, C25, C39, C41, C43, C48, C61, C71, C80, C86, C104 | CH0805C | Capacitor | 14
100n | | C2, C3, C4, C5, C7, C9, C10, C14, C20, C21, C37, C38, C40, C42, C46, C47, C62, C64, C65, C67, C70, C72, C75, C76, C100, C105, C106, C109, C111 | CH0805C | Capacitor | 29
1uF | | C6, C44 | CH0805C | Capacitor | 2
2.2uF | | C13, C55 | CH0805C | Capacitor | 2
100p | | C15, C22, C28, C36, C49, C66, C79, C110 | CH0805C | Capacitor | 8
1n | | C16, C54 | CH0805C | Capacitor | 2
10uF | | C17, C73 | CH0805C | Capacitor | 2
220p | | C18, C56, C57, C58, C59 | CH0805C | Capacitor | 5
4.7uF | | C19, C45, C74 | CH0805C | Capacitor | 3
330p | | C23, C24 | CH0805C | Capacitor | 2
110p | | C26, C85 | CH0805C | Capacitor | 2
4.7n | | C27, C50, C68, C81, C107 | CH0805C | Capacitor | 5
15p | | C29, C30, C90, C91 | CH0805C | Capacitor | 4
56p | | C31, C87 | CH0805C | Capacitor | 2
39p | | C32, C33 | CH0805C | Capacitor | 2
68p | | C34, C88 | CH0805C | Capacitor | 2
3p | | C35, C53, C89 | CH0805C | Capacitor | 3
18p | | C51 | CH0805C | Capacitor | 1
27p | | C52 | CH0805C | Capacitor | 1
270pF | | C60 | CH1206ATC | Capacitor | 1
10uF | | C63, C99 | CH1206C | Capacitor | 2
0,47uF 16v | | C69, C108 | TANTAL_B | TantalCap | 2
20p | | C77, C78, C93, C94 | CH0805C | Capacitor | 4
82p | | C82, C83, C84, C101, C102, C103 | CH0805C | Capacitor | 6
470pF | | C92 | CH1206ATC | Capacitor | 1
30pF | | C95 | CH1206ATC | Capacitor | 1
36pF | | C96 | CH1206ATC | Capacitor | 1
47pF | | C97 | CH1206ATC | Capacitor | 1
22pF | | C98 | CH1206ATC | Capacitor | 1
PE4312 / PE4302 | | D1 | 20-QFN (4x4) | PE4312-№1 | 1
BAV99 | | D2, D3, D4 | SOT23_132 | BAV99 | 3
SN74LS145DR | | DA1 | 16-SOIC | SN74LS145N | 1
BLM21 | | FB1, FB2 | CH0805L | FB-1 | 2
IM06 | | K1, K2, K3, K5, K6, K7, K9, K10, K11 | IM06 | IM06-V1 | 9
IM06-12v | | K4 | IM06 | IM06-V1 | 1
G6S-2-DC12 | | K8, K12 | G6S-2-DC12 | G6S-2-12VDC | 2
150nH | | L1 | CH1210L | Inductor | 1
1uH | | L2, L11 | CH1210L | Inductor | 2
18 nH | | L3 | CH1210L | Inductor | 1
22nH | | L4, L18 | CH1206L | Inductor | 2
180nH | | L5, L6, L7, L9, L19, L20 | CH1206L | Inductor | 6
82nH | | L8 | CH1206L | Inductor | 1
12 nH | | L10 | CH1210L | Inductor | 1
82nH | | L12 | CH1210L | Inductor | 1
12nH | | L13, L15, L24, L26 | CH1206L | Inductor | 4
10nH | | L14, L25 | CH1206L | Inductor | 2
22 nH | | L16 | CH1210L | Inductor | 1
10uH | | L17 | CH1210L | Inductor | 1
0.047uH | | L21, L22, L23 | T50-6 | Inductor ring | 3
LP3878MR-ADJ | LP3878-ADJ HSOP-8 | LP1, LP2, LP3 | SOP-8 gnd | LP3878-ADJ | 3
PAW-145M2 | PAW-A022-145M2 | PAW-1 | PAW-145M2 | PAW-145M2 | 1
10k | | R1, R12, R19, R22, R37, R53 | CH0805R | Resistor | 6
4.7k | | R2, R13, R18, R23, R26, R30, R38, R48, R49, R54, R69, R70 | CH0805R | Resistor | 12
620 | | R3, R39, R50, R55, R73 | CH0805R | Resistor | 5
33 | | R4 | CH0805R | Resistor | 1
18 | | R5, R56 | CH2010R | Resistor | 2
180 | | R6, R7 | CH0805R | Resistor | 2
10K | | R8, R41, R57 | CH2010R | Resistor | 3
18 | | R9, R42, R58 | CH0805R | Resistor | 3
300 | | R10, R11, R43, R44, R59, R60 | CH0805R | Resistor | 6
3.3K | | R14, R15, R29 | CH0805R | Resistor | 3
3K | | R16, R20, R24, R27, R31 | CH0805R | Resistor | 5
30k | | R17, R21, R25, R28, R32 | CH0805R | Resistor | 5
0 | | R33, R34, R35, R36, R61, R62, R63, R64, R65 | CH1206R | Resistor | 9
12 | | R40 | CH2010R | Resistor | 1
51R | | R45, R66 | CH1206R | Resistor | 2
5.1k | | R46, R47, R67, R68 | CH0805R | Resistor | 4
100 | | R51, R71 | CH0805R | Resistor | 2
10k | | R52, R72 | RES: 3296W | ADJ resistor | 2
VHF Module | RA80H | RA1 | RA80H | RA80H | 1
VHF RA60H1317 | RA80H | RA2 | RA80H | RA80H | 1
SWR | SWR_VHF | SWR1, SWR2 | SWR_VHF | SWR_VHF | 2
TAU692 433MHz | TAU692 433MHz | TAU1, TAU2 | TAU-692 433 MHz | TAU692 433MHz | 2
1117-5.0 | LT1117CST-5.0 | U1, U3 | LT1117CST-3.3 | LT1117CST-3.3 | 2
1117-ADJ | LT1117CST-ADJ | U2, U4 | LT1117CST-3.3 | LT1117CST-3.3 | 2
SS14 | | VD1, VD2, VD3, VD4, VD5, VD6, VD7 | SMA | Diod Schottky | 7
LED BLUE | | VD8, VD9, VD10, VD11, VD12 | LED: 0805B | LED_single | 5
BAT62-03W | | VD13, VD14, VD15, VD16 | SOD323 | Diod Schottky | 4
PGA-103+ | | VT1, VT7, VT8 | SOT89_321_PGA103 | N | 3
IRLML9301 | Mosfet | VT2, VT3, VT4, VT5, VT6 | SOT23_132 | IRLML9301 | 5
VHF Control | | X1 | CON: IDC-14MS | 14-Connector | 1
CTRL_Transverters | | X2 | CON: PBS-6 | 6-Connector | 1
RX_144 | RF | X3 | CON: u.Fl | u.Fl | 1
RX_430 | RF | X4 | CON: u.Fl | u.Fl | 1
MB_ADC | RF | X5 | CON: SMA | SMA | 1
CTRL_144 | | X6, X19 | CON: PLS-5 | 5-Connector | 2
CTRL_430 | | X7, X13 | CON: PLS-5 | 5-Connector | 2
MB DAC | RF | X8 | CON: SMA | SMA | 1
ANT_BW | RF | X9 | CON: SMA | SMA | 1
TXT_1.2G | RF | X10 | CON: SMA | SMA | 1
TXD_430 | RF | X11 | CON: u.Fl | u.Fl | 1
TXD_144 | RF | X12 | CON: u.Fl | u.Fl | 1
RX_OUT_430 | RF | X14 | CON: u.Fl | u.Fl | 1
ANT_430 | RF | X15 | CON: SMA | SMA | 1
IN_TRX_430 | RF | X16 | CON: u.Fl | u.Fl | 1
RX_OUT_144 | RF | X17 | CON: u.Fl | u.Fl | 1
RX_1.2G | RF | X18 | CON: SMA | SMA | 1
ANT_144 | RF | X20 | CON: SMA | SMA | 1
IN_TRX_144 | RF | X21 | CON: u.Fl | u.Fl | 1
YG602020 | | YG1, YG2 | SOT89_123 | YG602020 | 2

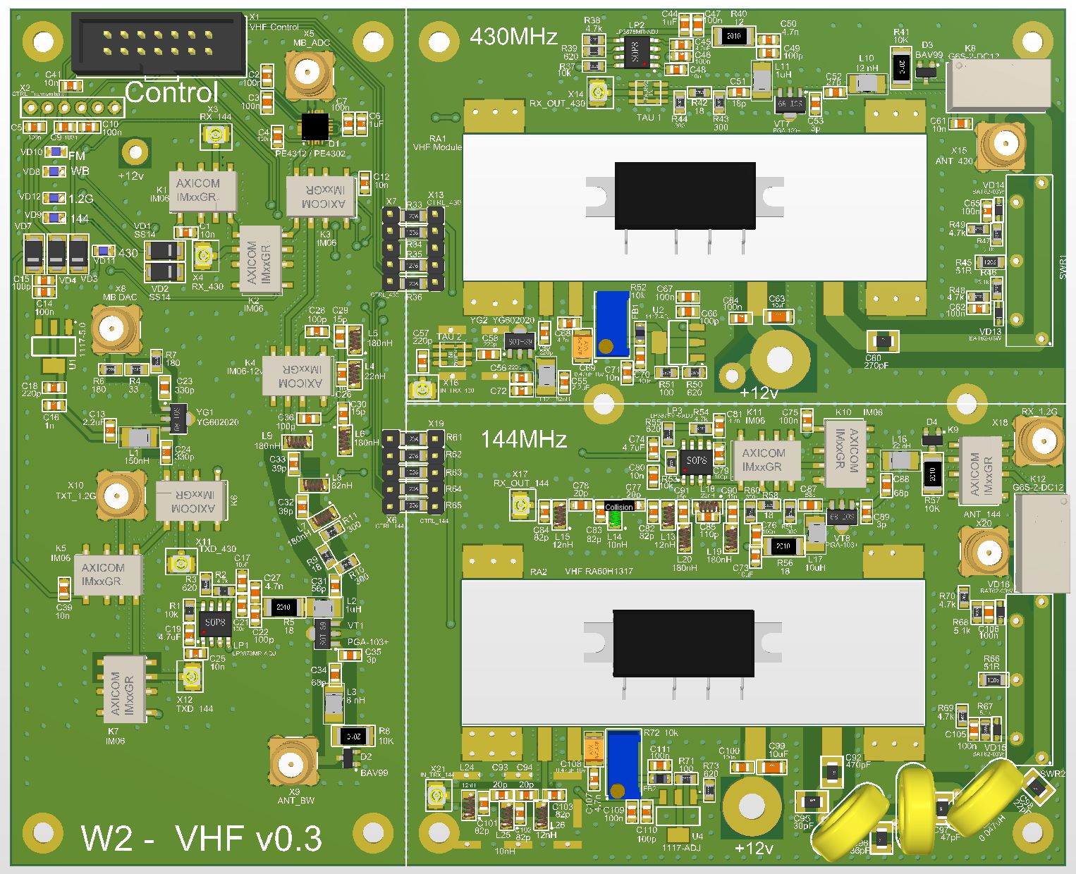
[picture p372: page 5]
