XGudron/UA3REO-DDC-Transceiver/Schematic/Wolf/Addons/TX_LPF_Add_on.pdf

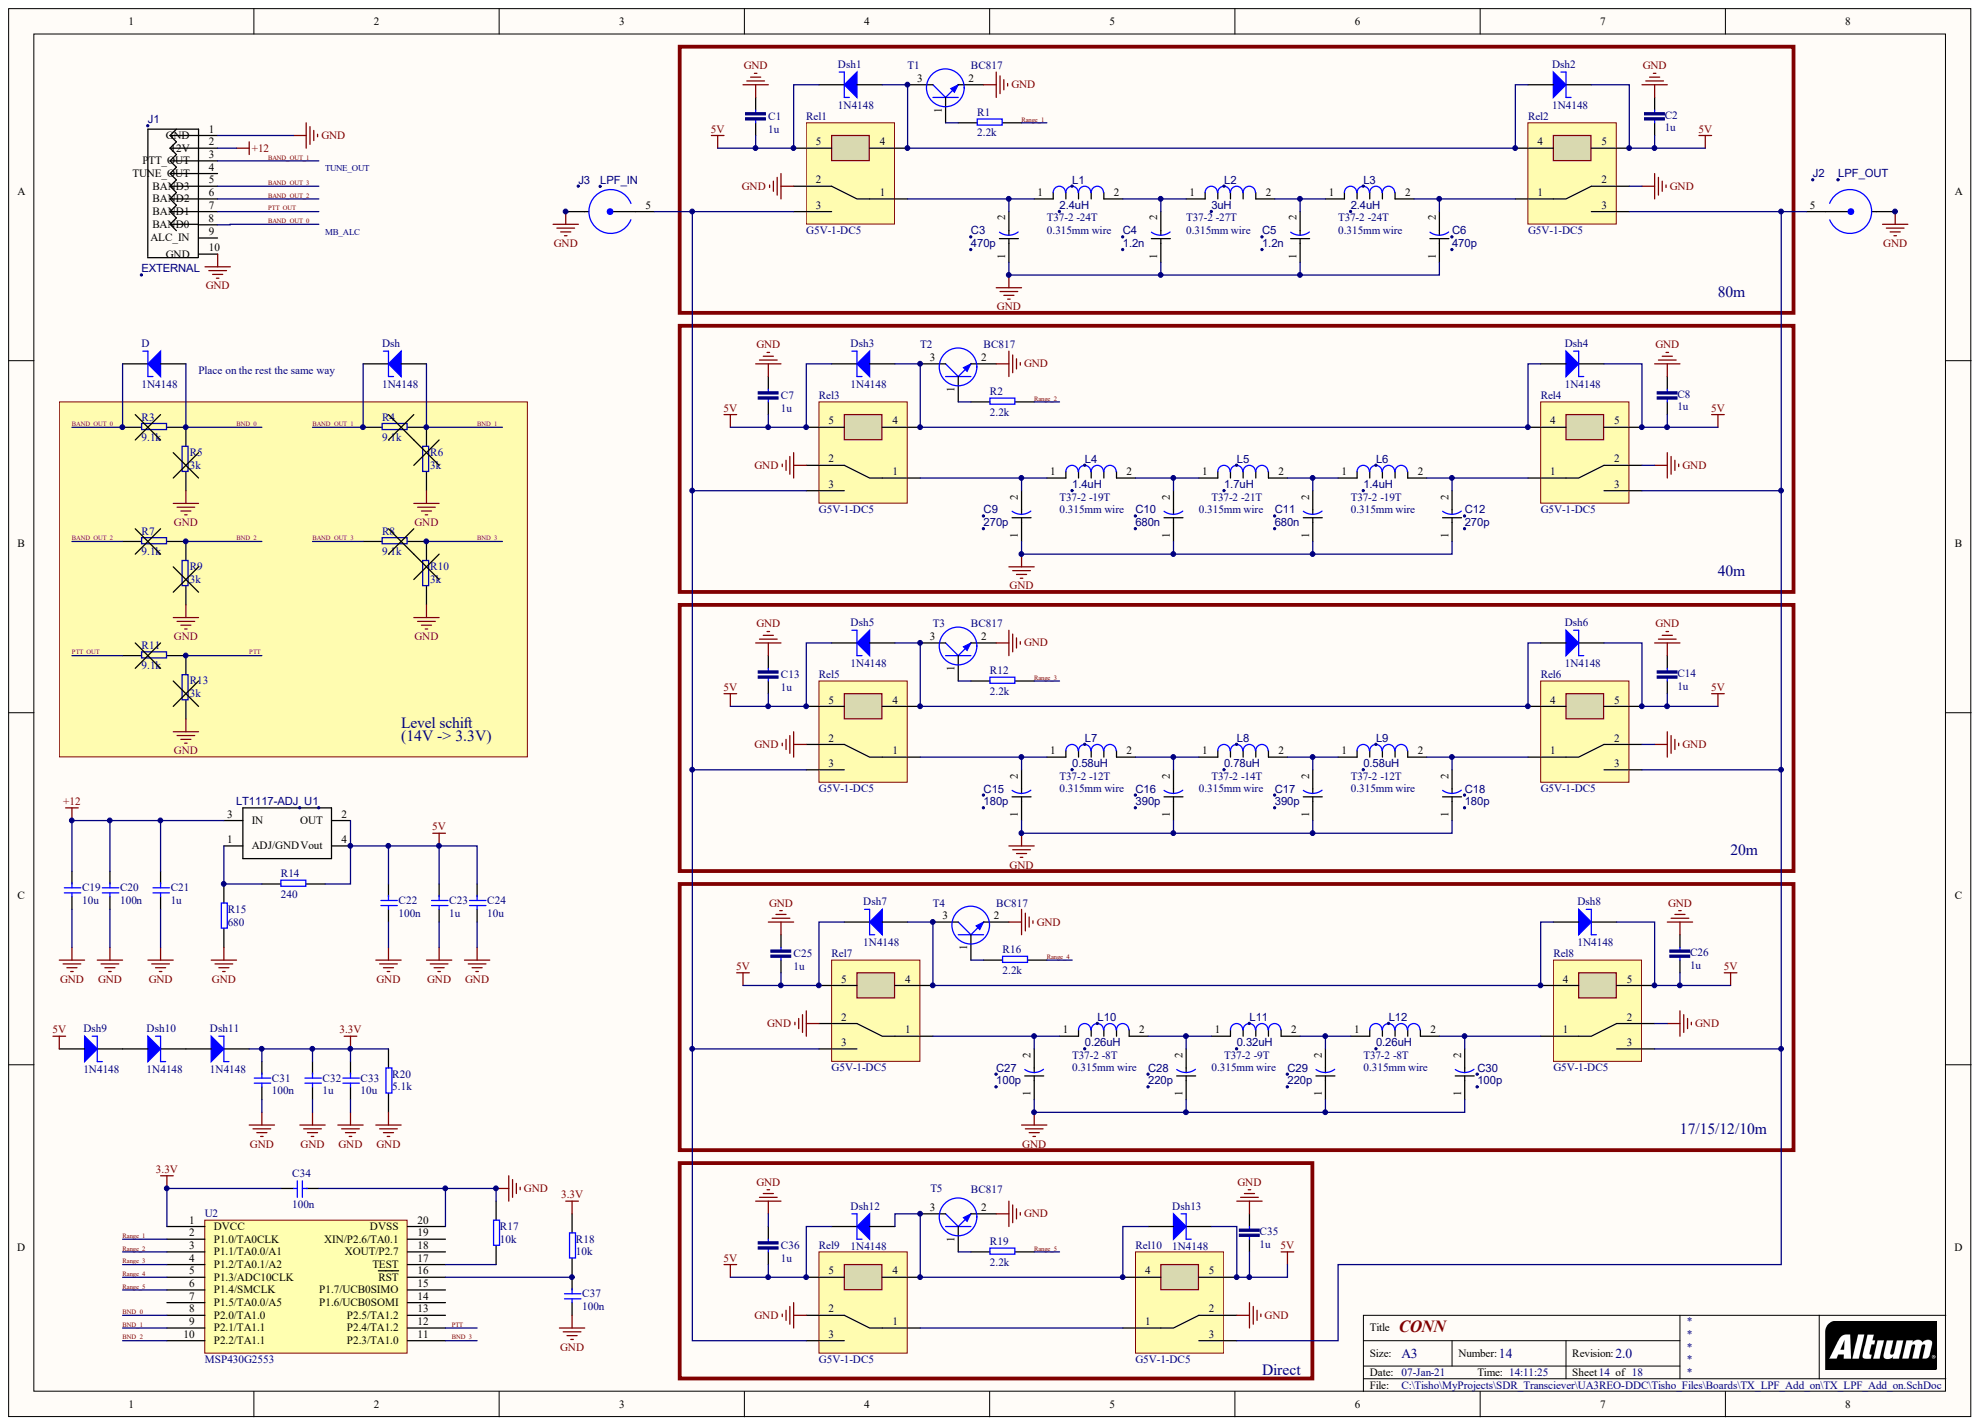
[picture p374: page 1]

Place on the rest the same way

C:\Tisho\MyProjects\SDR_Transciever\UA3REO-DDC\Tisho_Files\Boards\TX_LPF_Add_on\TX_LPF_Add_on.SchDoc
