XGudron/UA3REO-DDC-Transceiver/Schematic/Wolf/Scheme/SCHEMATIC-RF-UNIT-BIG-RU4PN-rev5.5.pdf

# CONNECTIONS

# HF TUNER

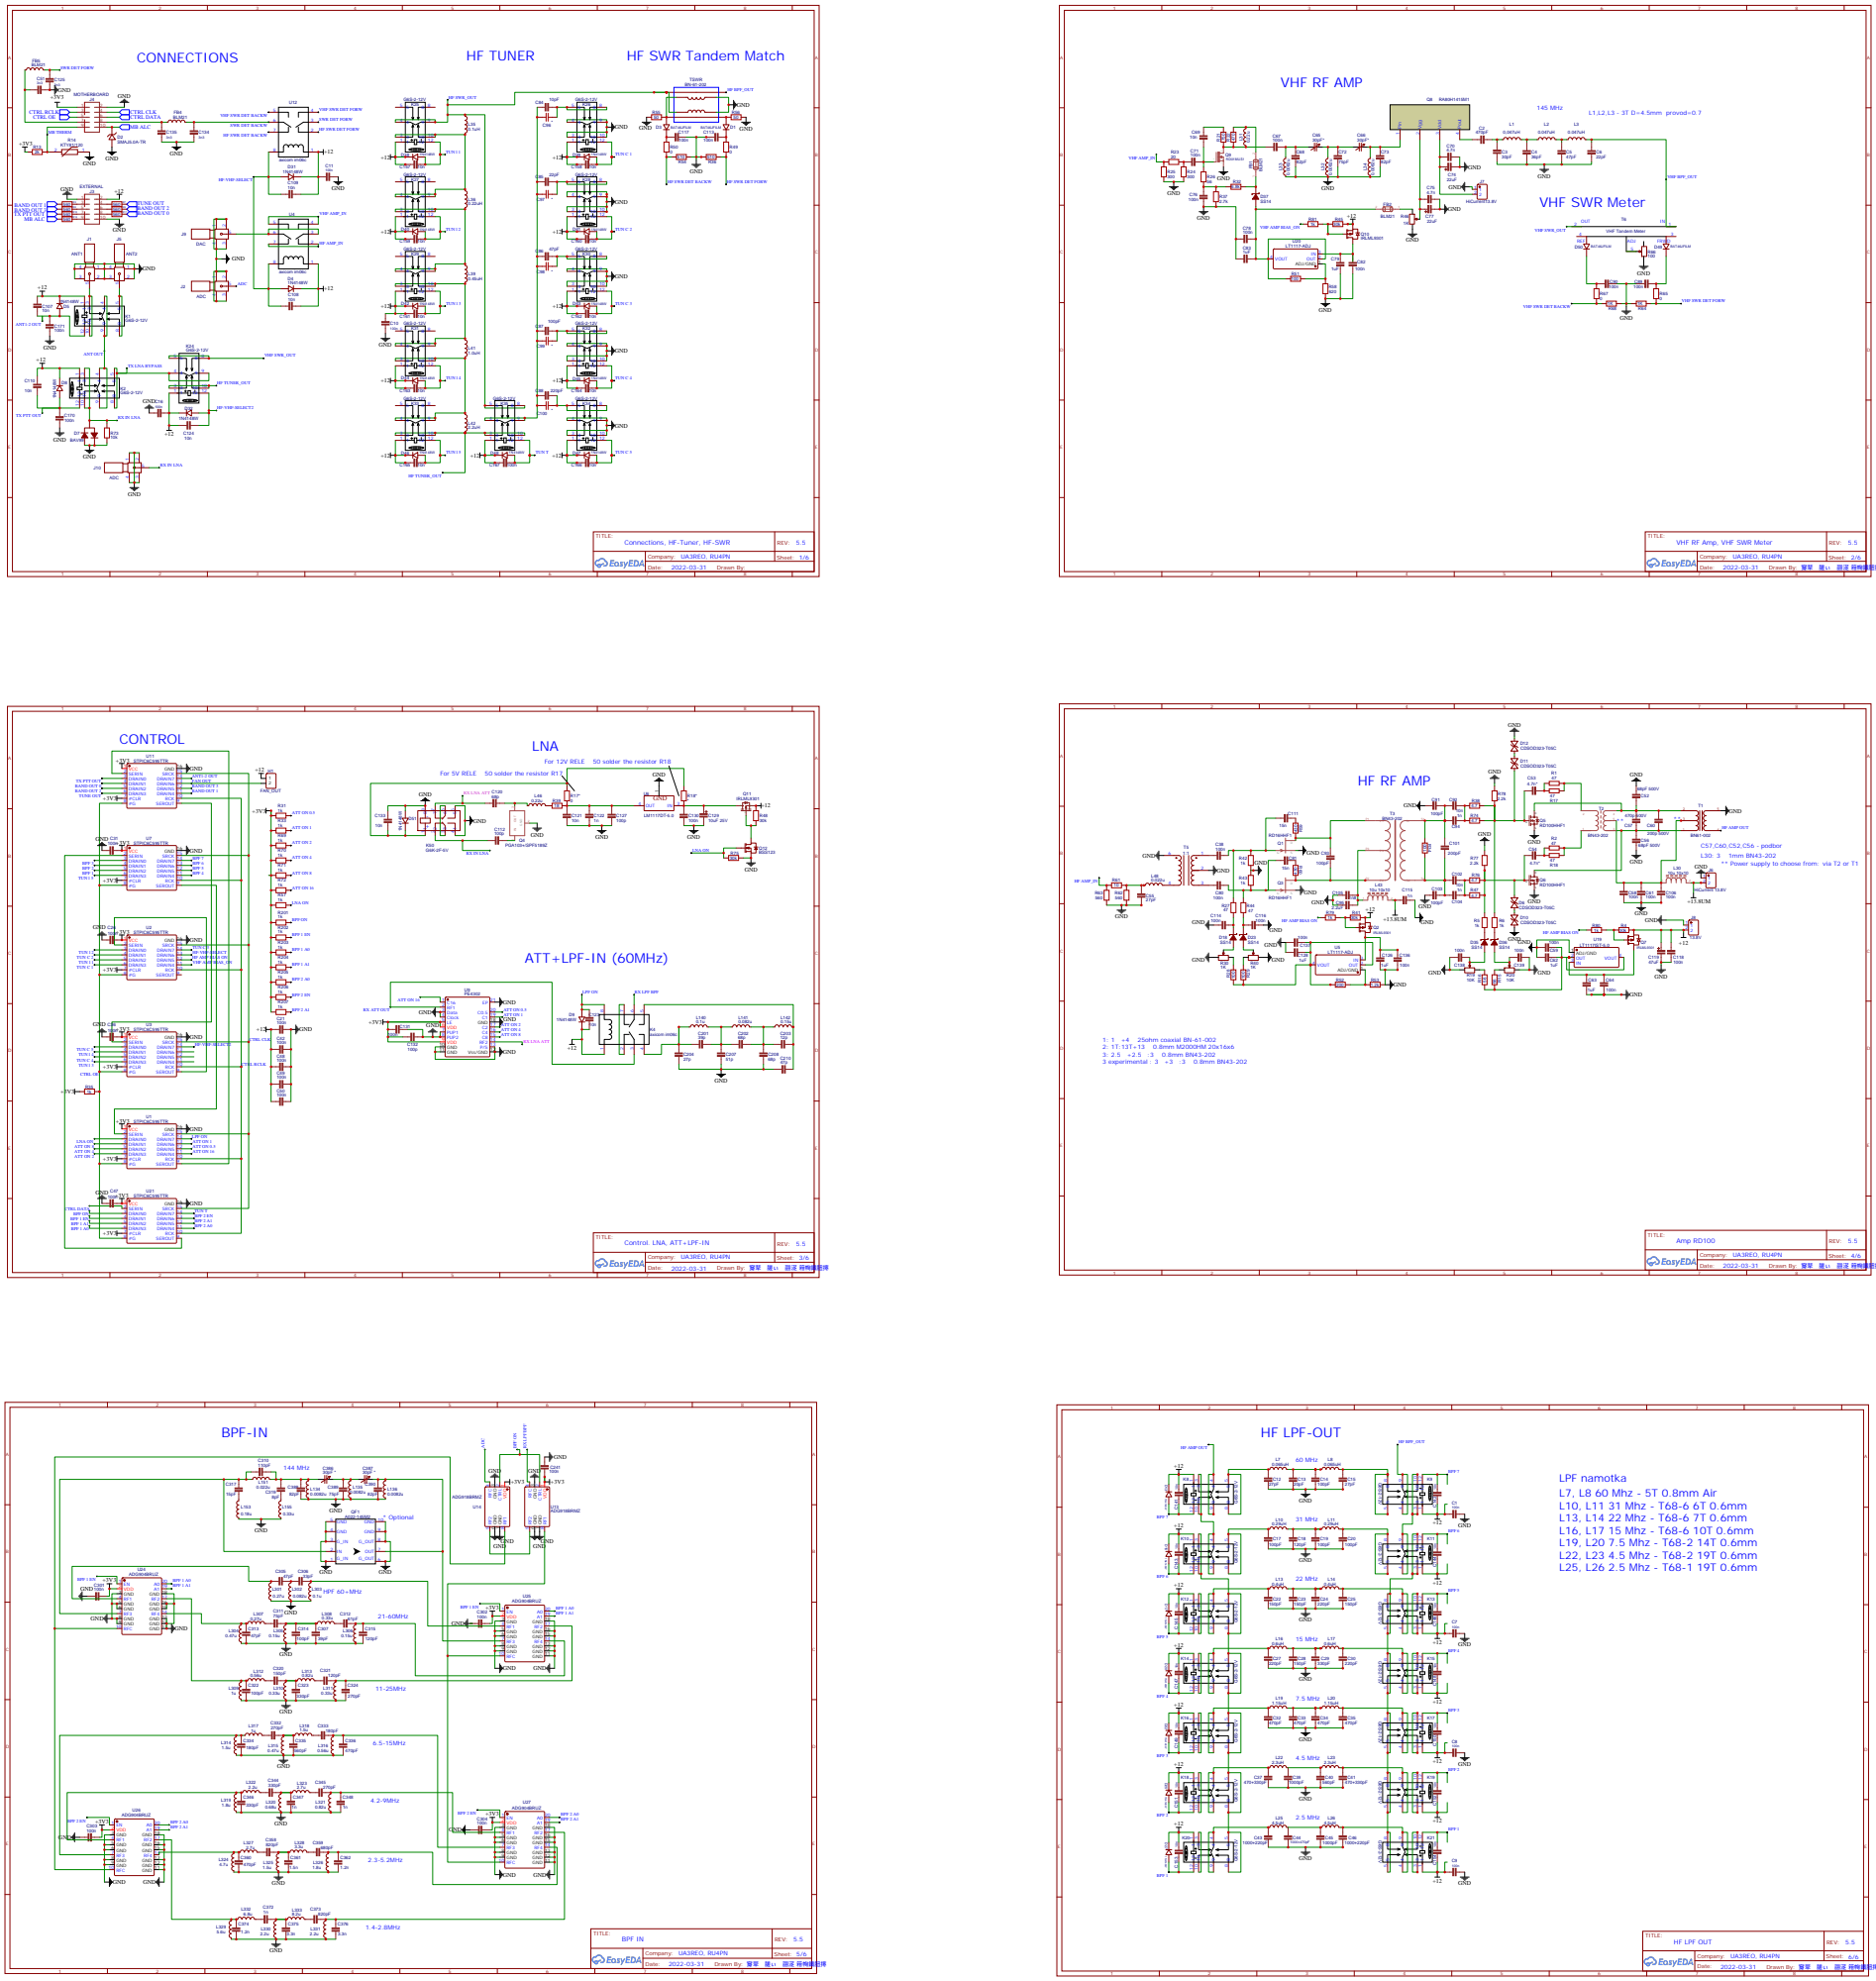
[picture p385: page 1]

HF SWR Tandem Match

VHF SWR DET BACKW

HF SWR DET BACKW

VHF SWR DET FORW

Drawn By: 䆤㹃푁䐤ぃ푂䎄㴀 䈤㡄鐵䏔㩃

For 12V RELE 50 solder the resistor R18

For 5V RELE 50 solder the resistor R17

GND
TUN C 3
HF-VHF-SELECT
HF AMP BIAS ON
VHF AMP BIAS_ON
