XGudron/UA3REO-DDC-Transceiver/Schematic/Wolf/Scheme/SCHEMATIC-RF-UNIT-QRP-RU4PN-rev3.pdf

# CONNECTIONS

# HF TUNER

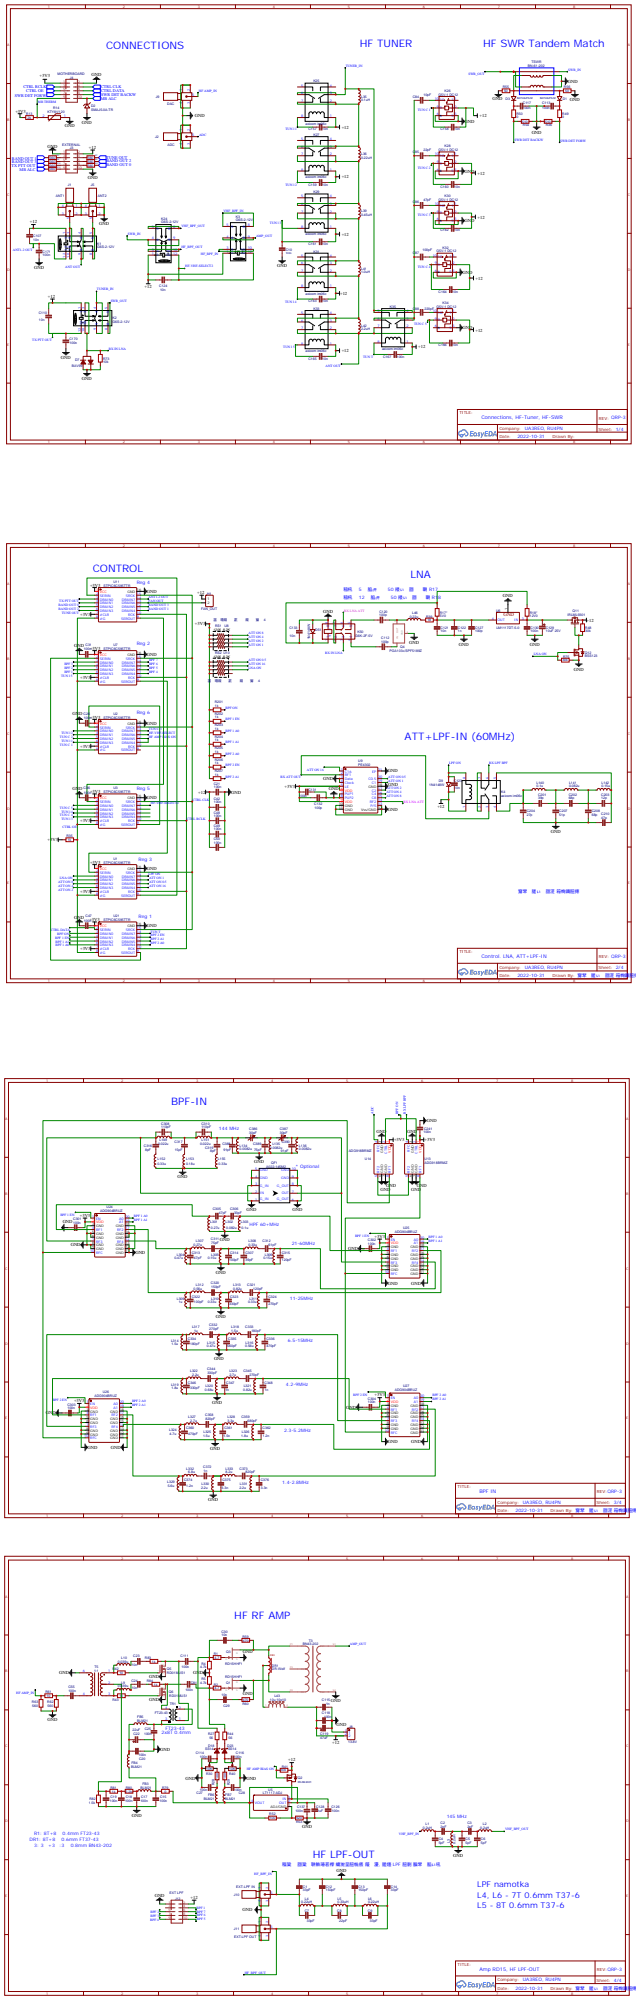
[picture p393: page 1]

HF SWR Tandem Match

GND
TUN C 3
HF-VHF-SELECT
HF AMP BIAS ON

Drawn By: 䆤㹃푁䐤ぃ푂䎄㴀 䈤㡄鐵䏔㩃

R41 HF AMP BIAS ON

䅔䅃됸 䎄䅃䎴䱃瑃䍔㰀 䌤㵃呈䏔㡃倀 䉄ᵂ瀀, 䐤㸀 LPF 䏔㔀 䐔㹃ᐸ䐄ぃ吼
