XGudron/UA3REO-DDC-Transceiver/Schematic/Wolf/Scheme/SCHEMATIC-RF-UNIT-QRP_20W-rev21.pdf

U_SWR Tandem Match
SWR Tandem Match.SchDoc
SWR_OUT

C:\Dropbox\Develop\Projects\WOLF\Schematic\Wolf\Altium_Designer\RF-UNIT-QRP_20W\RF-UNIT-QRP_20W.SCHDOC

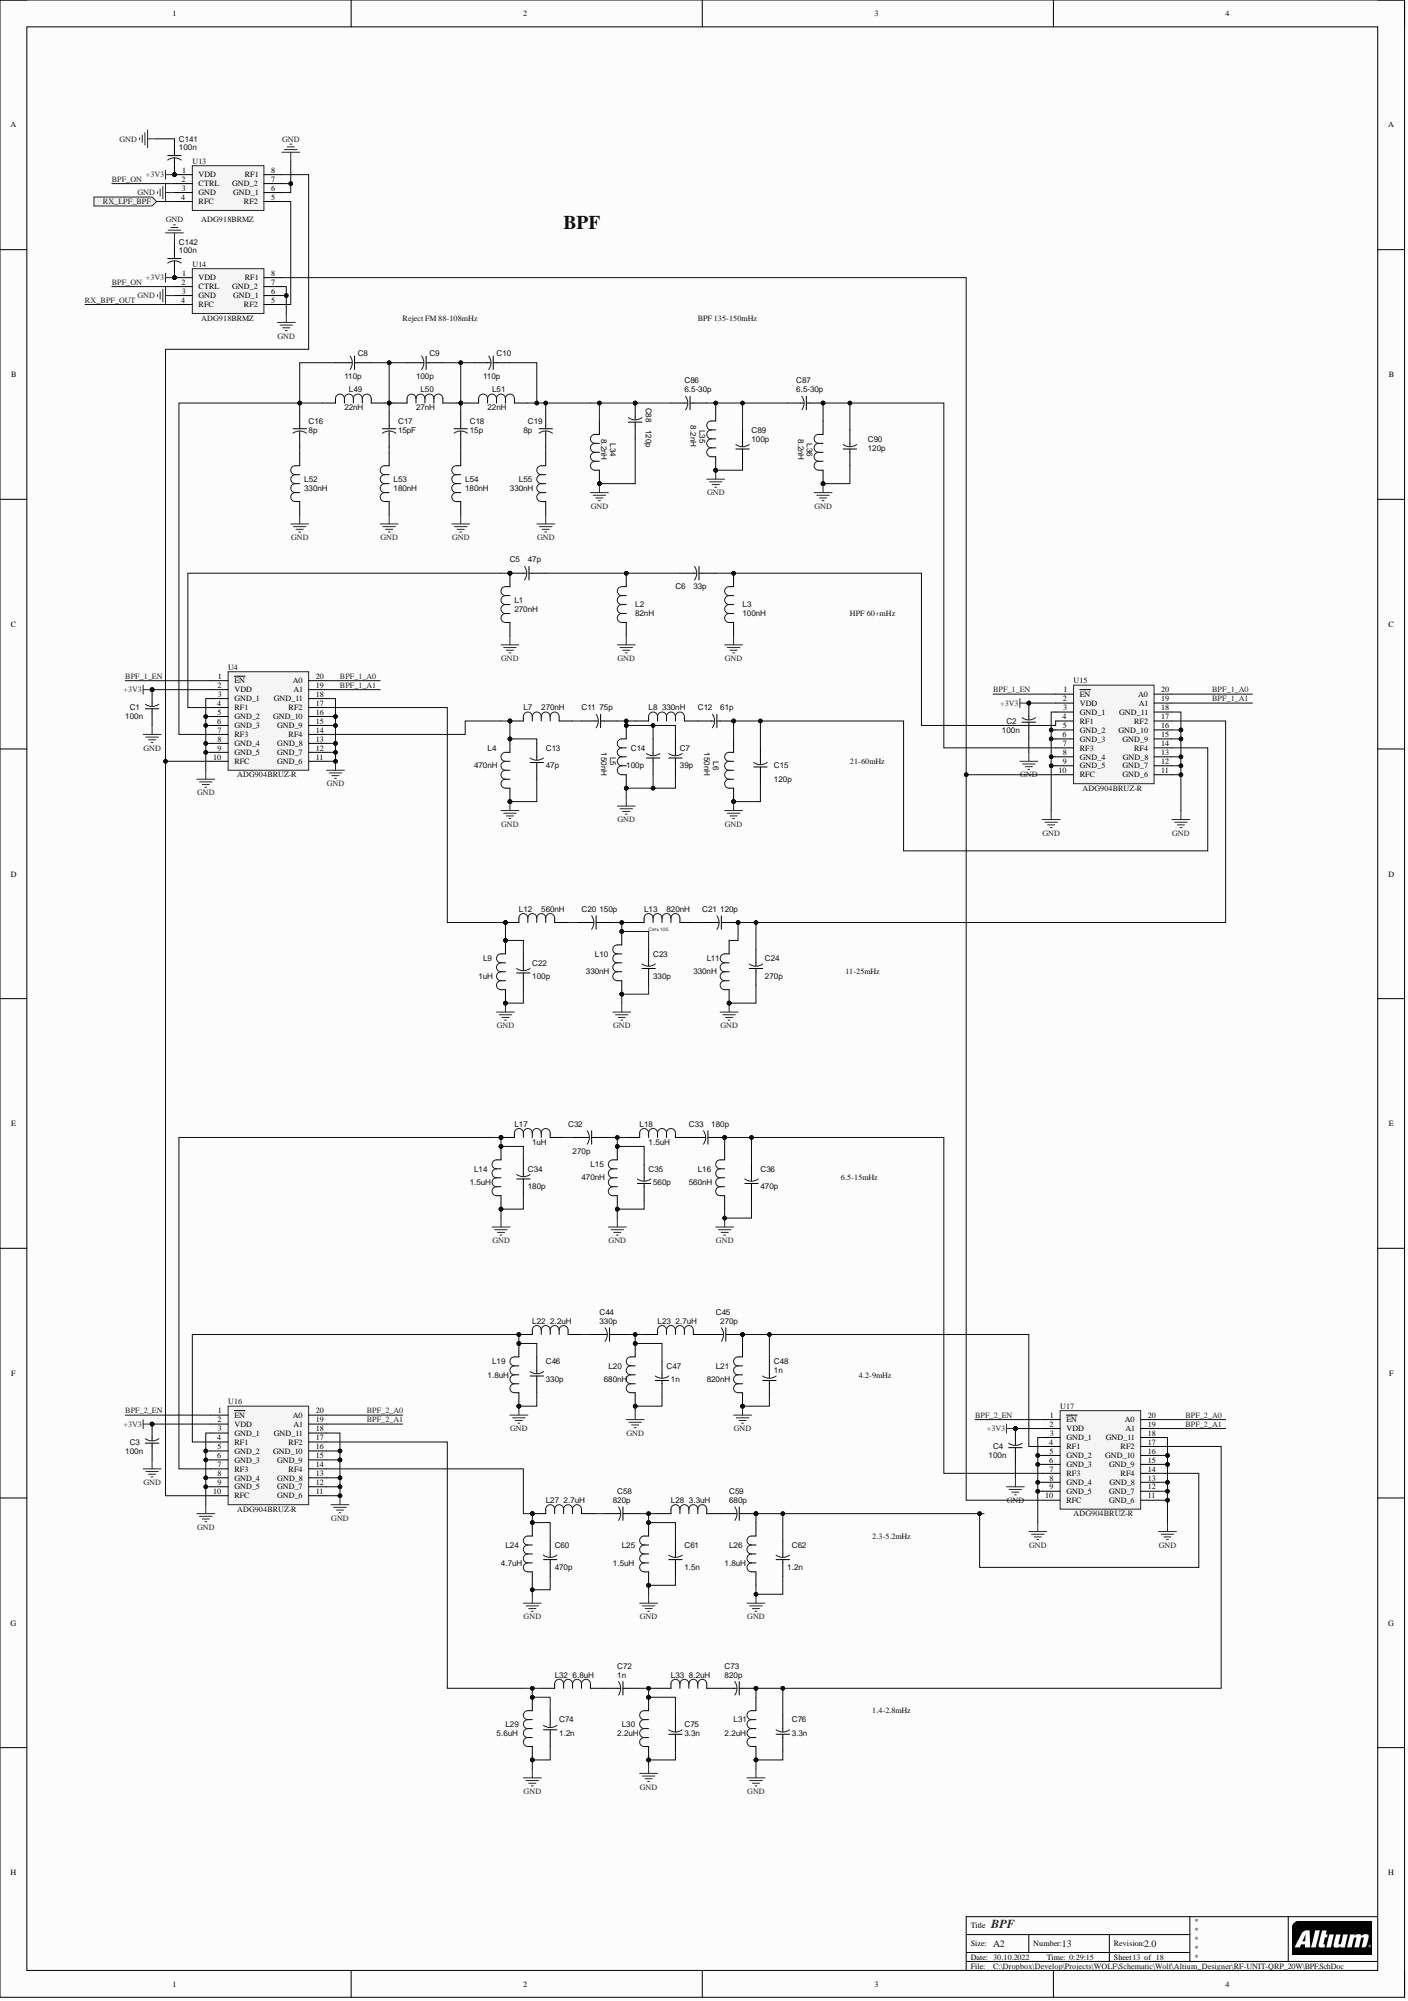
[picture p394: page 2]

EN 1 VDD 2 | RF2

GND_1 3
RF1 4 | 17
GND_2 5 GND_10 GND_9 | 16
GND_3 6 | 15

C15 | | GND_2 5 GND_10 GND_9 RF4 GND_8 GND_7 | 16

RF3 7 | 14
GND_4 8 | 13
GND_5 9 | 12

GND_4 8 GND_8 GND_7 | 13

GND | C20 150p C33 180p

GND_2 5 GND_10 GND_9 RF4 | 16

C:\Dropbox\Develop\Projects\WOLF\Schematic\Wolf\Altium_Designer\RF-UNIT-QRP_20W\BPF.SchDoc

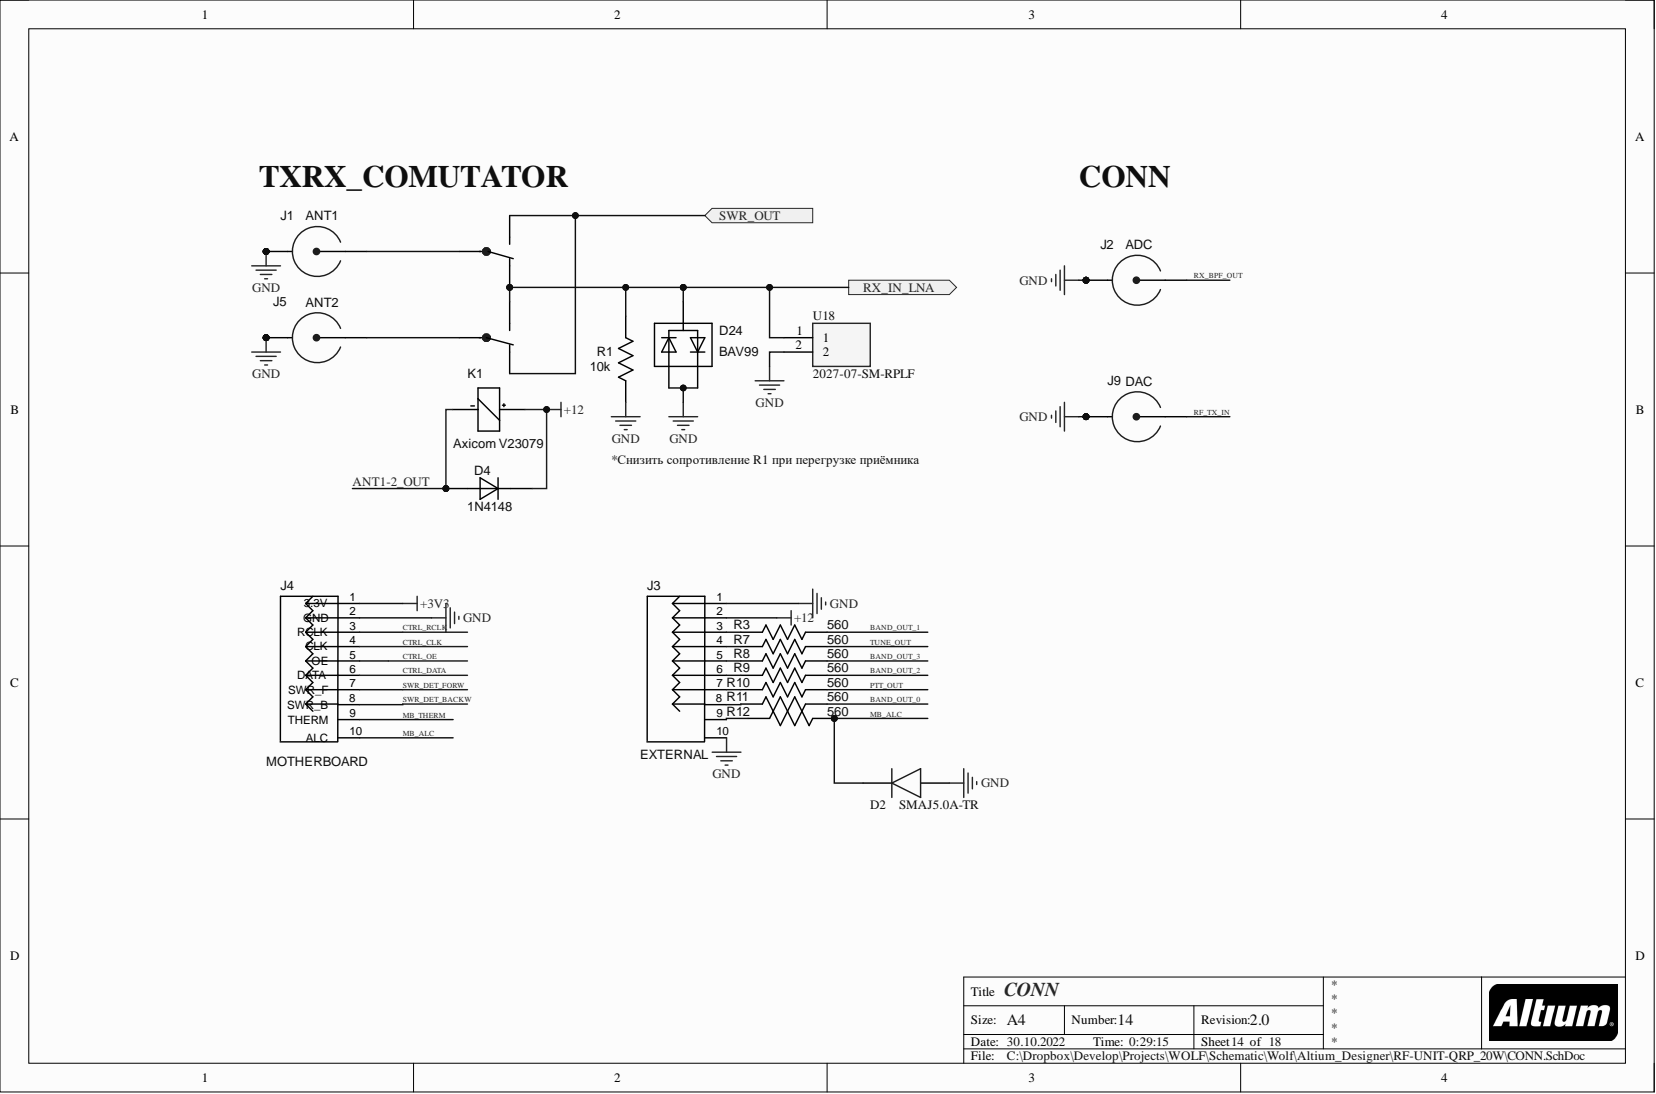
[picture p395: page 3]

GND
*Снизить сопротивление R1 при перегрузке приёмника

C:\Dropbox\Develop\Projects\WOLF\Schematic\Wolf\Altium_Designer\RF-UNIT-QRP_20W\CONN.SchDoc

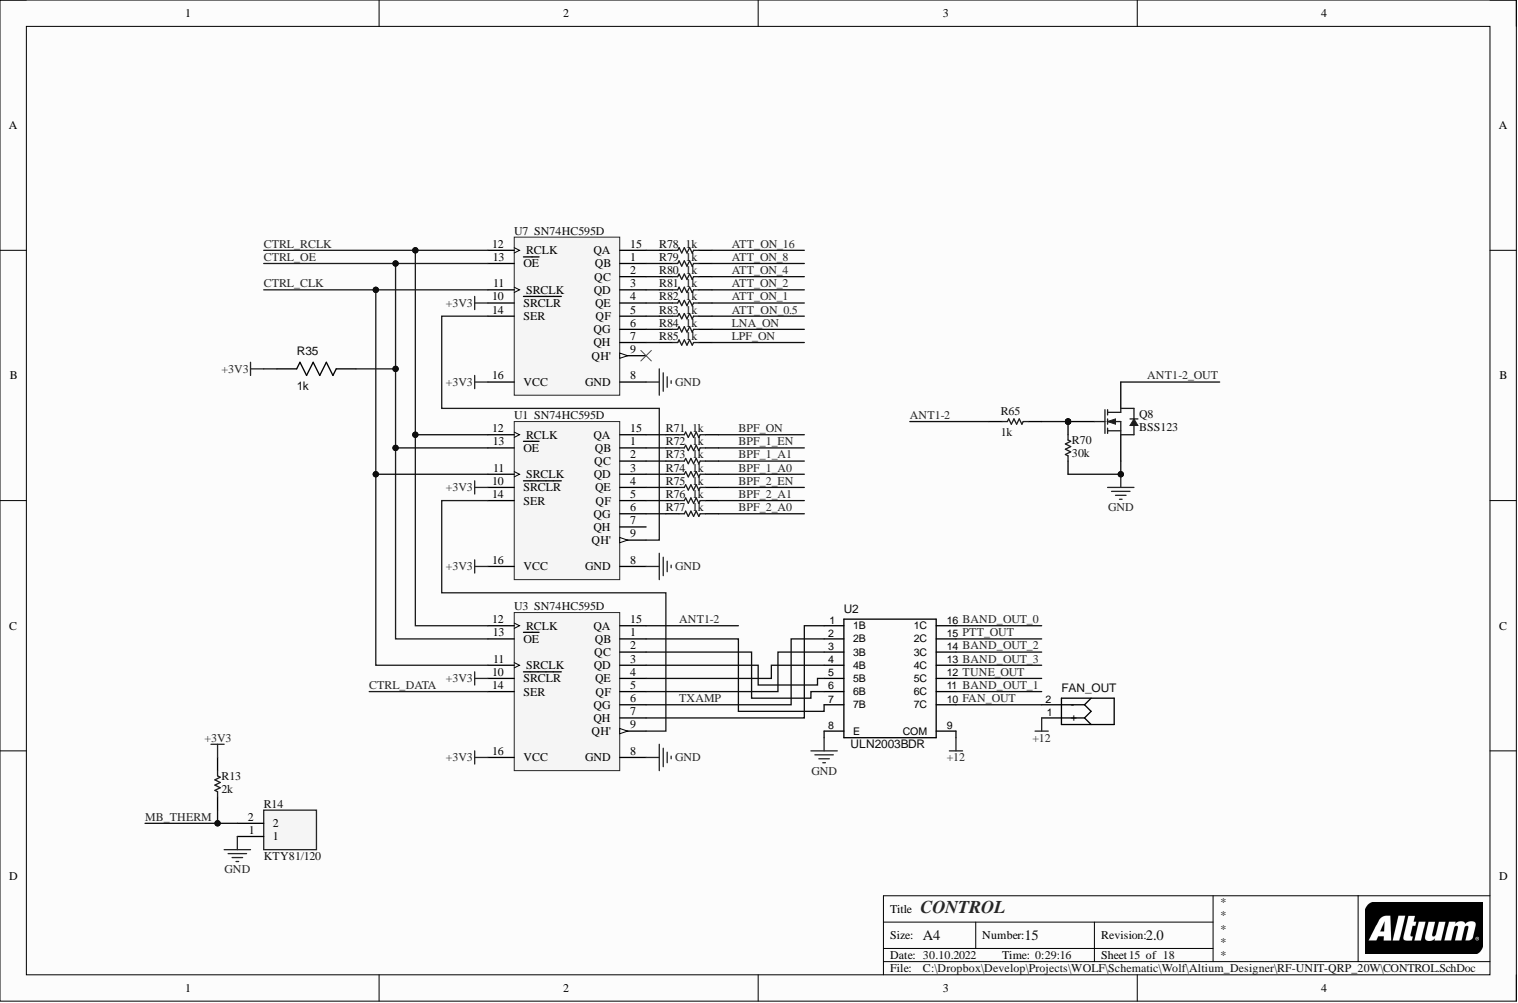
[picture p396: page 4]

1 3 | 1 | | 2
1 1 | 2 | | 3

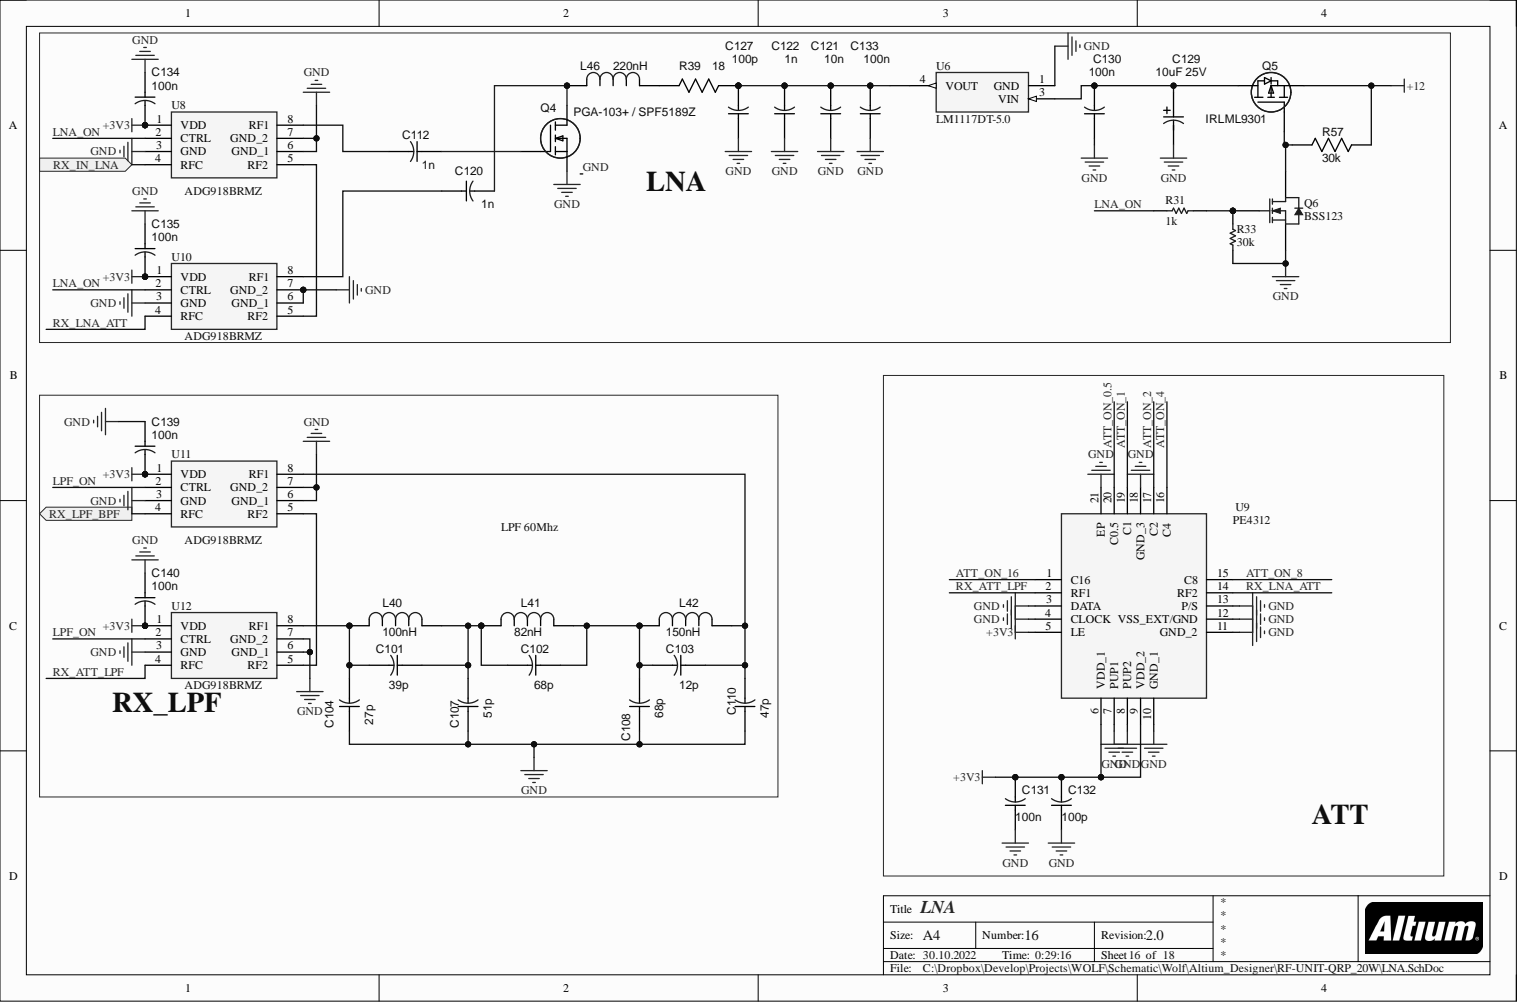
[picture p397: page 5]

C:\Dropbox\Develop\Projects\WOLF\Schematic\Wolf\Altium_Designer\RF-UNIT-QRP_20W\LNA.SchDoc

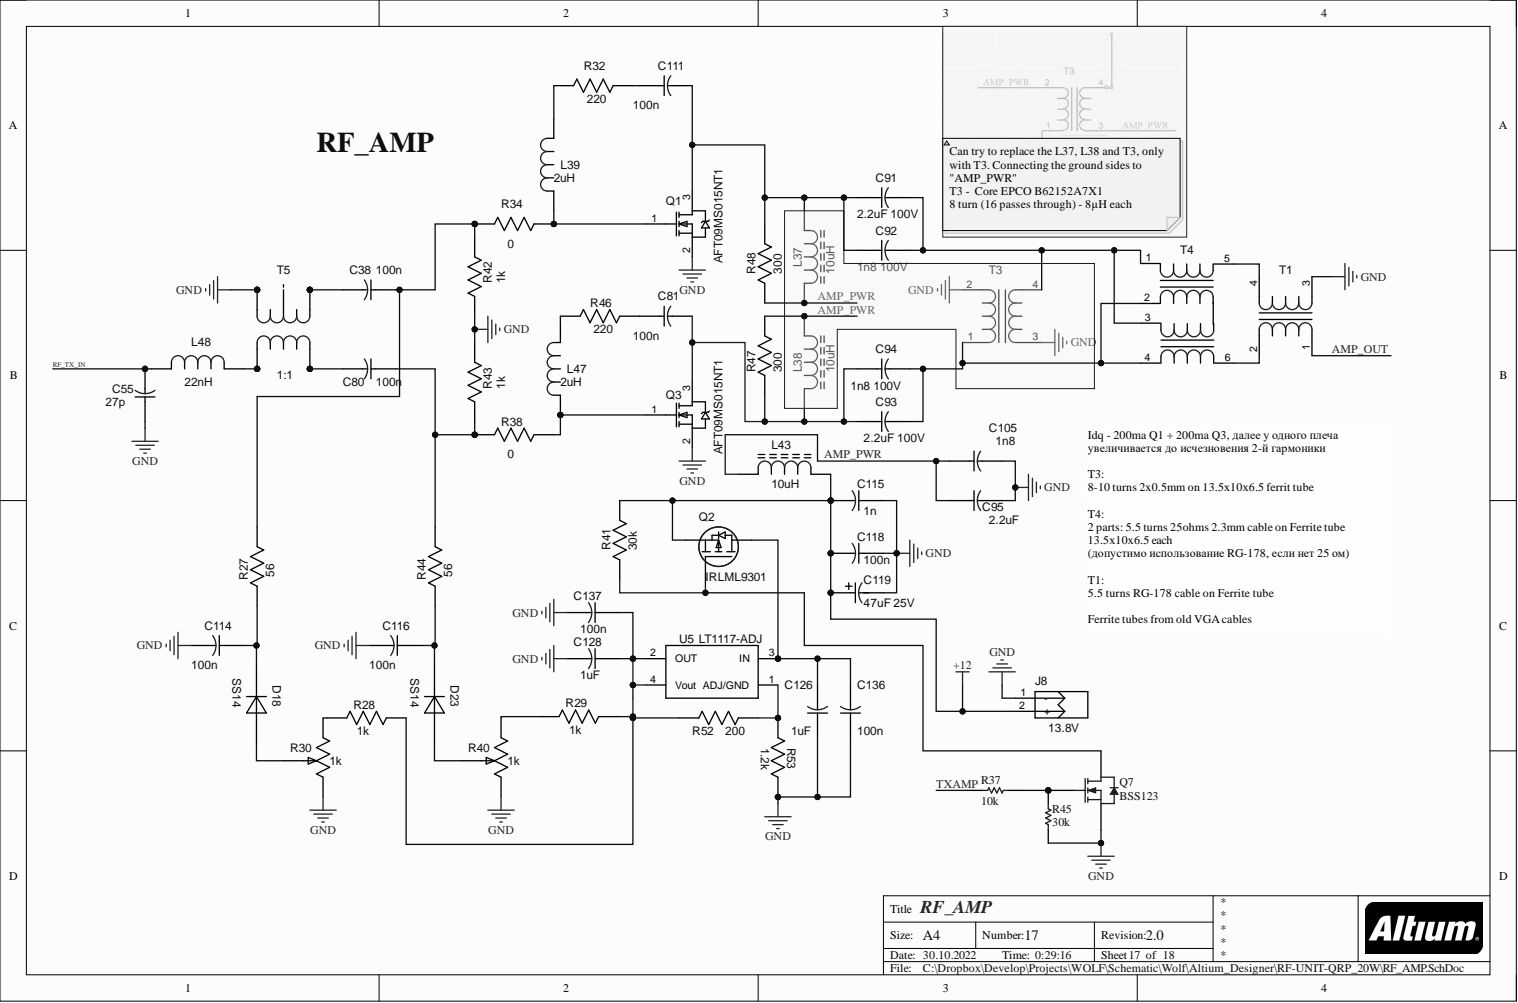
[picture p398: page 6]

Can try to replace the L37, L38 and T3, only
with T3. Connecting the ground sides to
"AMP_PWR"
T3 - Core EPCO B62152A7X1
8 turn (16 passes through) - 8µH each

Idq - 200ma Q1 + 200ma Q3, далее у одного плеча
увеличивается до исчезновения 2-й гармоники

8-10 turns 2x0.5mm on 13.5х10х6.5 ferrit tube

2 parts: 5.5 turns 25ohms 2.3mm cable on Ferrite tube
13.5х10x6.5 each
(допустимо использование RG-178, если нет 25 ом)

5.5 turns RG-178 cable on Ferrite tube

Ferrite tubes from old VGA cables

C:\Dropbox\Develop\Projects\WOLF\Schematic\Wolf\Altium_Designer\RF-UNIT-QRP_20W\RF_AMP.SchDoc

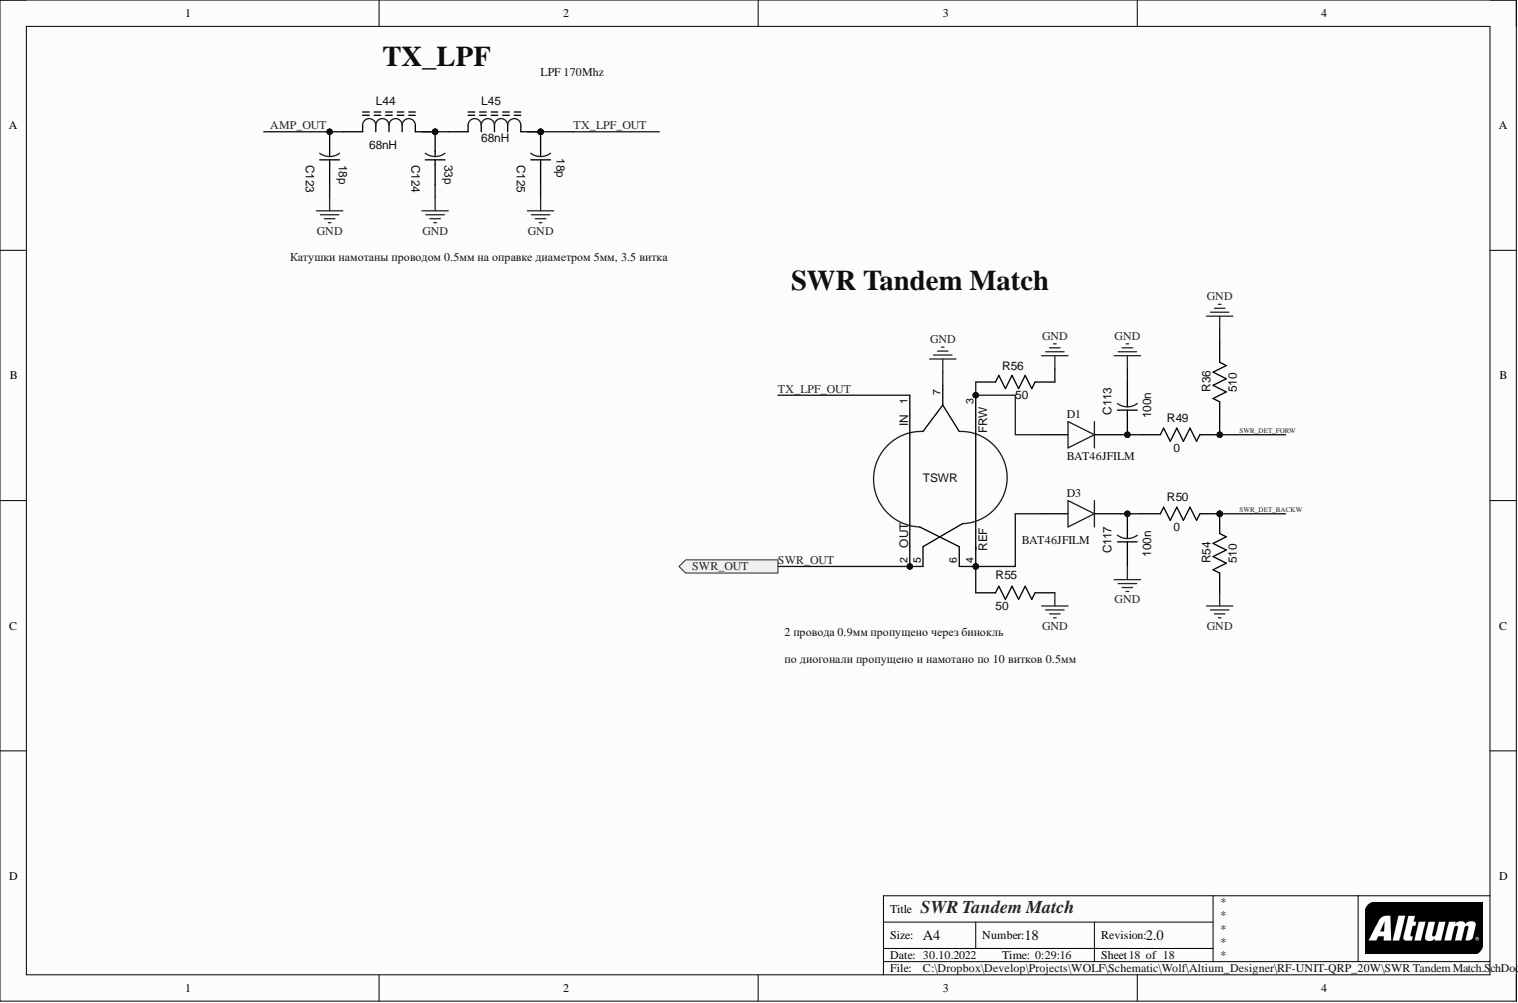
[picture p399: page 7]

Катушки намотаны проводом 0.5мм на оправке диаметром 5мм, 3.5 витка

2 провода 0.9мм пропущено через бинокль

по диогонали пропущено и намотано по 10 витков 0.5мм

C:\Dropbox\Develop\Projects\WOLF\Schematic\Wolf\Altium_Designer\RF-UNIT-QRP_20W\SWR Tandem Match.SchDoc
