XGudron/UA3REO-DDC-Transceiver/Schematic/Wolf/Scheme/SCHEMATIC-RF-UNIT-SPLIT-rev3.pdf

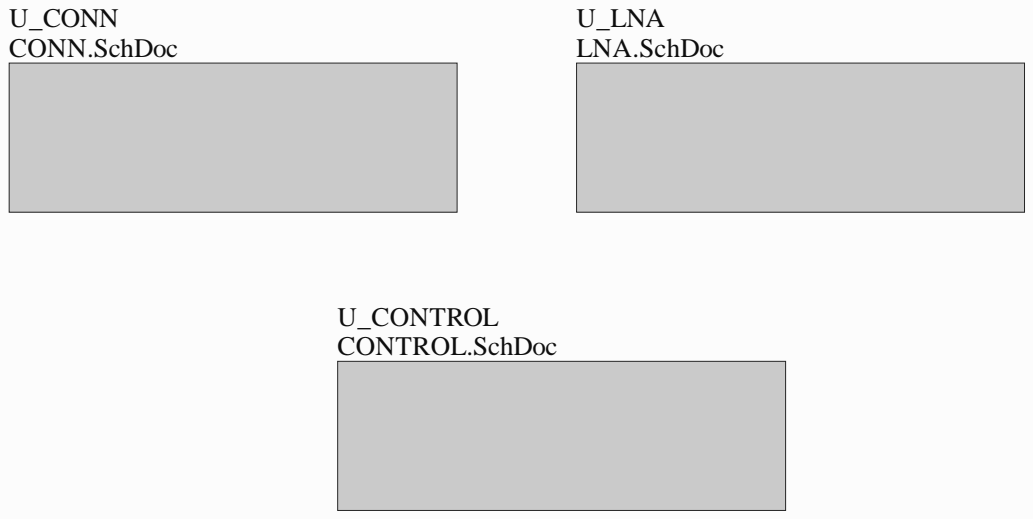
[picture p400: page 1]

C:\Dropbox\Develop\Projects\WOLF\Schematic\Wolf\Altium_Designer\RF-UNIT-SPLIT\RF-UNIT-SPLIT.SCHDOC

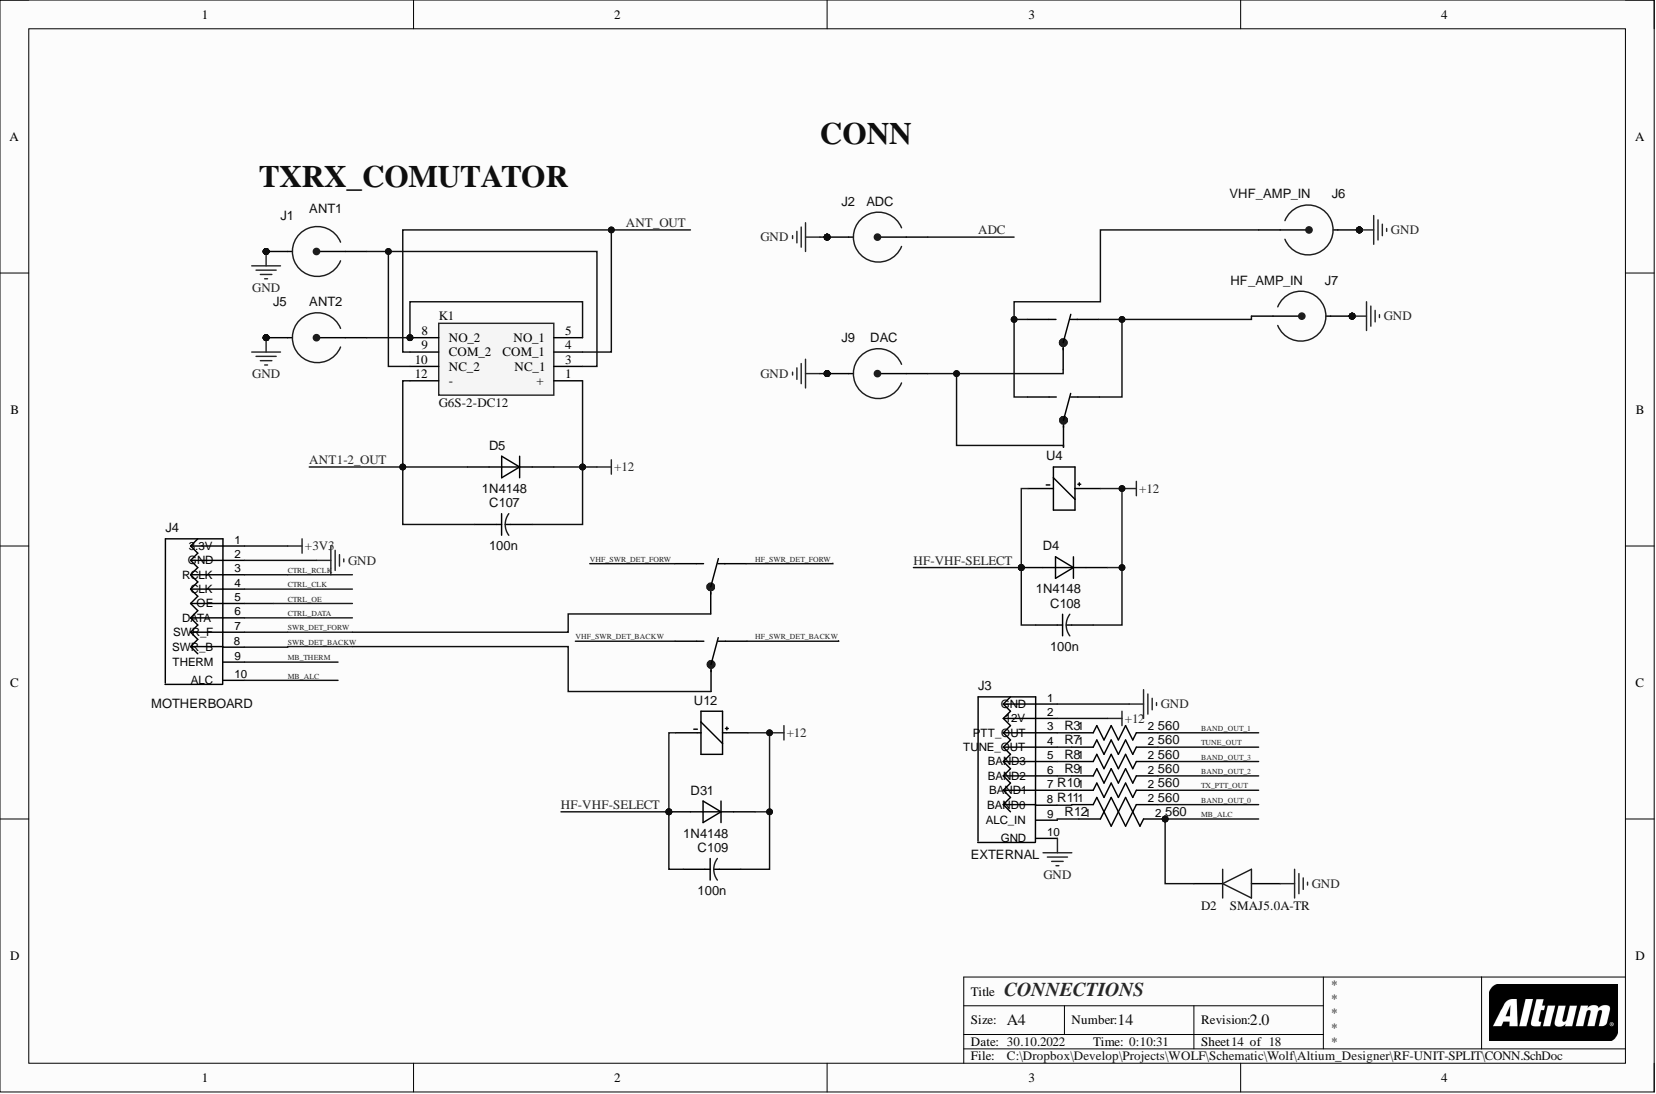
[picture p401: page 2]

C:\Dropbox\Develop\Projects\WOLF\Schematic\Wolf\Altium_Designer\RF-UNIT-SPLIT\CONN.SchDoc

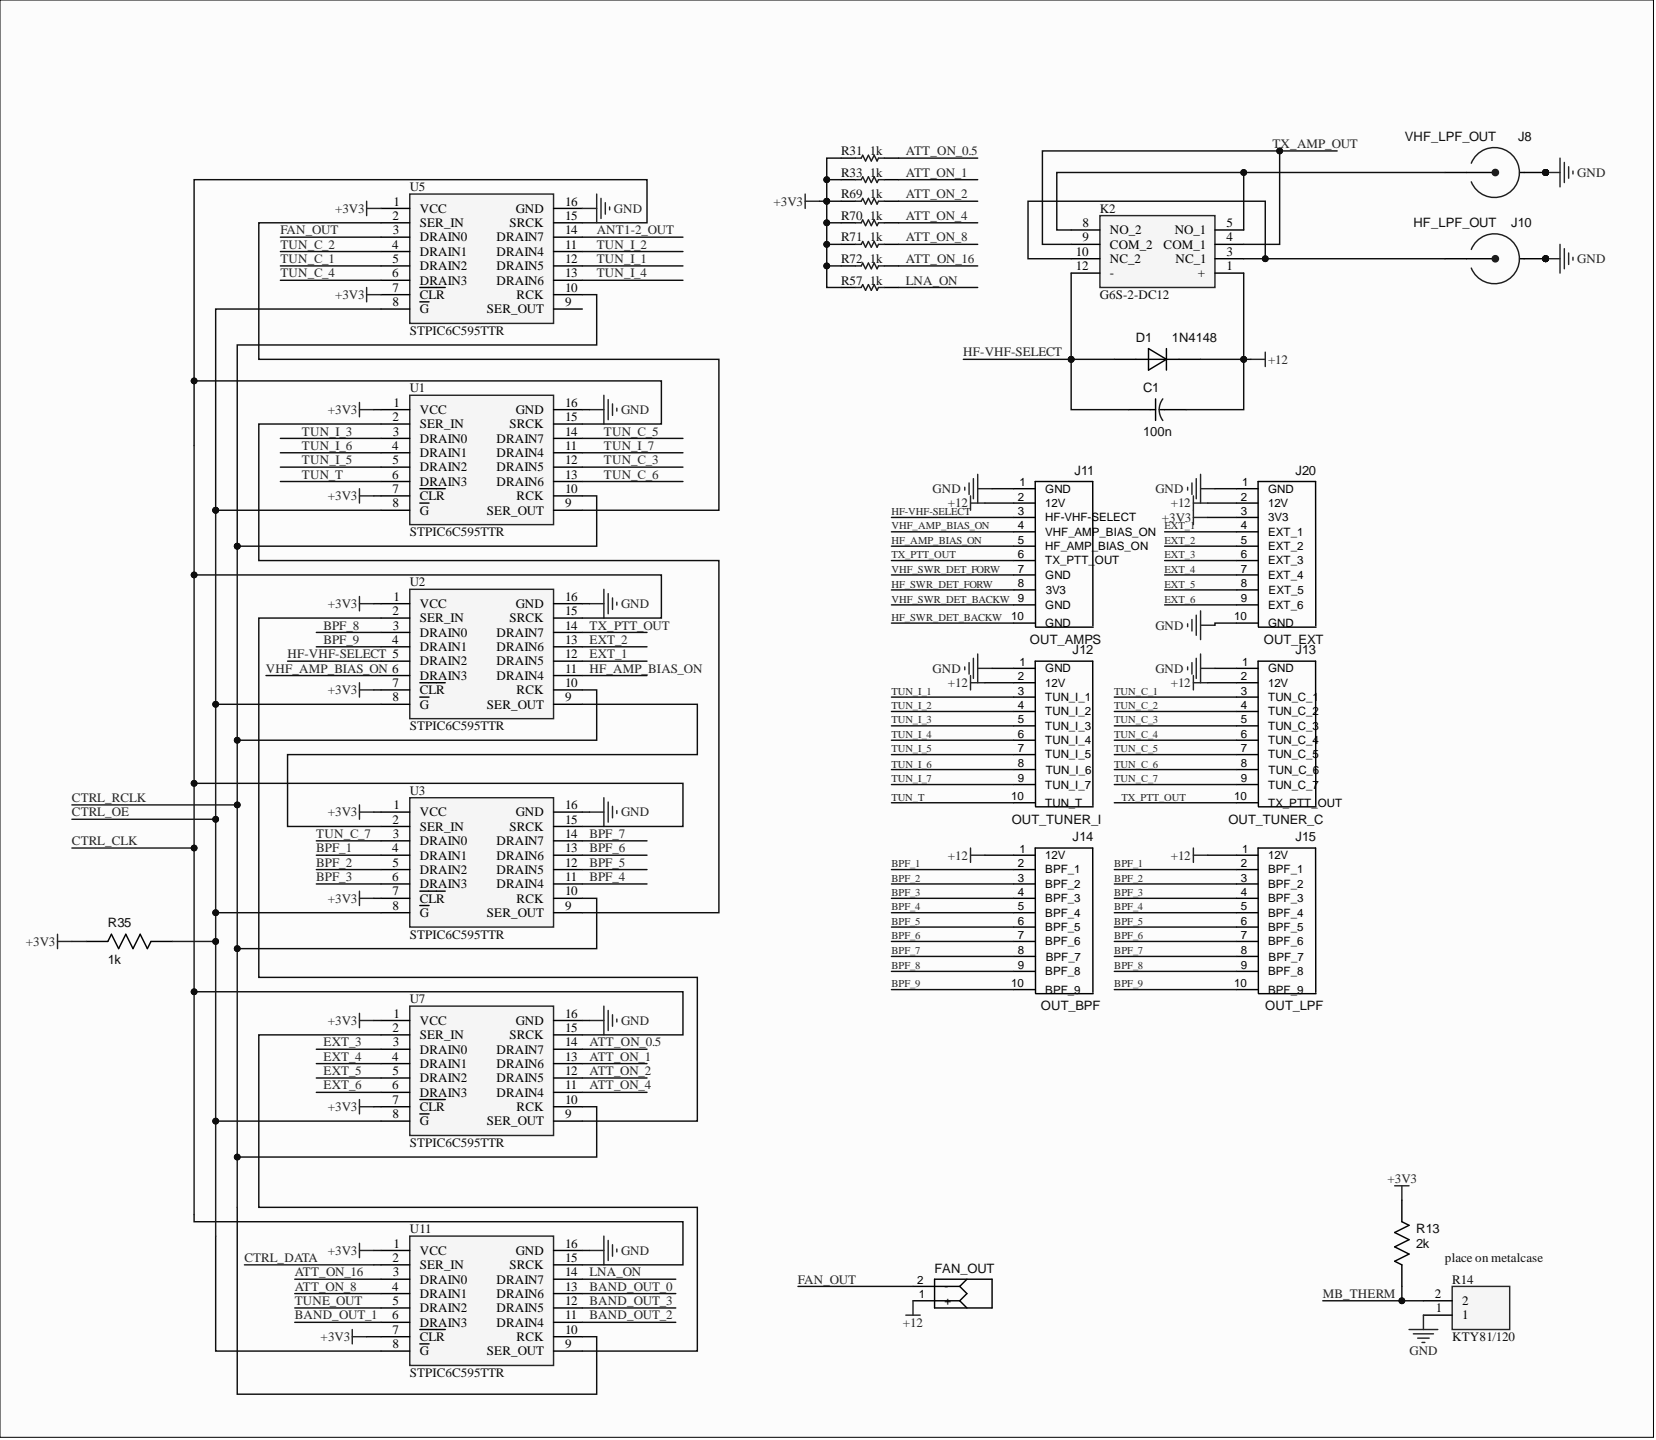
[picture p402: page 3]

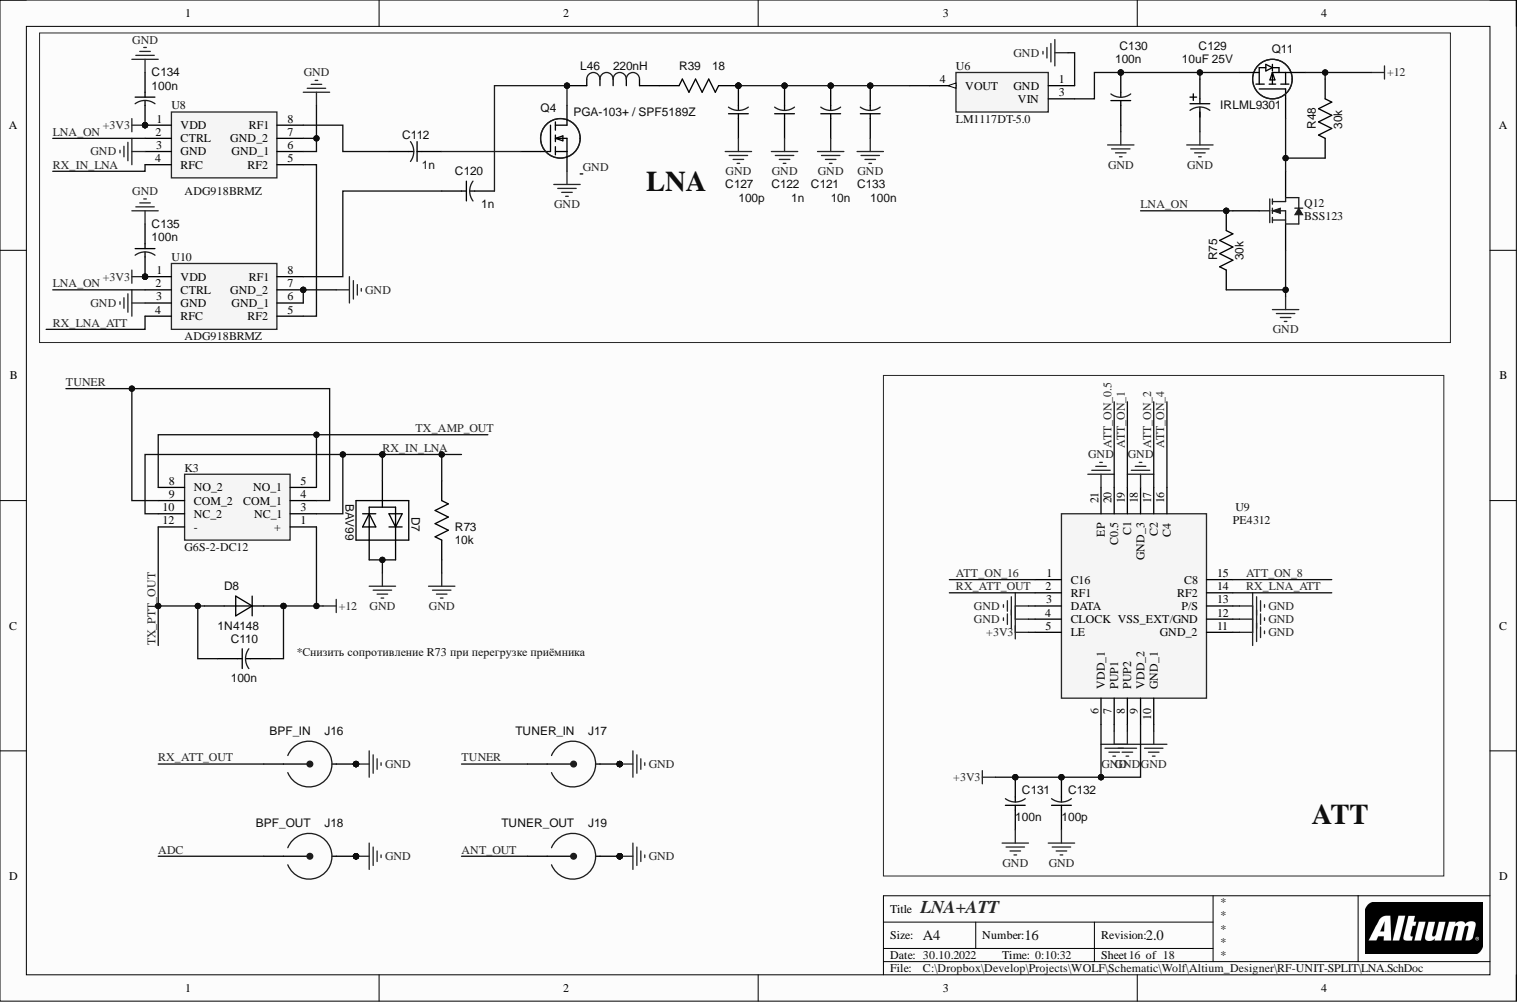
[picture p403: page 4]

RX_IN_LNA

*Снизить сопротивление R73 при перегрузке приёмника

C:\Dropbox\Develop\Projects\WOLF\Schematic\Wolf\Altium_Designer\RF-UNIT-SPLIT\LNA.SchDoc
