XGudron/UA3REO-DDC-Transceiver/Schematic/Wolf-Lite/Scheme/RFPower-Unit-v1.3.pdf

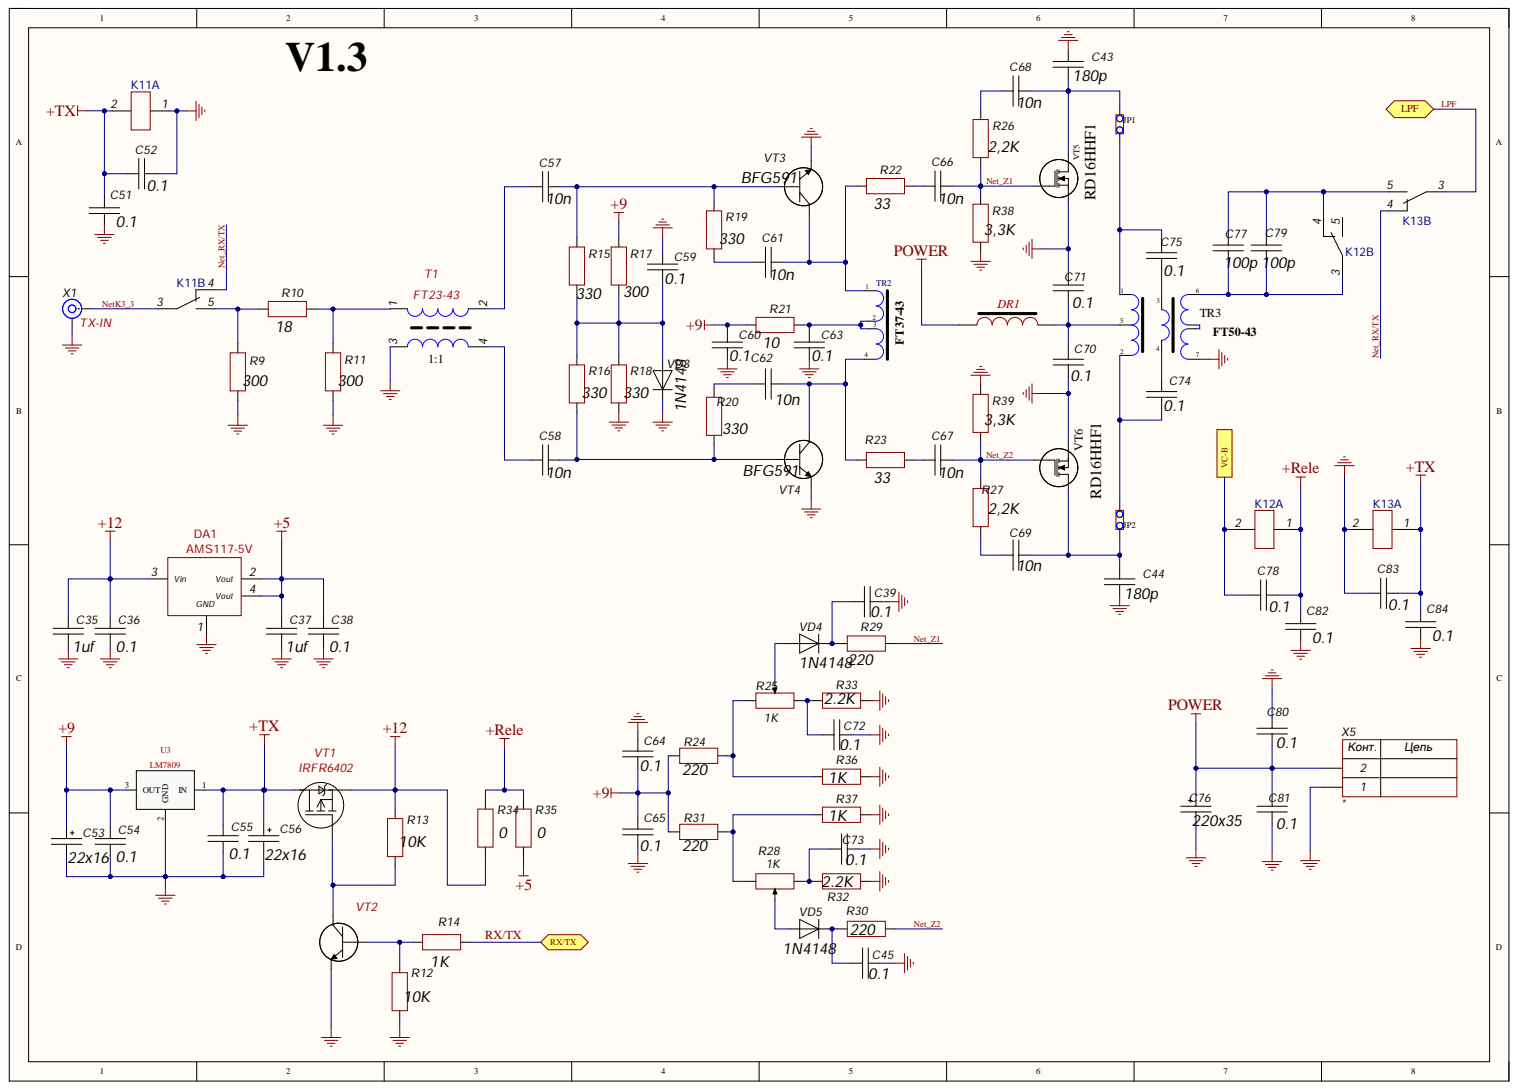
[picture p426: page 1]

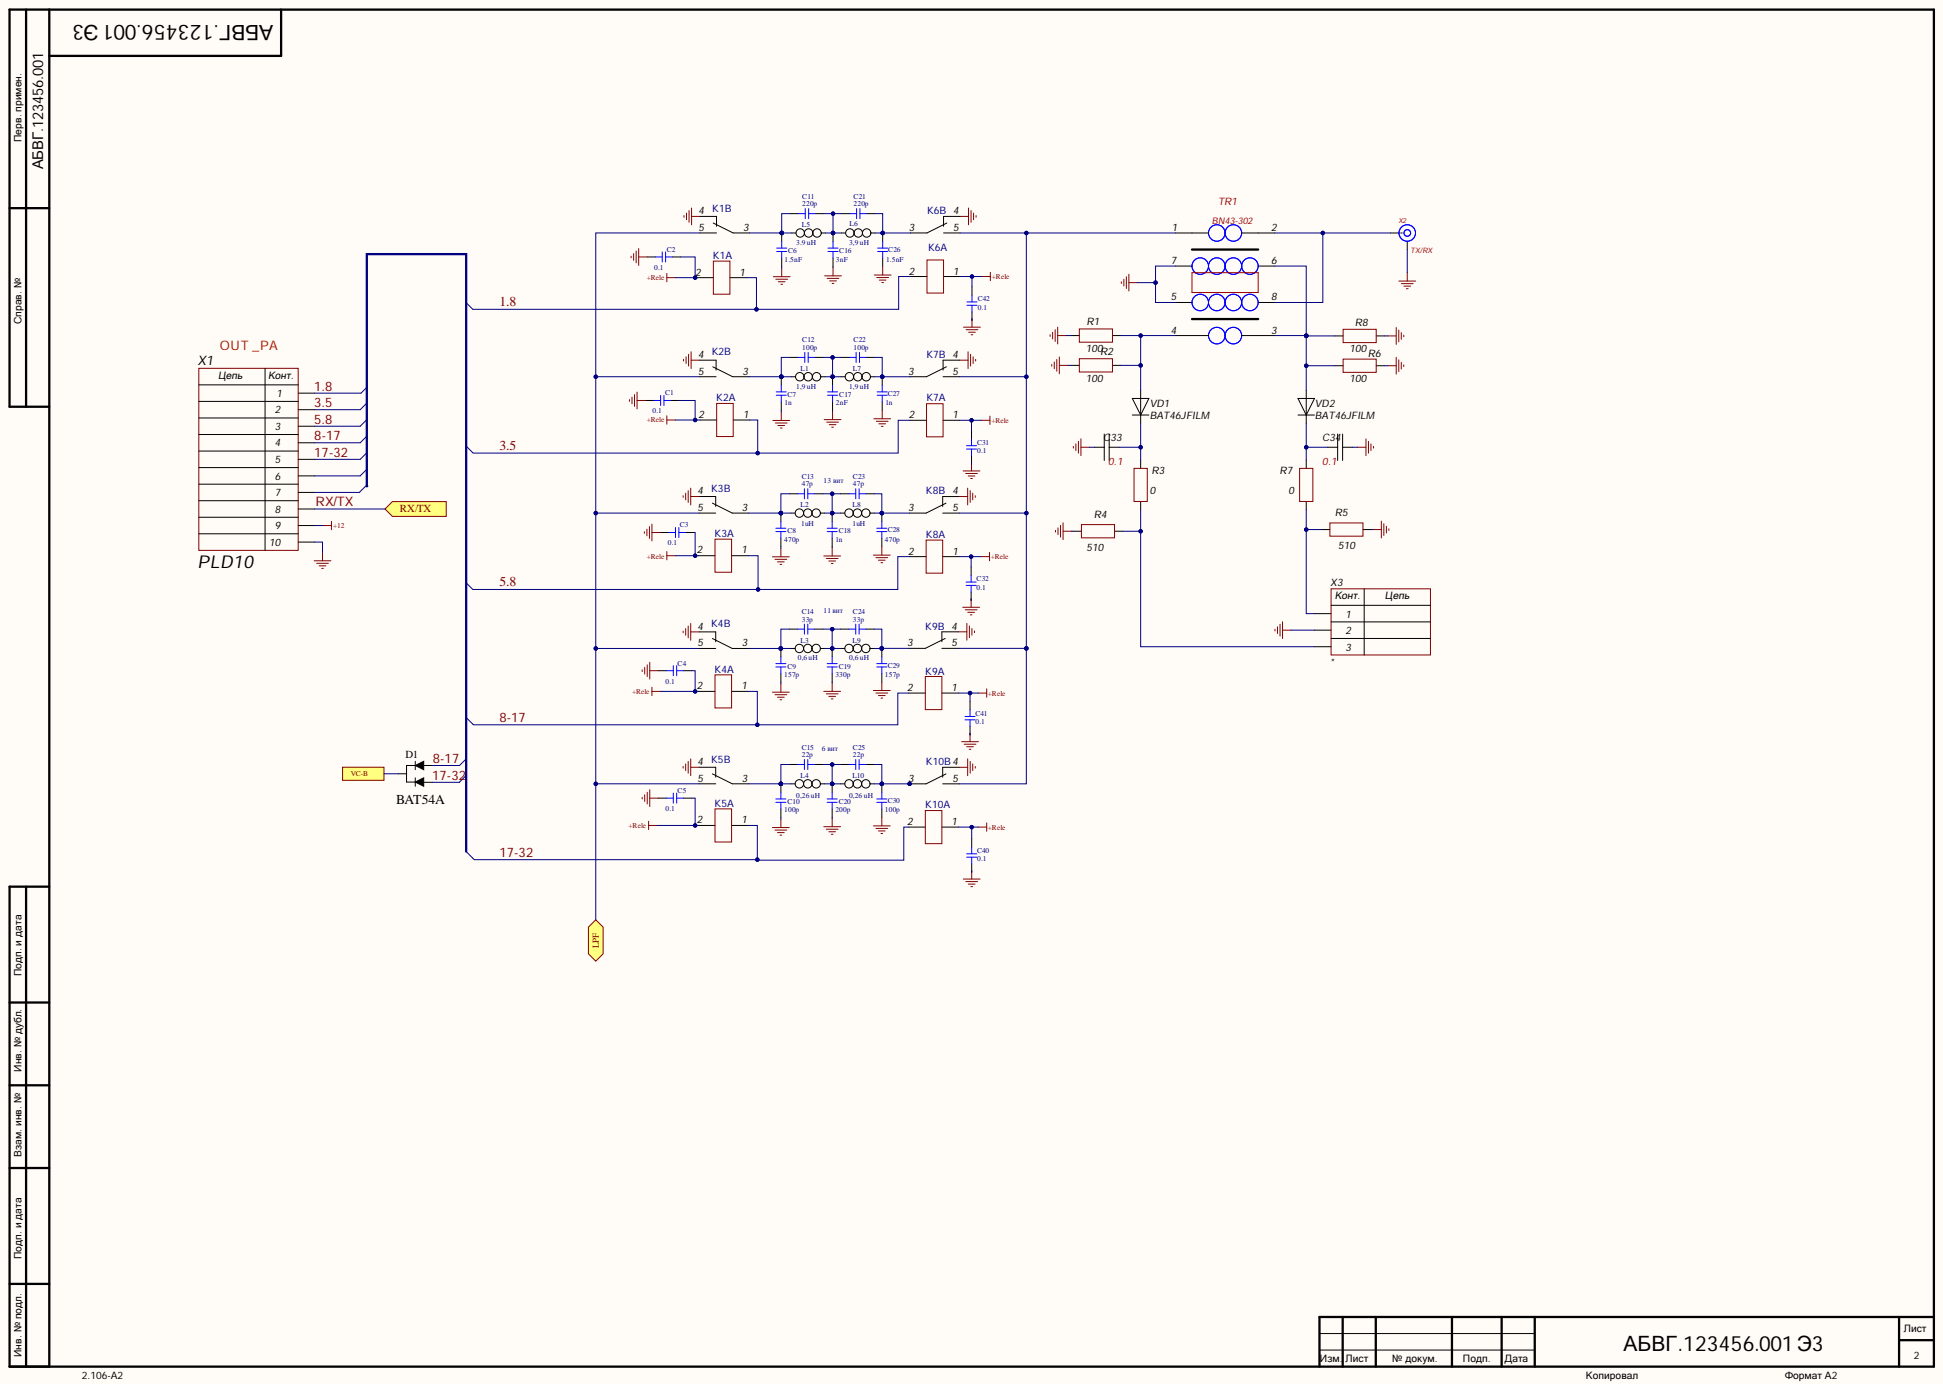
[picture p427: page 2]

Инв. № подл. Инв. № дубл. Подп. и дата Взам. инв. № Подп. и дата Перв. примен. Справ. №

1 PL Цепь | Конт. 3456789

X3* 12
Конт. | Цепь

АБВГ.1 2 3 4 5 6 . 001 Э 3 Изм. | Лист 2
Лист | № докум. | Подп. | Дата
