XGudron/UA3REO-DDC-Transceiver/Schematic/Wolf-Lite/Scheme/RFPower-Unit-v1.4-PZT2222.pdf

## 1KR¹⁷

### C4¹⁸⁰p

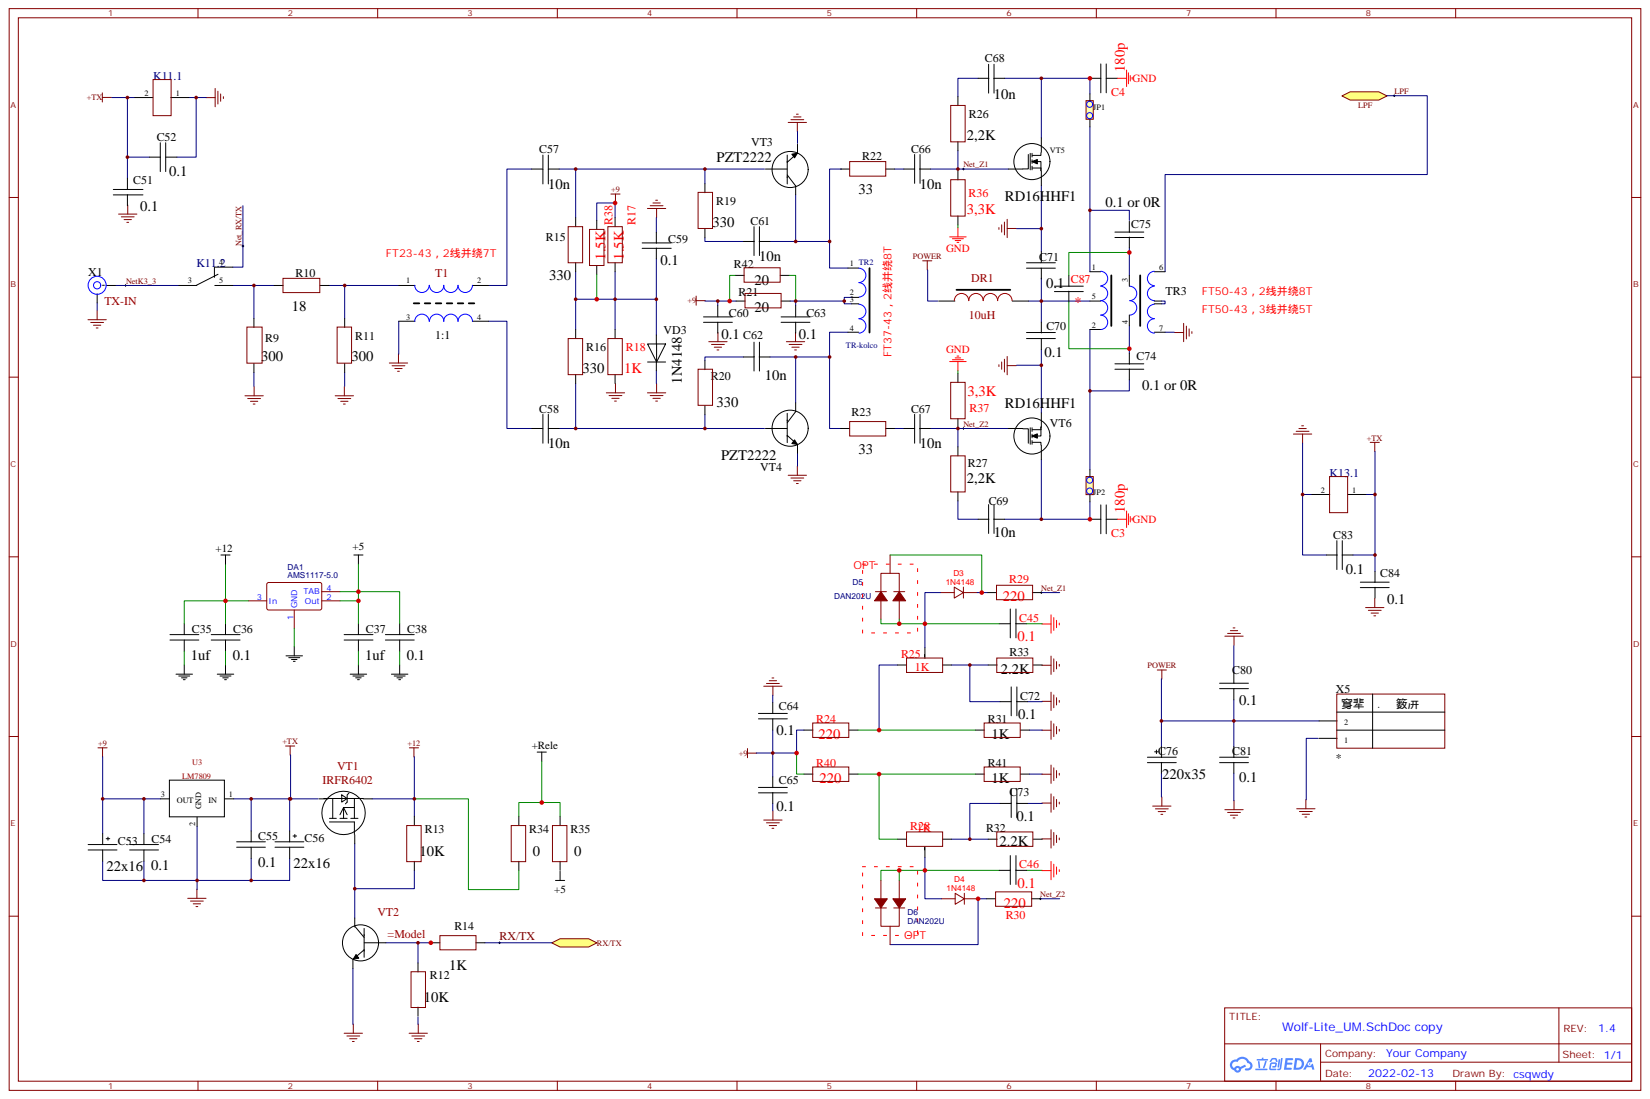
[picture p428: page 1]

# =DocumentNumber

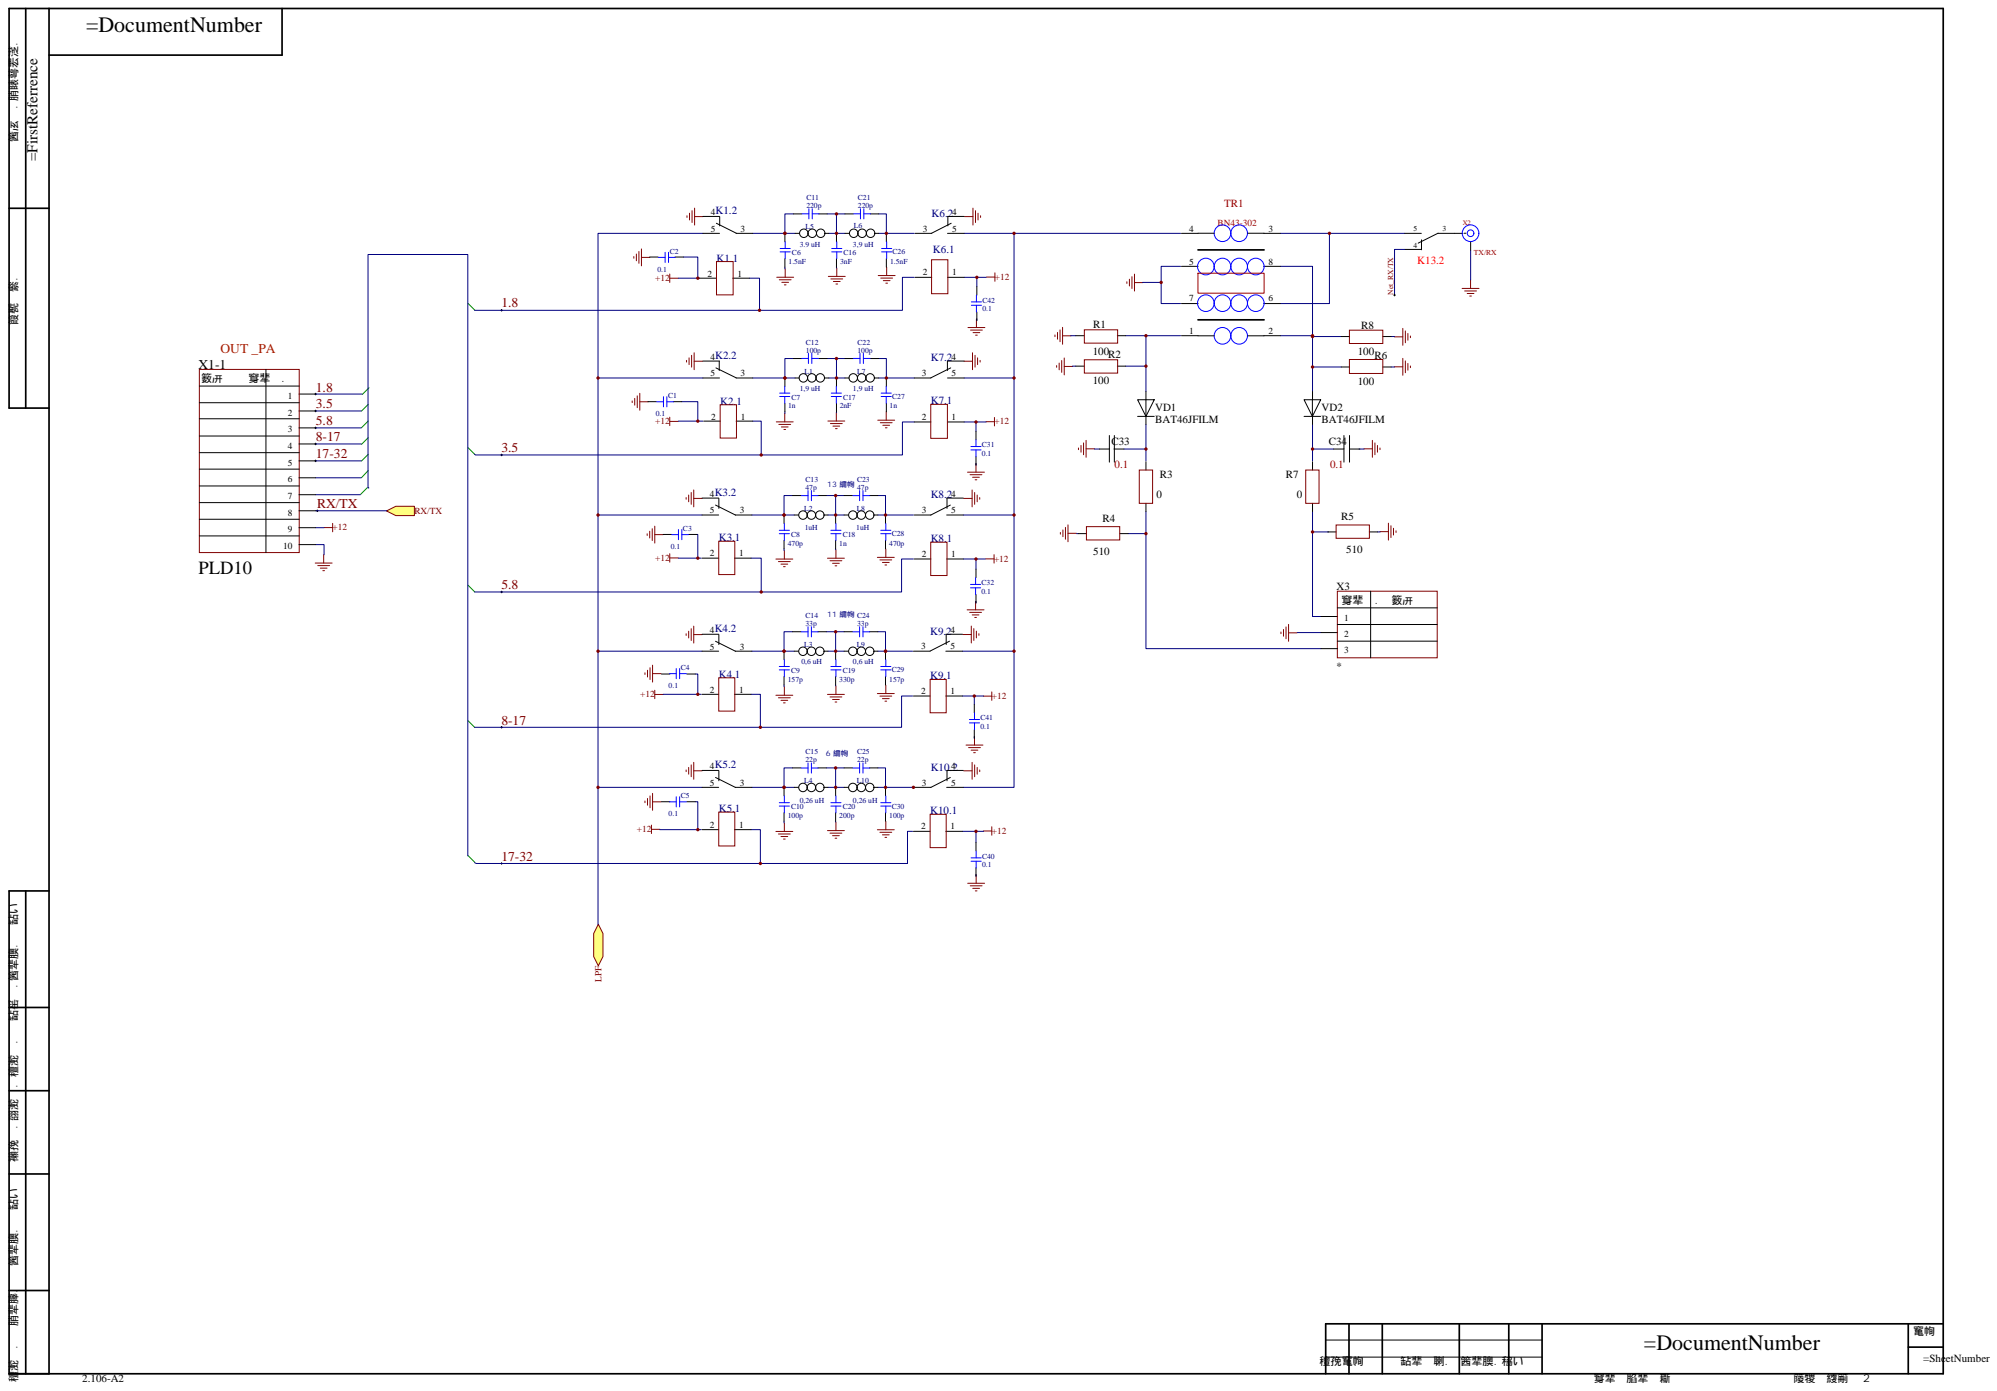
[picture p429: page 2]

䆄㵃 . 䏴㹃䐻. 䆄㵃 . 䍄䍃ᐻ. 䇴㹃䐿. 䍄い␰ 䄤㝃м. 䎄㵃 . 䇴㹃䐿. 䍄い␰ 䇴㕄в. 䏴䁃萼䍔㴀. 䈔㽄а䌠.
