XGudron/UA3REO-DDC-Transceiver/Schematic/Wolf-BA7LJL/Montage/WOLF-MIAN-11-3.pdf

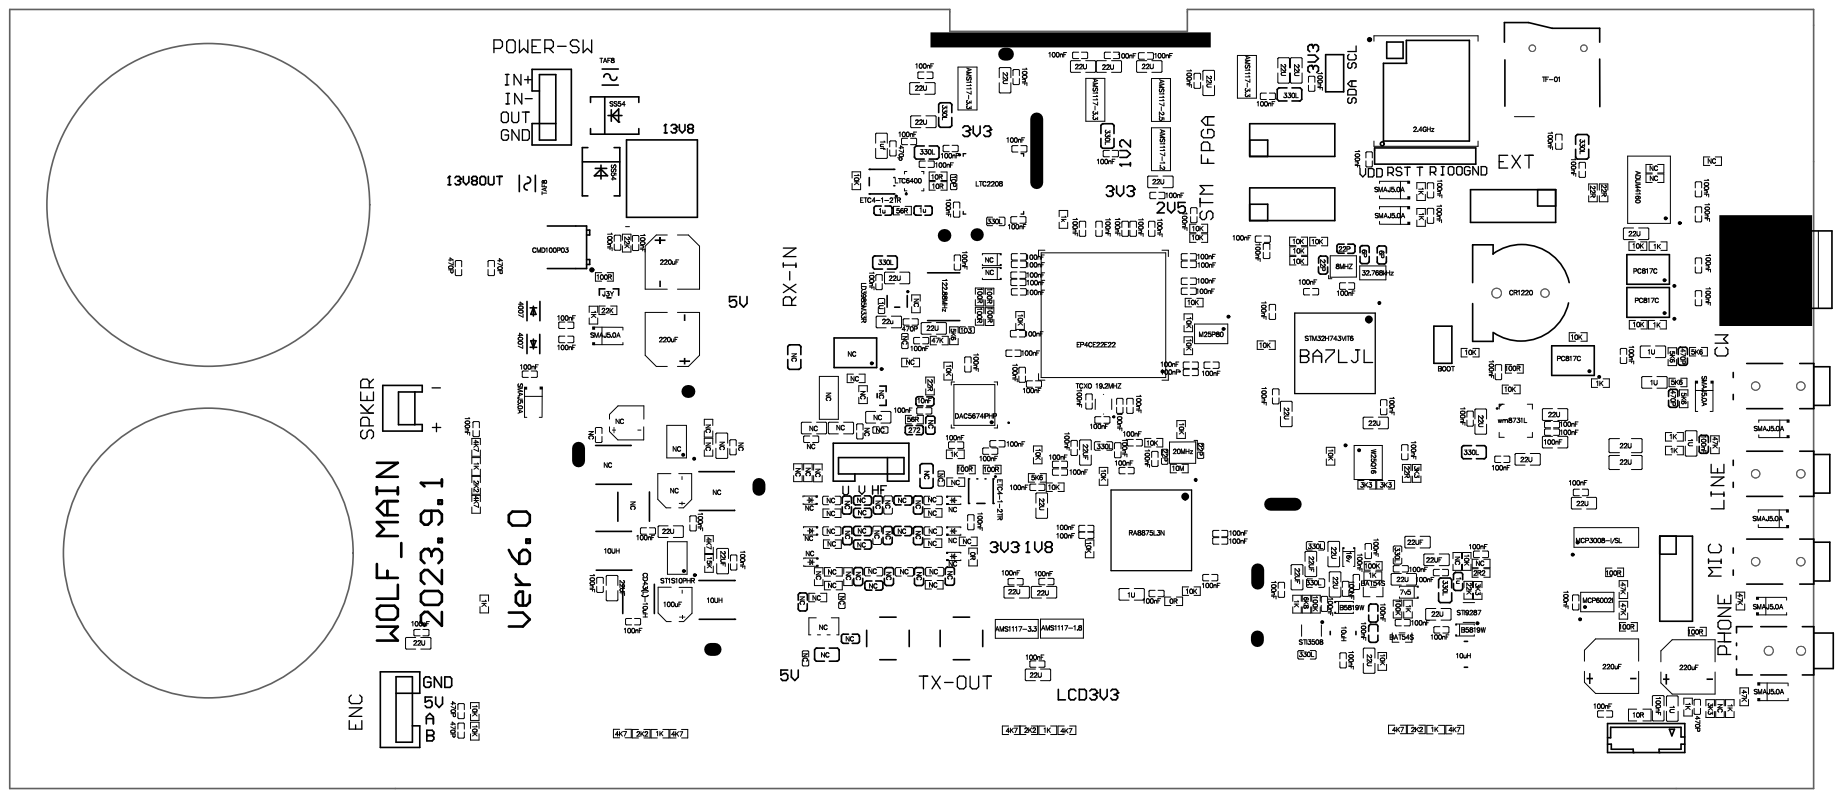
[picture p430: page 1]
