XGudron/UA3REO-DDC-Transceiver/Schematic/Wolf-BA7LJL/Montage/WOLF-PA 11-3.pdf

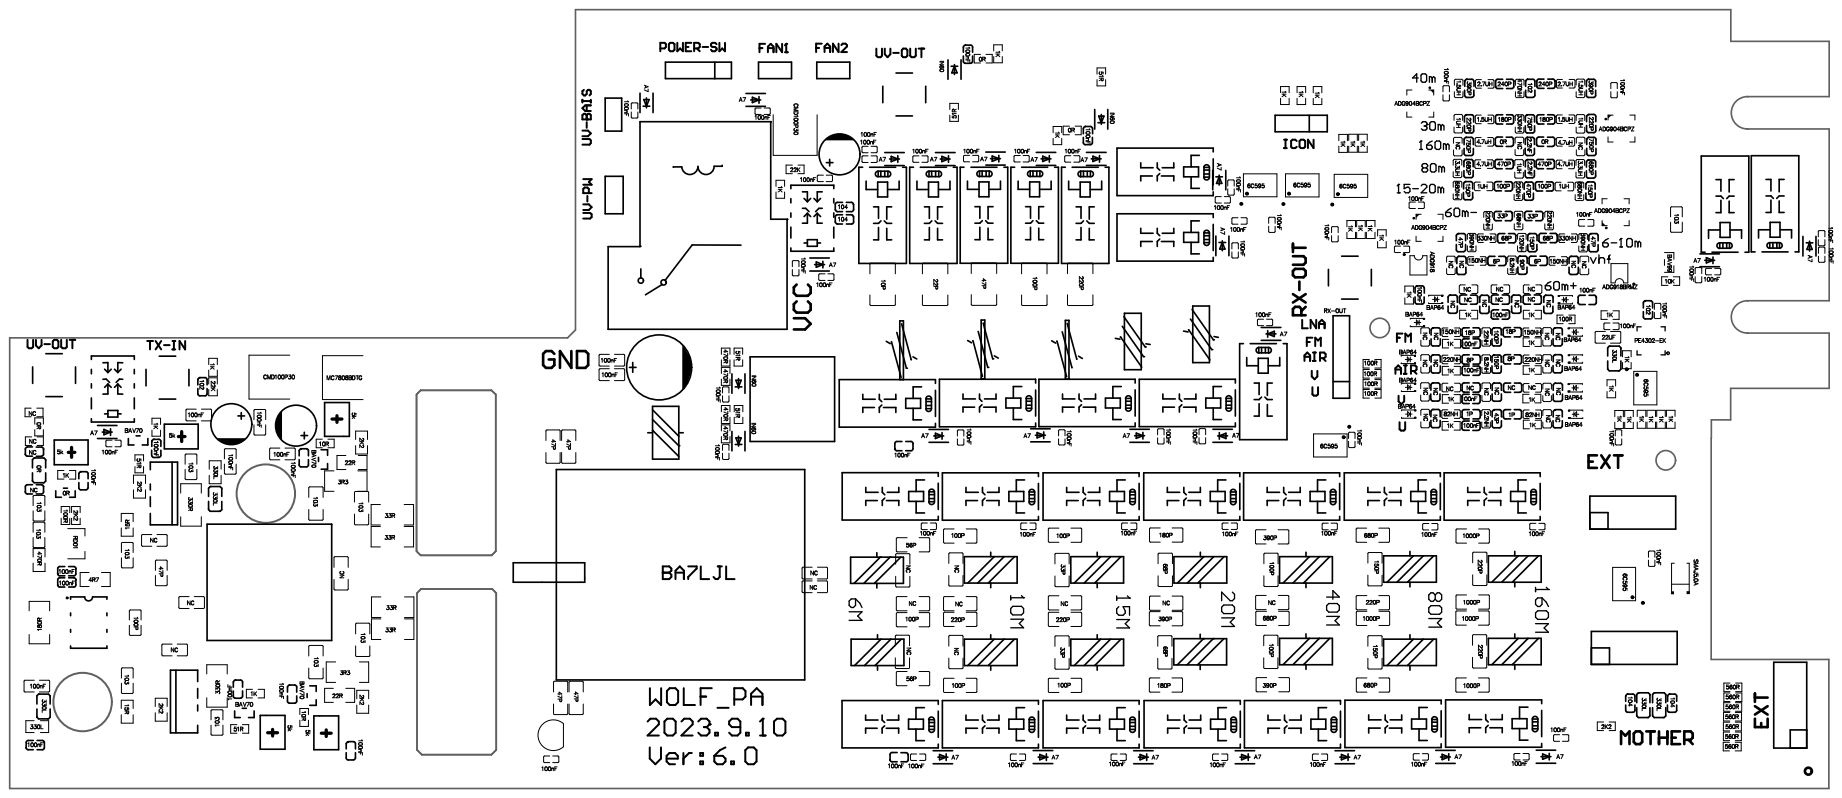
[picture p431: page 1]
