XGudron/UA3REO-DDC-Transceiver/Schematic/Wolf-DK102/Schematic/DK-102_PA_V01_240821.pdf

AF GAIN | SHIFT
+3V3 | +3V3

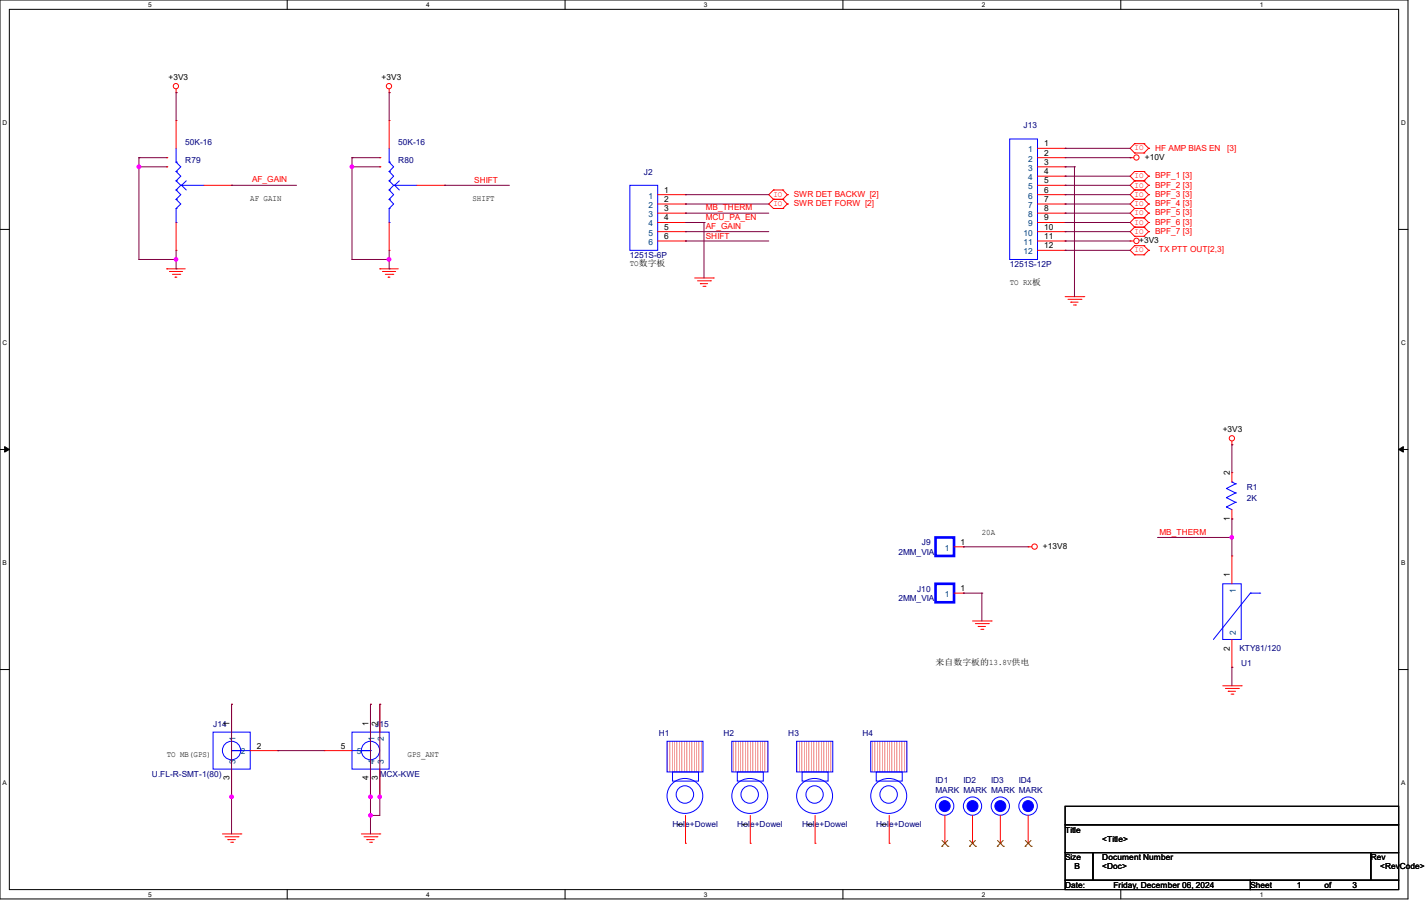
[picture p432: page 1]

IO SWR DET BACKW [2]
IO SWR DET FORW [2]

D

S

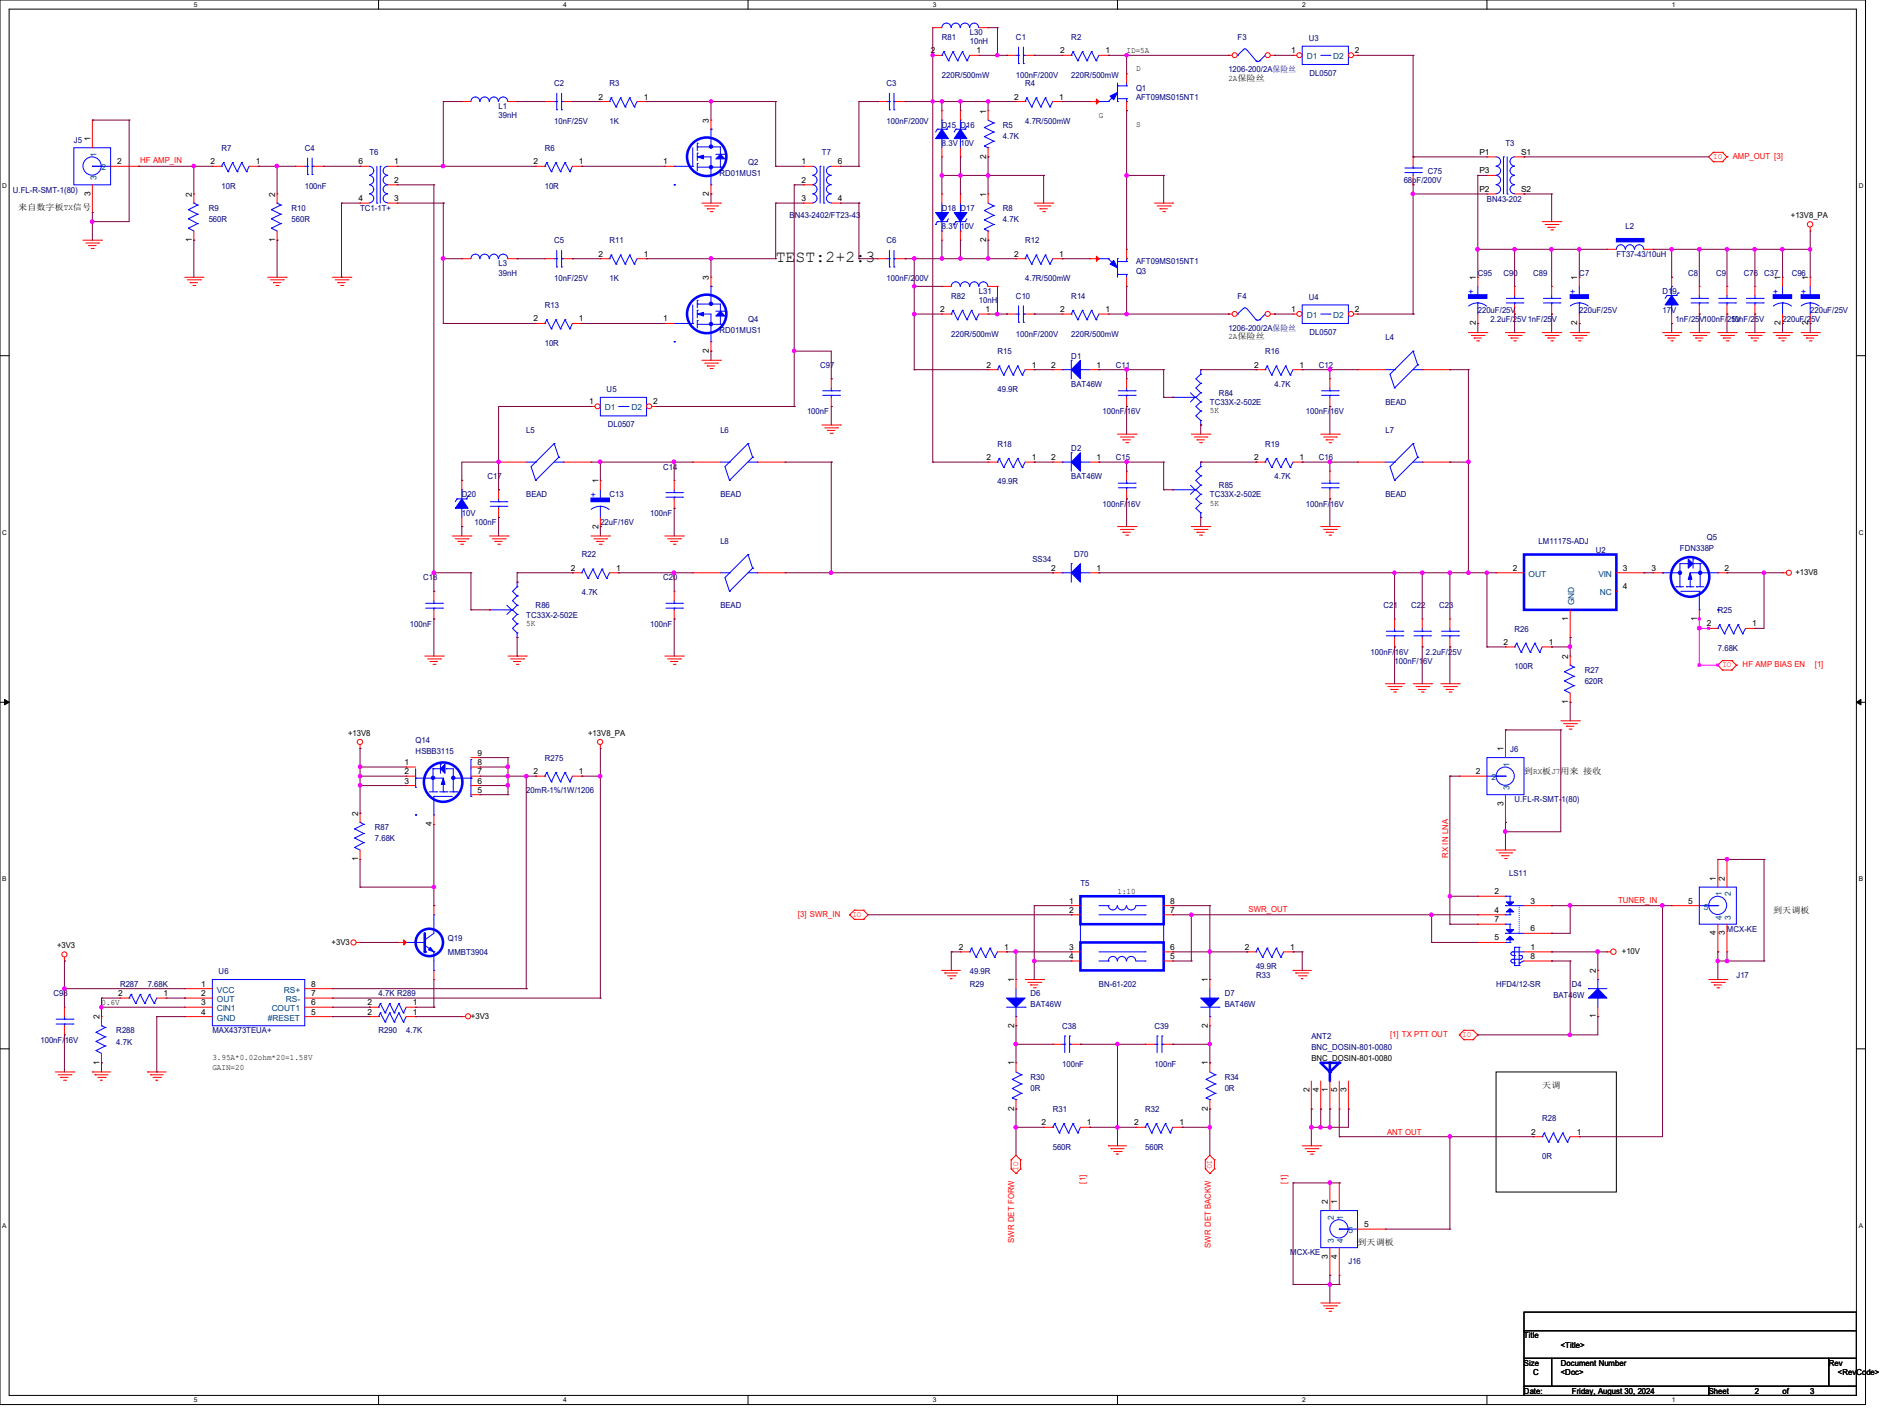
[picture p433: page 2]

IO HF AMP BIAS EN [1]

M

H

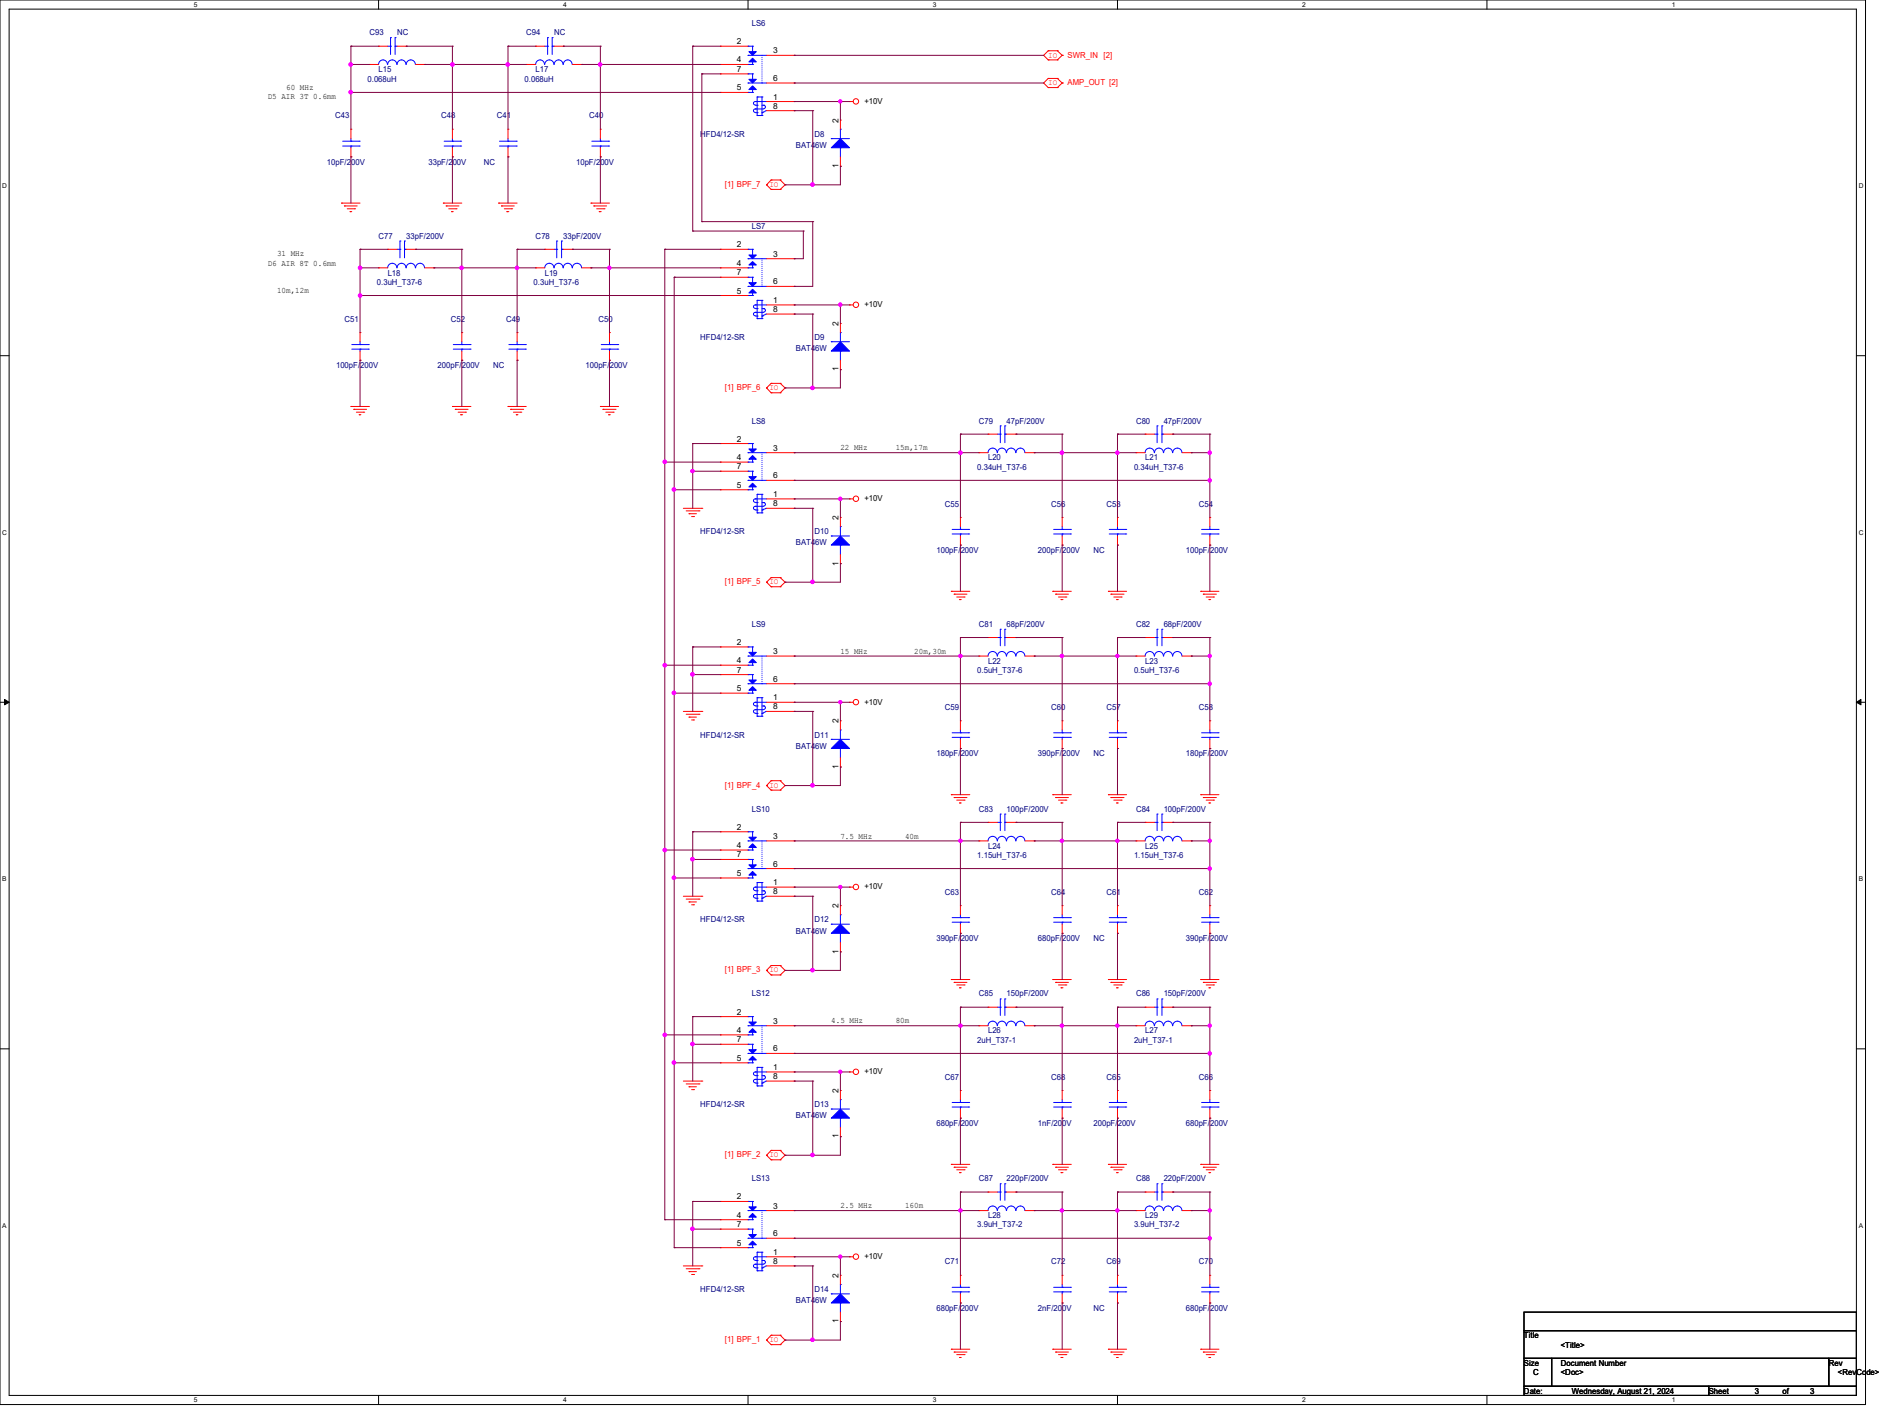
[picture p434: page 3]
Title Size; Title
