XGudron/UA3REO-DDC-Transceiver/Schematic/Wolf-DK102/Schematic/DK-102_TUNING_V01_240414.pdf

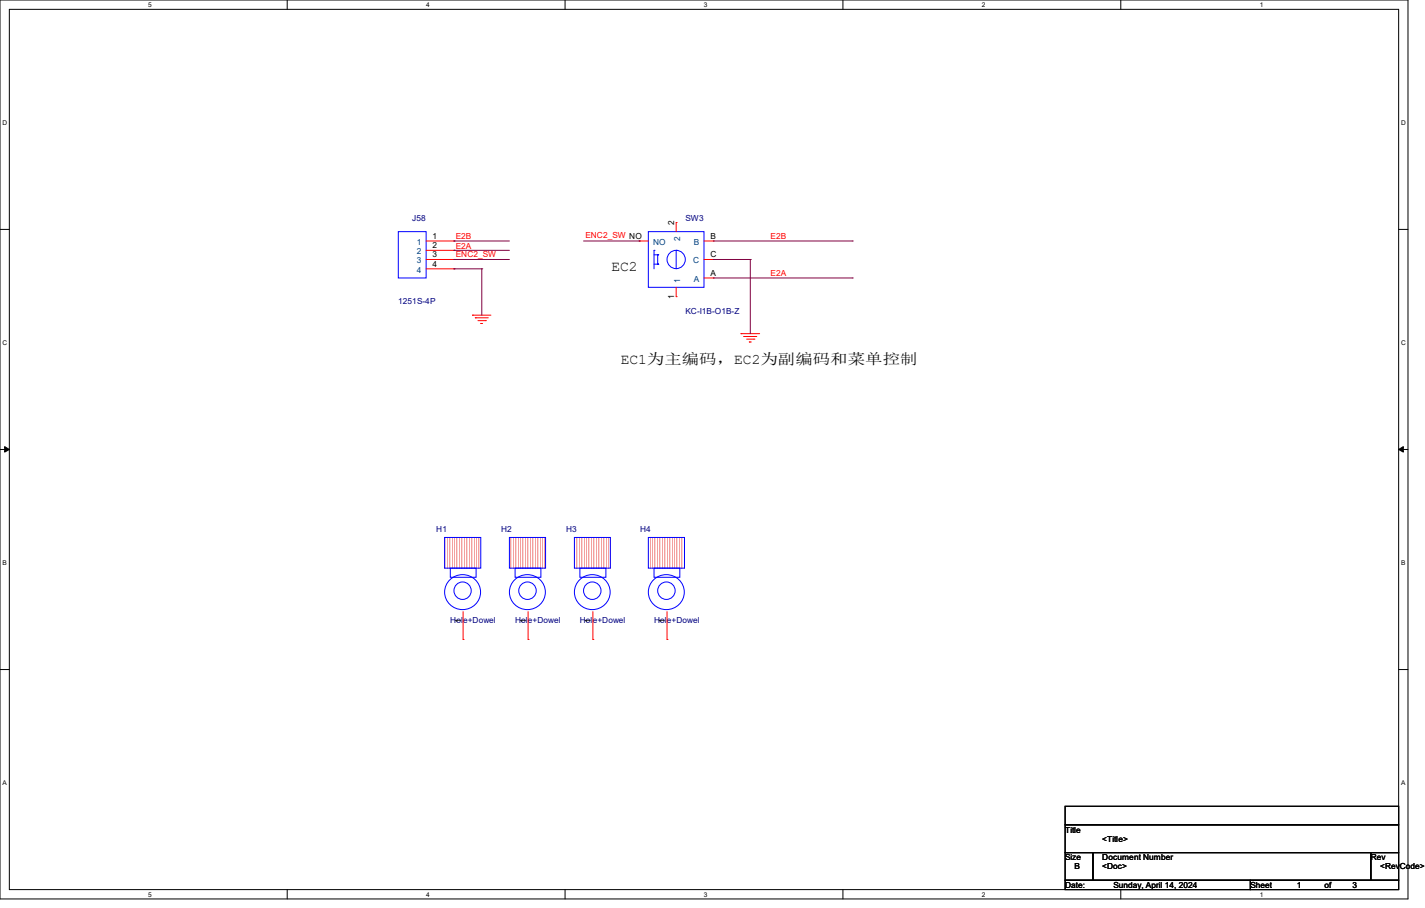
[picture p435: page 1]
EC1为主编码，EC2为副编码和菜单控制; Title; Size; Document Number; Rev; Date:; Sheet; <Doc>; <RevCode>; <Title>; Sunday, April 14, 2024; Hol1e+Dowel; Ho1le+Dowel; ENC2_SW; E2A ENC2_SW
