XGudron/UA3REO-DDC-Transceiver/Schematic/Wolf-Adapter/Scheme/Wolf-Adapter-rev2.pdf

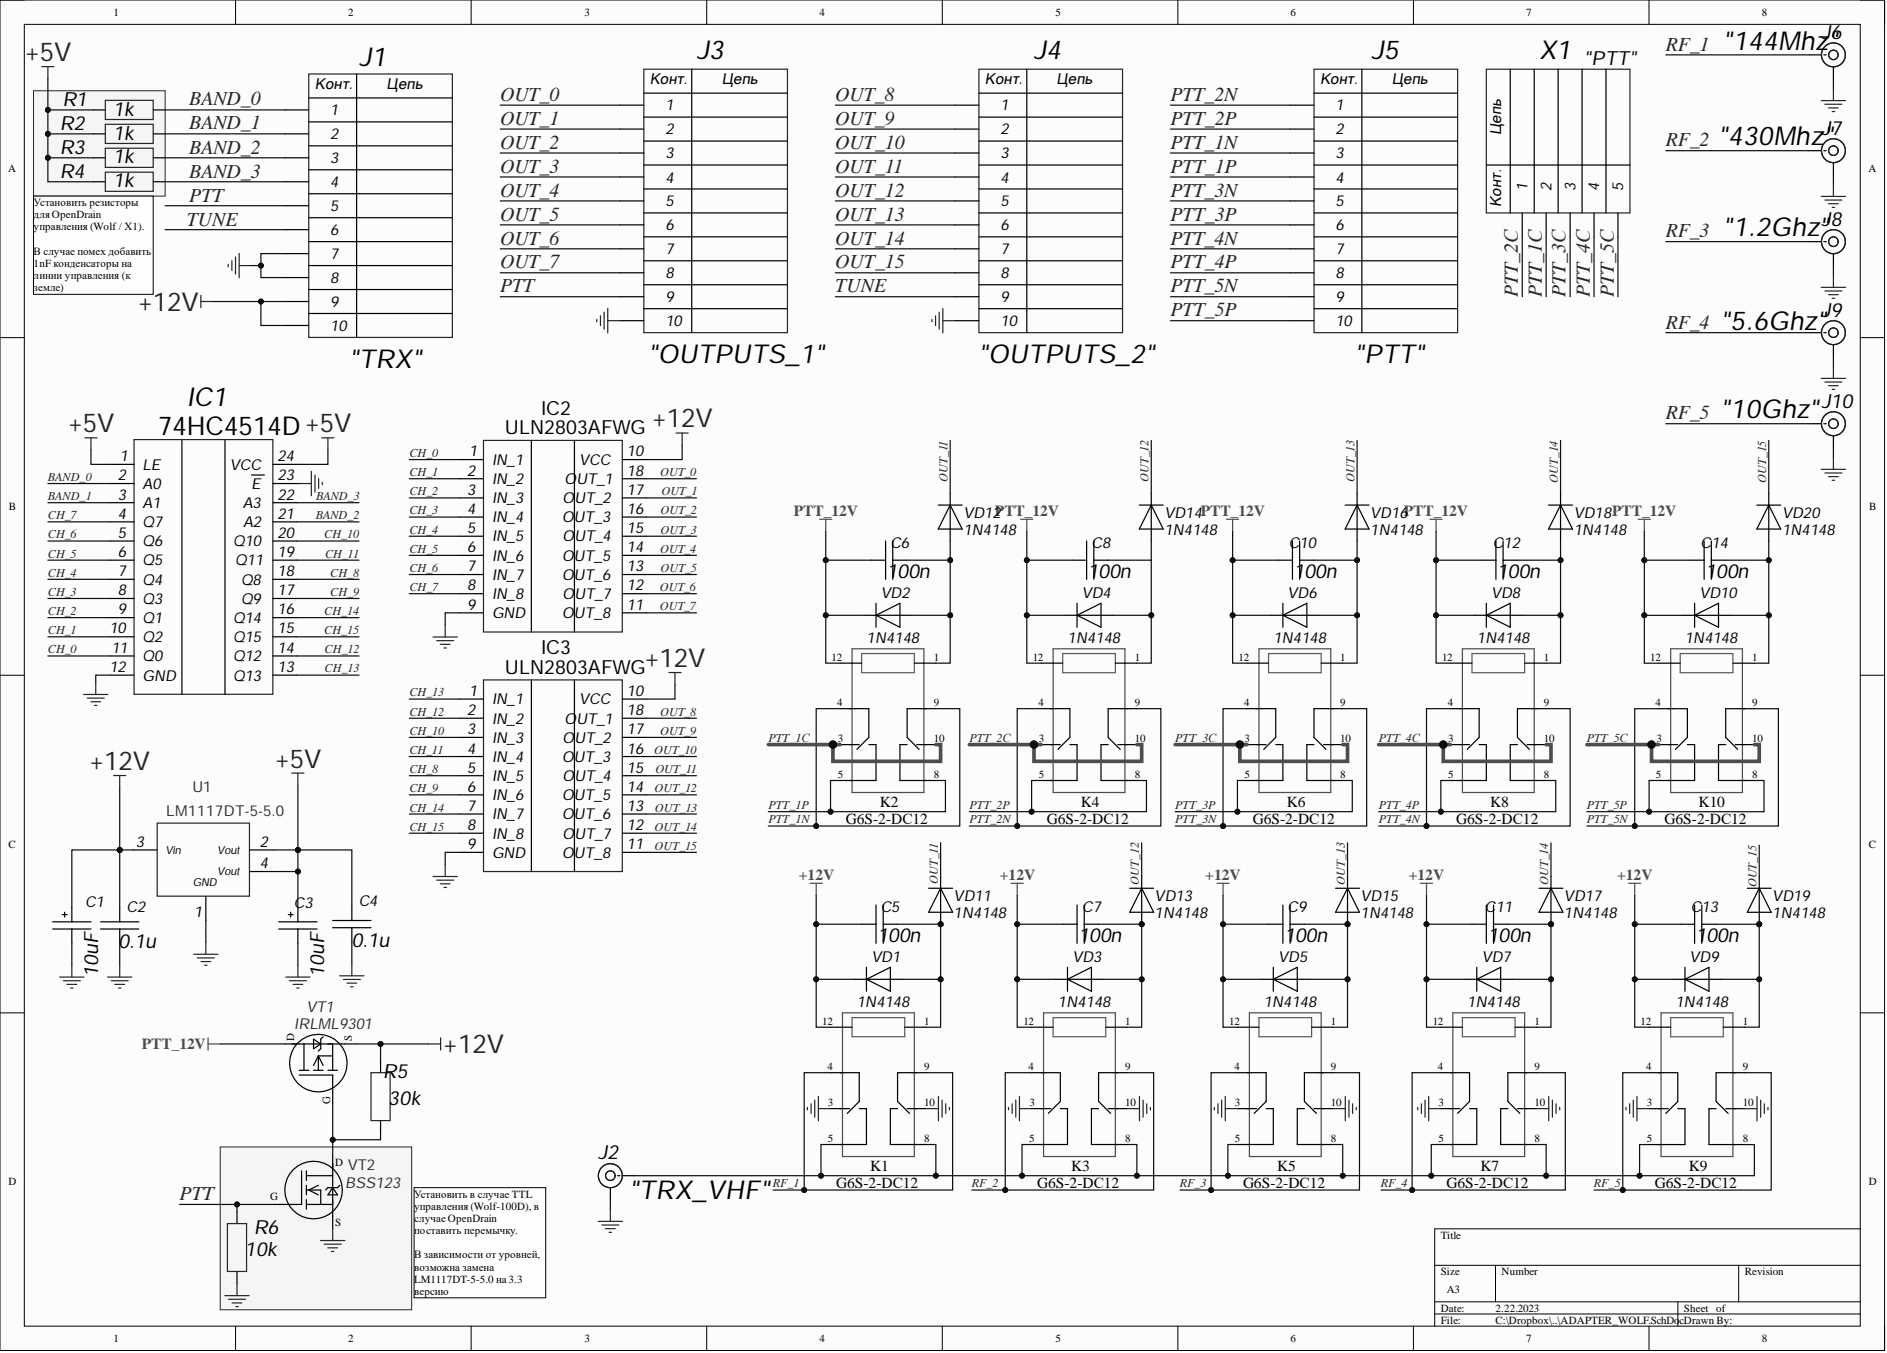
[picture p436: page 1]

Конт. | Цепь

10
