XGudron/UA3REO-DDC-Transceiver/Schematic/Wolf-Lite/Scheme/AD9226-LQFP.pdf

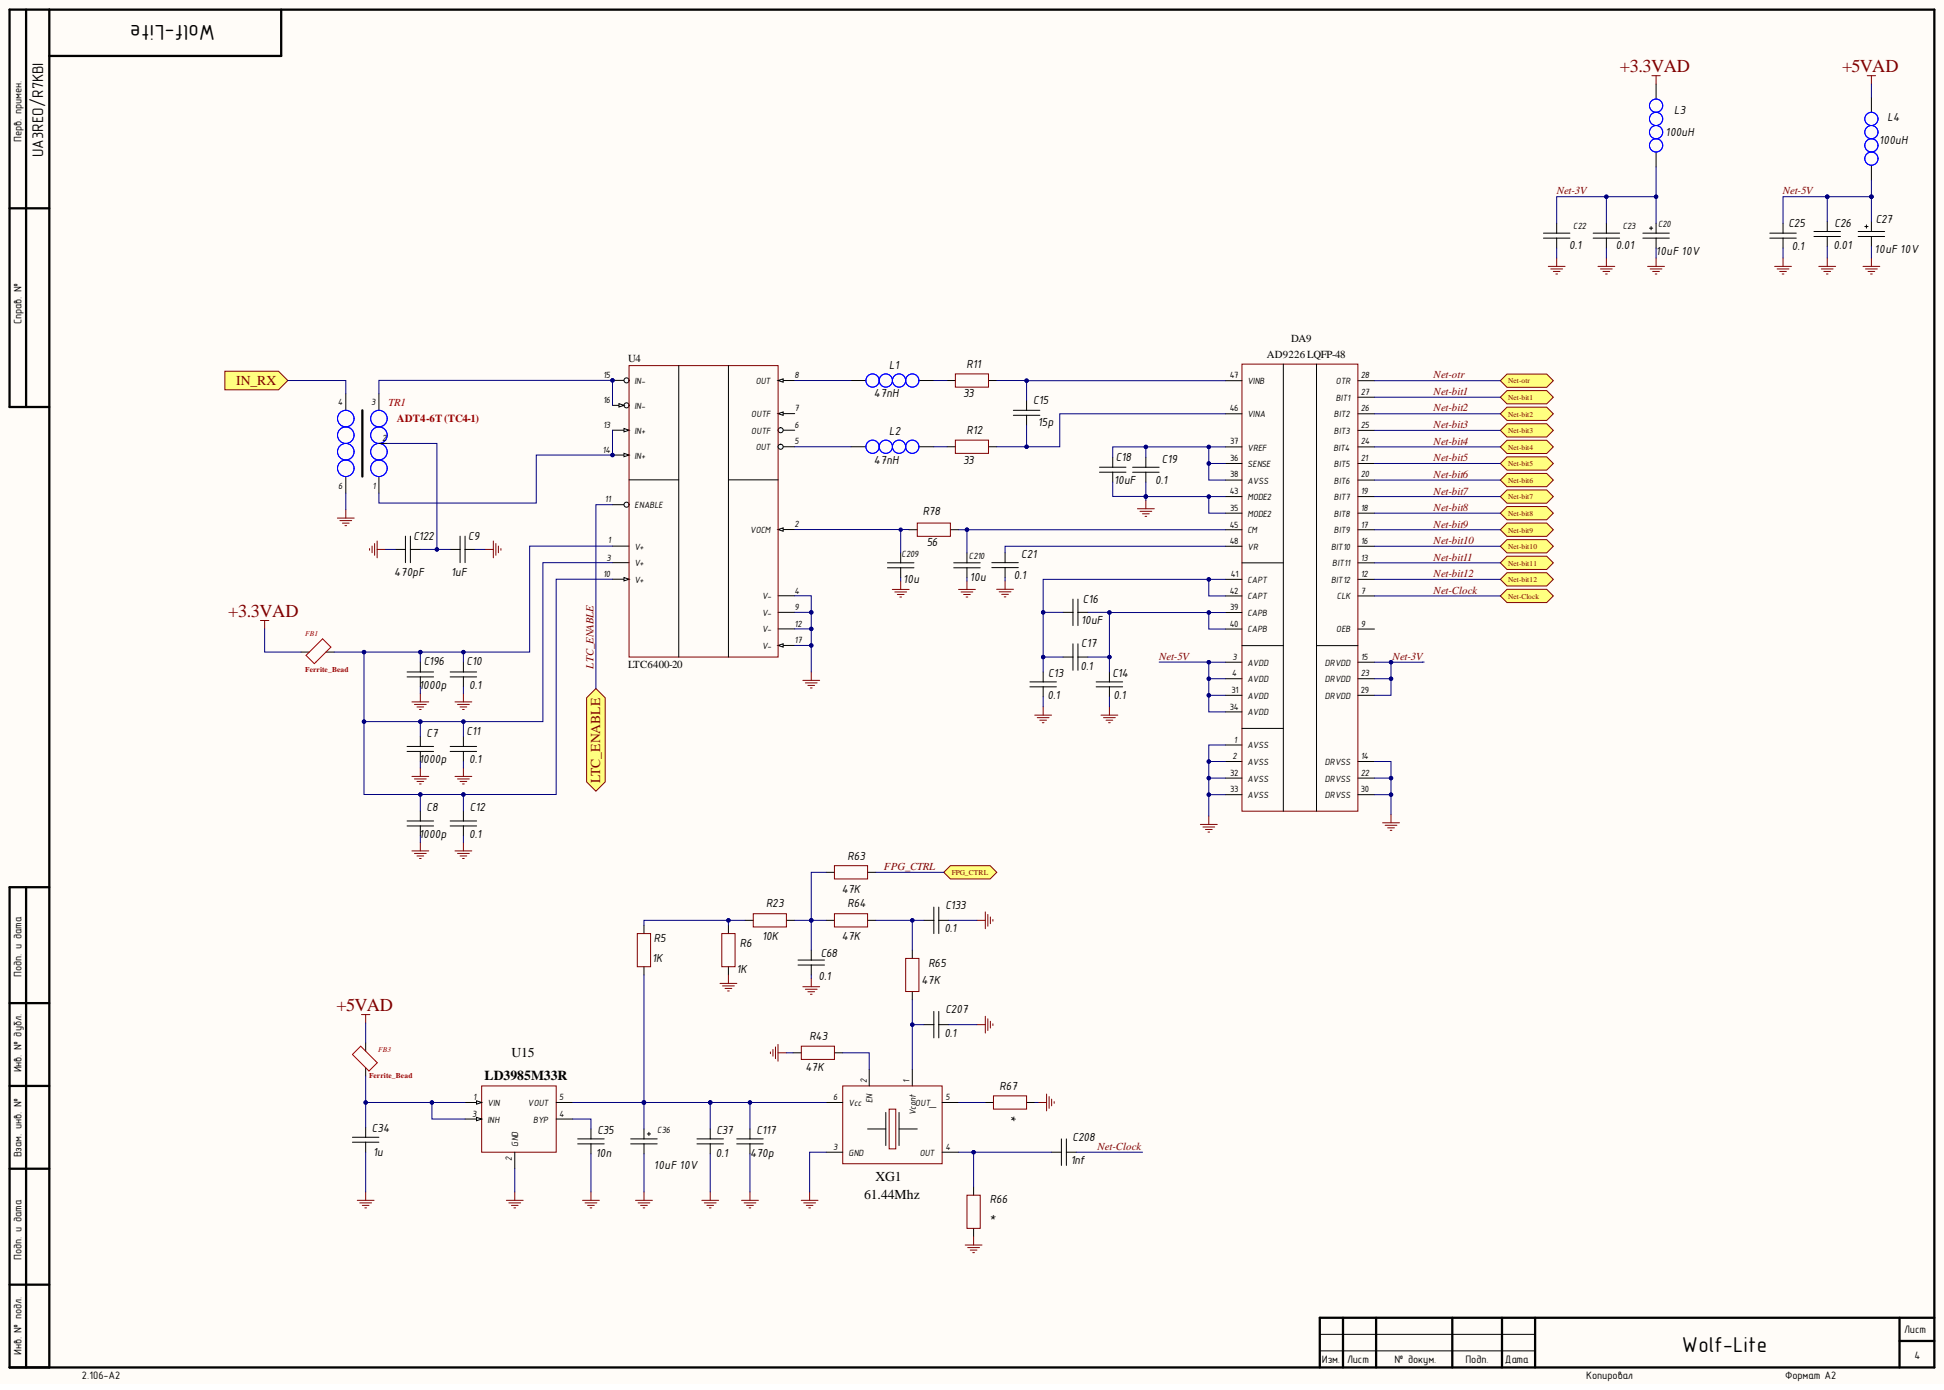
[picture p437: page 1]

Инв. № подл. Инв. № дубл. Подп. и дата Взам. инв. № Подп. и дата Перв. примен. Справ. №

3 6 | 21 Ne t -b i t5
3 8 | 20 Ne t -b i t6

AVD D AVD D | D RVD D D RVD D D RVD D D RVS S D RVS S D RVS S
