XGudron/UA3REO-DDC-Transceiver/Schematic/Wolf-X1/Assembly/Top_case.PDF

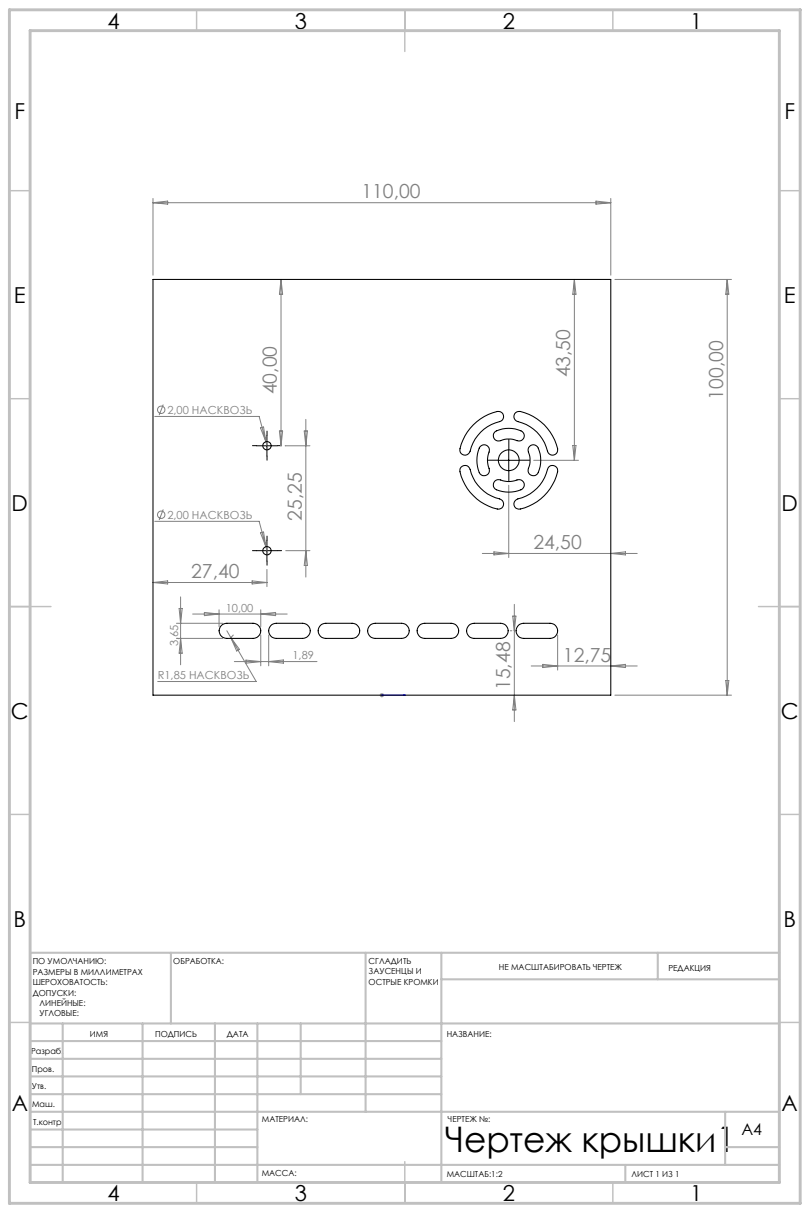
[picture p438: page 1]
2,00 НАСКВОЗЬ; R1,85 НАСКВОЗЬ; МАСШТАБ:1:2; ЛИСТ 1 ИЗ 1; НЕ МАСШТАБИРОВАТЬ ЧЕРТЕЖ; РЕДАКЦИЯ; ЗАУСЕНЦЫ И ОСТРЫЕ КРОМКИ; ПО УМОЛЧАНИЮ:; ОБРАБОТКА:; РАЗМЕРЫ В МИЛЛИМЕТРАХ

ИМЯ | ПОДПИСЬ | ДАТА | | | | НАЗВАНИЕ:
Т.контр | | | | МАТЕРИАЛ: | ЧЕРТЕЖ №: Чертеж крышки1 МАССА: | A4

Разраб.
Пров.
Утв.
Маш.
