XGudron/UA3REO-DDC-Transceiver/Schematic/Wolf-X1/Assembly/X1_MAIN_V1.3.PDF

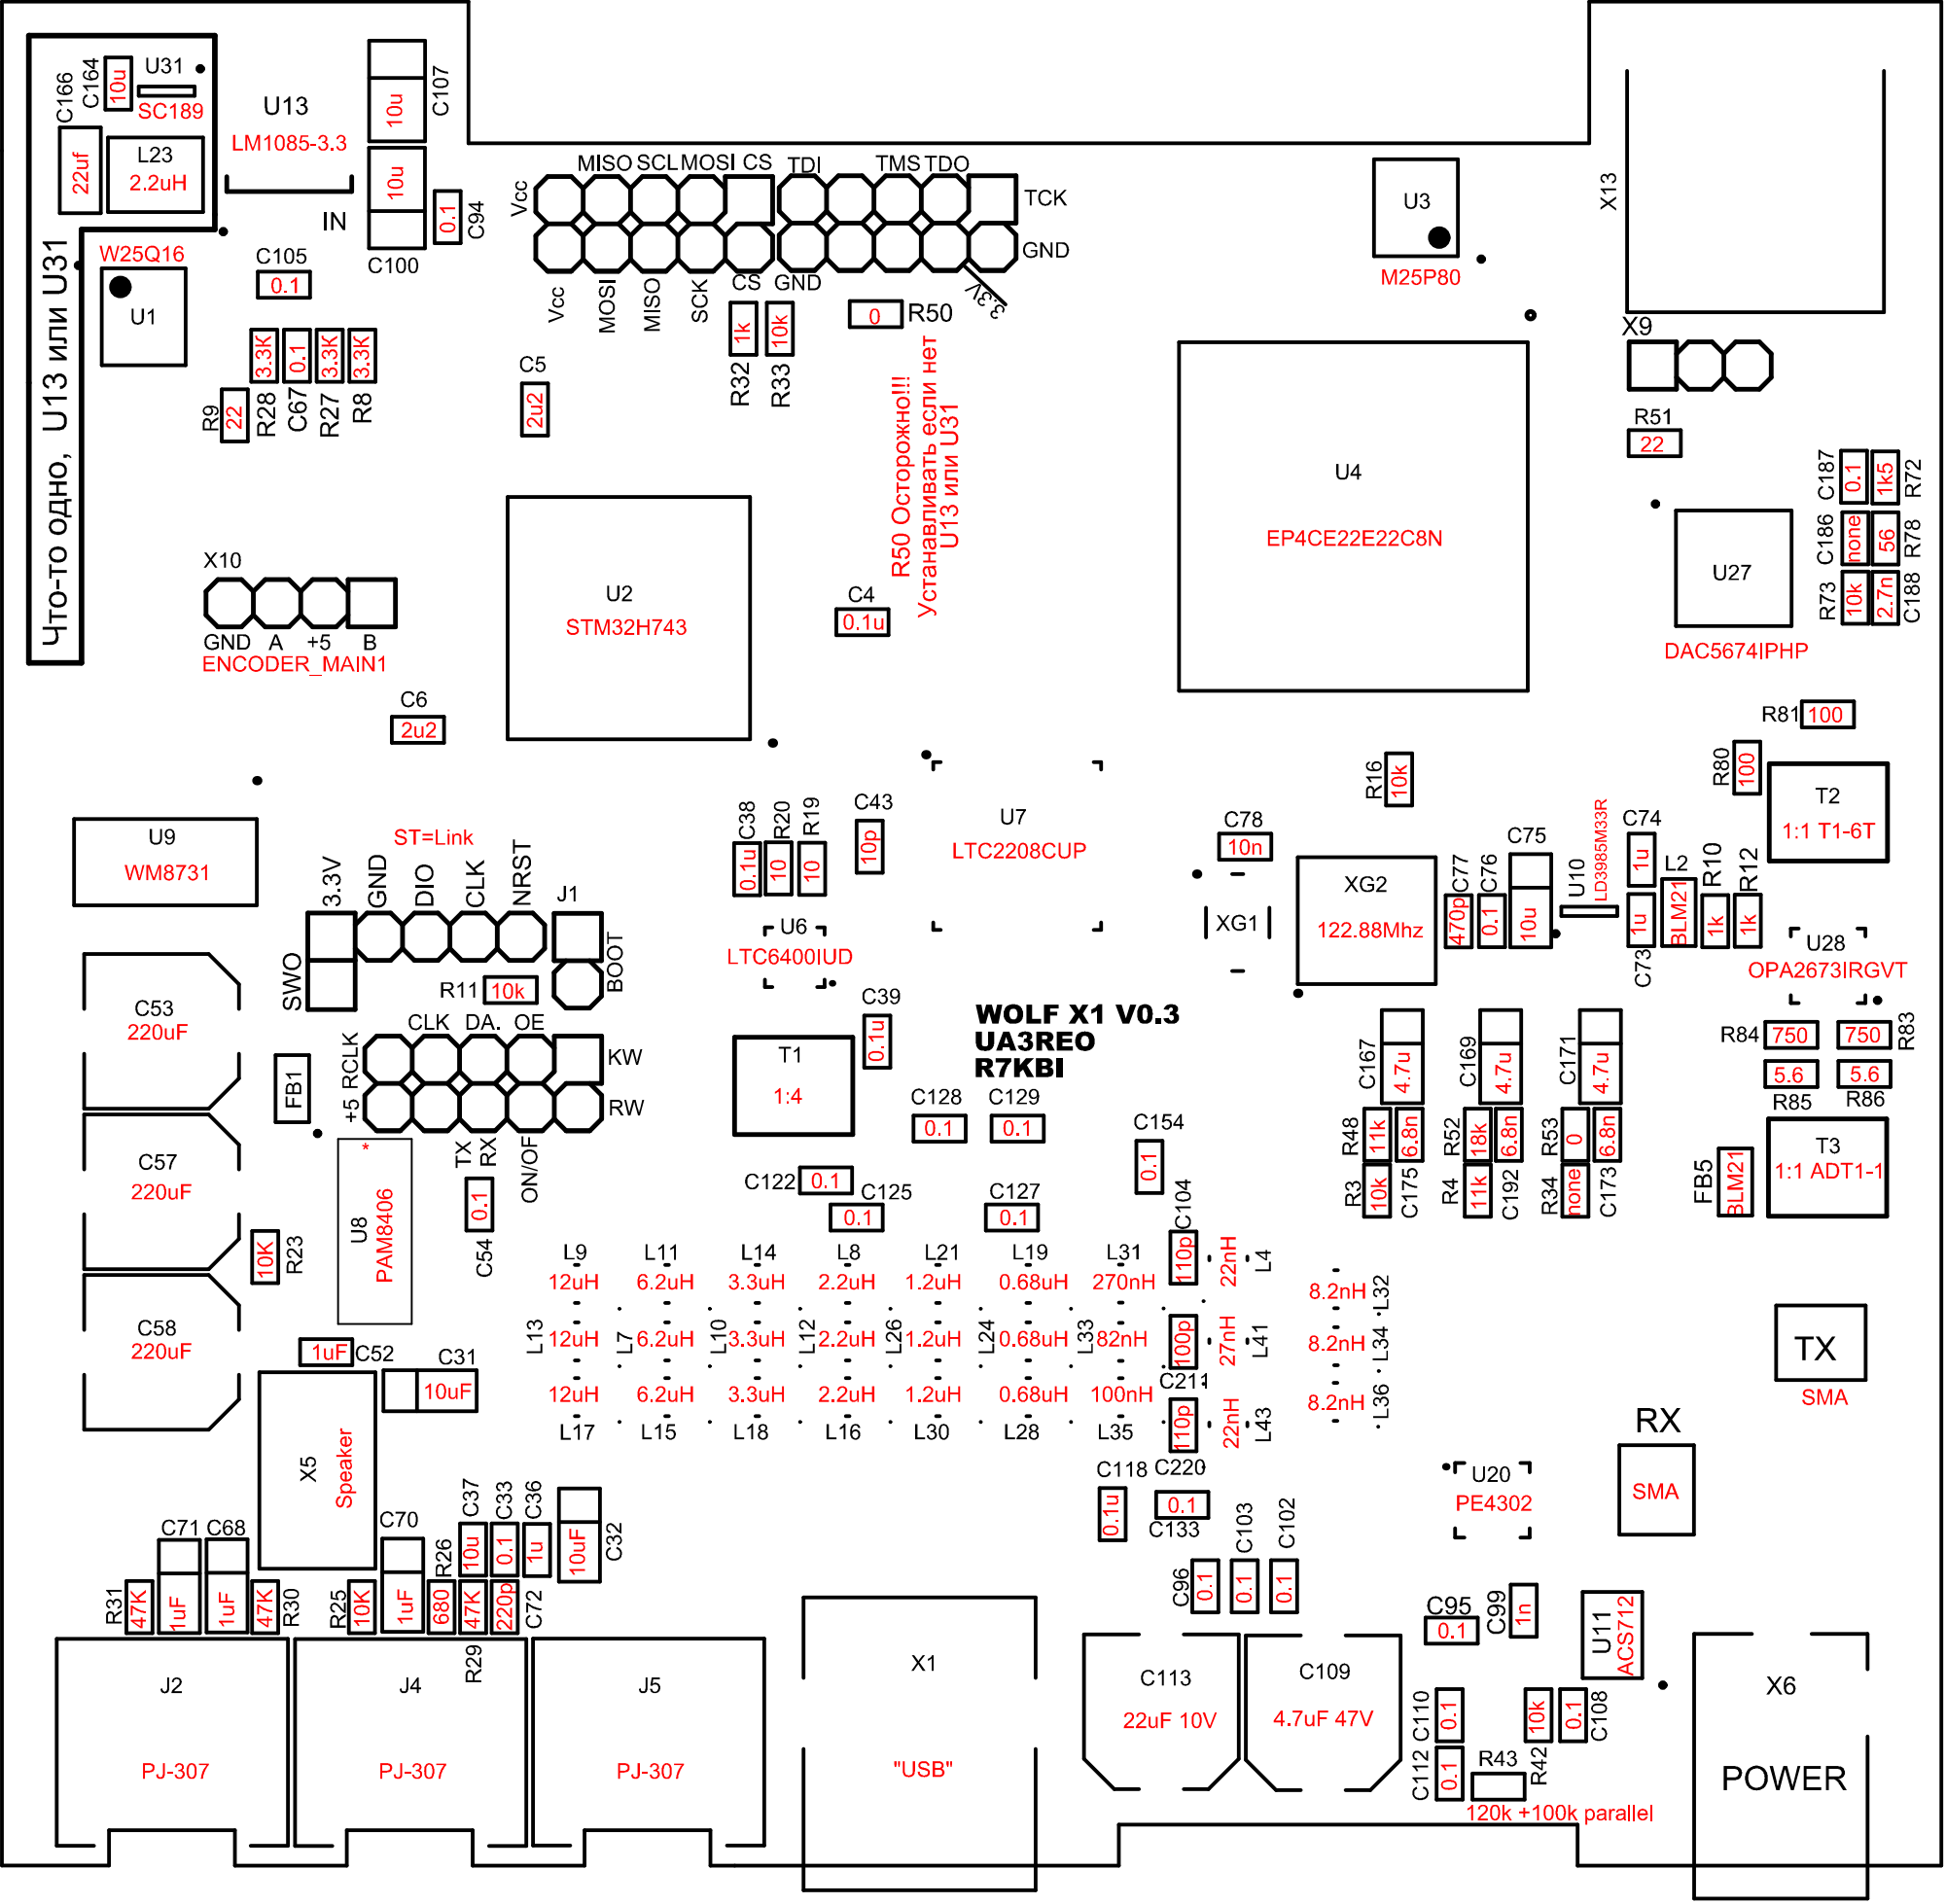
[picture p439: page 1]

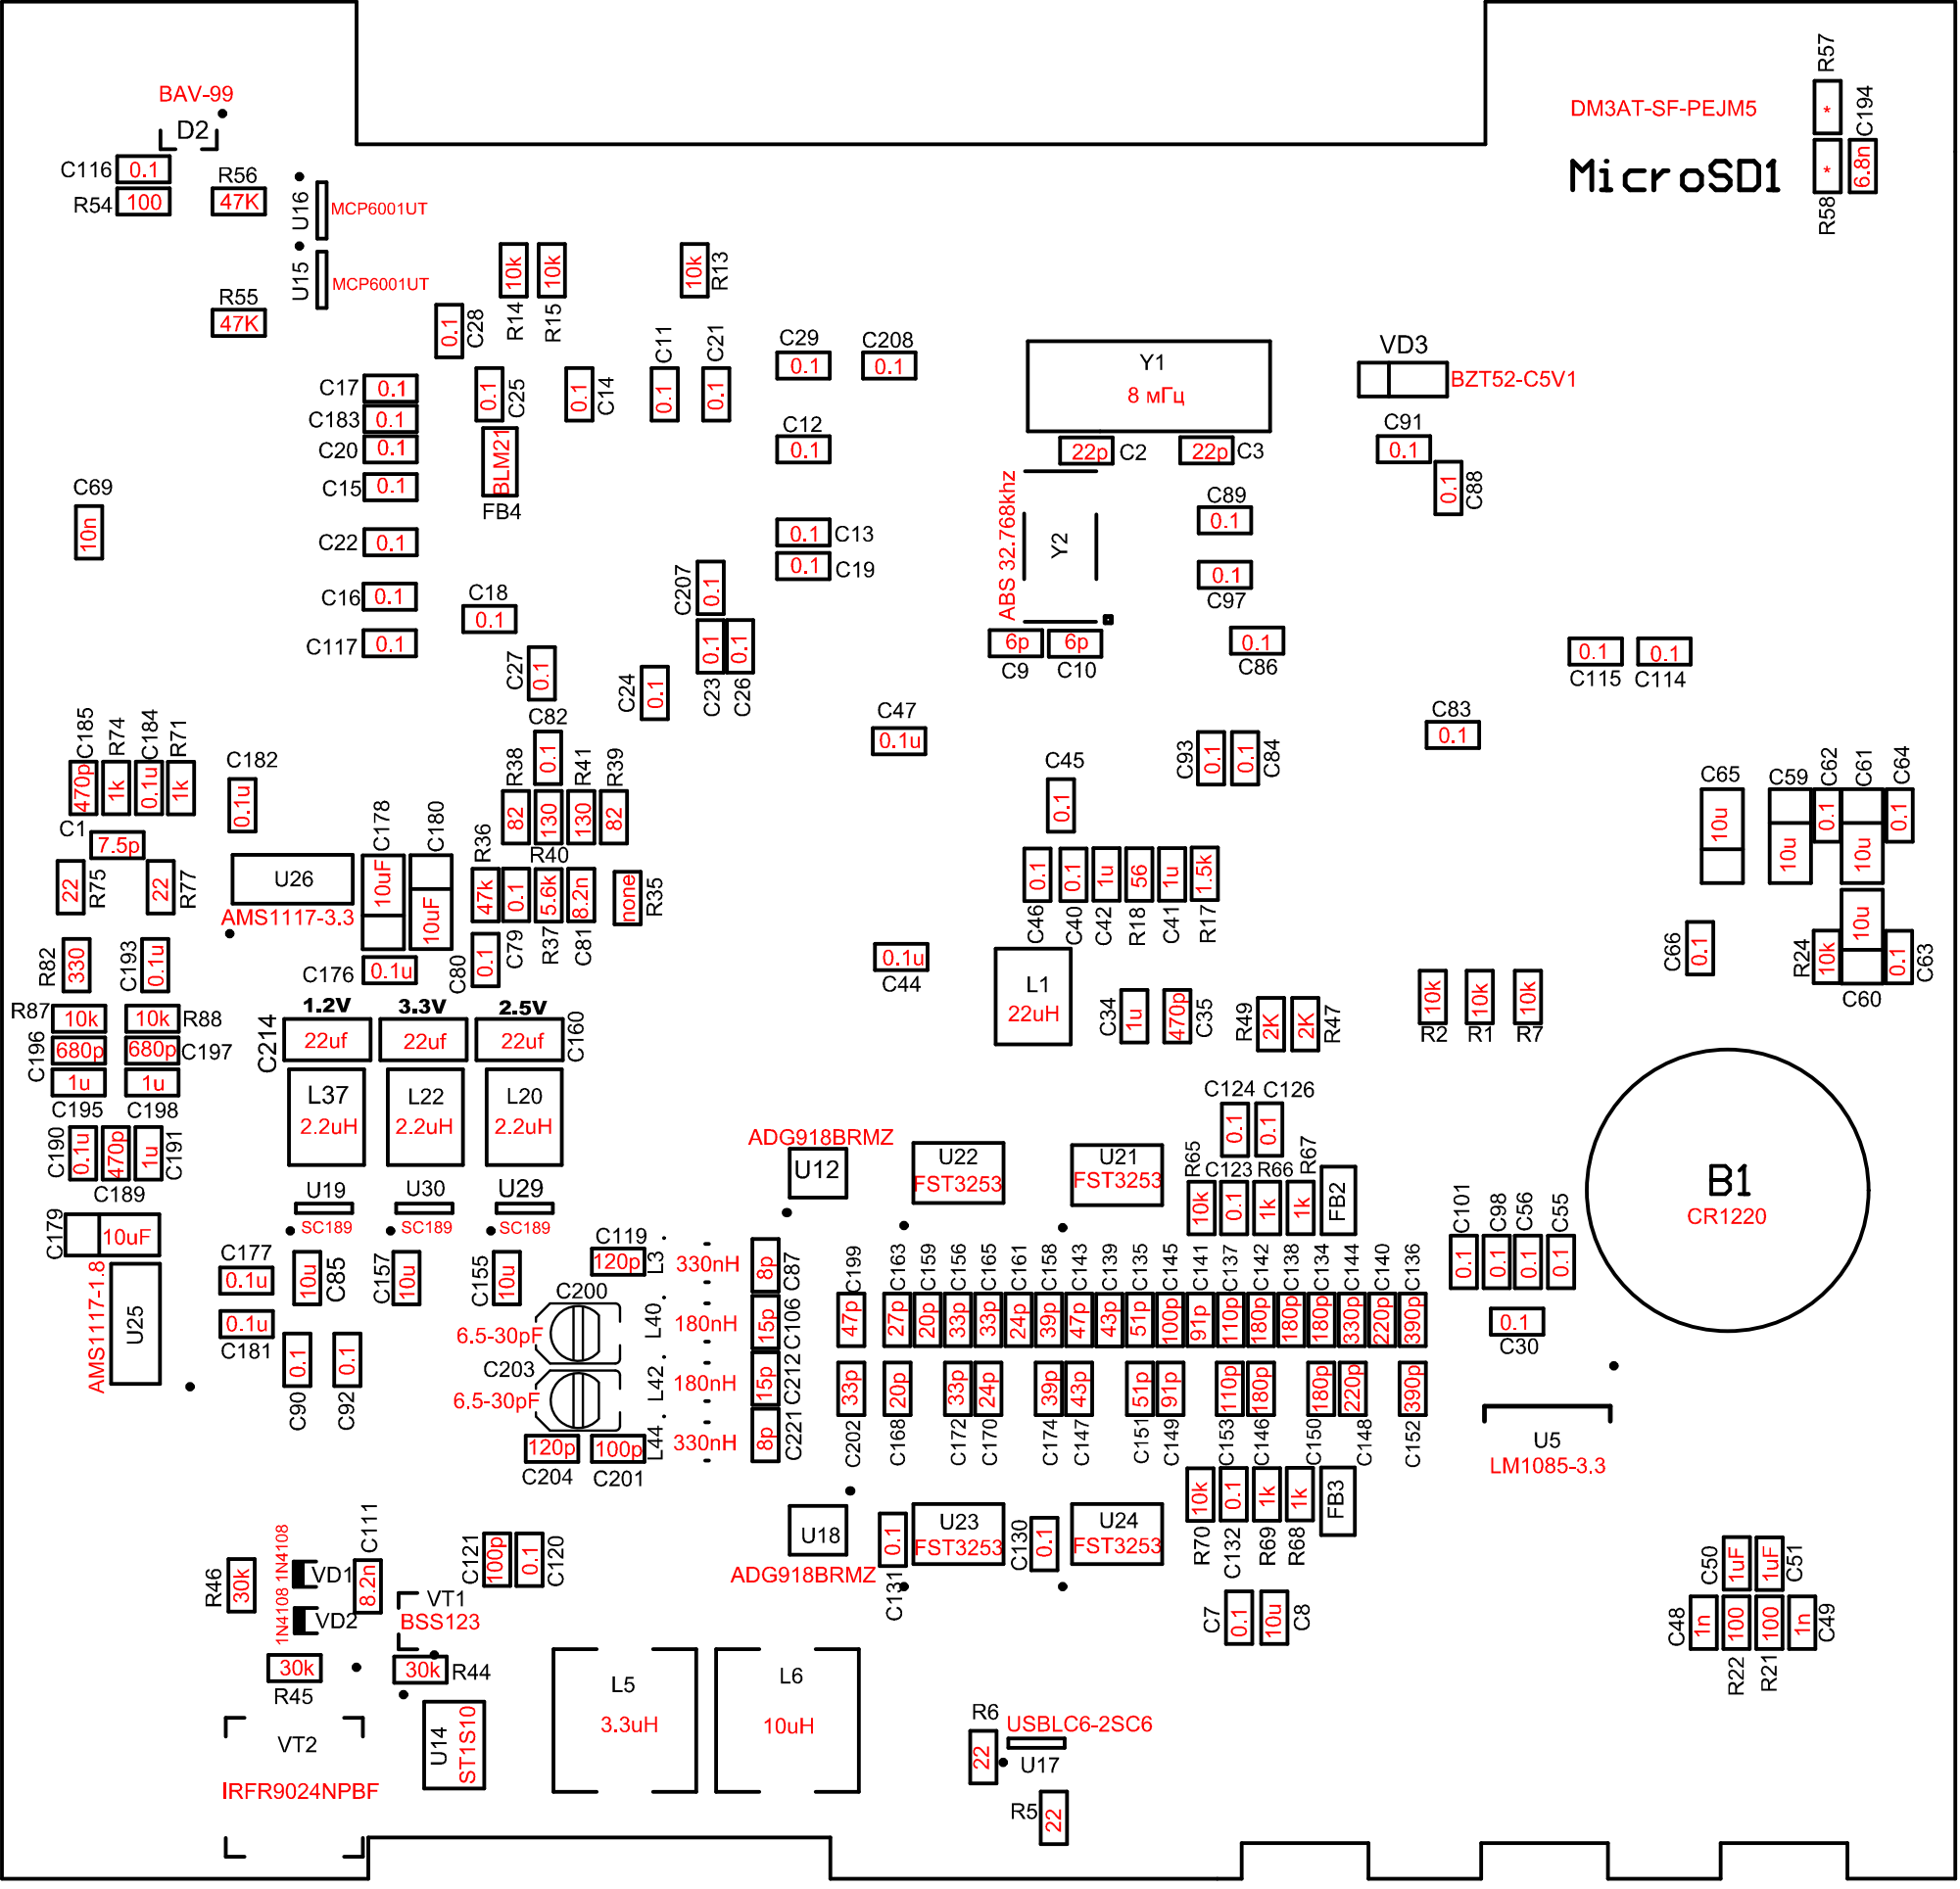
[picture p440: page 2]
