XGudron/UA3REO-DDC-Transceiver/Schematic/Wolf-X1/Assembly/X1_PA_V0.3.PDF

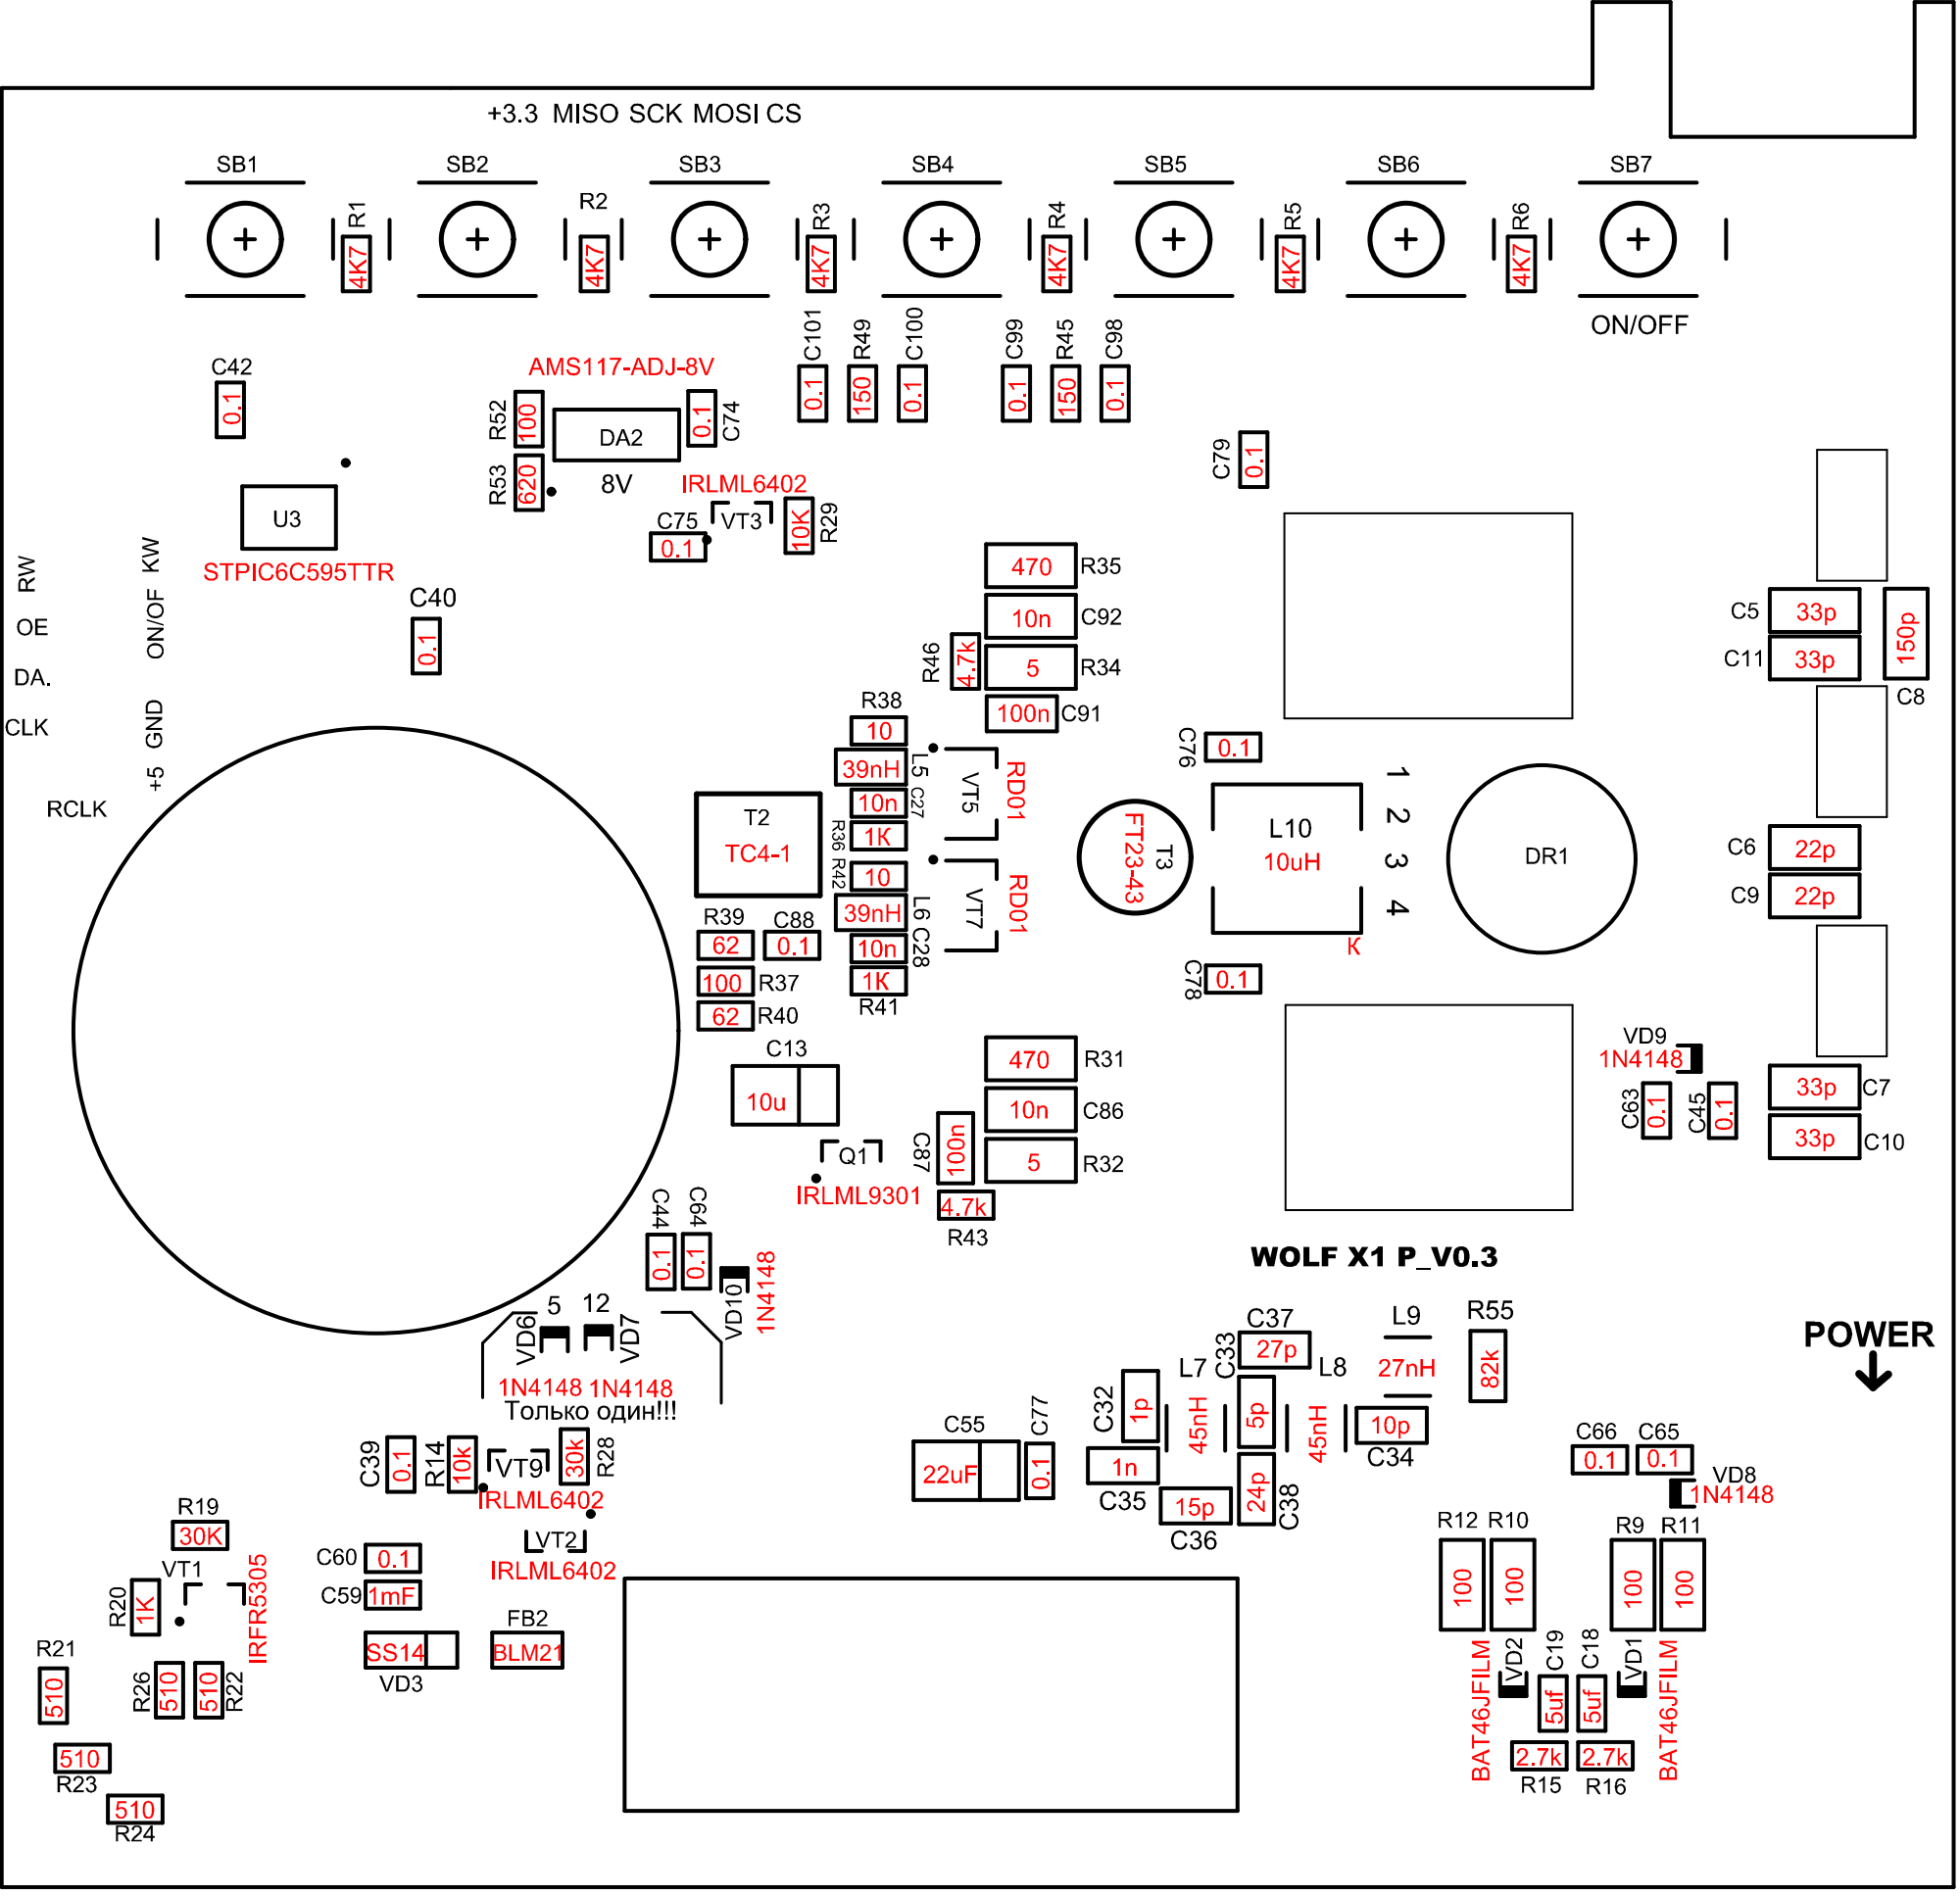
[picture p441: page 1]

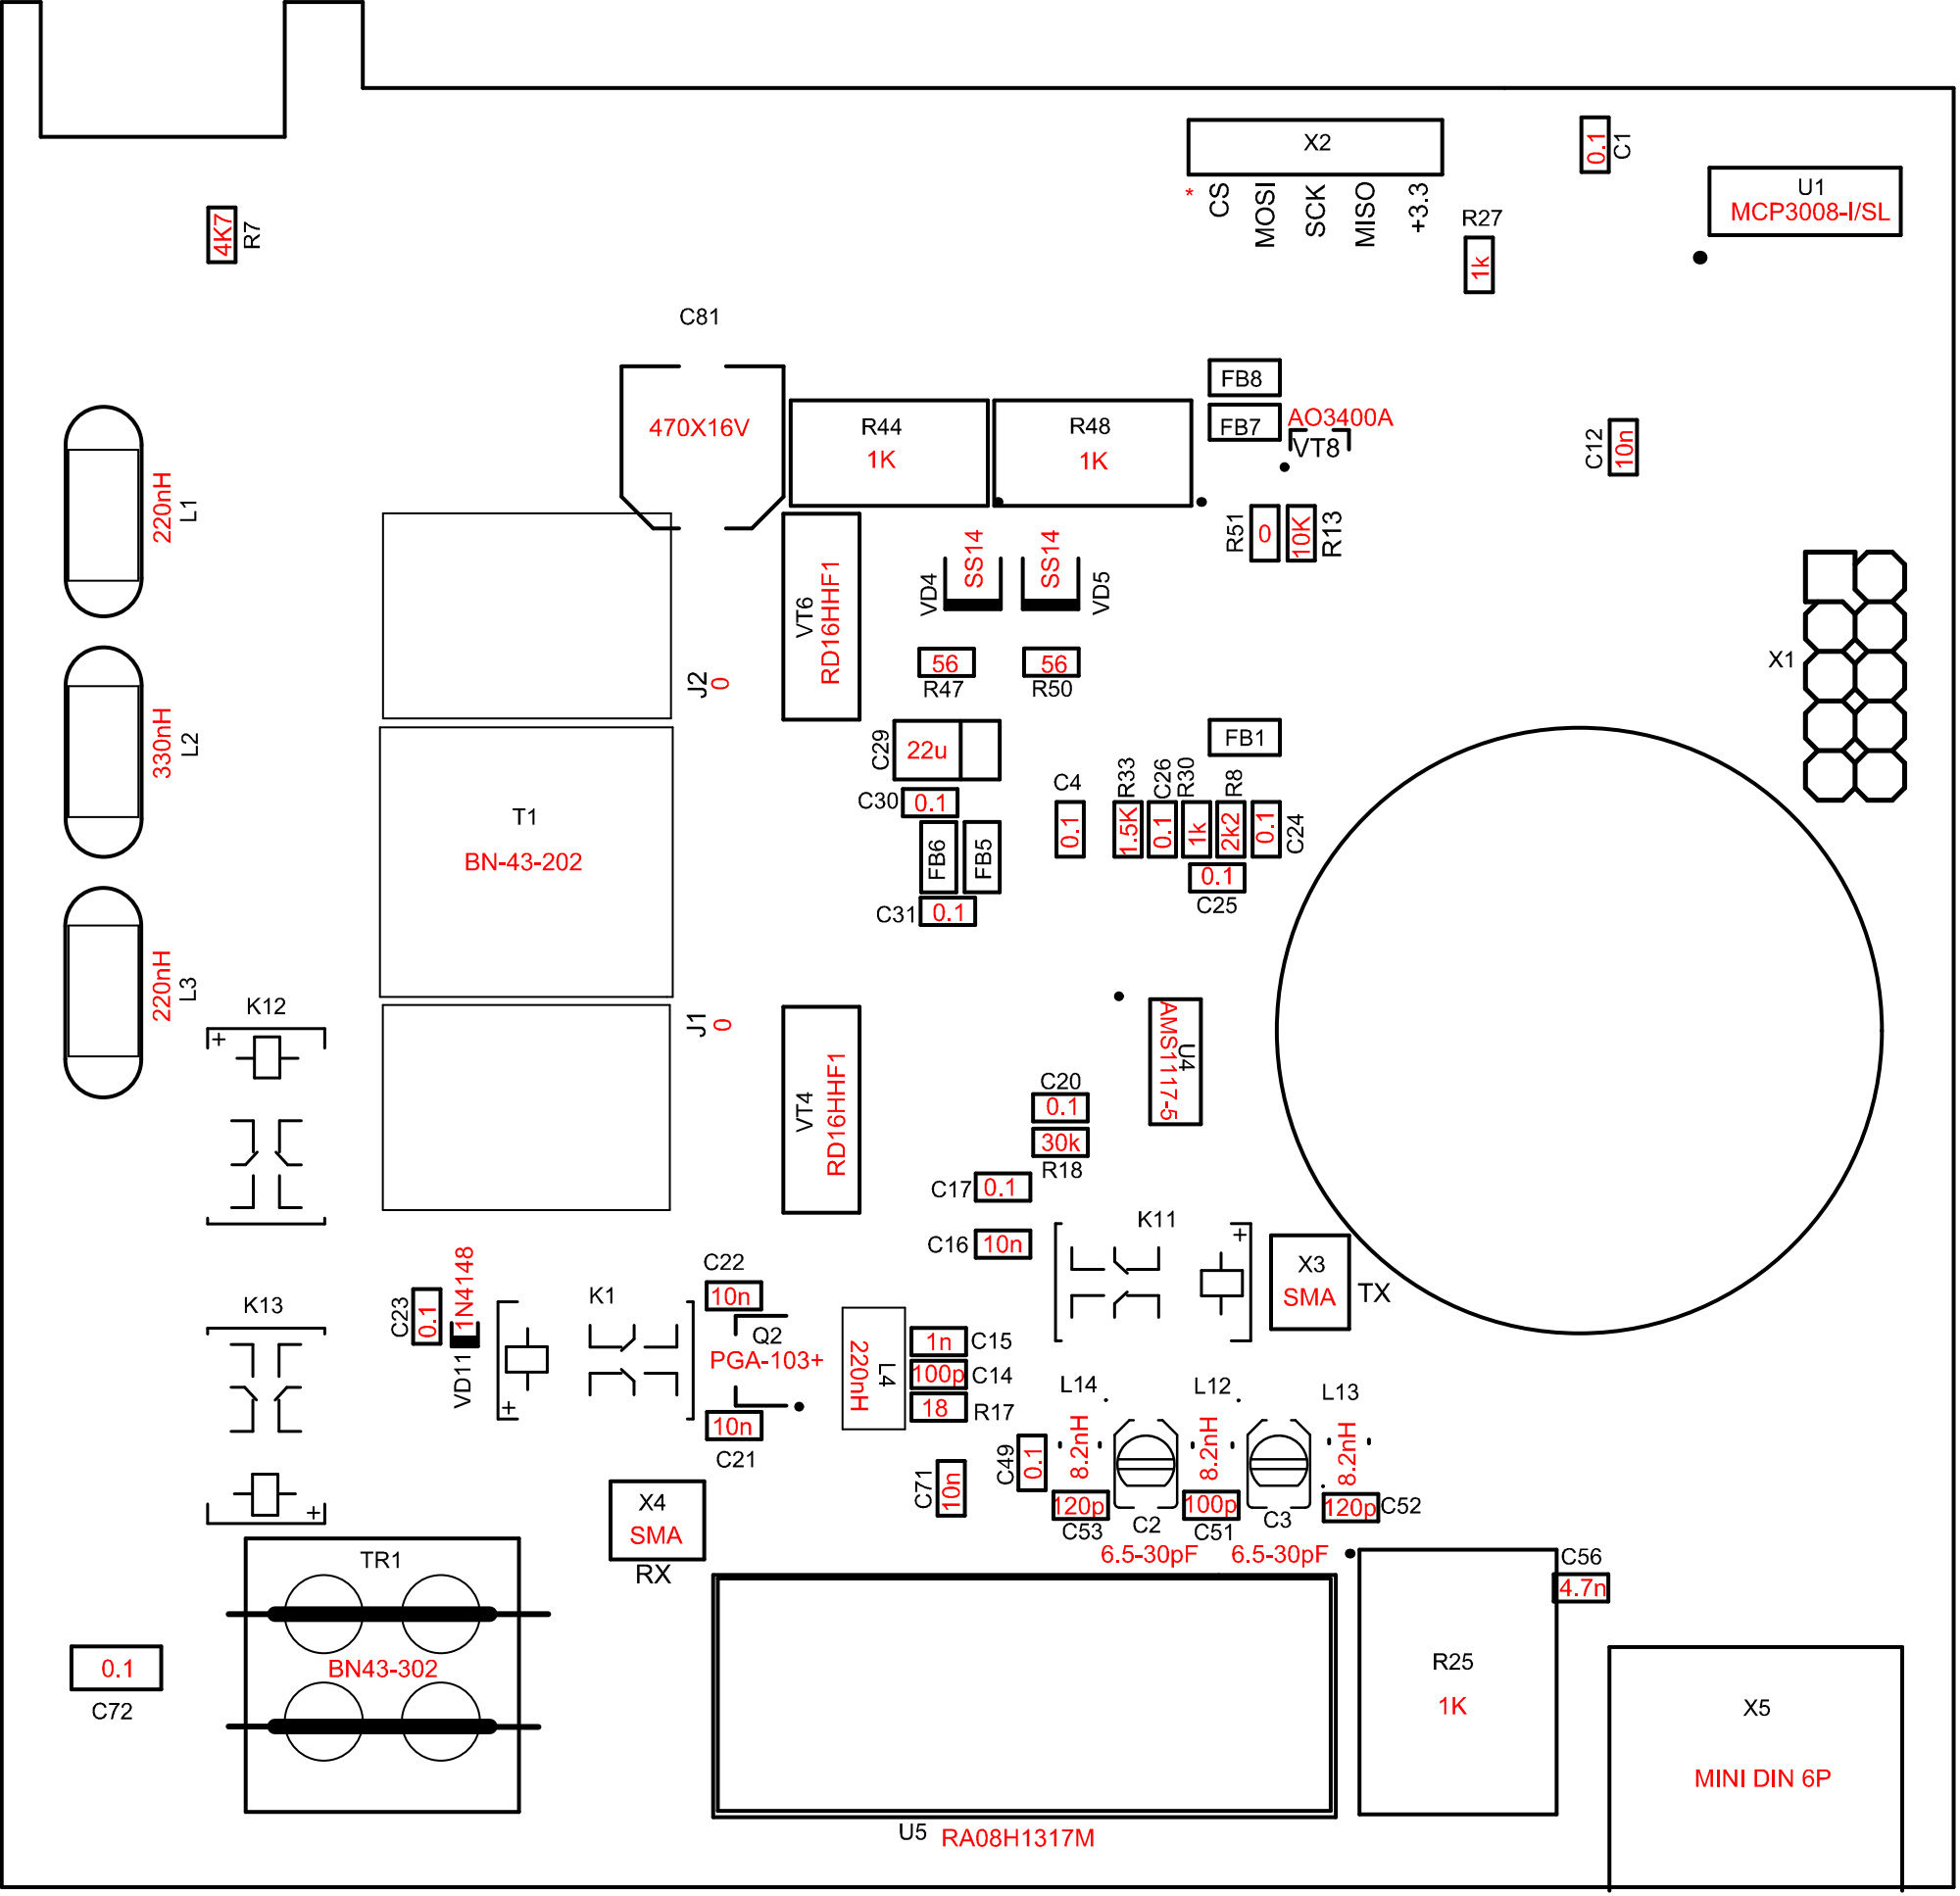
[picture p442: page 2]
