XGudron/UA3REO-DDC-Transceiver/Schematic/Wolf-X1/Scheme/X1_MAIN_V1.3.pdf

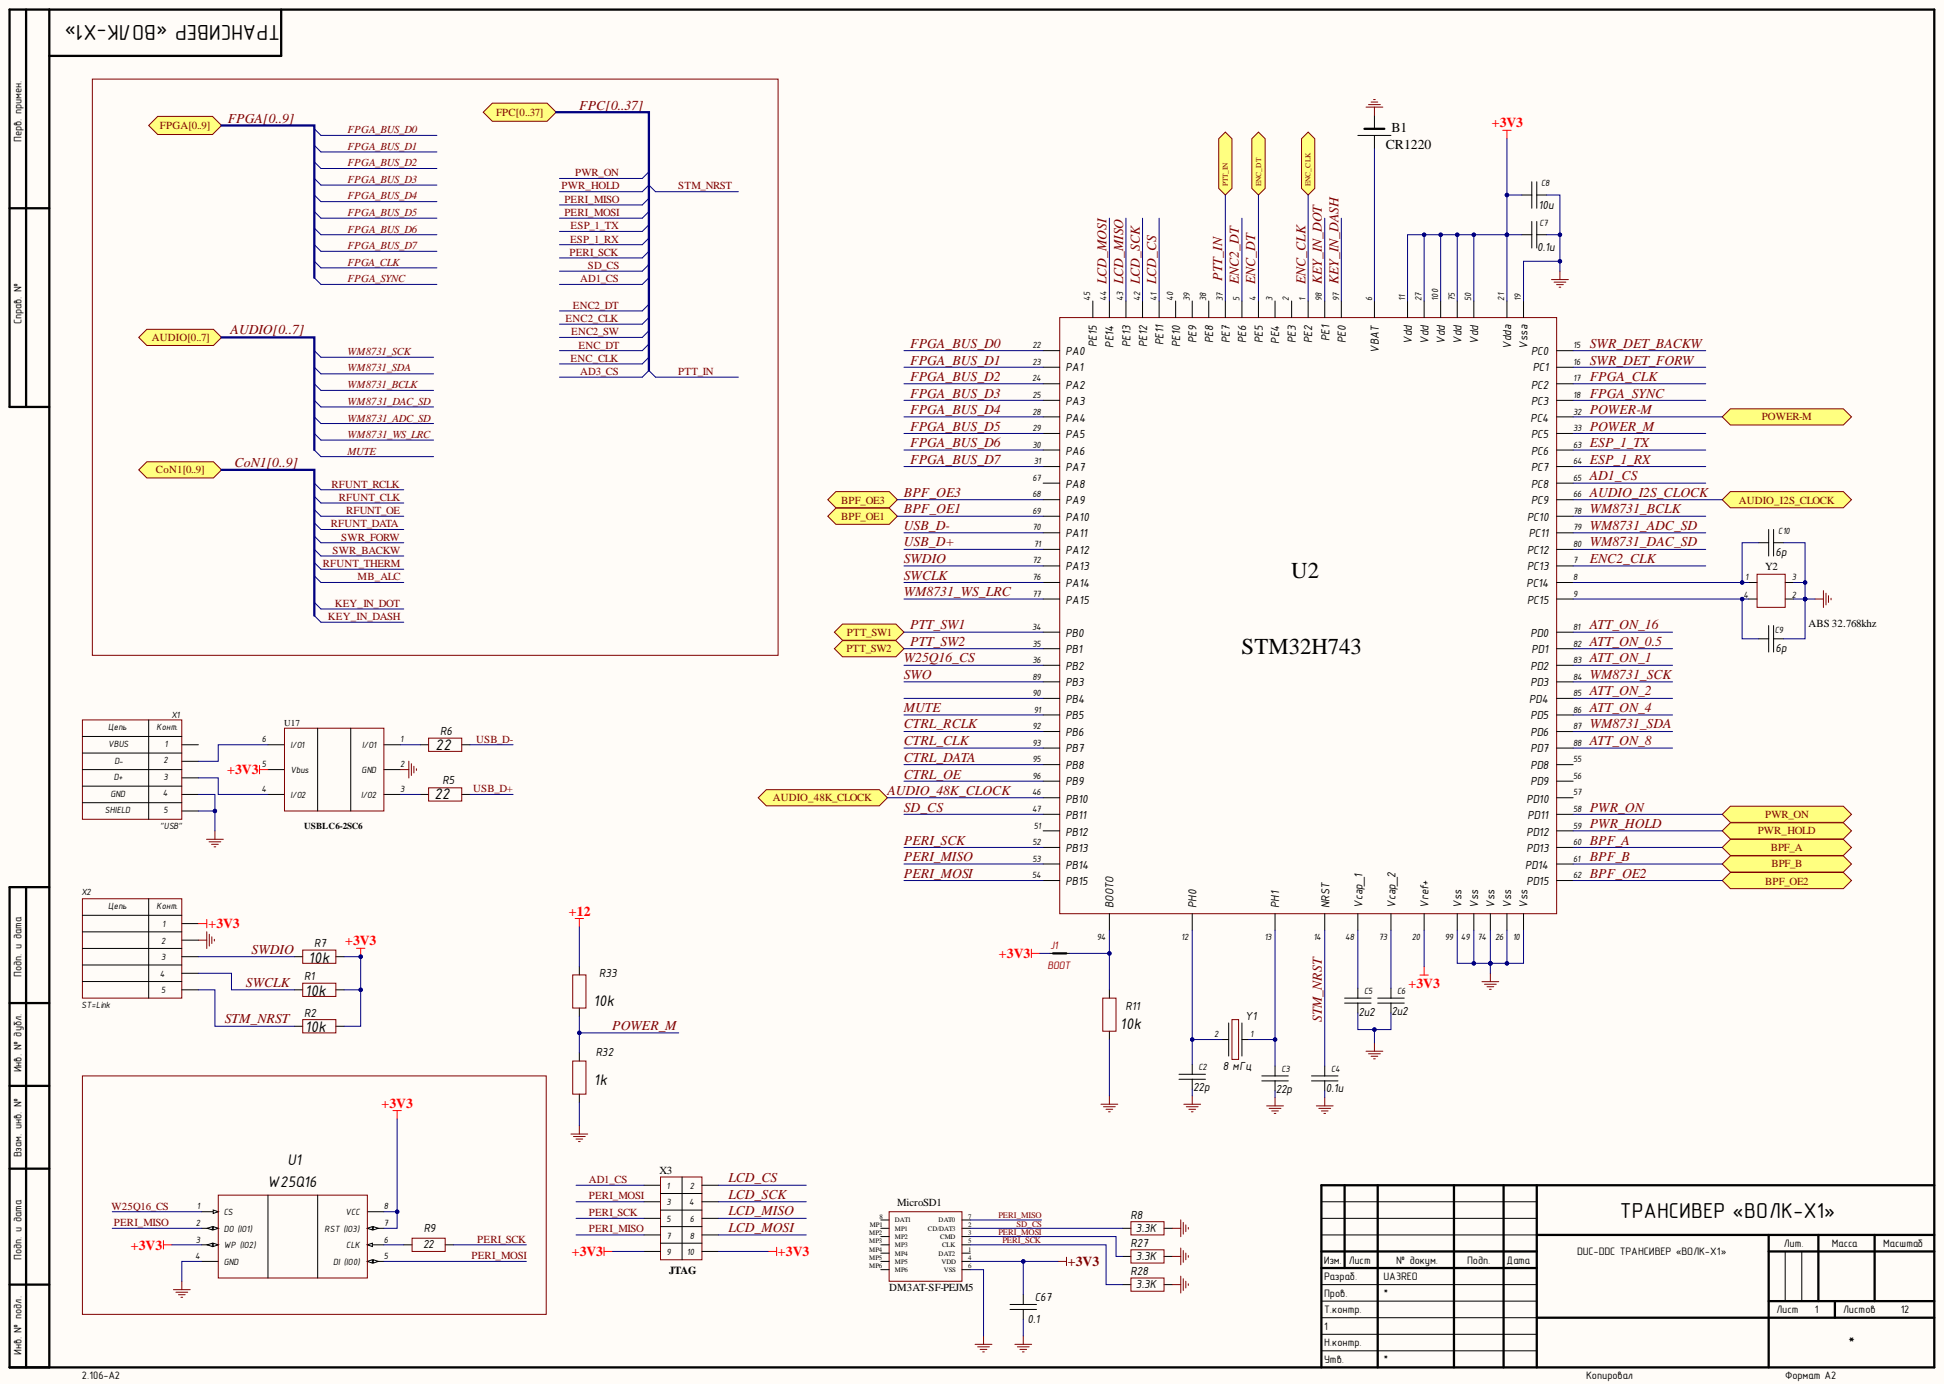
[picture p443: page 1]

Инв. № подл. Инв. № дубл. Подп. и дата Взам. инв. № Подп. и дата Перв. примен. Справ. №

5 | 10k

DUC-DDC ТРАНСИВЕР «ВОЛК-X1»

Пров. | *
Т.контр. | | Лист | Листов 12

Н.контр.
Утв. | *

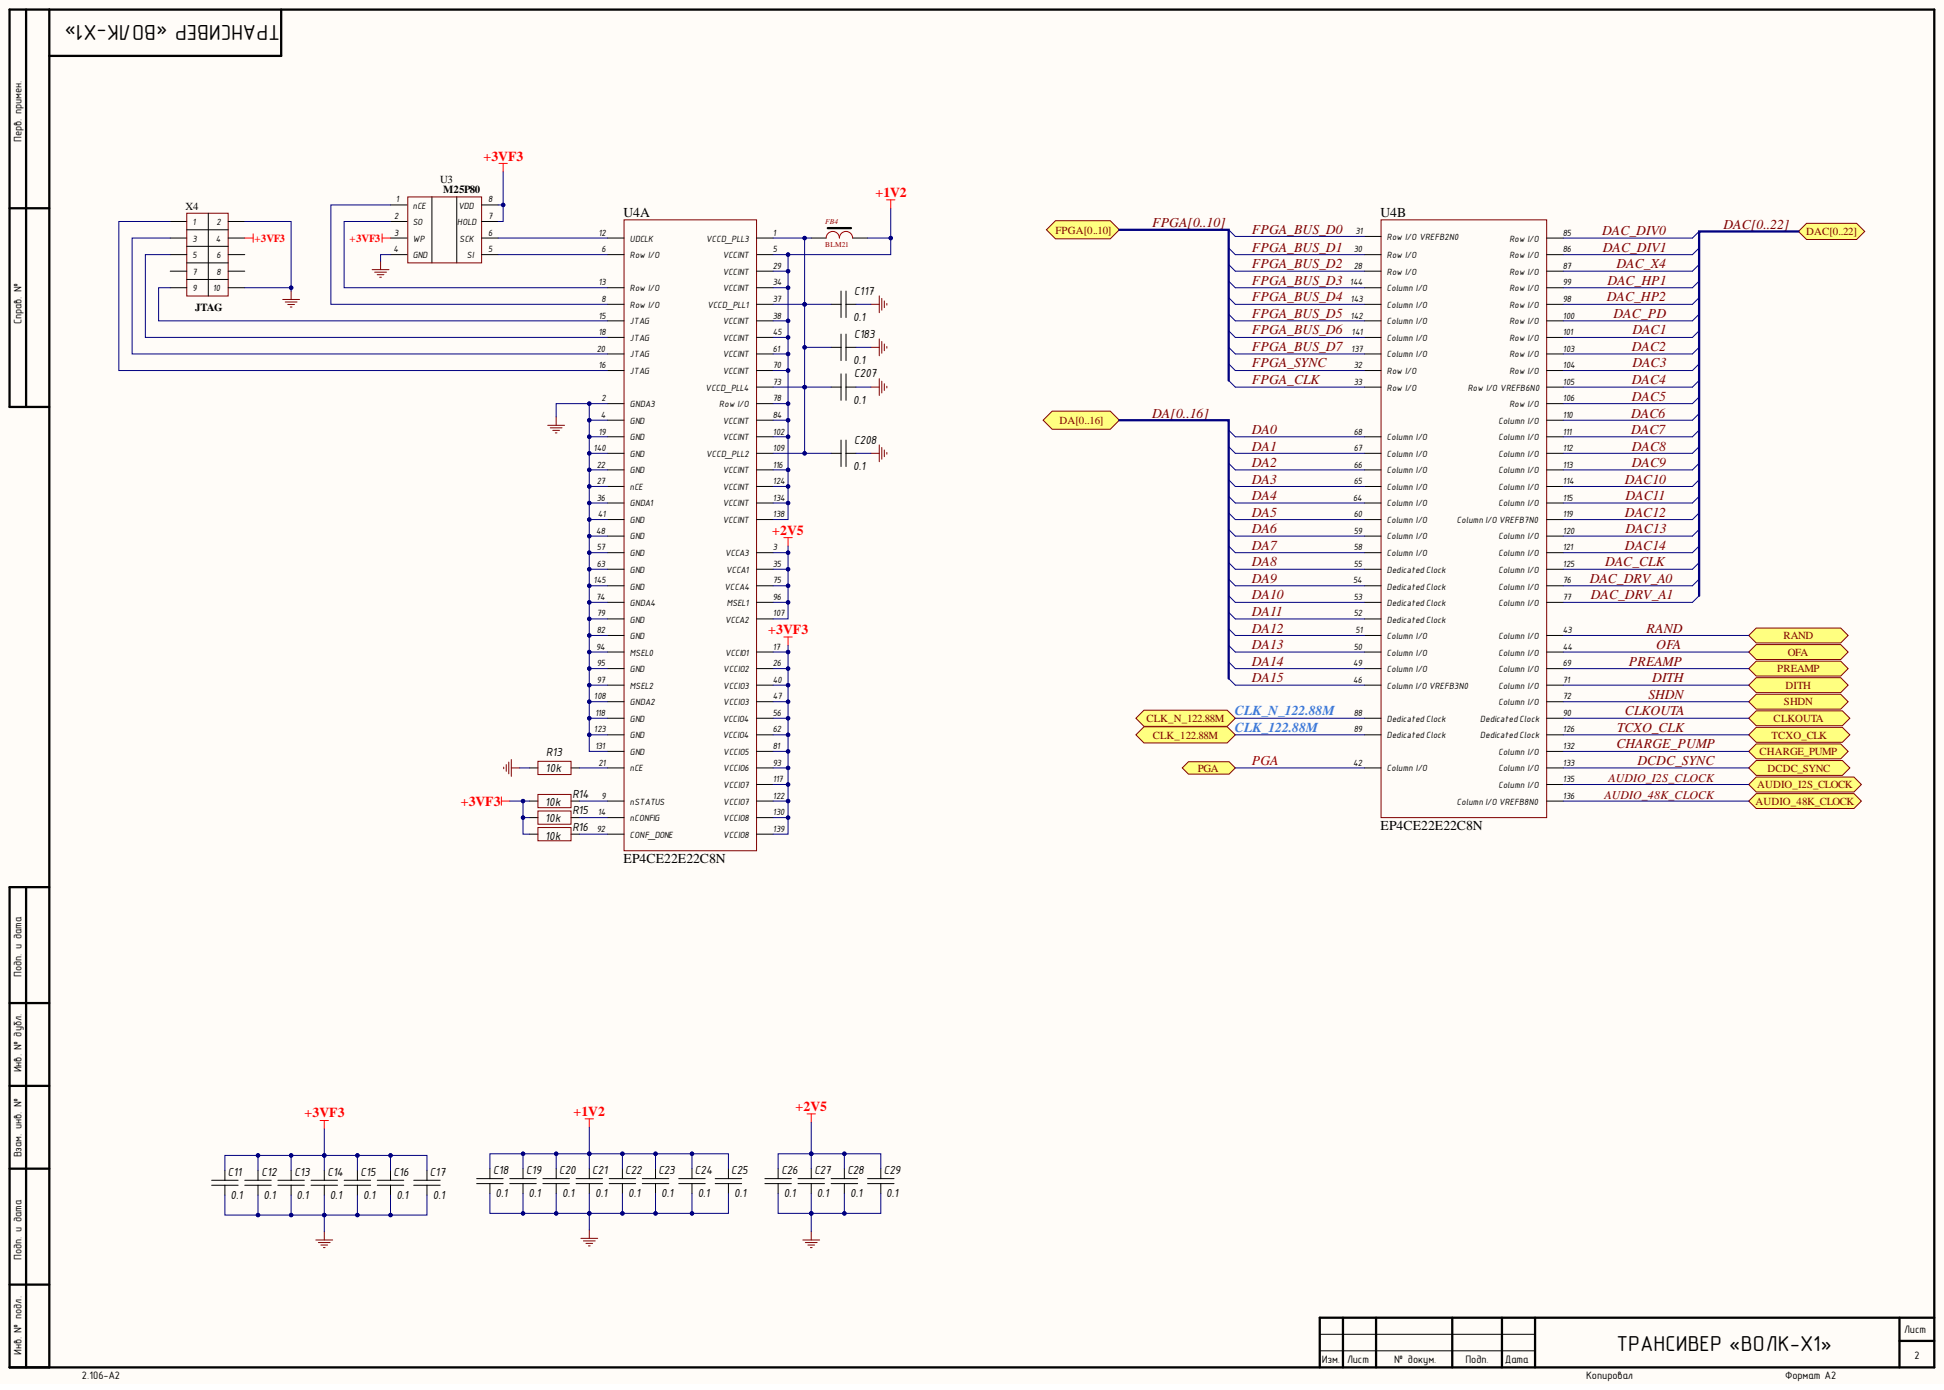
[picture p444: page 2]

Инв. № подл. Инв. № дубл. Подп. и дата Взам. инв. № Подп. и дата Перв. примен. Справ. №

nCE 1

+3VF3 | +3VF3 | WP 3 | SCK | 6

GNDA2 108

GND 123

Лист | № докум. | Подп. | Дата | ТРАНСИВЕР «ВОЛК-X1» Изм.

Лист

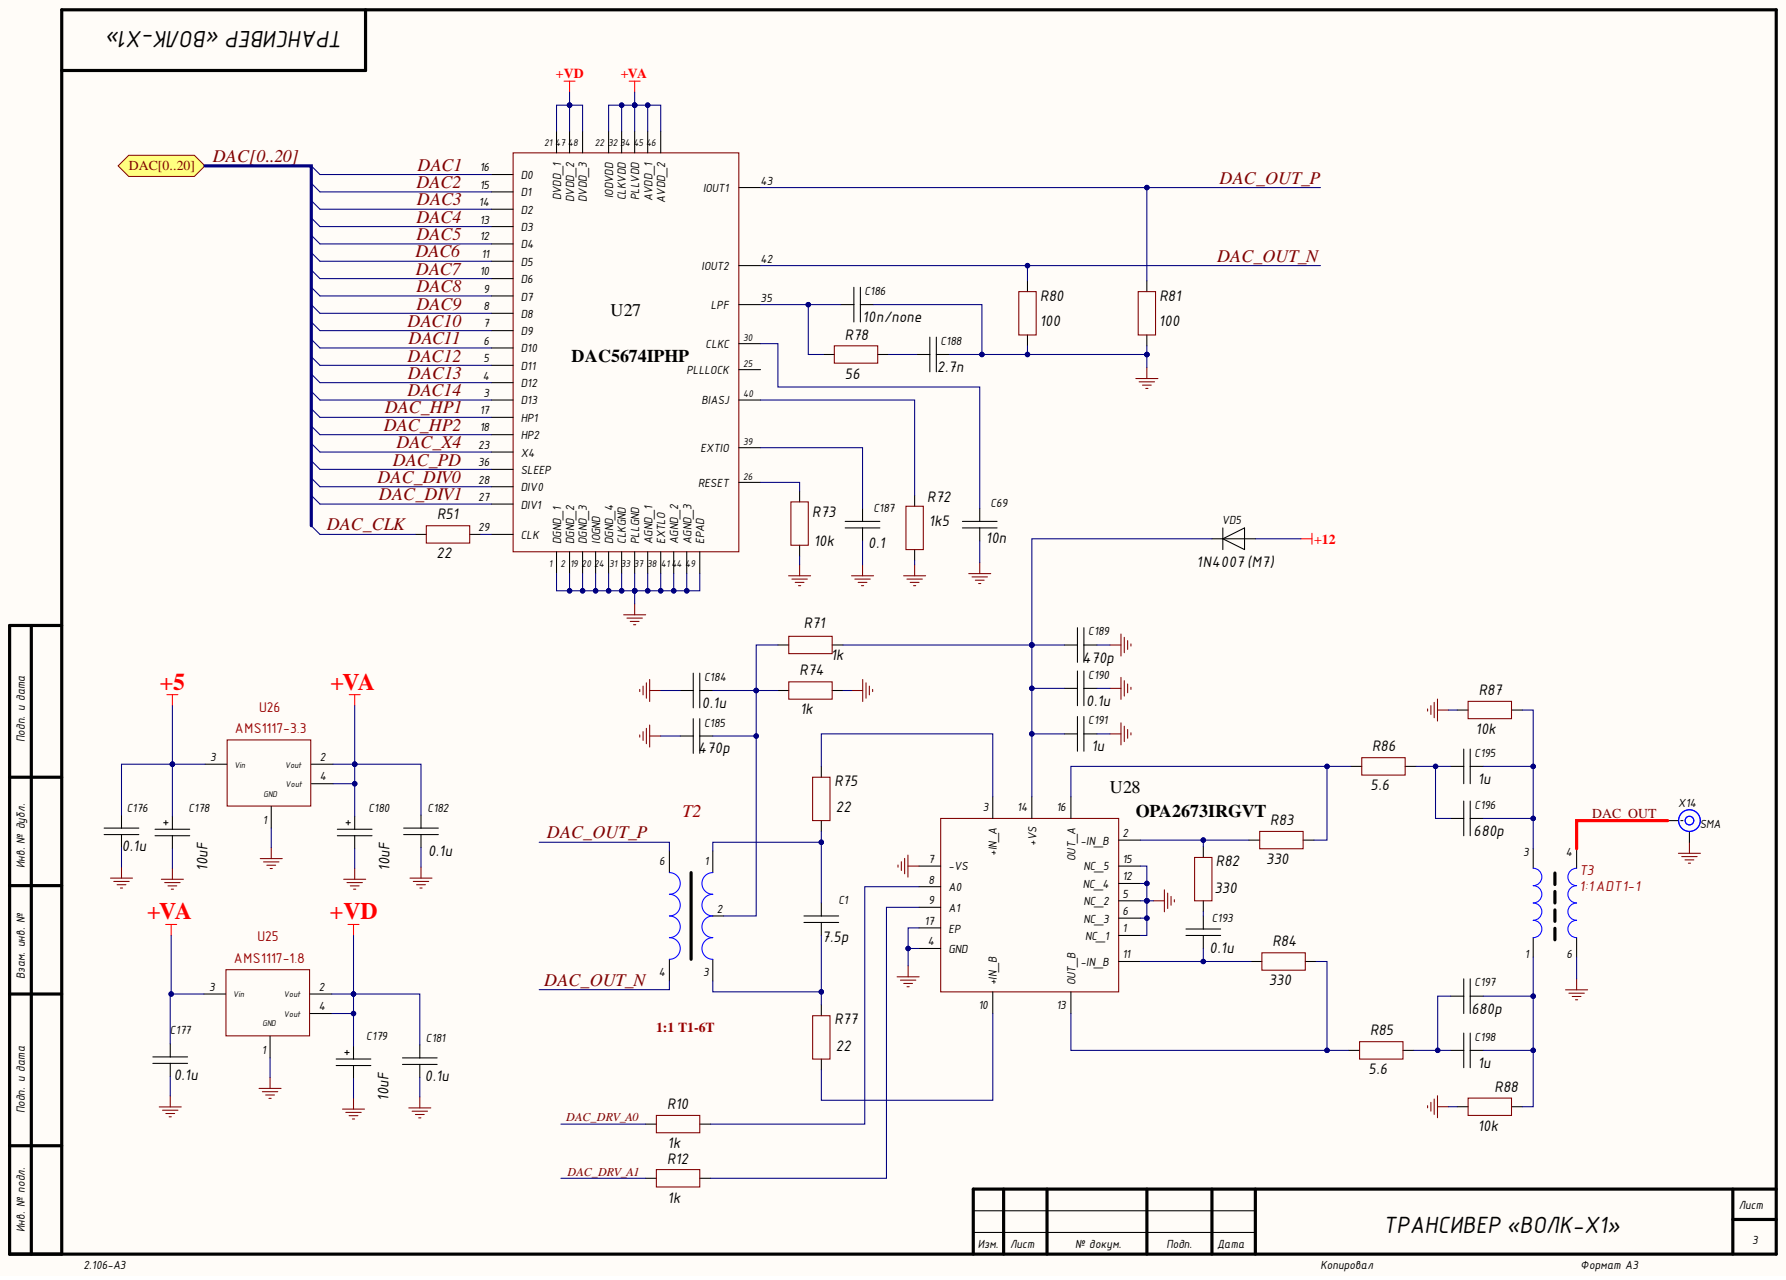
[picture p445: page 3]

Инв. № подл. Инв. № дубл. Подп. и дата Взам. инв. № Подп. и дата

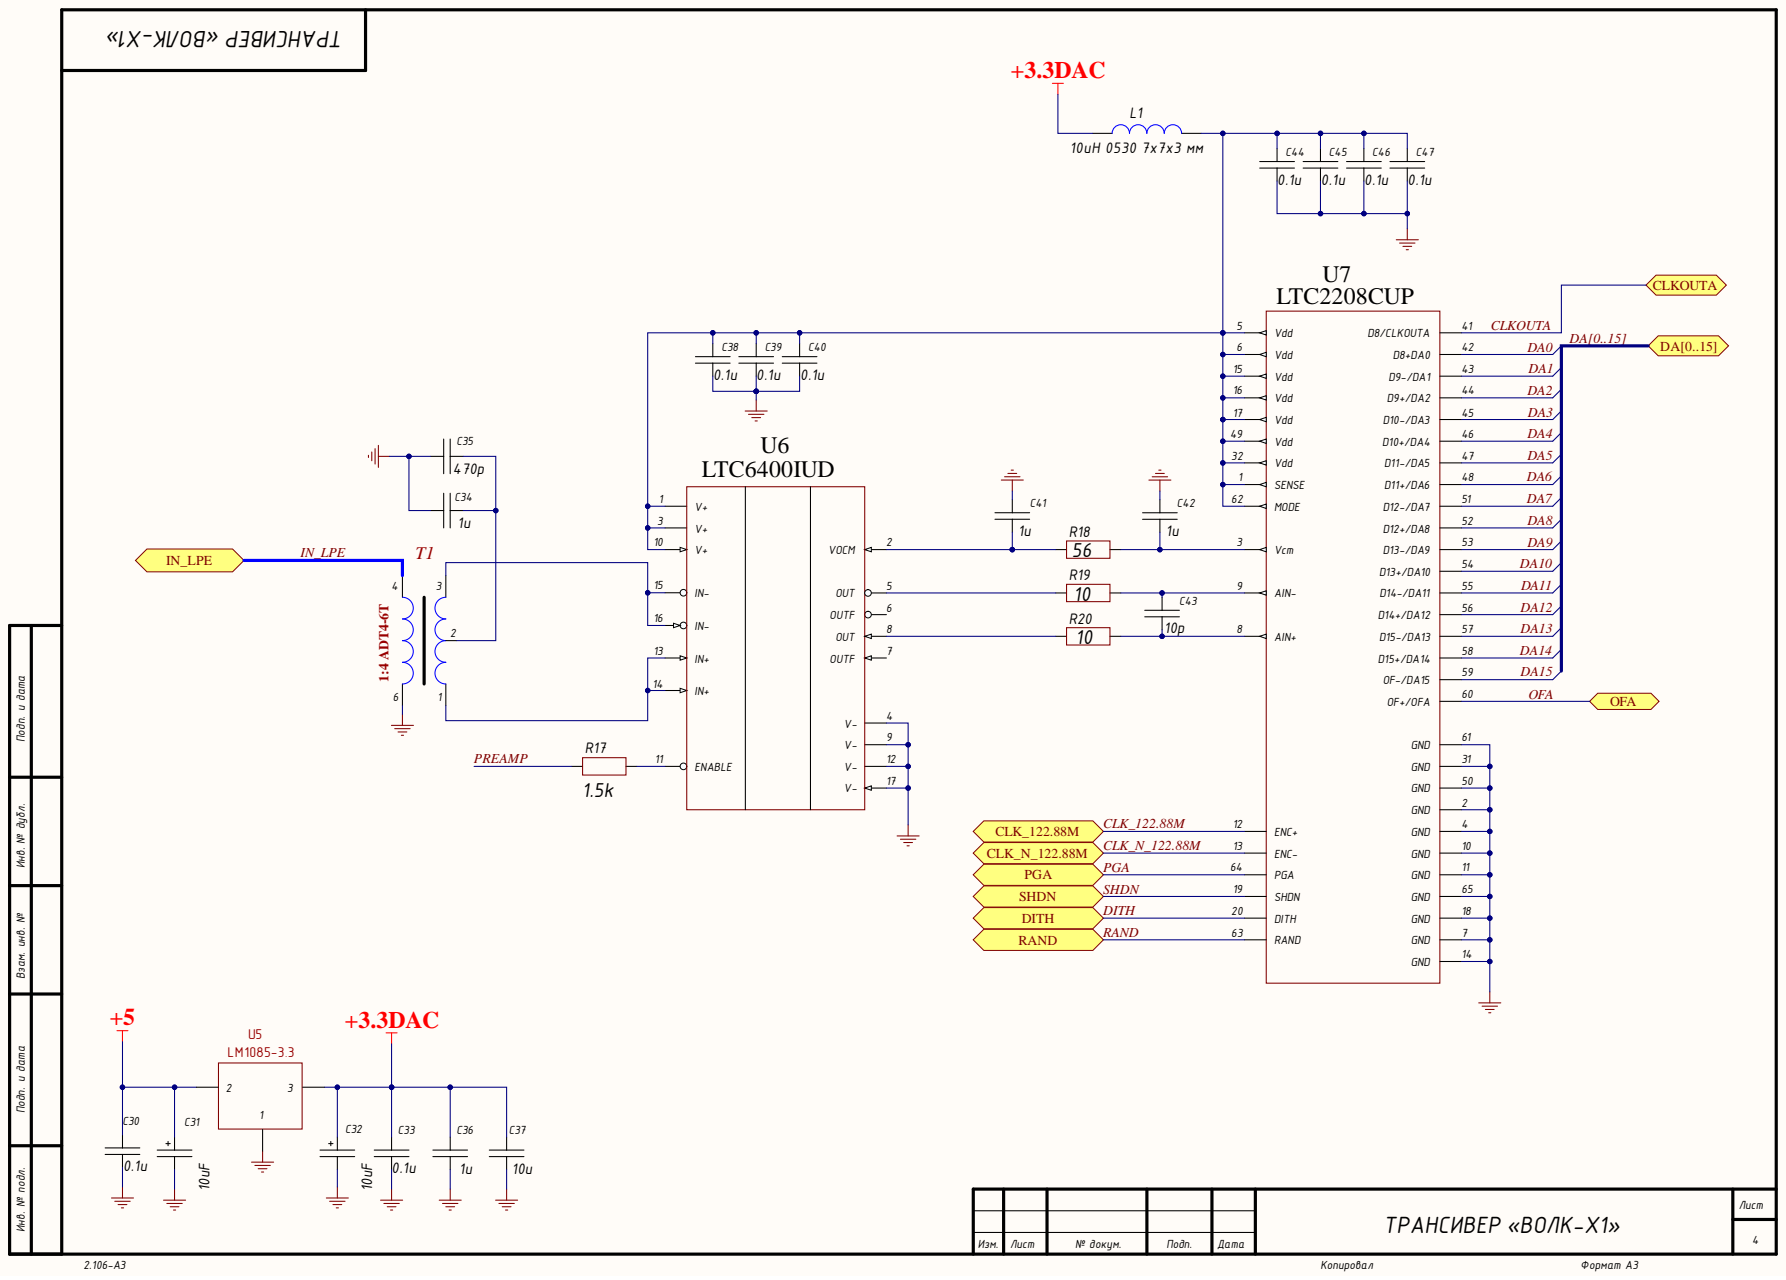
[picture p446: page 4]

Инв. № подл. Инв. № дубл. Подп. и дата Взам. инв. № Подп. и дата

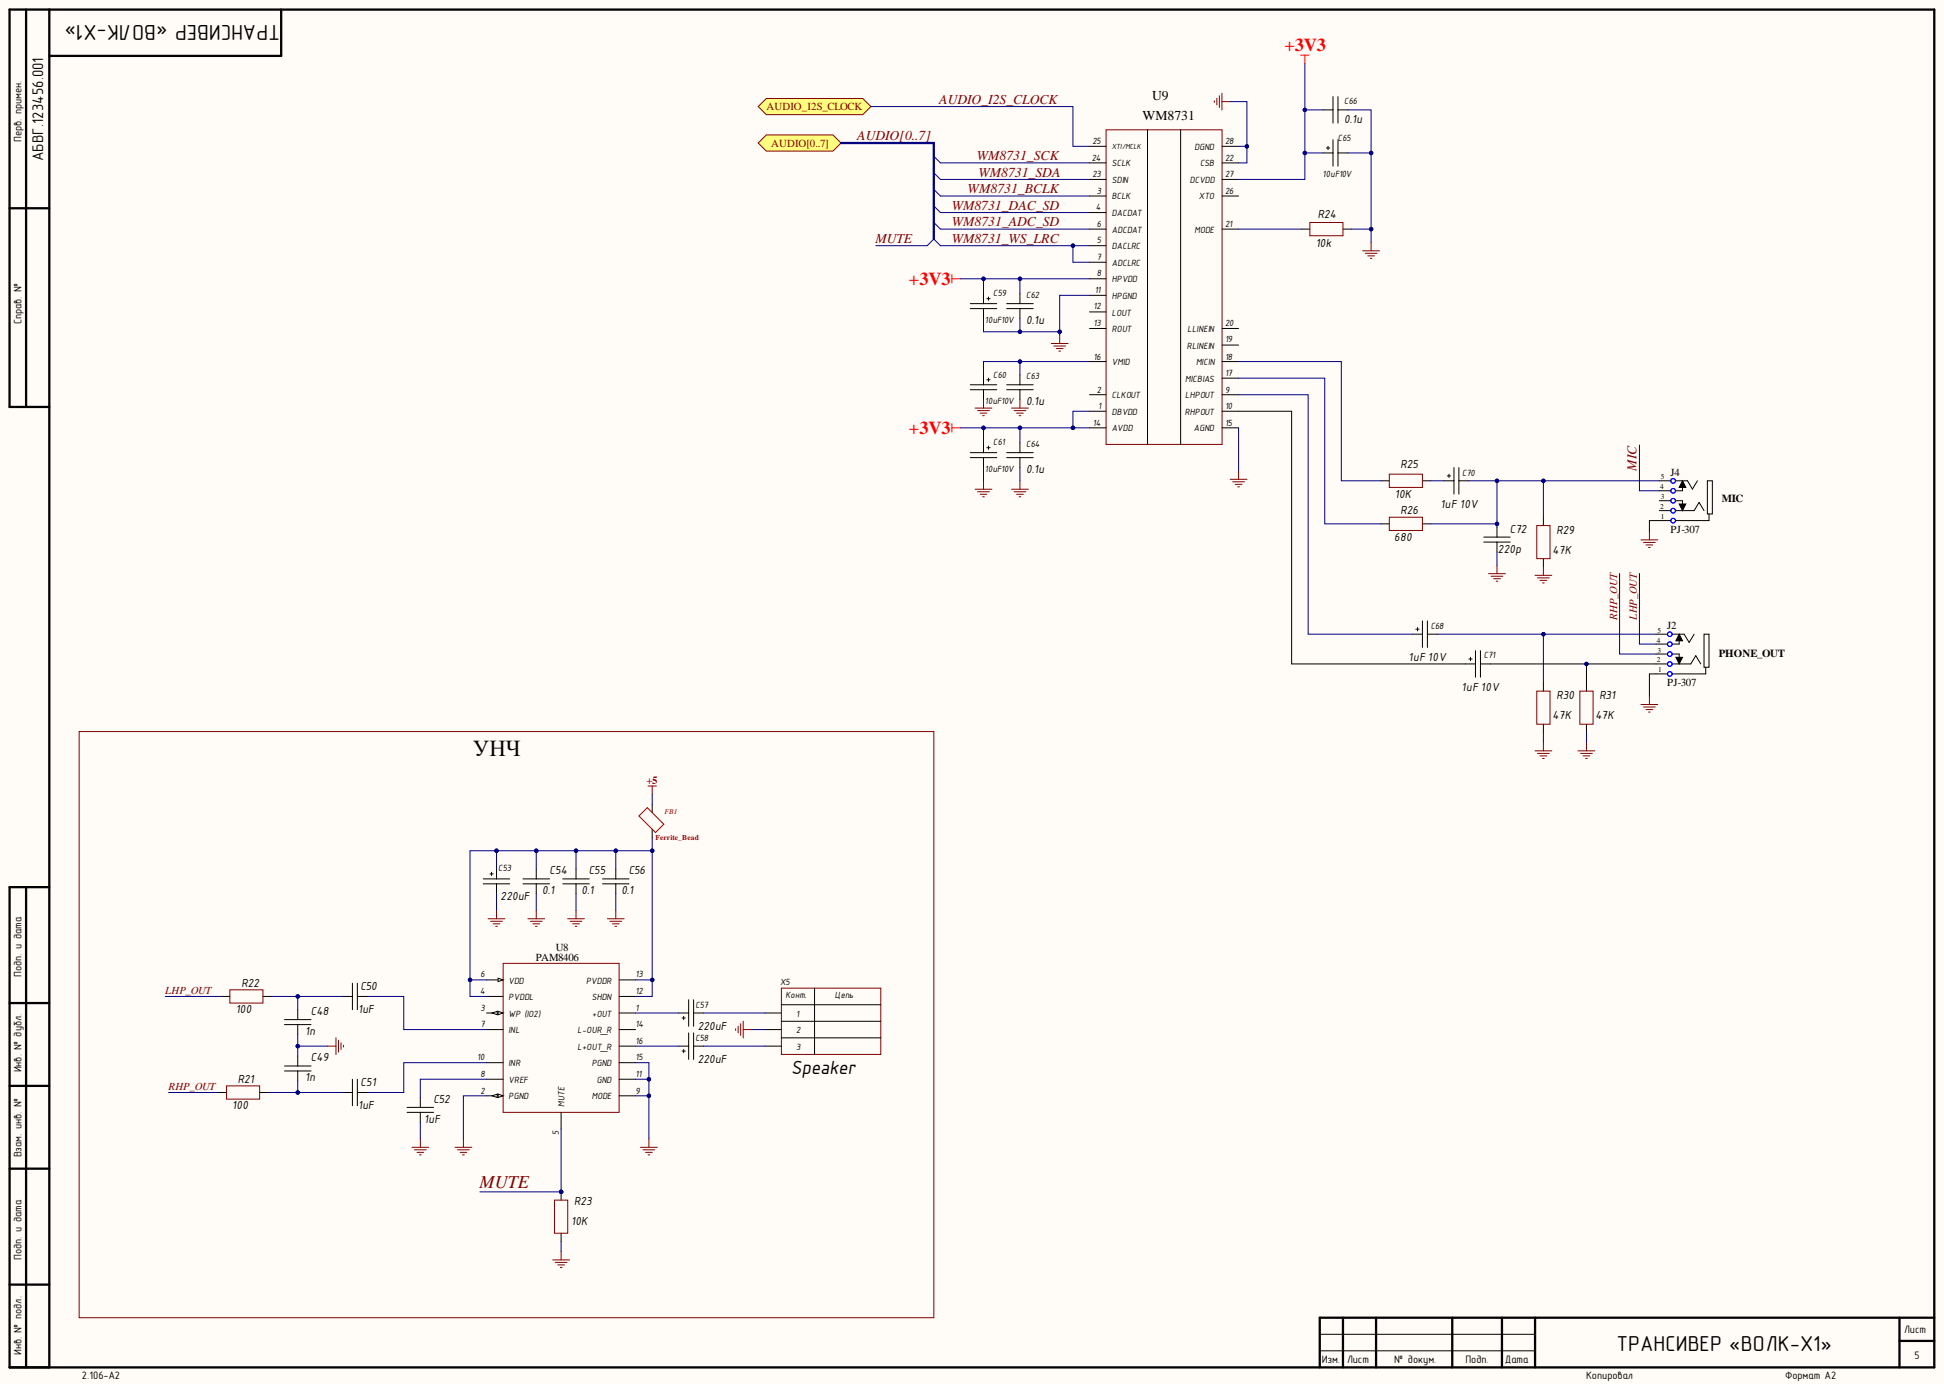
[picture p447: page 5]

Инв. № подл. Инв. № дубл. Подп. и дата Взам. инв. № Подп. и дата Перв. примен. Справ. №

LOUT 12

Конт. | Цепь

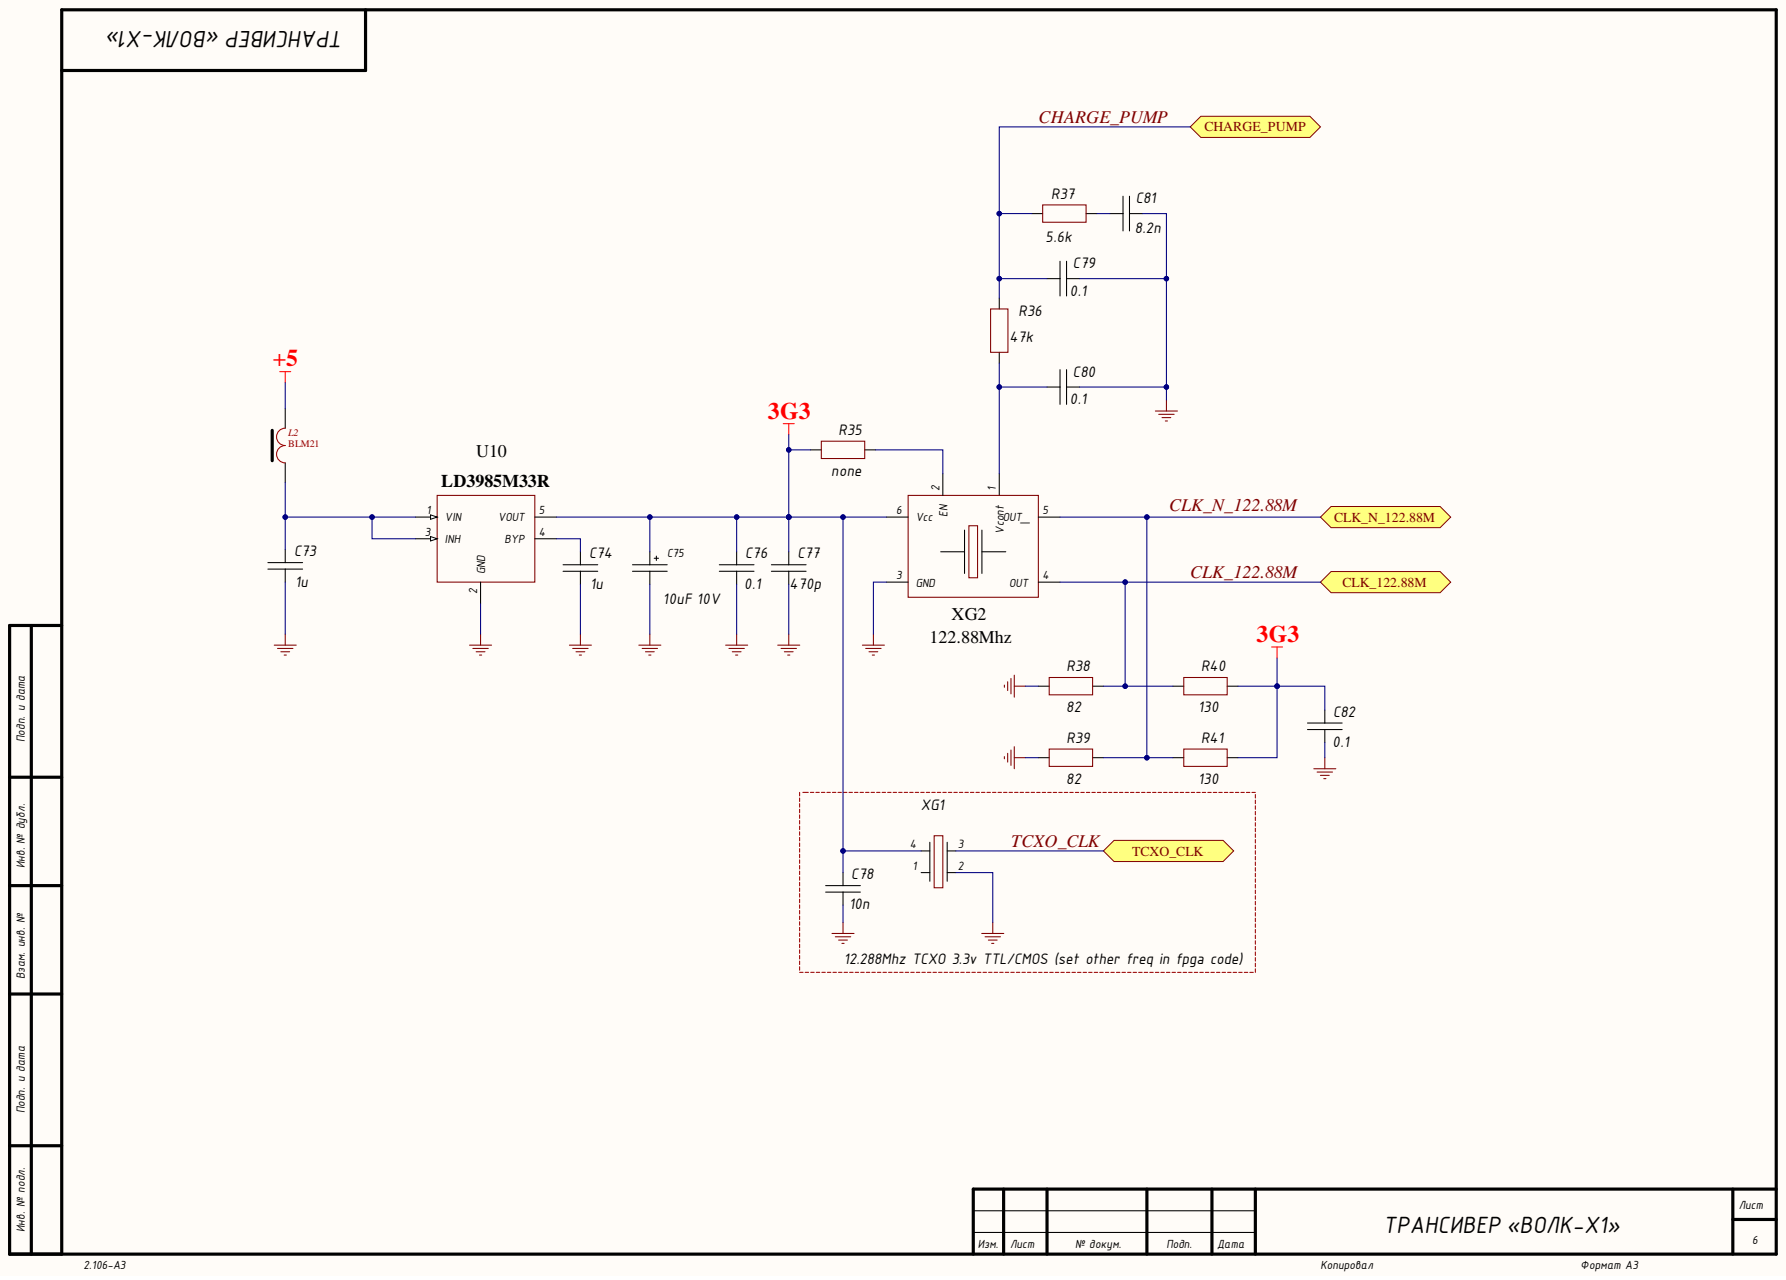
[picture p448: page 6]

Инв. № подл. Инв. № дубл. Подп. и дата Взам. инв. № Подп. и дата

12.288Mhz TCXO 3.3v TTL/CMOS (set other freq in fpga code)

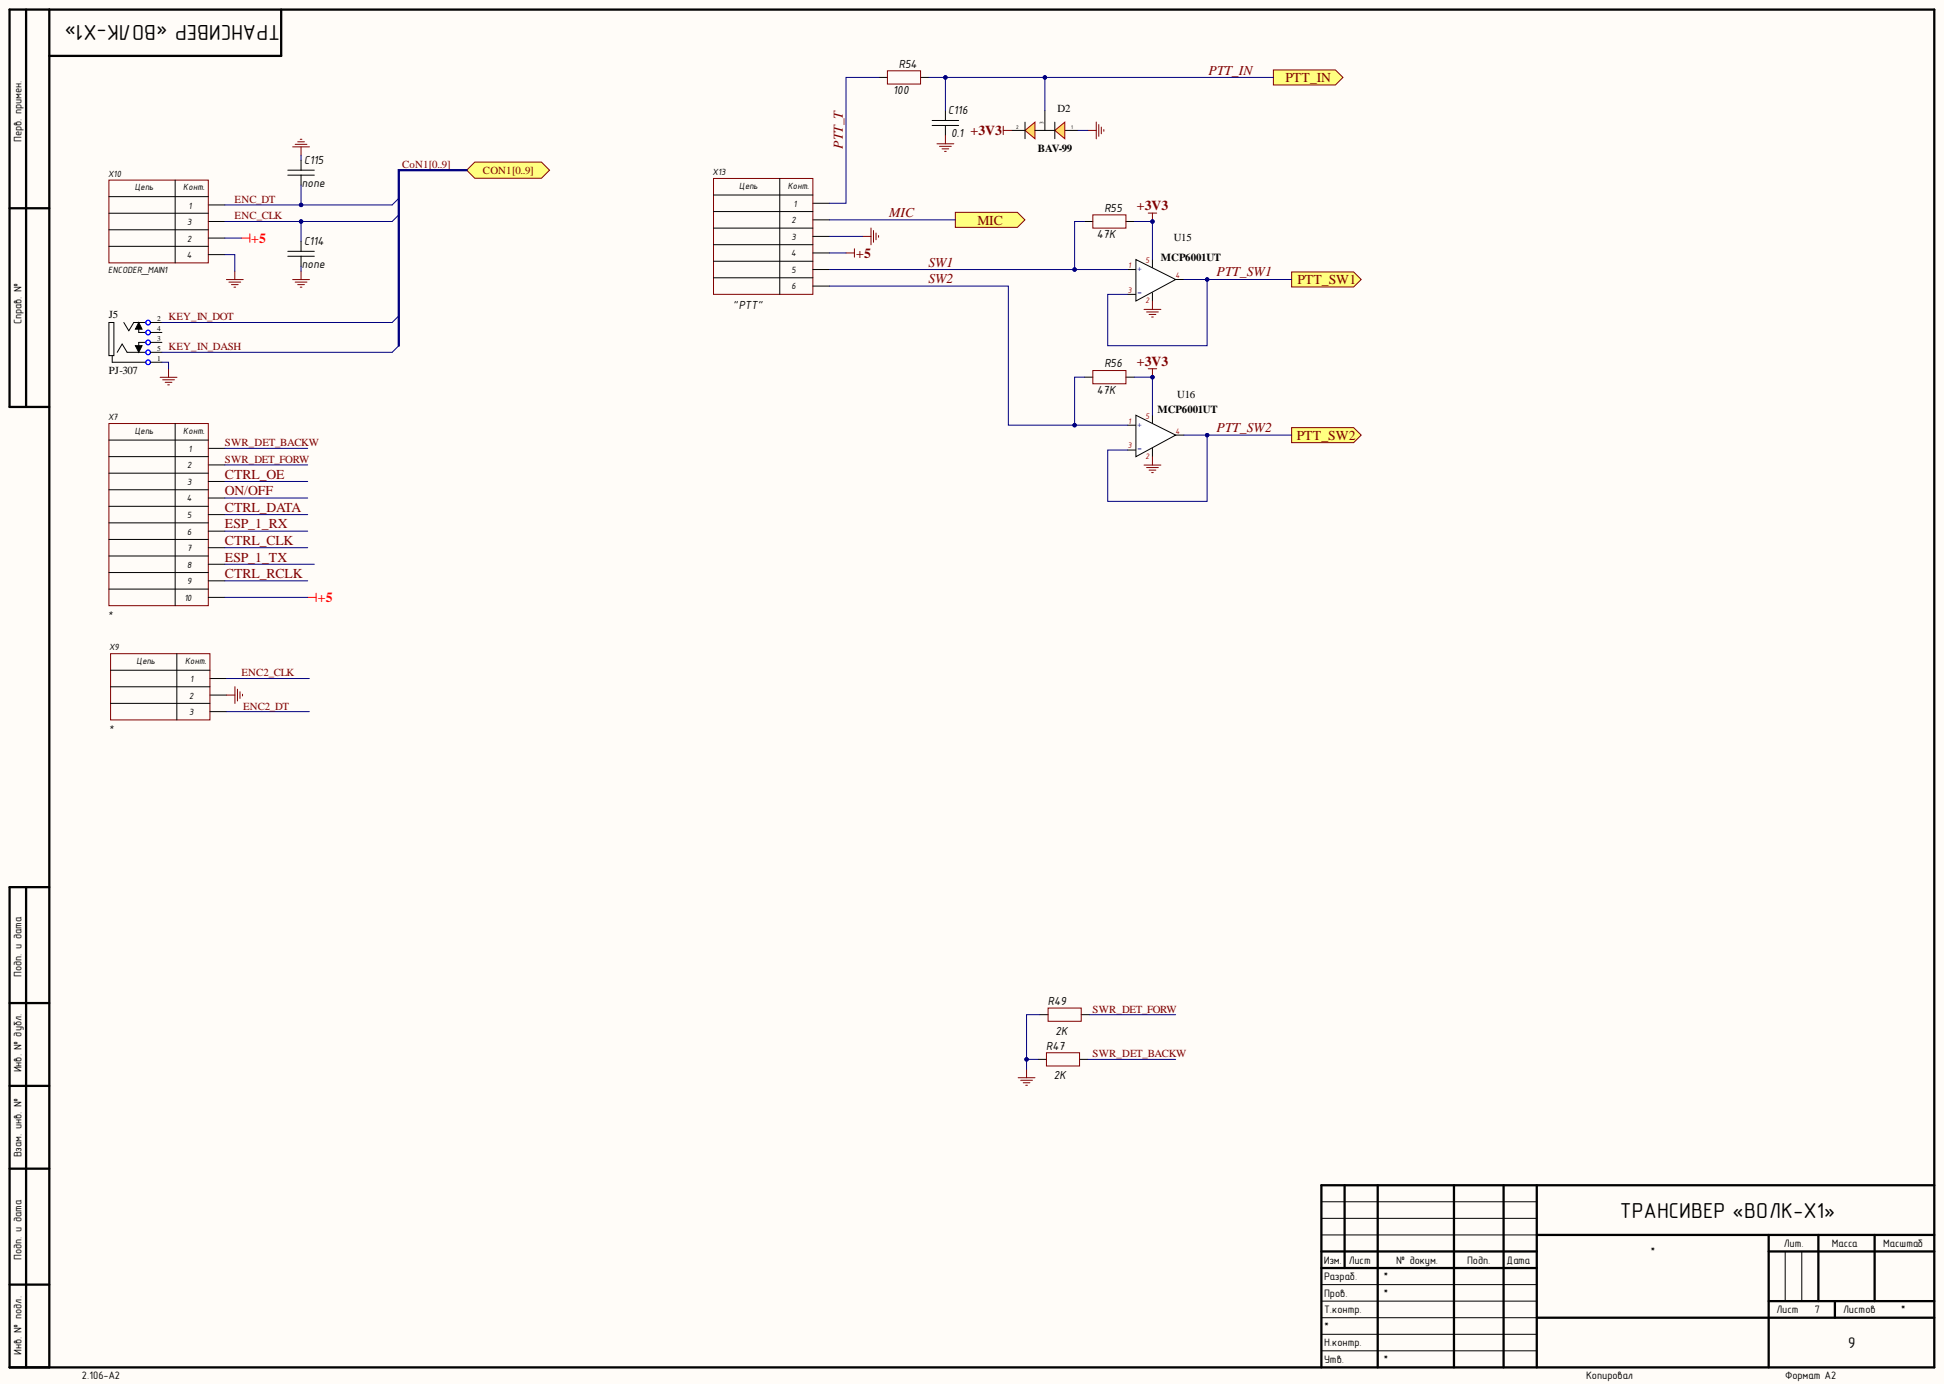
[picture p449: page 7]

Инв. № подл. Инв. № дубл. Подп. и дата Взам. инв. № Подп. и дата Перв. примен. Справ. №

Цепь | Конт.

ТРАНСИВЕР «ВОЛК-X1»

* | Лит. | Масса | Масштаб

Изм. | Лист | № докум. | Подп. | Дата
Разраб. | | *
Пров. | | *
Т.контр. | | | | | Лист | Листов *
Н.контр.
Утв. | *

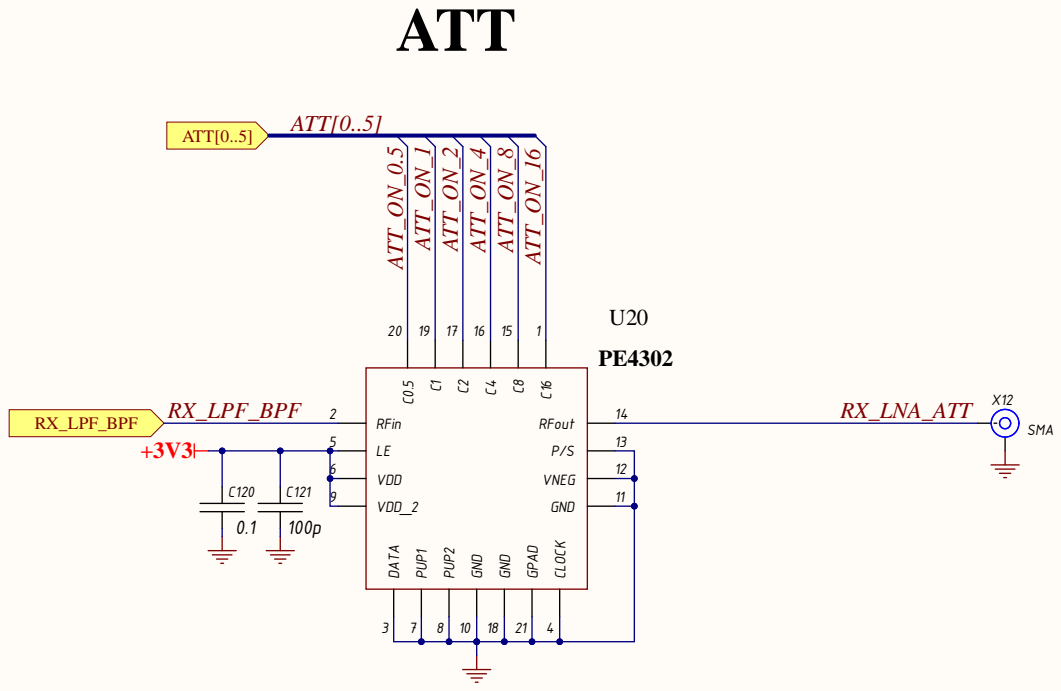
[picture p450: page 8]

Инв. № подл. Инв. № дубл. Подп. и дата Взам. инв. № Подп. и дата

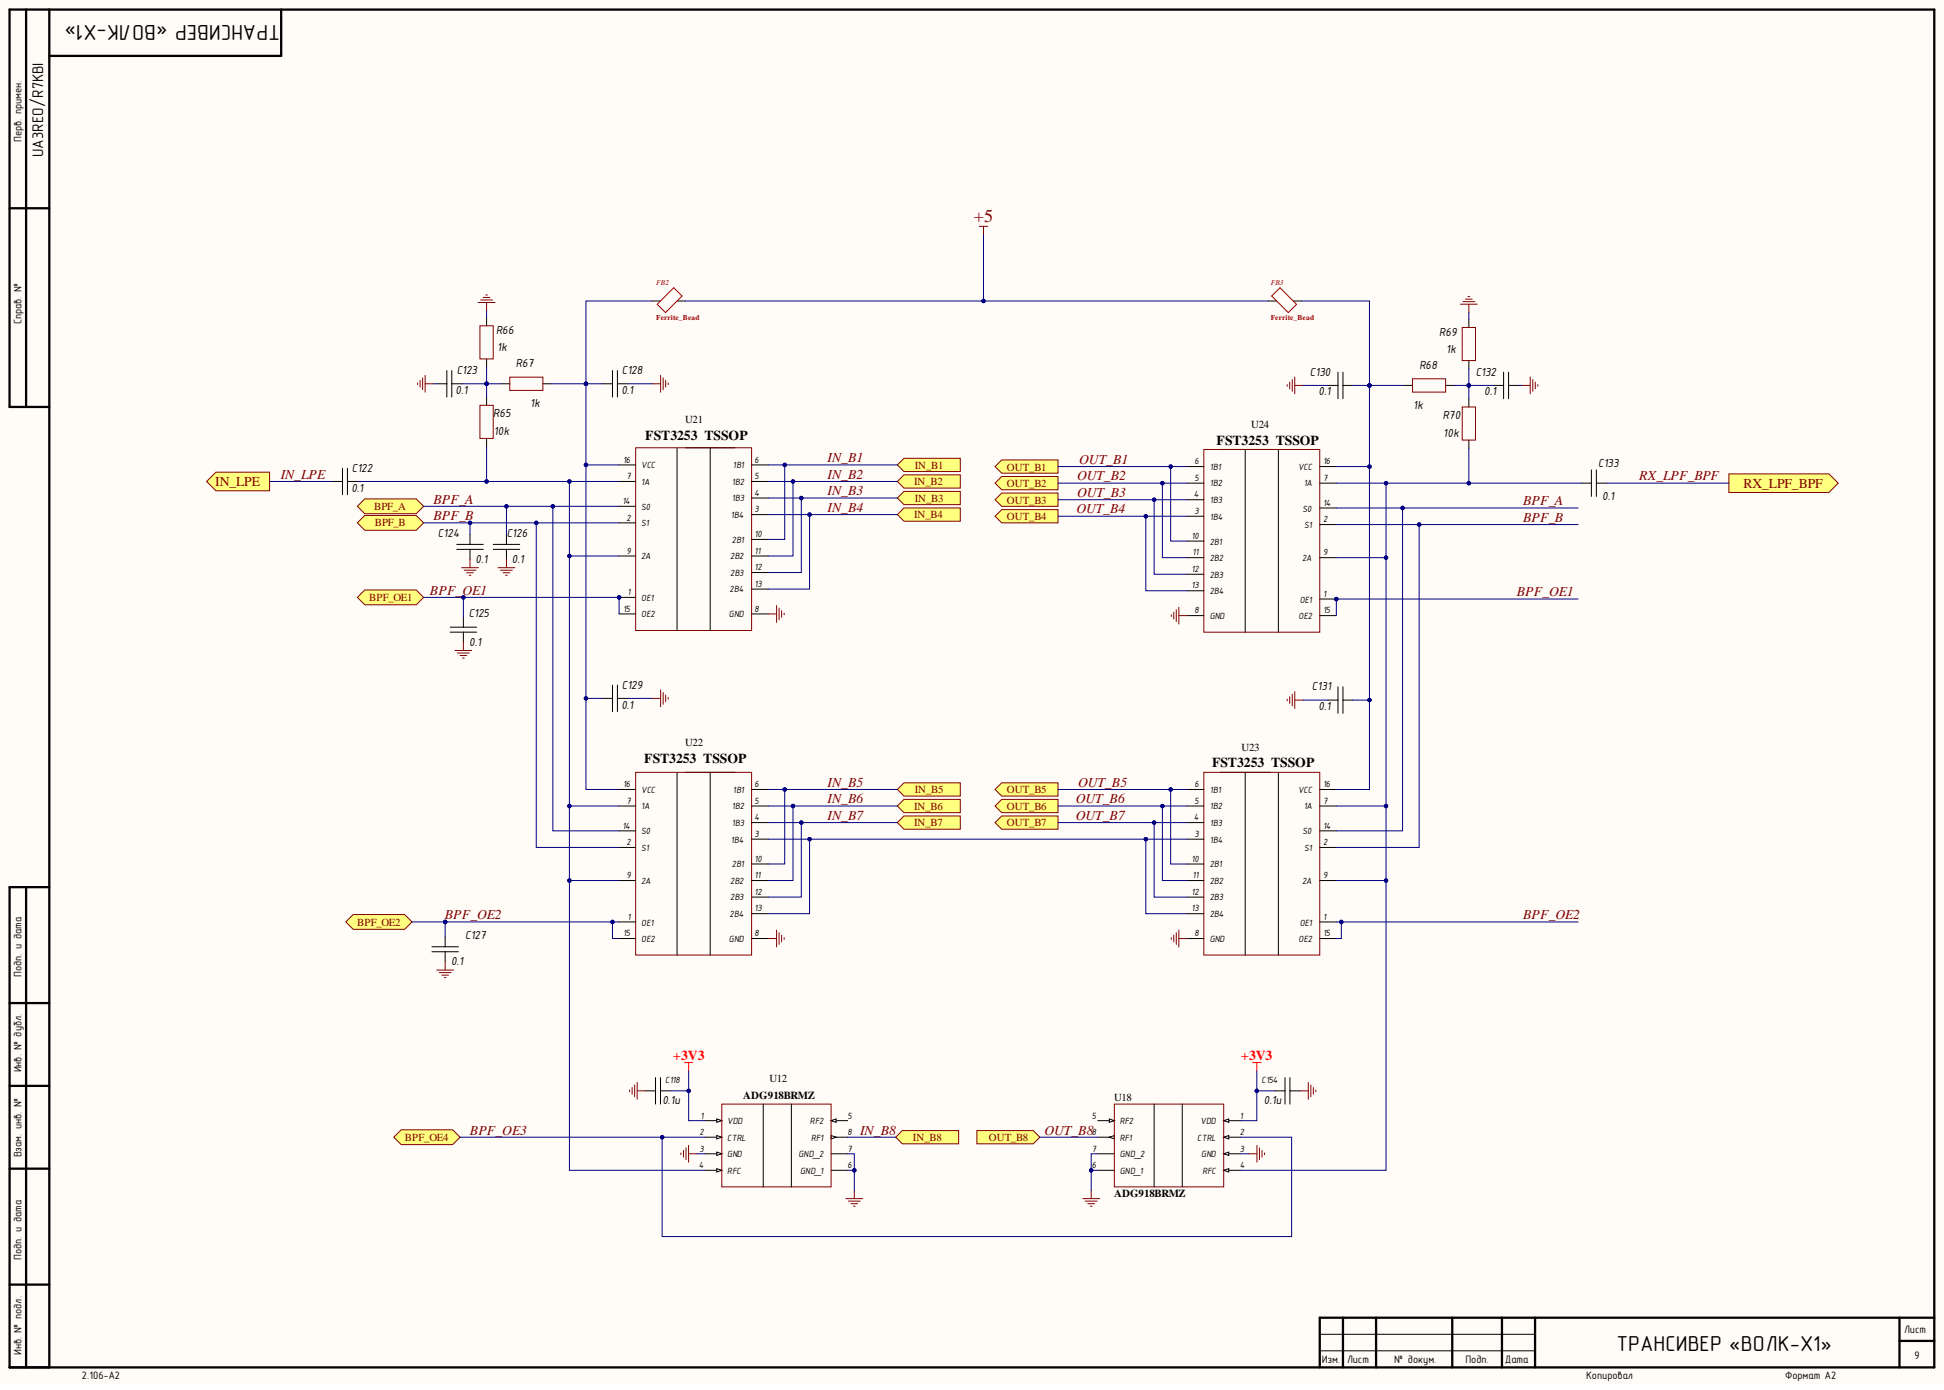
[picture p451: page 9]

Инв. № подл. Инв. № дубл. Подп. и дата Взам. инв. № Подп. и дата Перв. примен. Справ. №

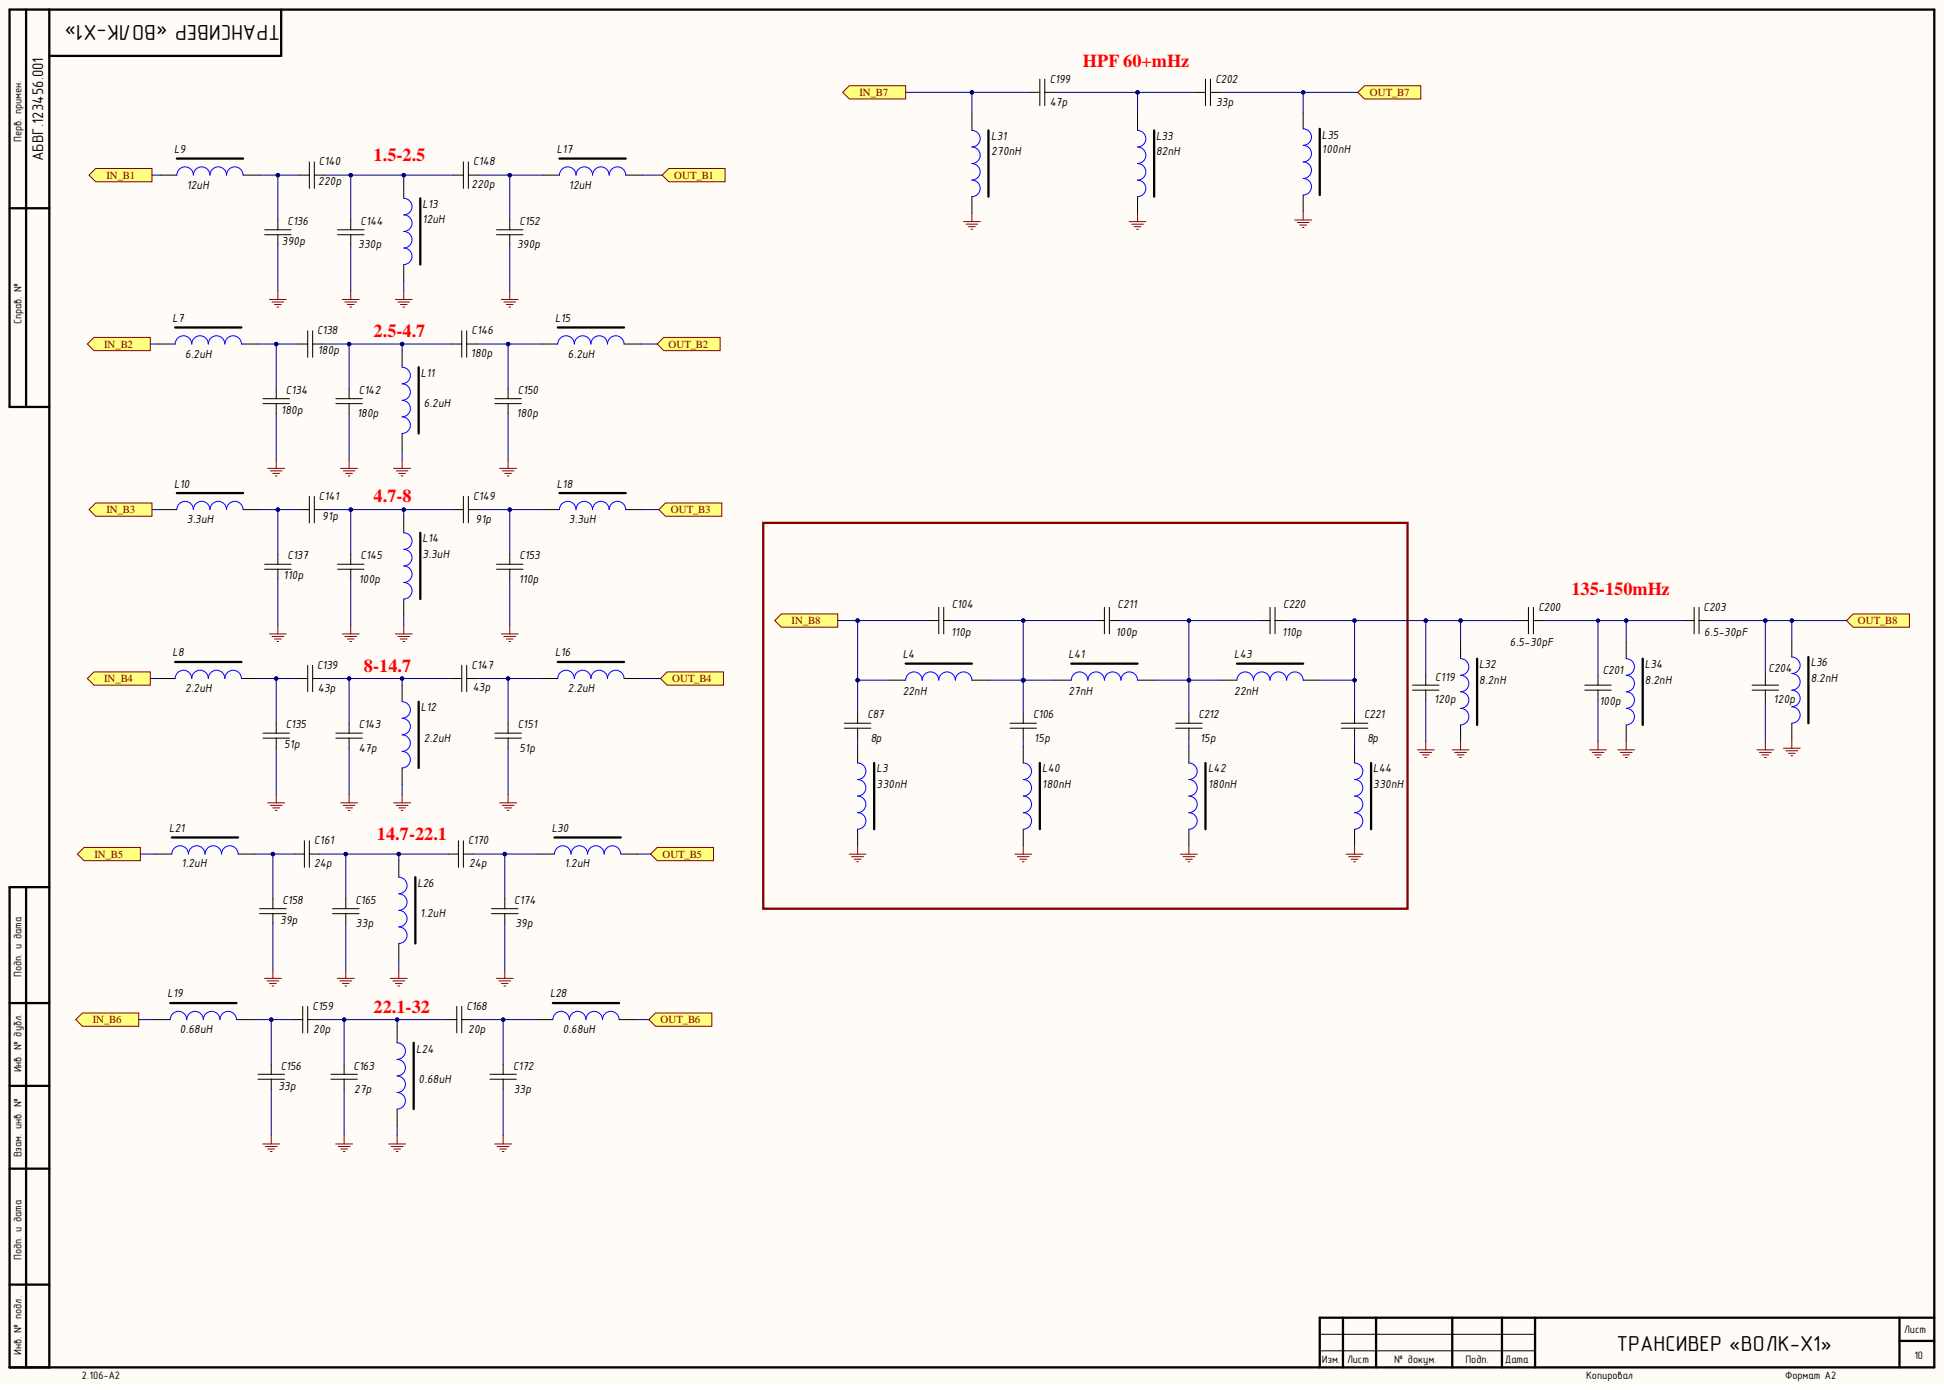
[picture p452: page 10]

HPF 60+mHz

Инв. № подл. Инв. № дубл. Подп. и дата Взам. инв. № Подп. и дата Перв. примен. Справ. №

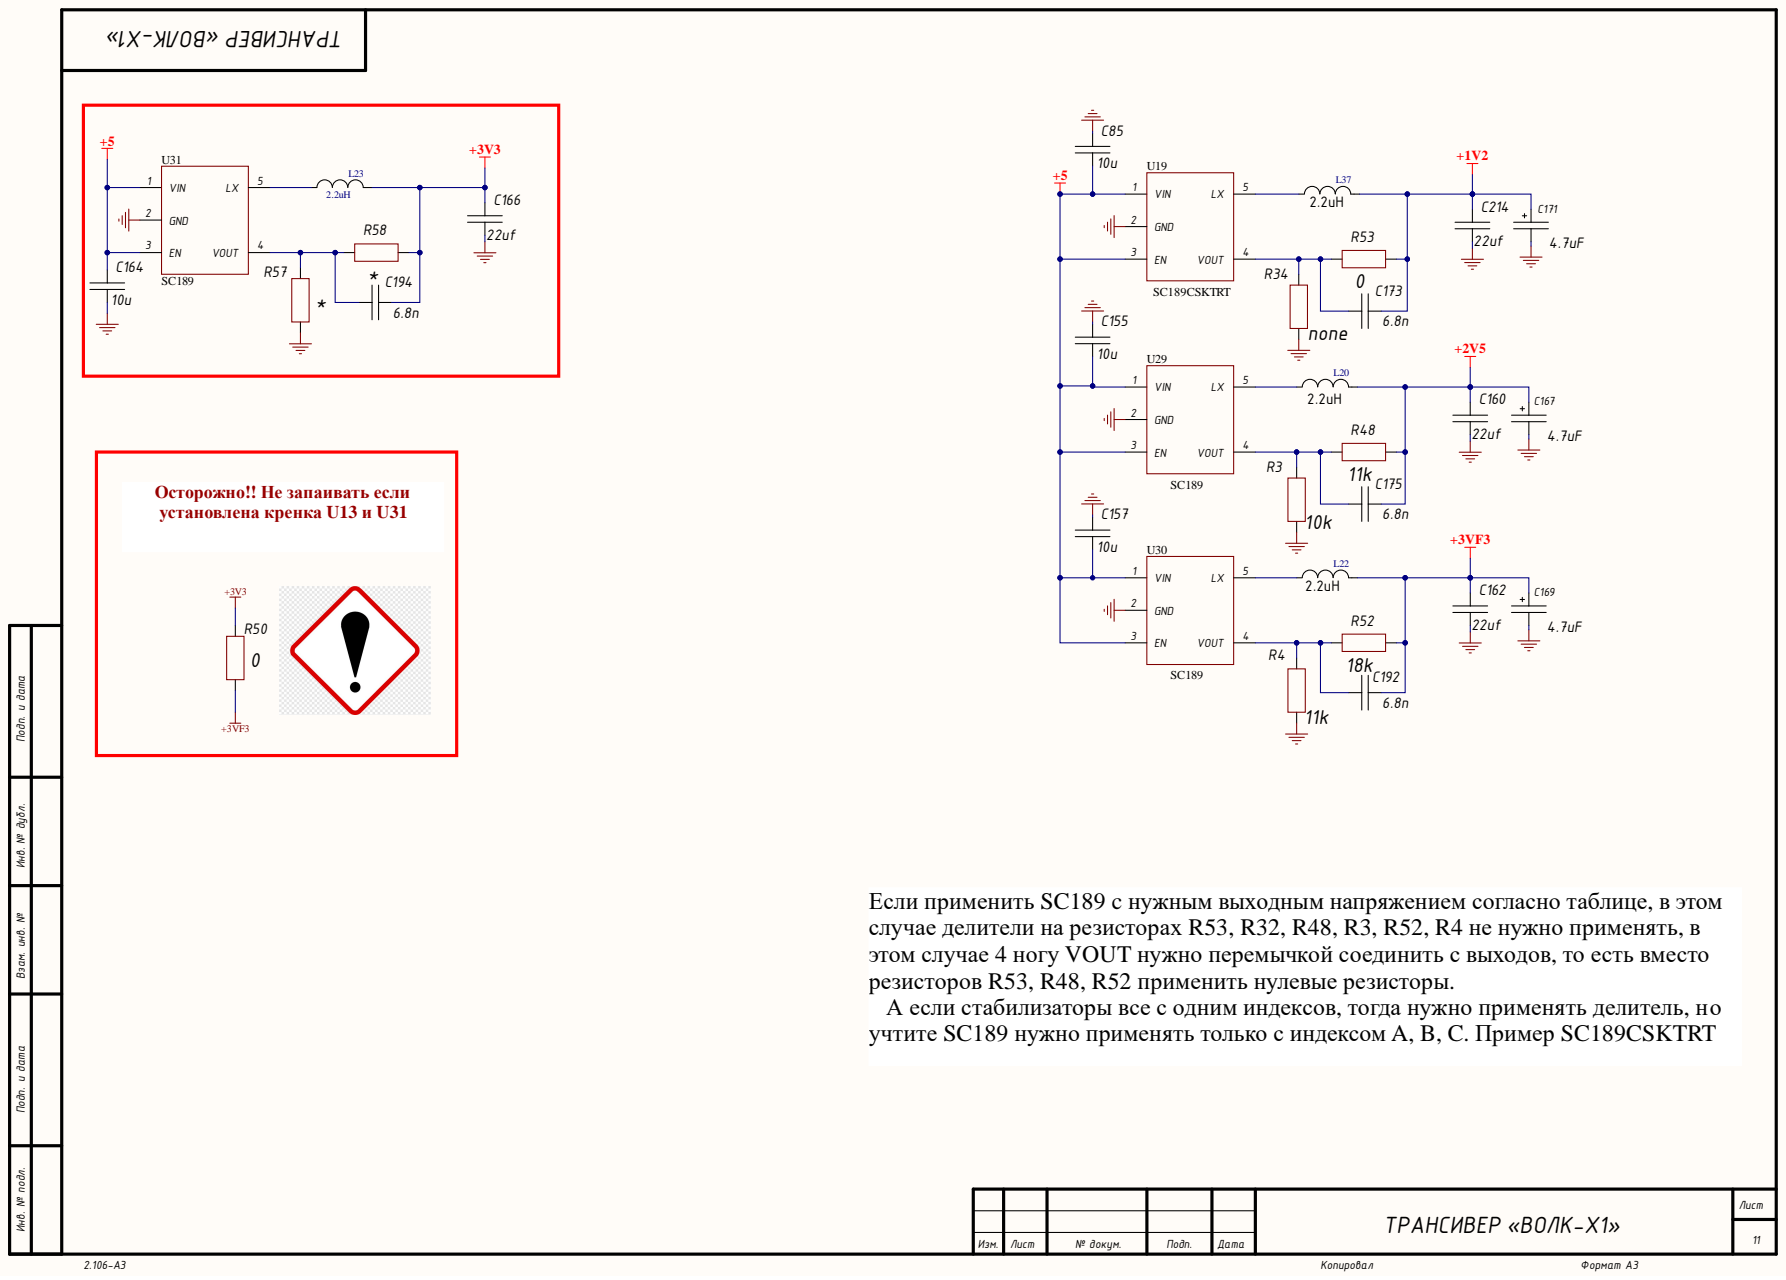
[picture p453: page 11]

Инв. № подл. Инв. № дубл. Подп. и дата Взам. инв. № Подп. и дата

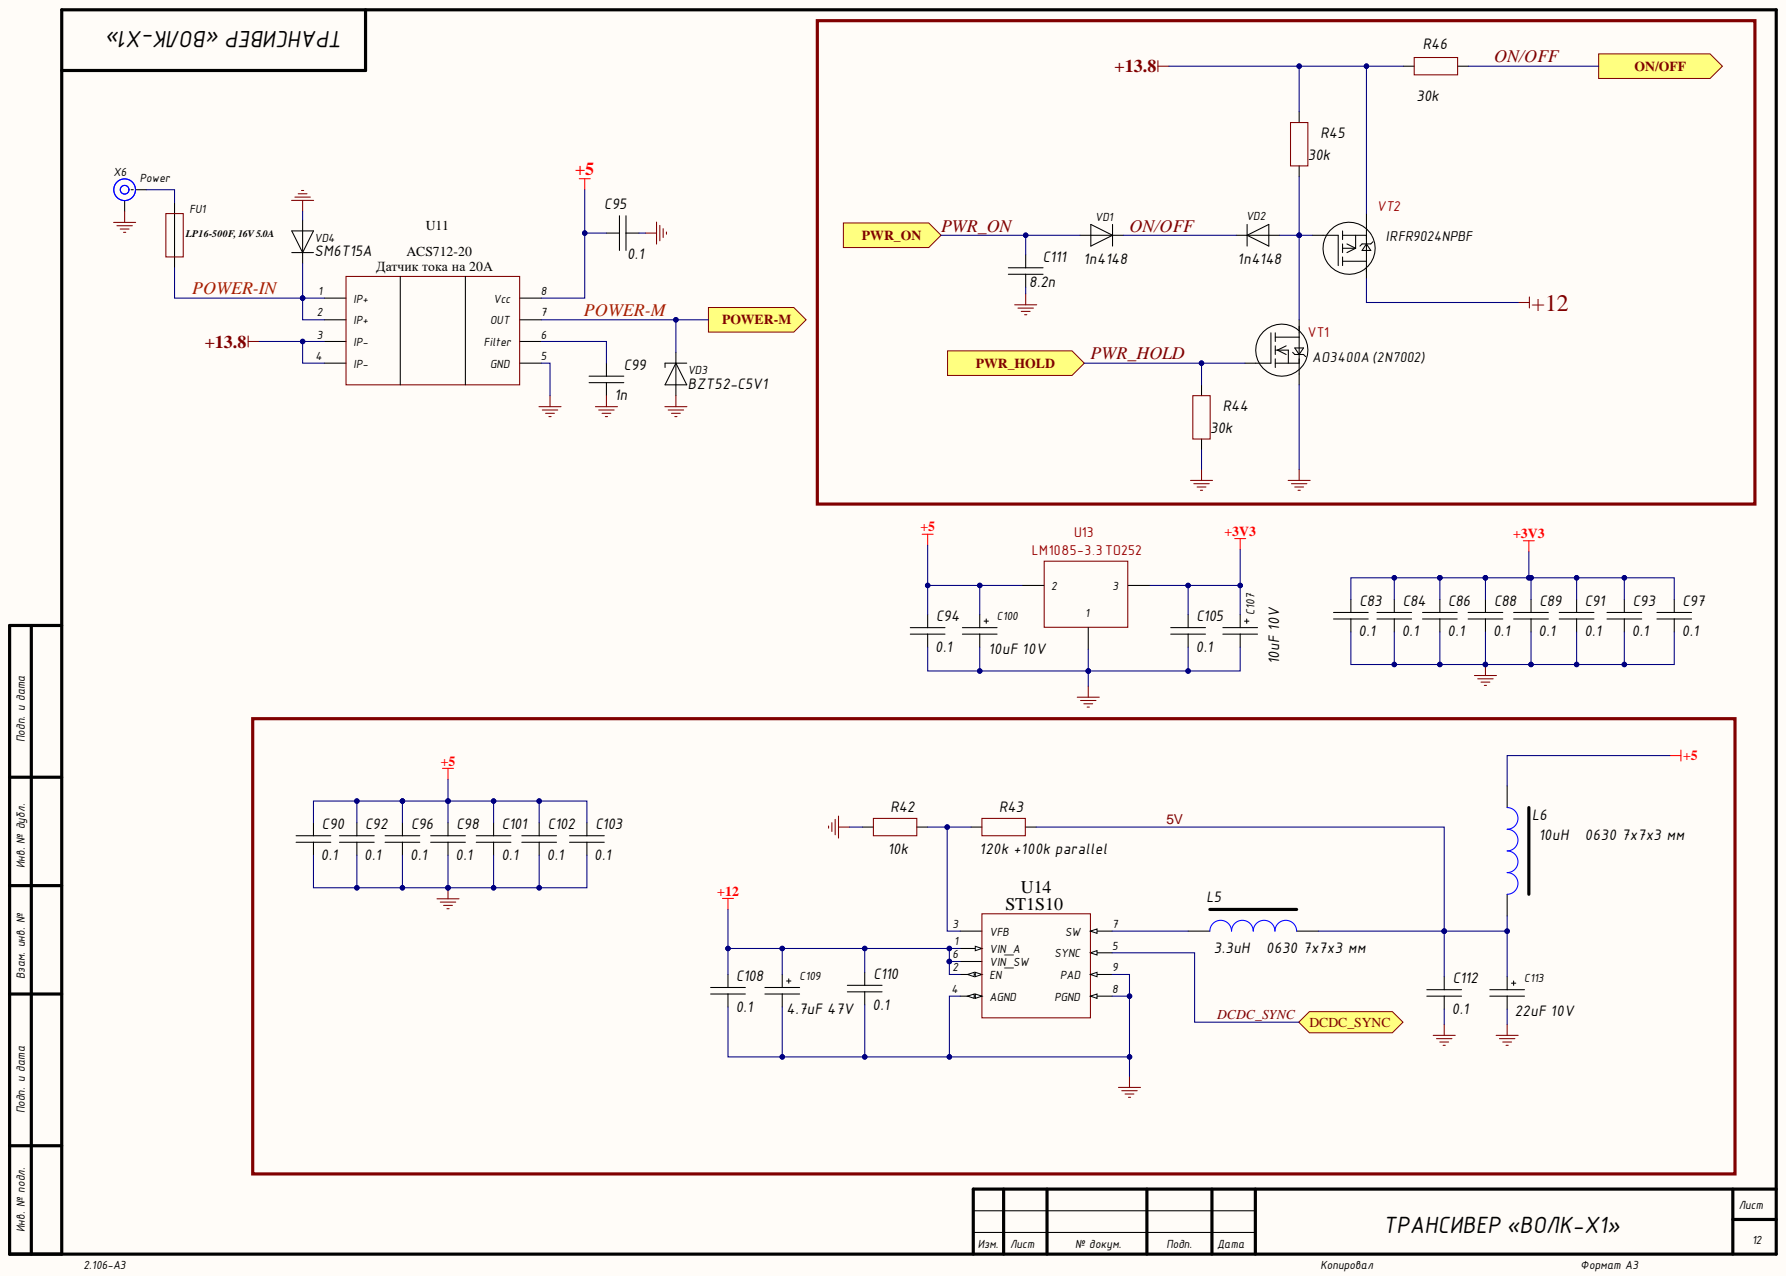
[picture p454: page 12]

Инв. № подл. Инв. № дубл. Подп. и дата Взам. инв. № Подп. и дата

VFB 3 VIN_A 1 SYNC PAD PGND | 3.3uH 0630 7x7x3 мм

EN 2 VIN_SW 6 | 5 9

AGND 4 | | 8
