XGudron/UA3REO-DDC-Transceiver/Schematic/Wolf/Assembly/ASSEMBLY-FRONT-UNIT-3.2-rev10.pdf

R29 | R³³ | R³²

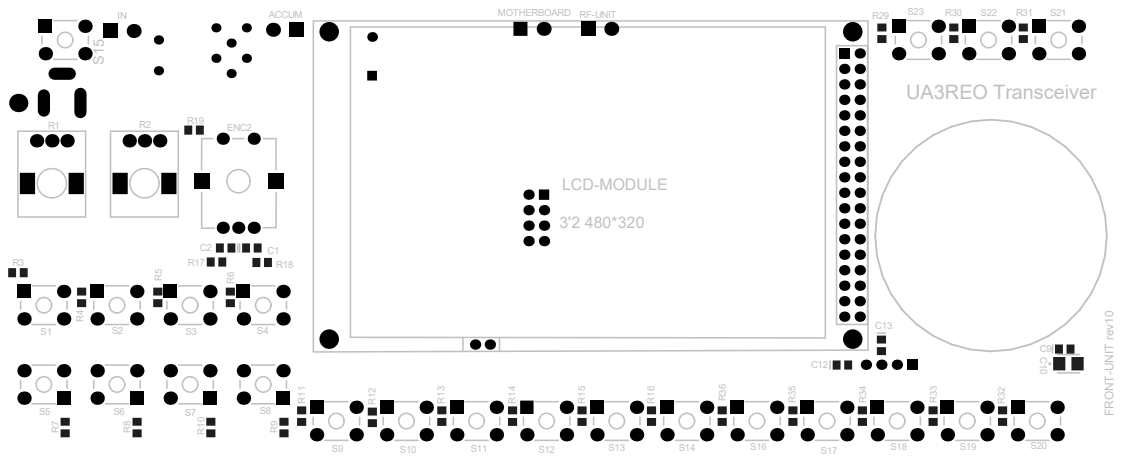
[picture p459: page 1]

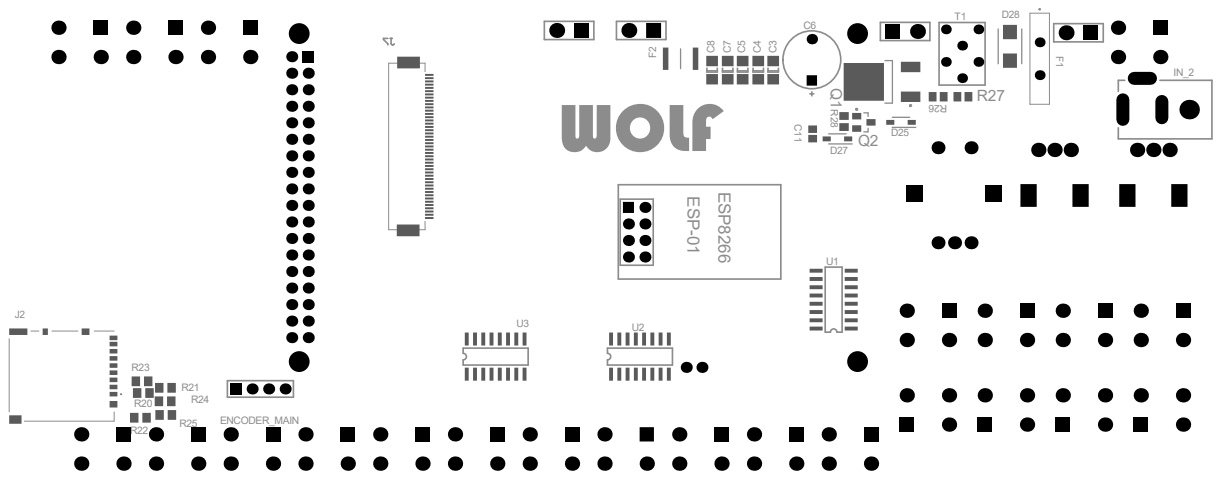
[picture p460: page 2]
