XGudron/UA3REO-DDC-Transceiver/Schematic/Wolf/Assembly/ASSEMBLY-FRONT-UNIT-3.2-WIDE-rev10.pdf

R29 | R³⁴
R30 | R³³ | R³²

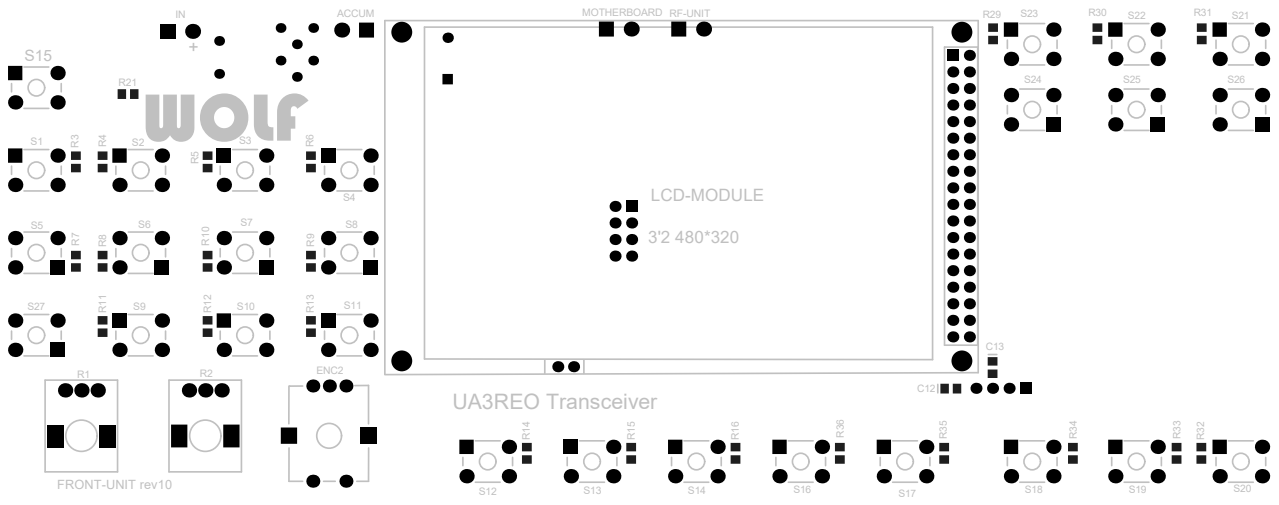
[picture p461: page 1]
R¹⁶; R³⁶ R¹⁰; R¹³ R⁹ R⁶; R¹¹; R¹⁴; R¹⁵; R³⁵; R¹²; ENC2; LCD-MODULE; FRONT-UNIT rev10; ACCUM; UA3REO Transceiver; WOLF

MOTHERBOARD RF-UNIT

# D28 R18 C1

T1 C2

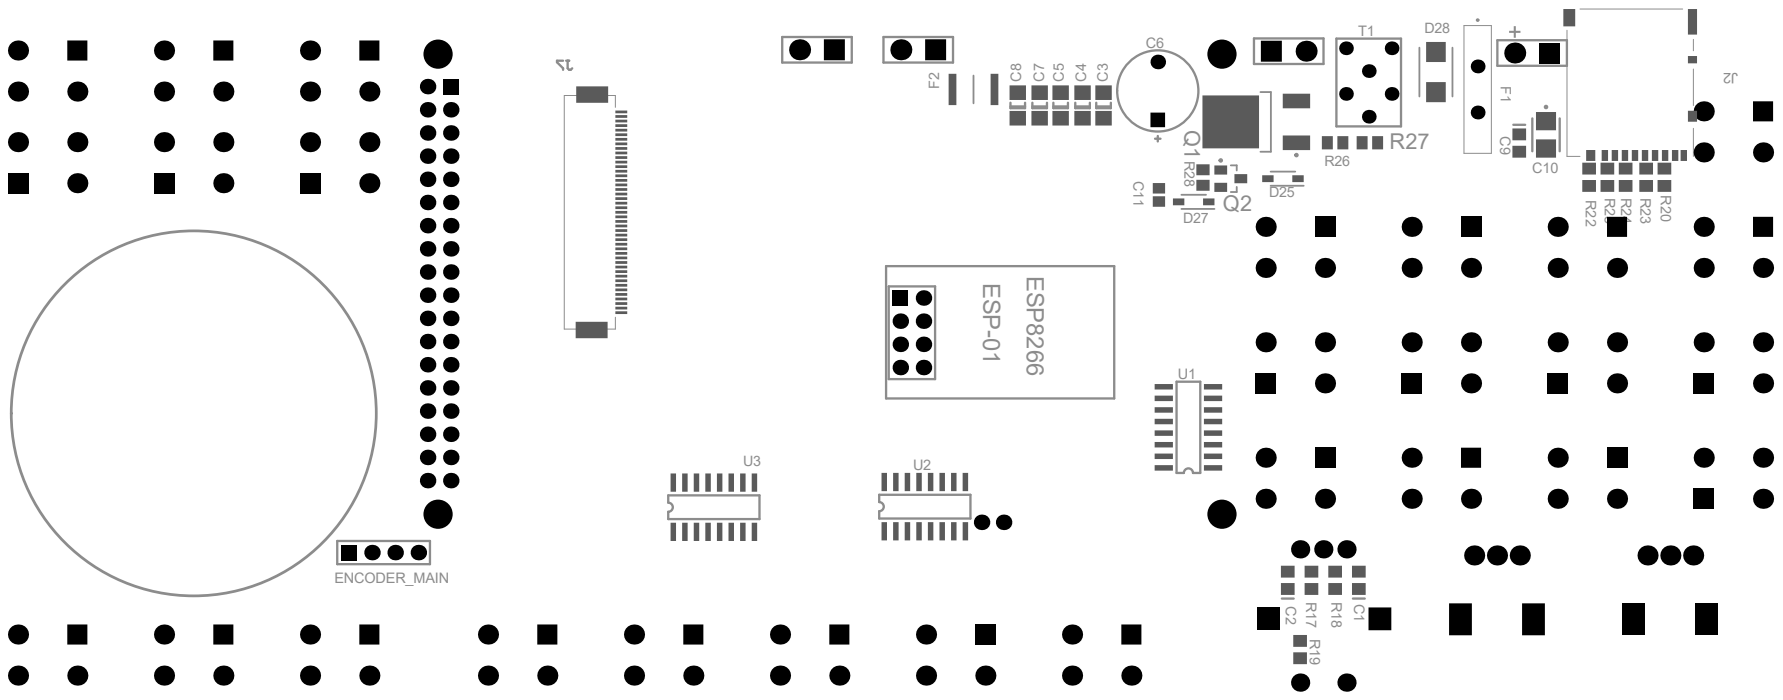
[picture p462: page 2]
