XGudron/UA3REO-DDC-Transceiver/Schematic/Wolf/Assembly/ASSEMBLY-FRONT-UNIT-3.5-rev10.pdf

R29 | R³³ | R³²

S15

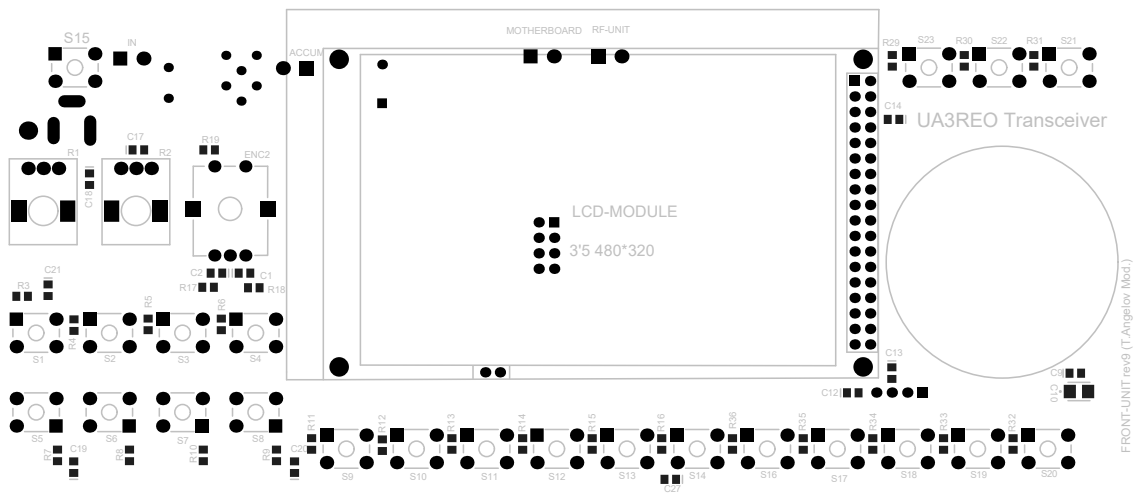
[picture p463: page 1]

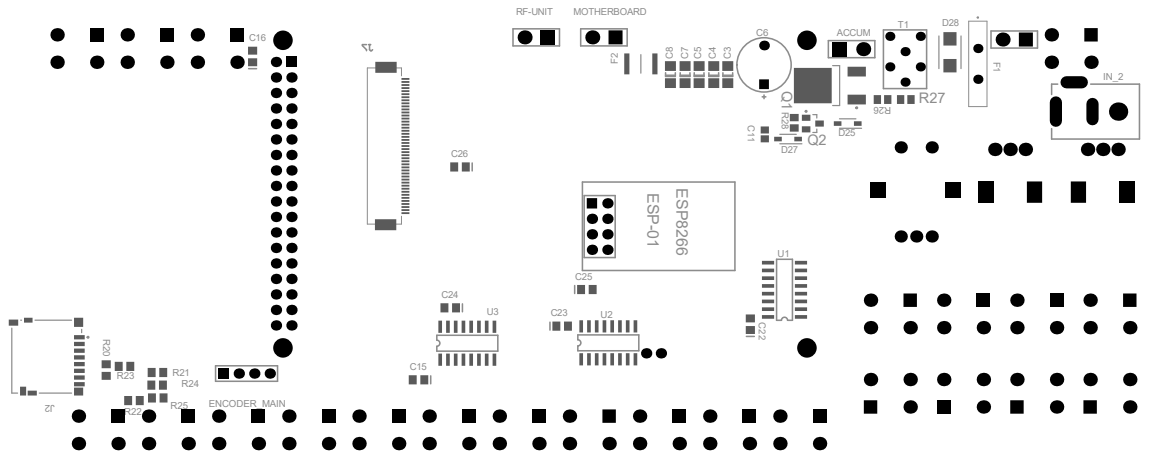
[picture p464: page 2]
