XGudron/UA3REO-DDC-Transceiver/Schematic/Wolf/Assembly/ASSEMBLY-FRONT-UNIT-7-rev5.pdf

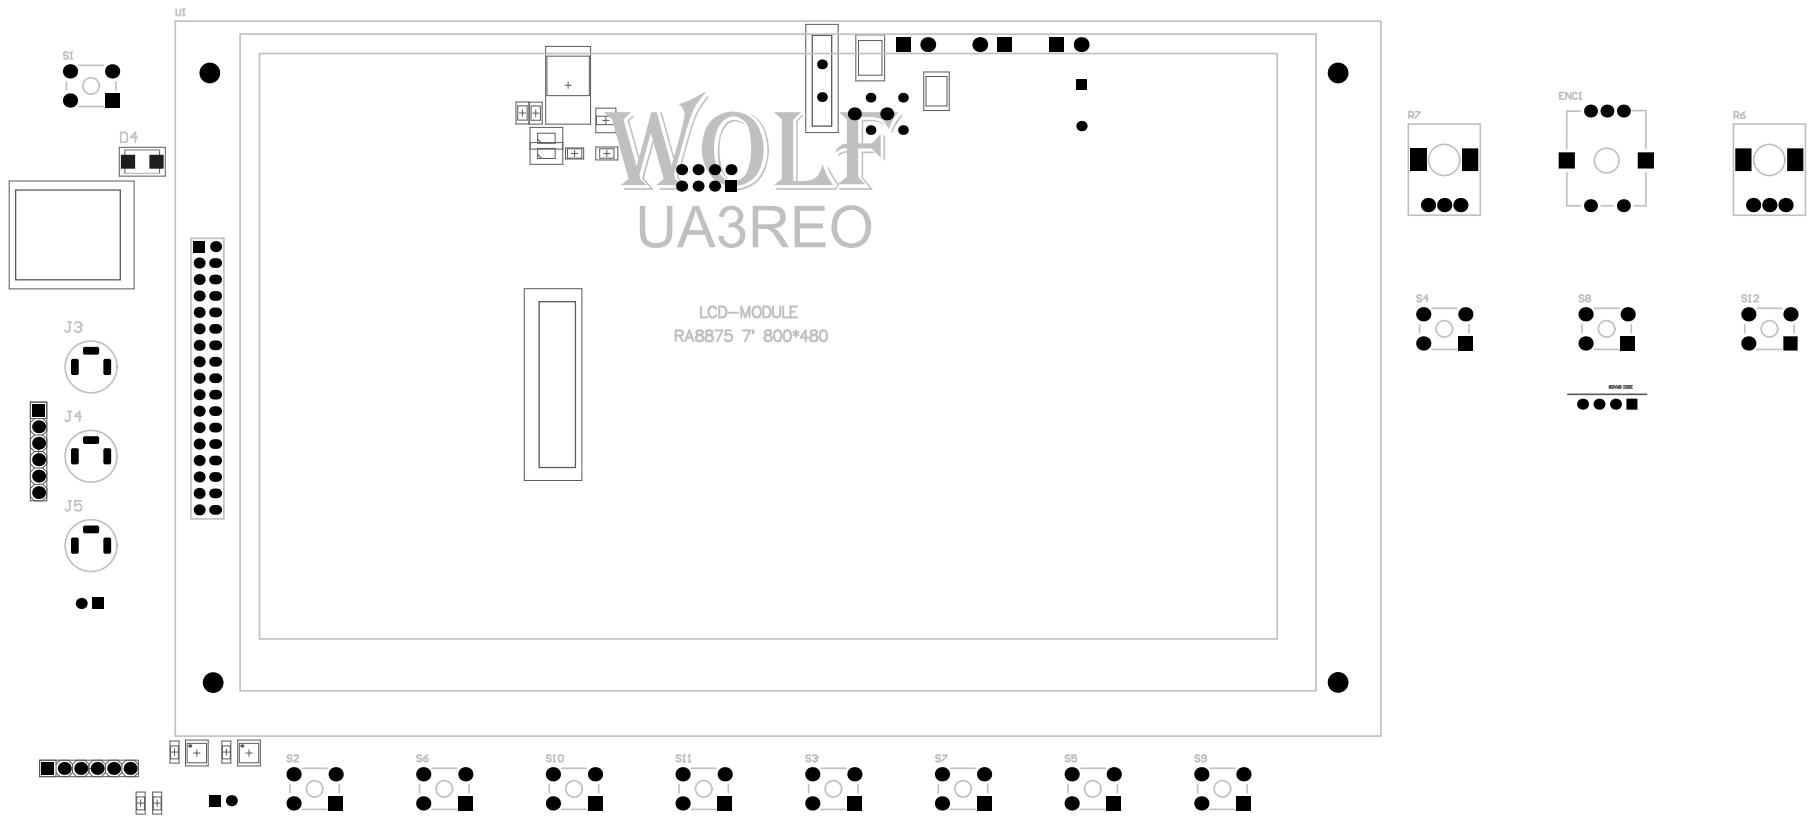
[picture p465: page 1]

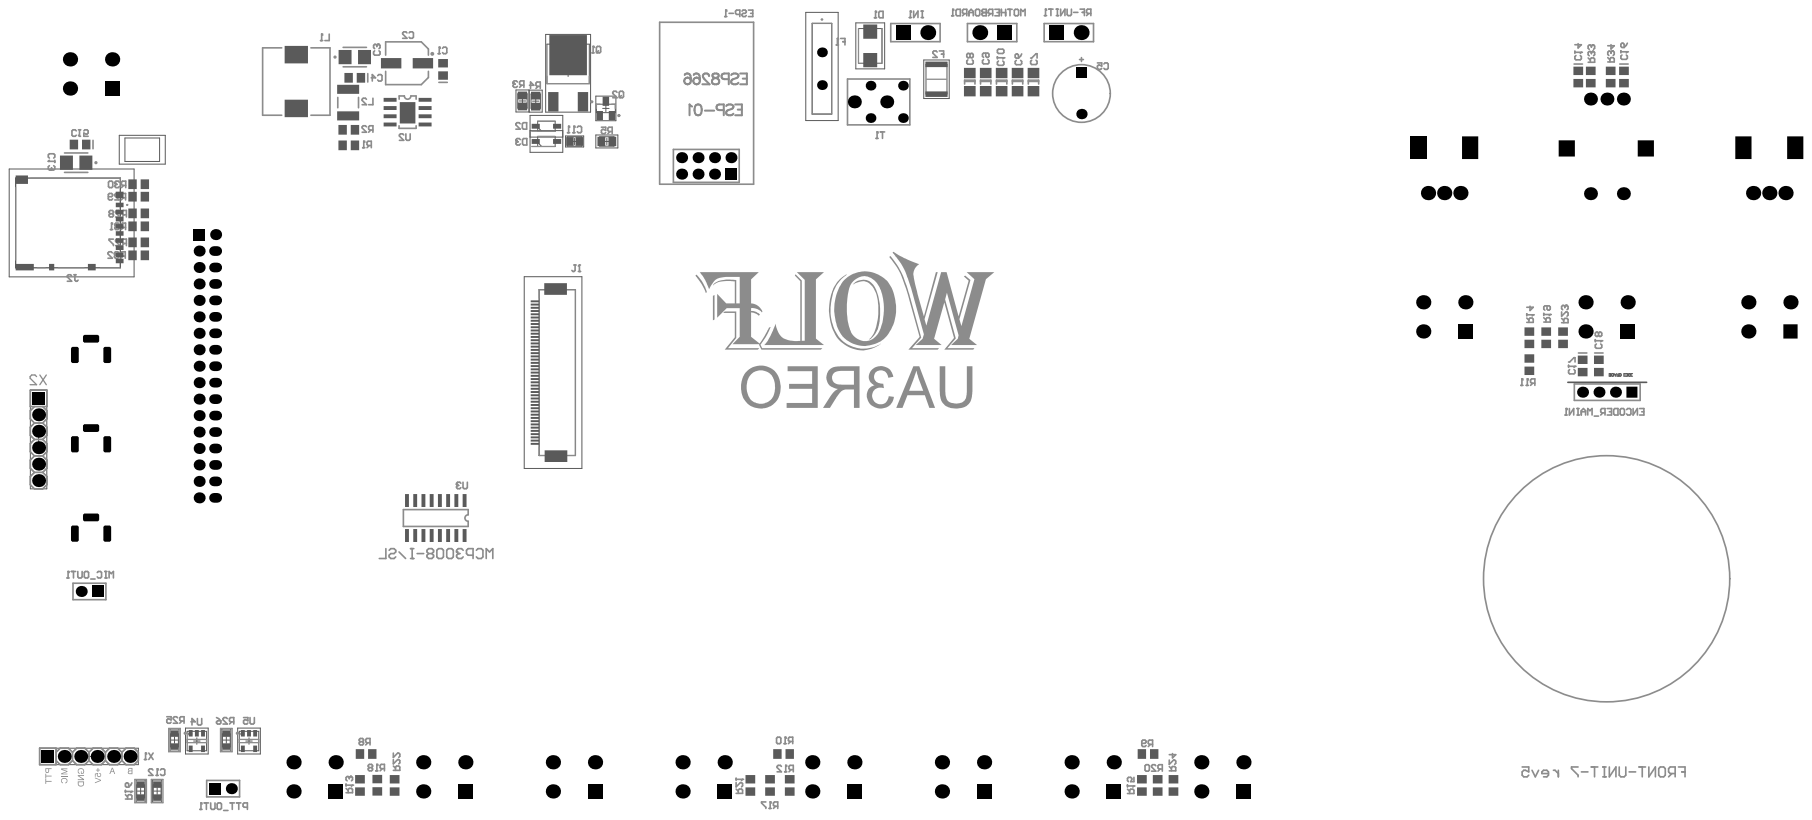
[picture p466: page 2]
