XGudron/UA3REO-DDC-Transceiver/Schematic/Wolf/Assembly/ASSEMBLY-MOTHERBOARD-rev34.PDF

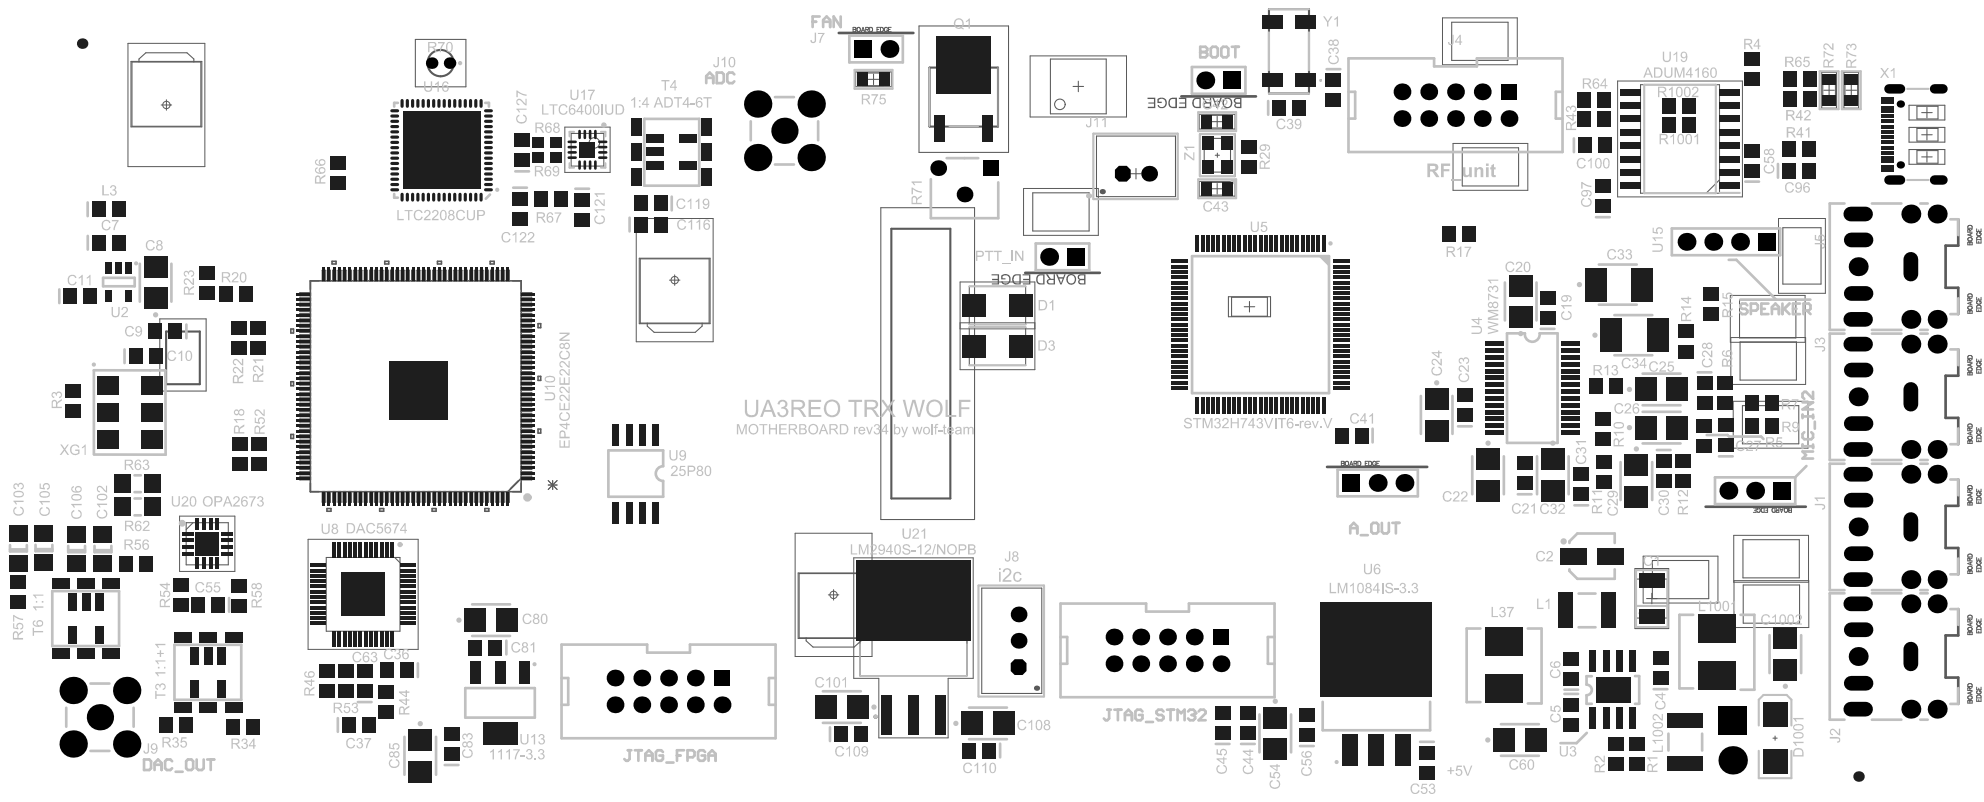
[picture p467: page 1]

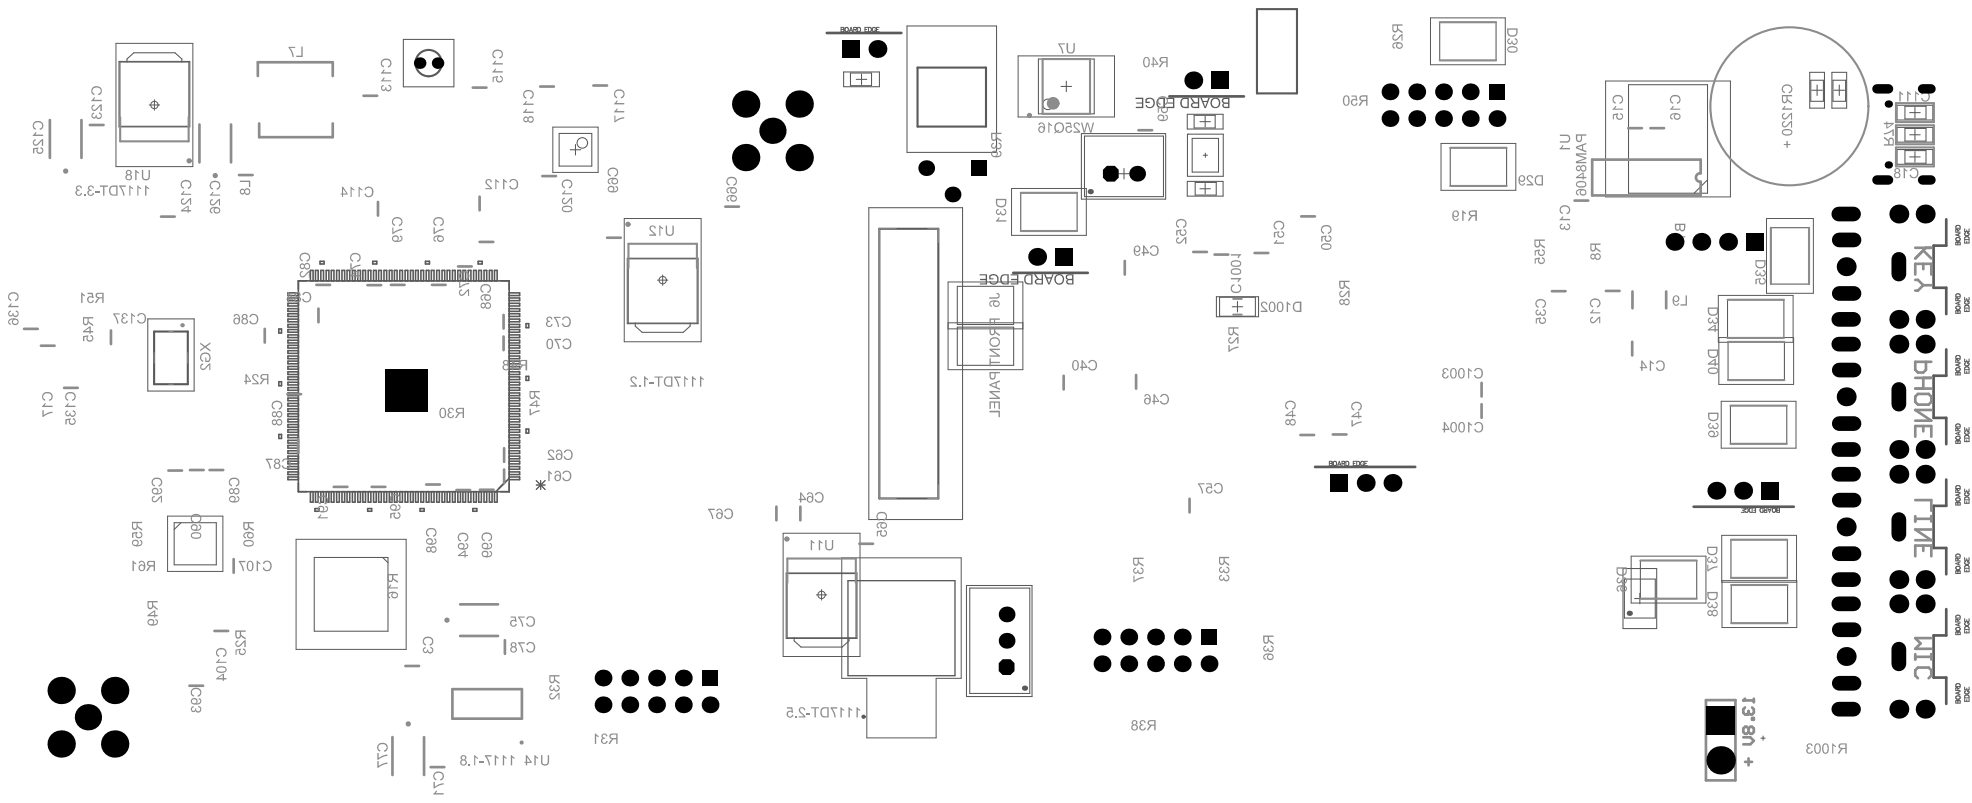
[picture p468: page 2]

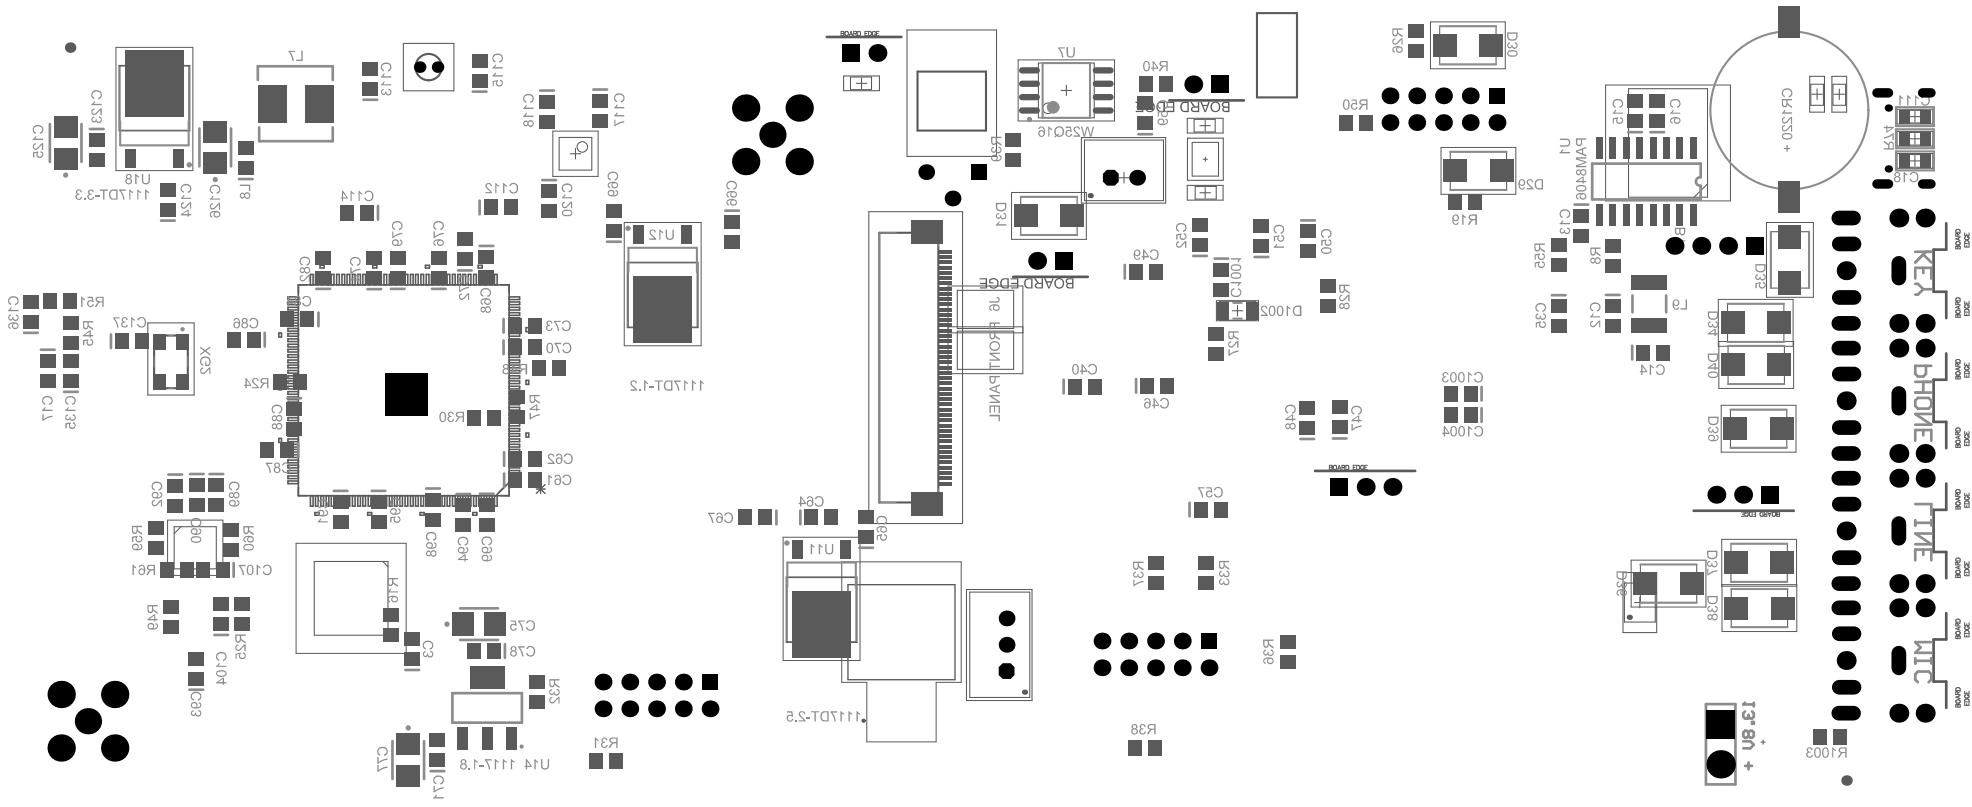
[picture p469: page 4]
