XGudron/UA3REO-DDC-Transceiver/Schematic/Wolf/Assembly/ASSEMBLY-RF-UNIT-QRP-rev22.pdf

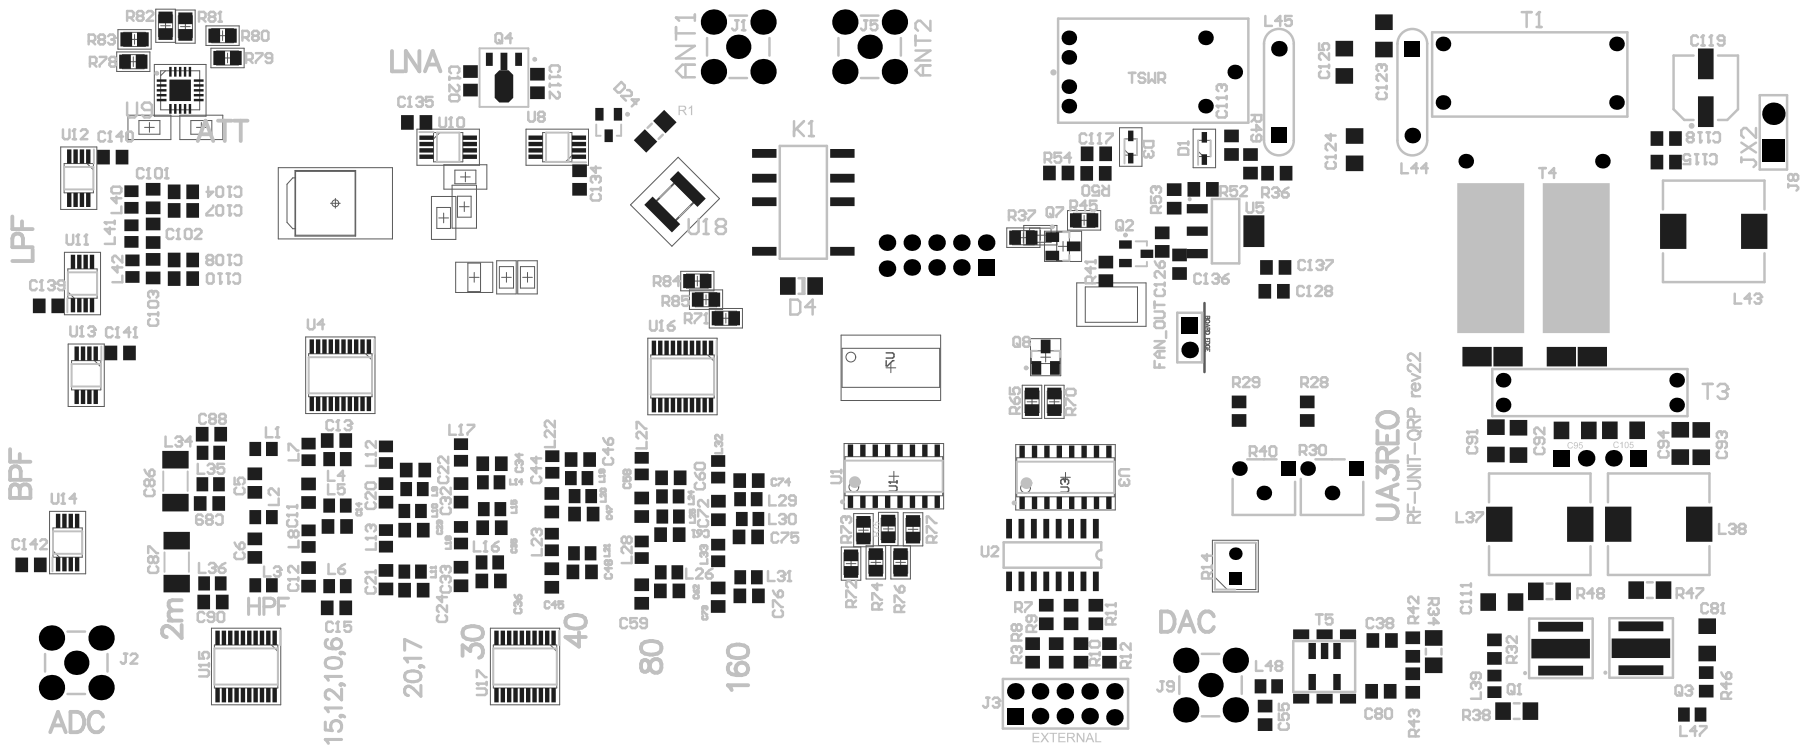
[picture p470: page 1]

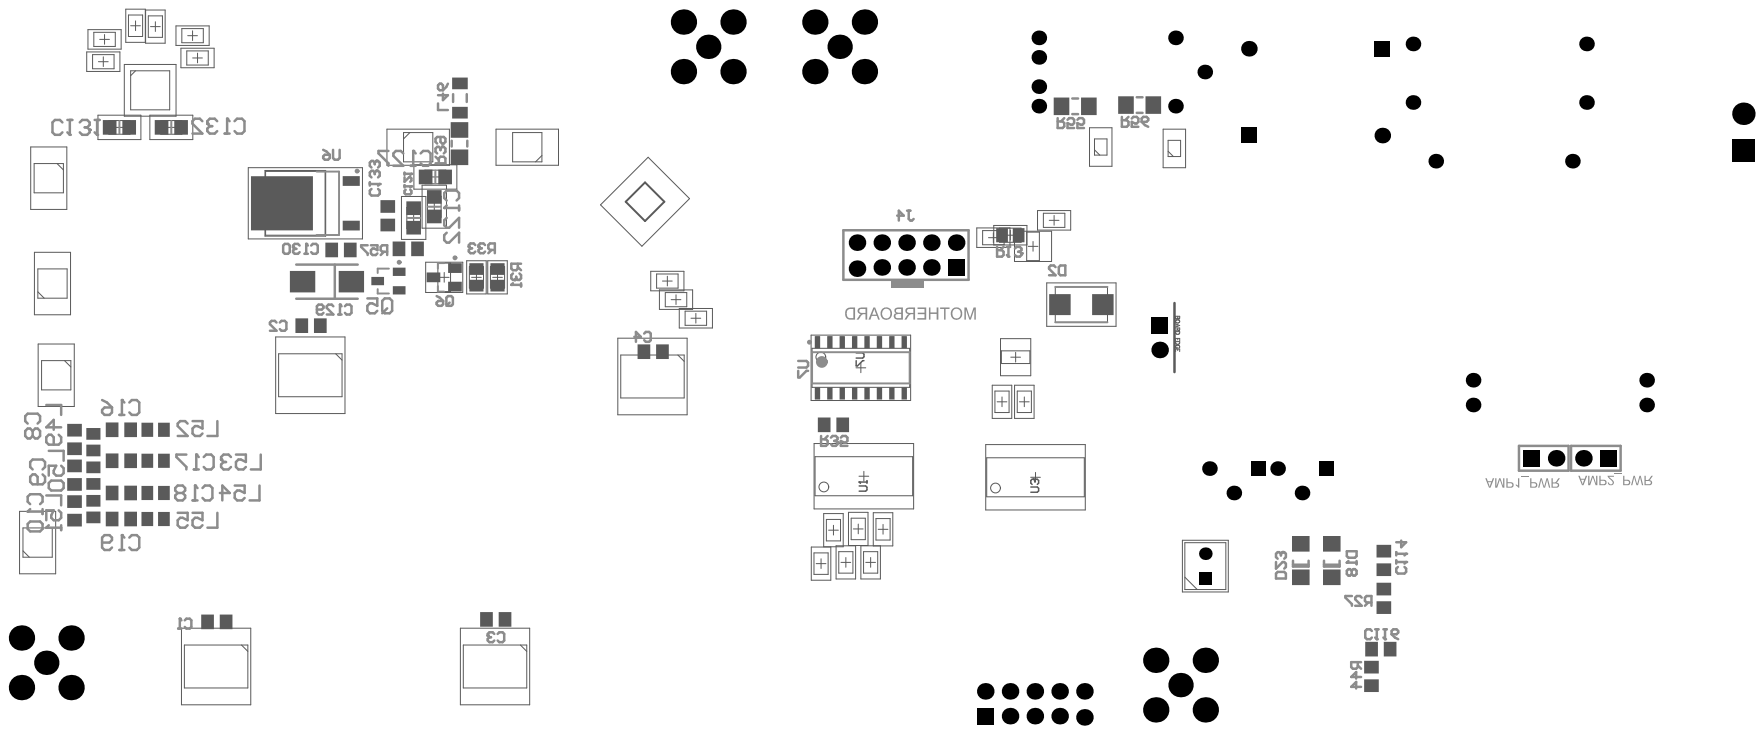
[picture p471: page 2]
