XGudron/UA3REO-DDC-Transceiver/Schematic/Wolf-2/Addons/ATT&Protector/ATT&Protector_Wolf_v2.pdf

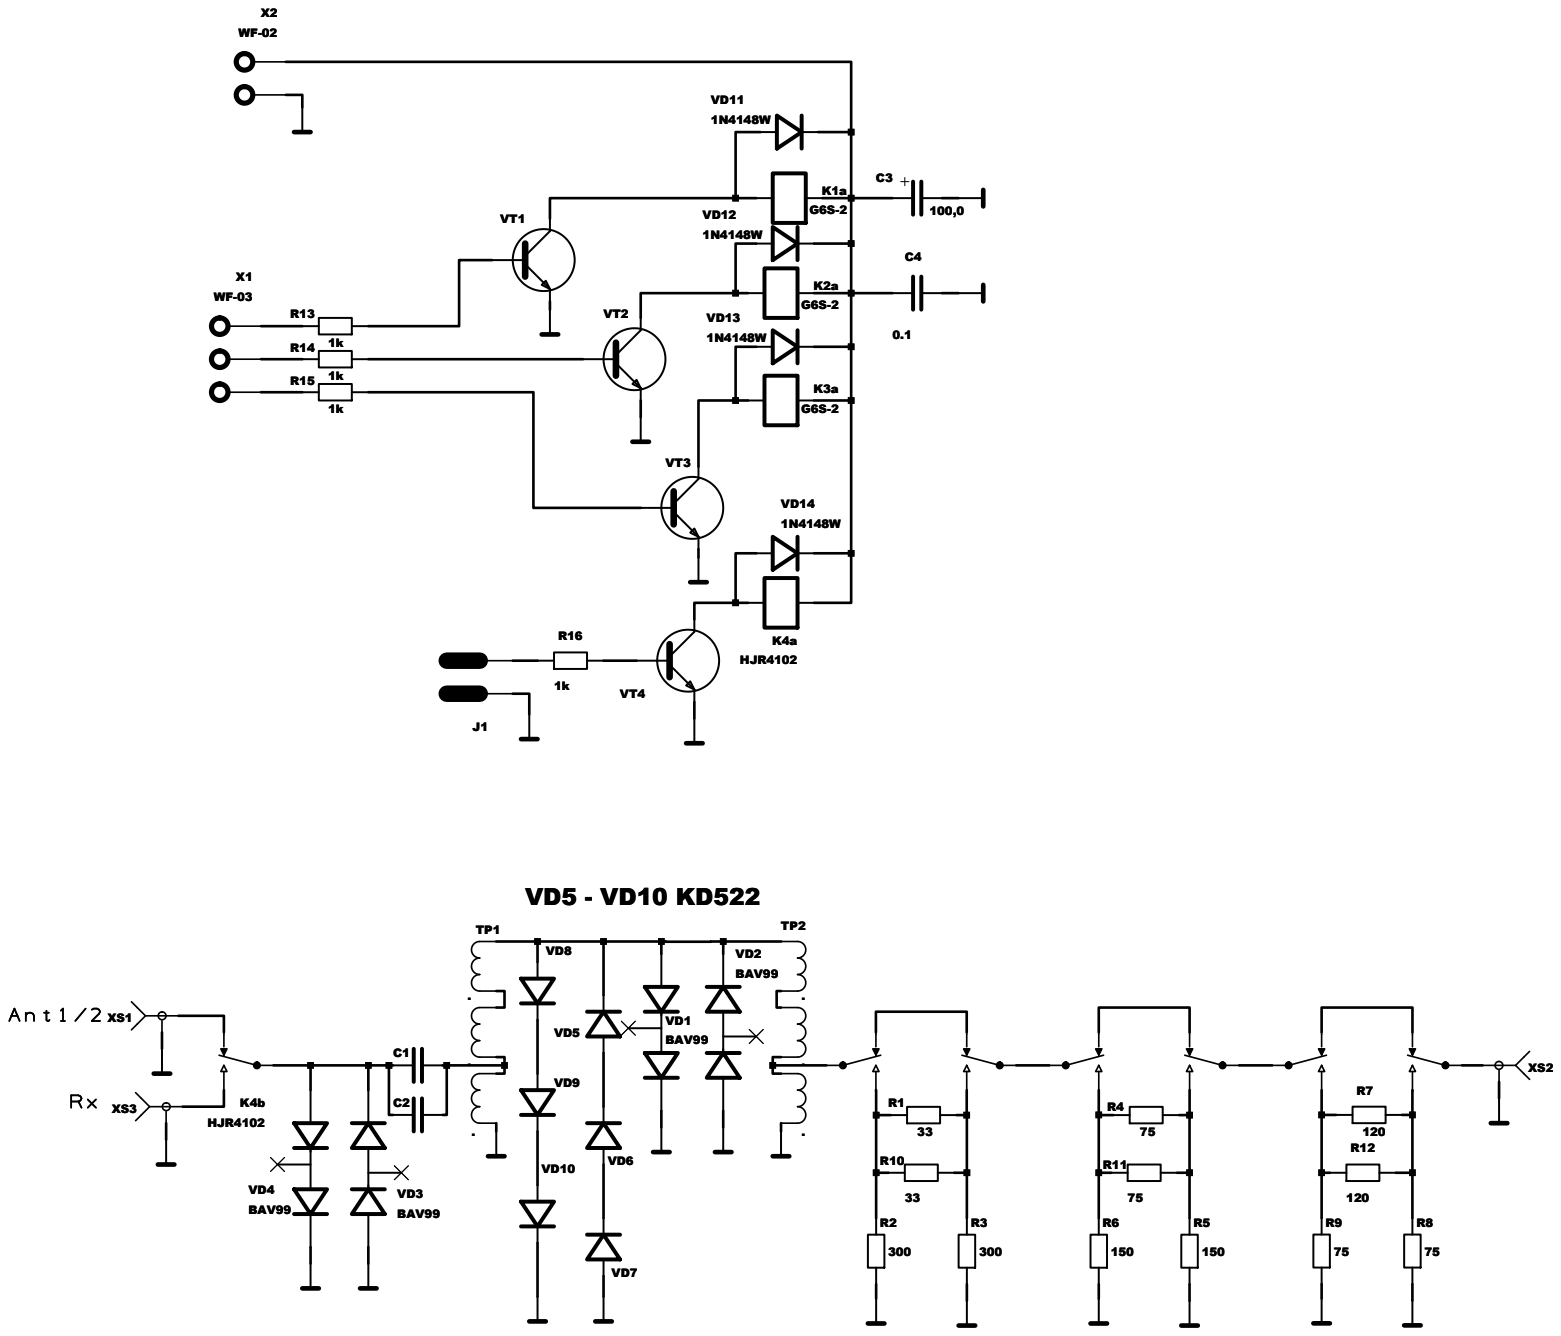
[picture p472: page 1]
