XGudron/UA3REO-DDC-Transceiver/Schematic/Wolf/Addons/PA_Control/remote.pdf

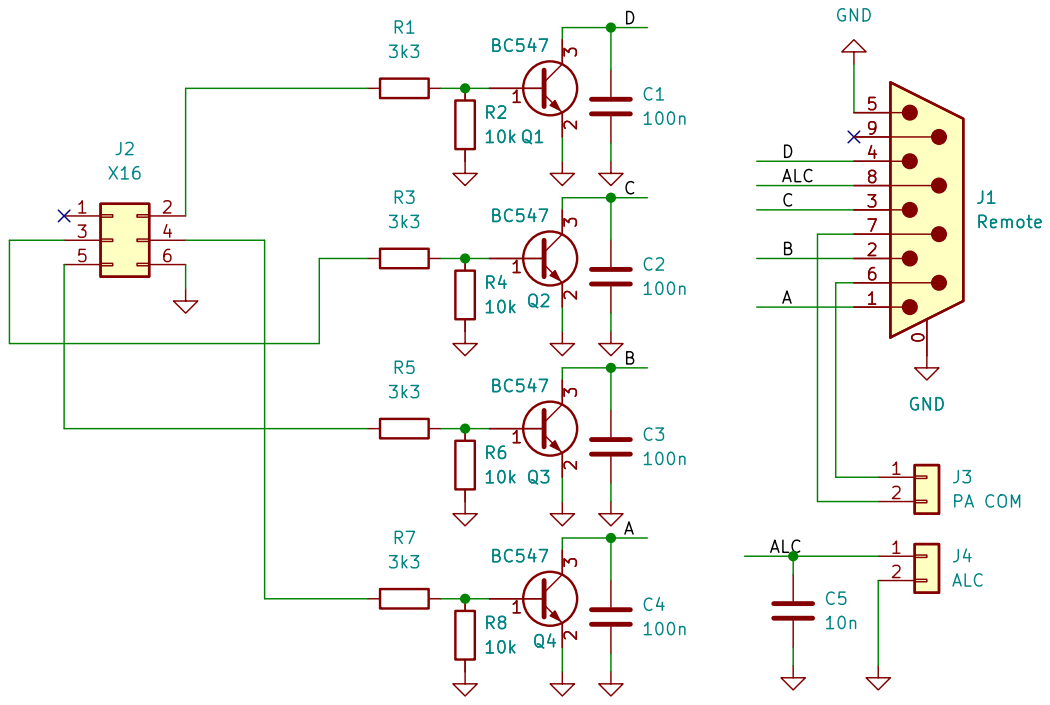
[picture p473: page 1]
