XGudron/UA3REO-DDC-Transceiver/Schematic/Wolf/Addons/AD8307_Add_on_v3/_Print/Mirrored.pdf

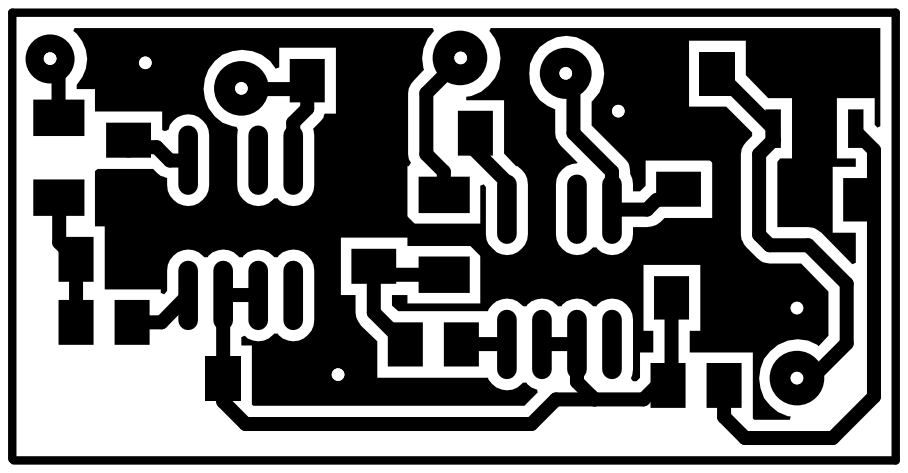
[picture p474: page 1]
