XGudron/UA3REO-DDC-Transceiver/Schematic/Wolf/Addons/PA_Control/PDF/remote-B_Cu.pdf

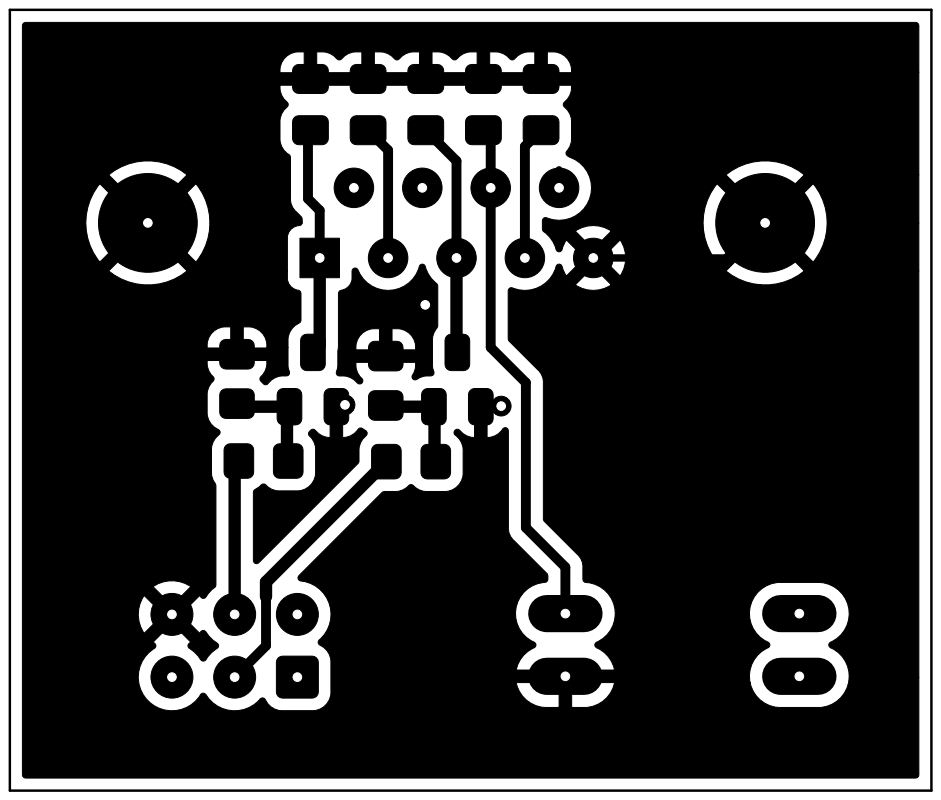
[picture p475: page 1]
