XGudron/UA3REO-DDC-Transceiver/Schematic/Wolf/Addons/PA_Control/PDF/remote-B_Silkscreen.pdf

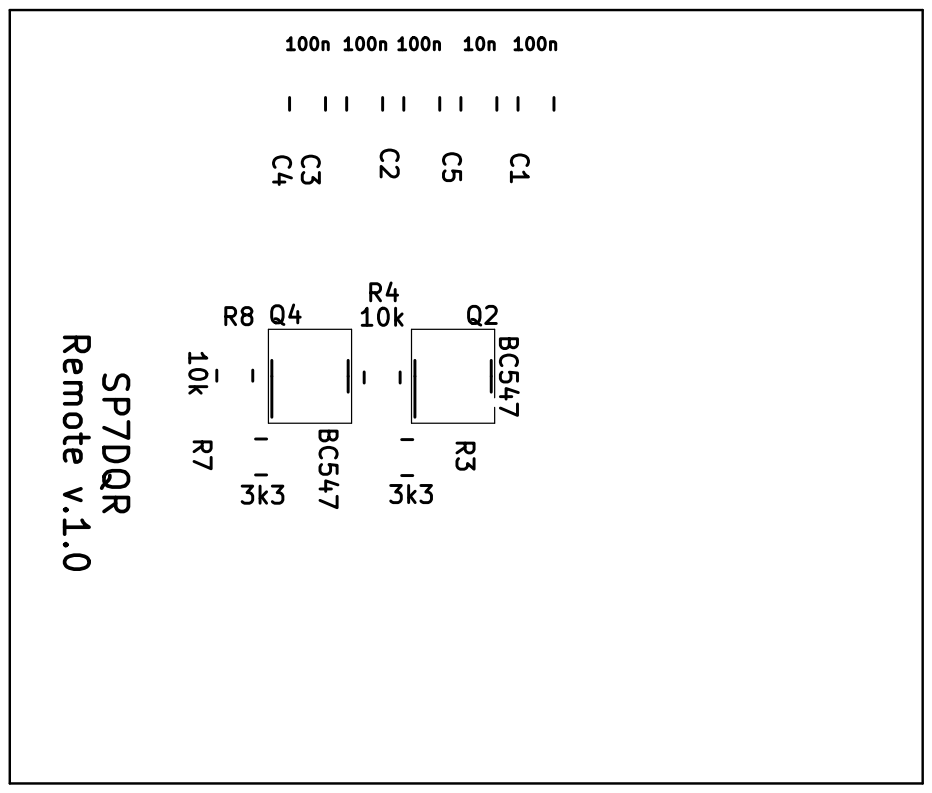
[picture p476: page 1]
