XGudron/UA3REO-DDC-Transceiver/Schematic/Wolf/Addons/PA_Control/PDF/remote-F_Cu.pdf

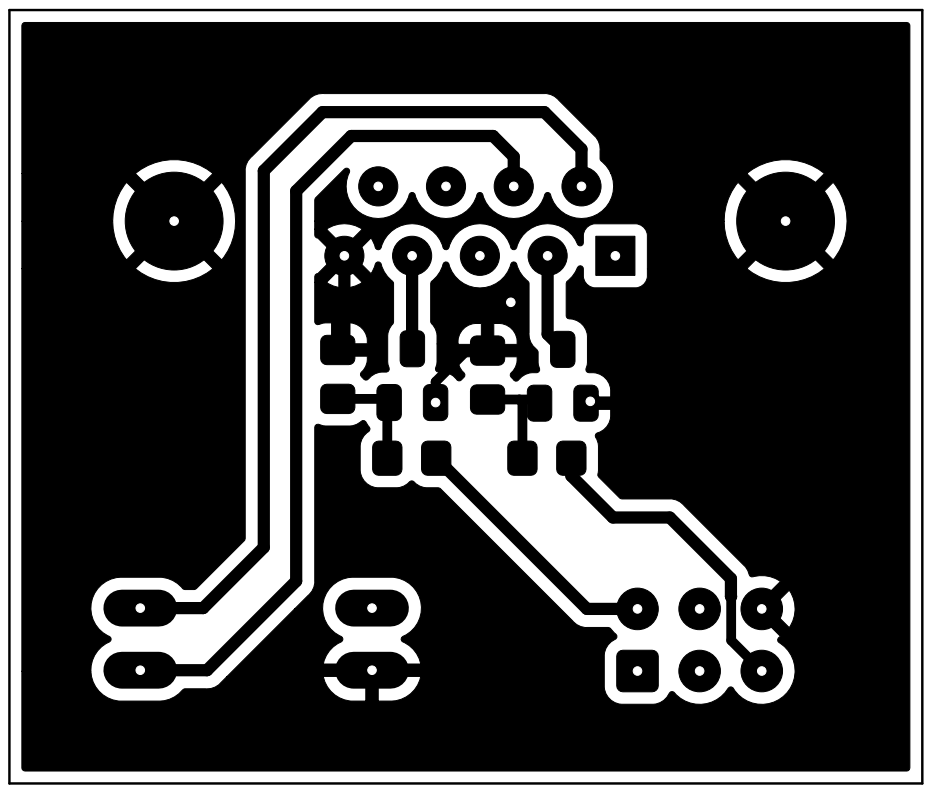
[picture p477: page 1]
