XGudron/UA3REO-DDC-Transceiver/Schematic/Wolf/Addons/PA_Control/PDF/remote-F_Silkscreen.pdf

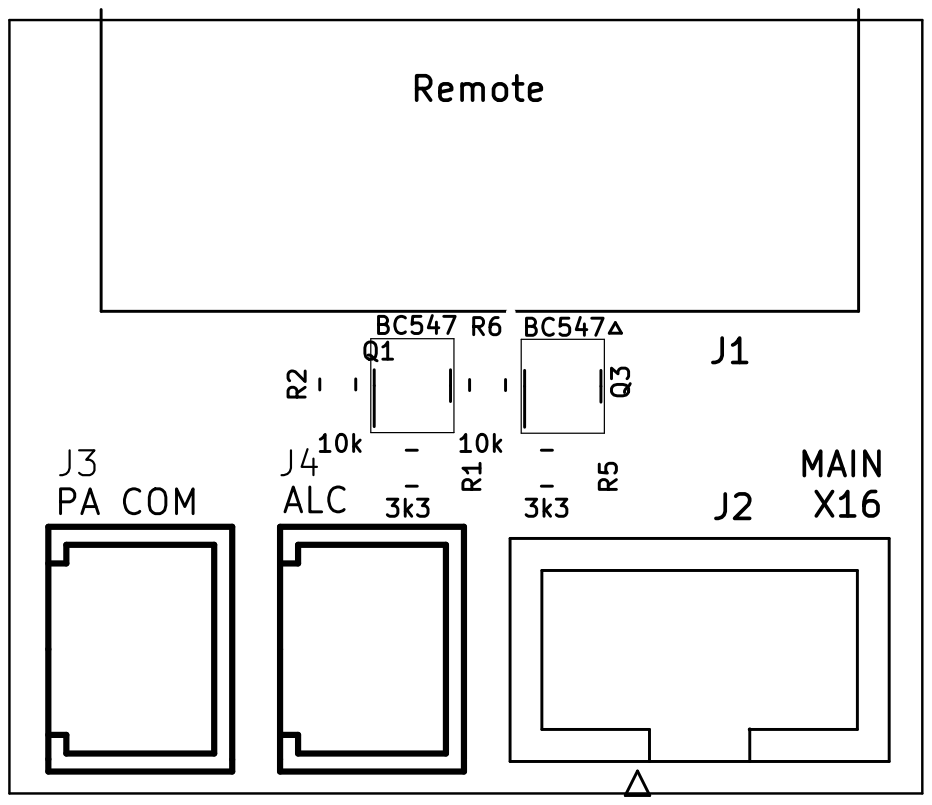
[picture p478: page 1]
