XGudron/UA3REO-DDC-Transceiver/Schematic/Wolf/Addons/TS4994_Add_on_v1/_Print/TS4994_Add_on_v1.pdf

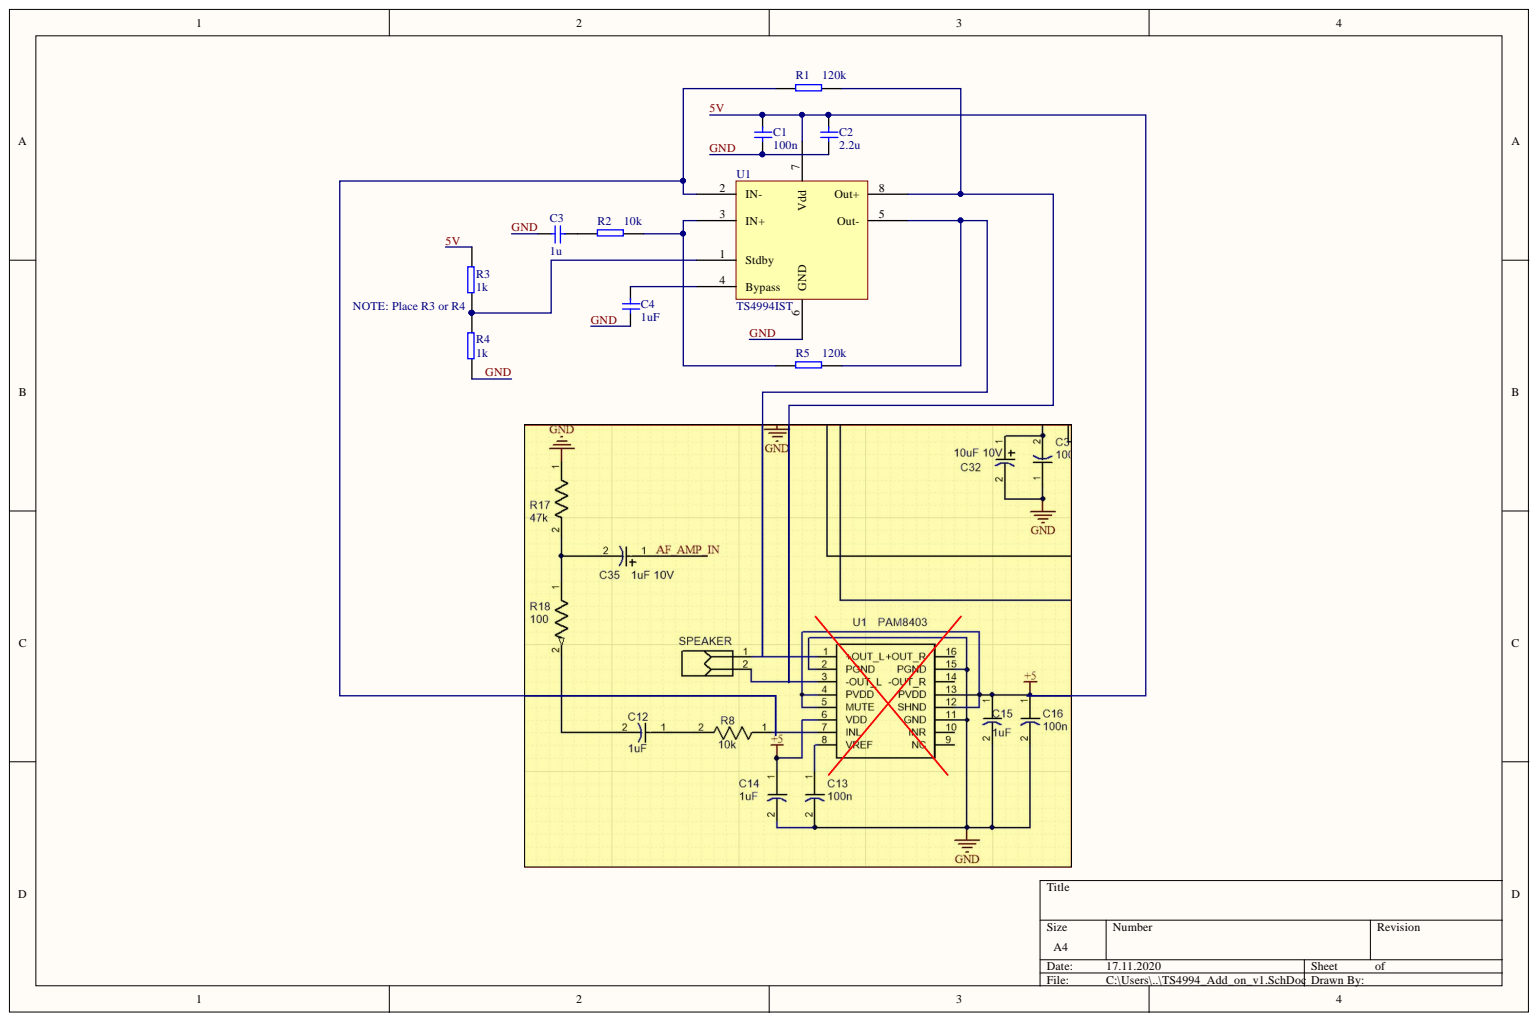
[picture p479: page 1]

Stdby 1

Bypass 4
