XGudron/UA3REO-DDC-Transceiver/Schematic/Wolf/Scheme/SCHEMATIC-FONT-UNIT-WOLF-1-5D-v1.pdf

C:\Users\RET\Desktop\FRONT-UNIT-5.SCHDOC
